prpplague/witch_dev/documentation/WITCH-schematics/jpgs/Primary Sequence - 47594.jpg

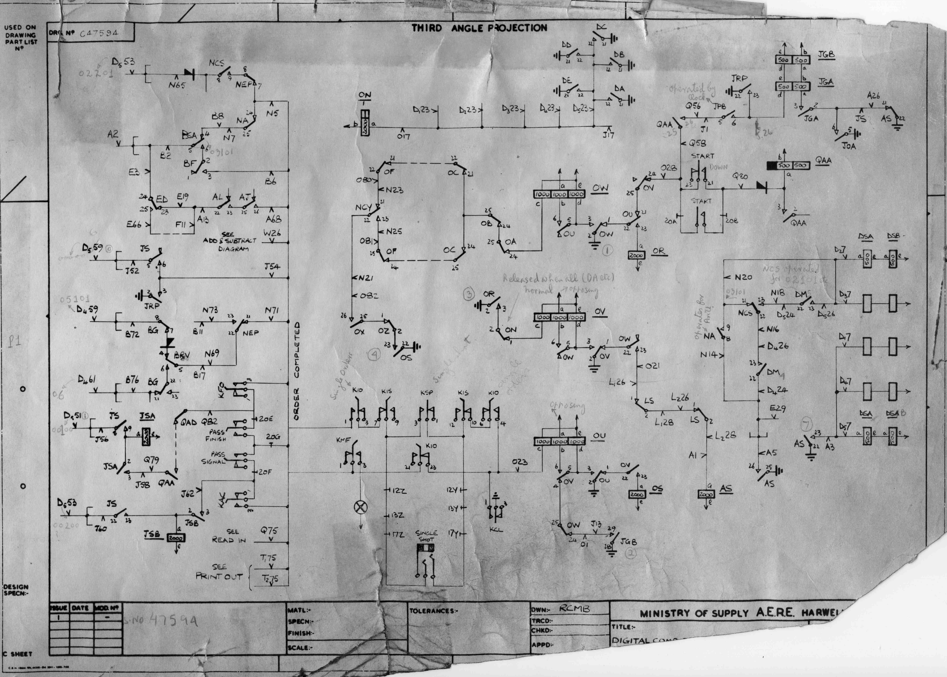
documentation/WITCH-schematics/jpgs/Primary Sequence - 47594.jpg
