prpplague/witch_dev/documentation/images/HarwellDekatronComputer-535x420.jpg

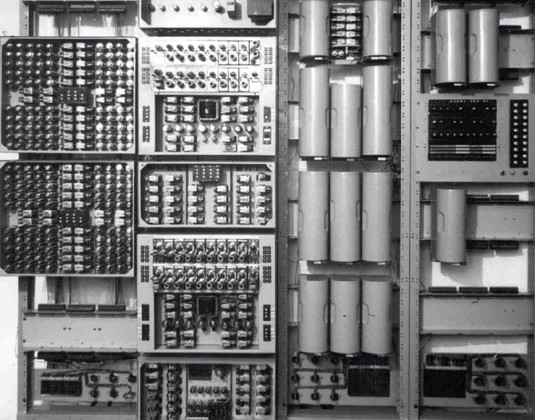
documentation/images/HarwellDekatronComputer-535x420.jpg
