prpplague/witch_dev/documentation/WITCH-schematics/notes/Multiplication Control Notes - 47584.pdf

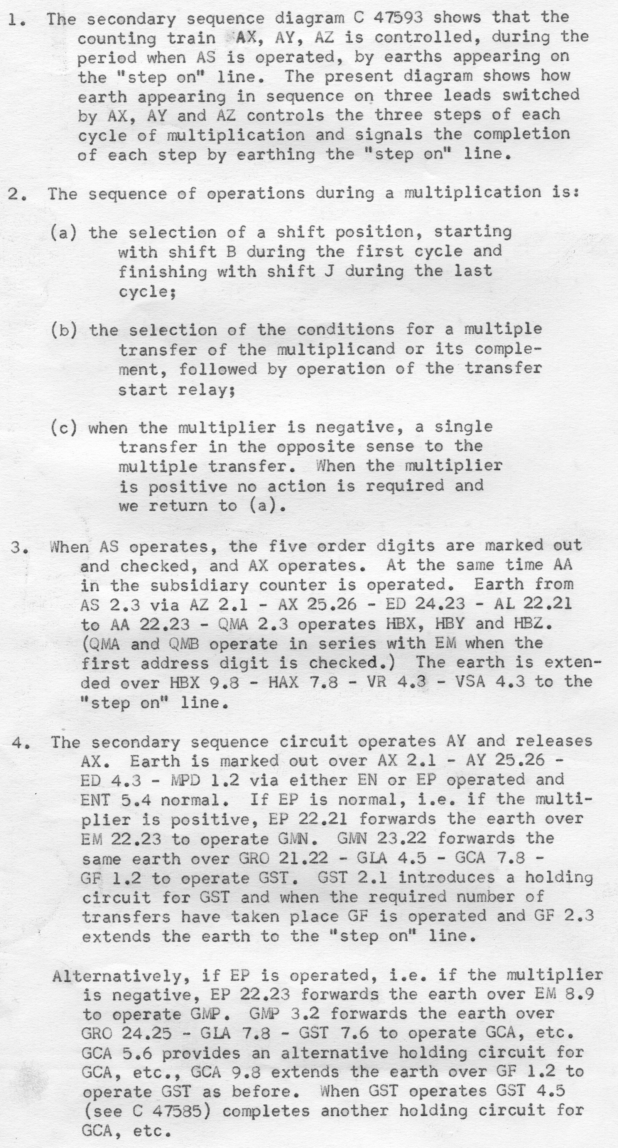
[picture p31: figure]

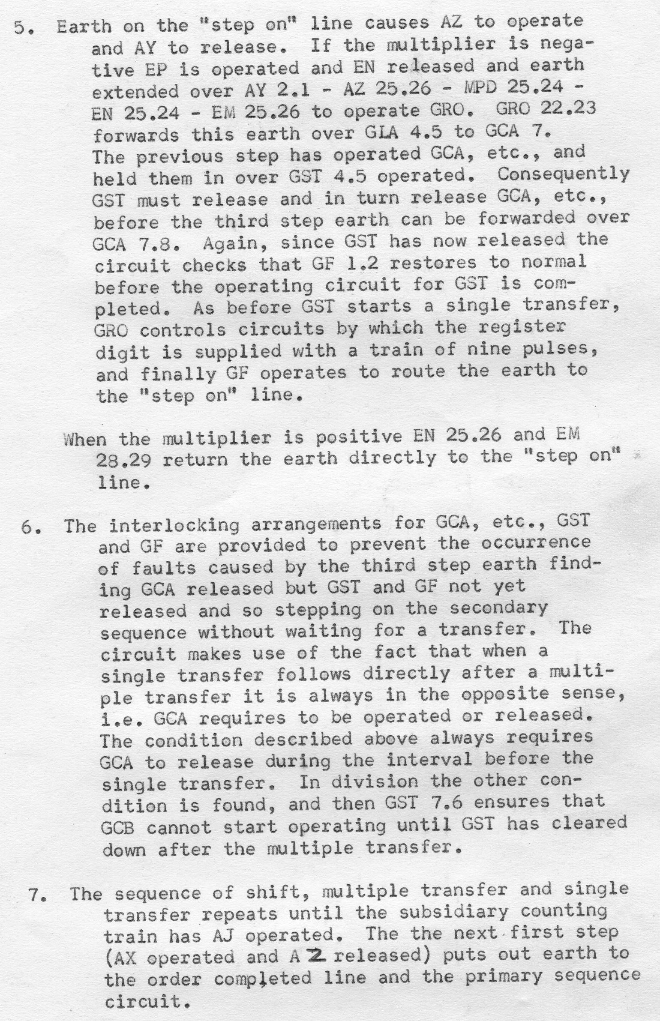
[picture p32: figure]
