prpplague/witch_dev/documentation/WITCH-schematics/notes/Read In Control Notes - 47582.pdf

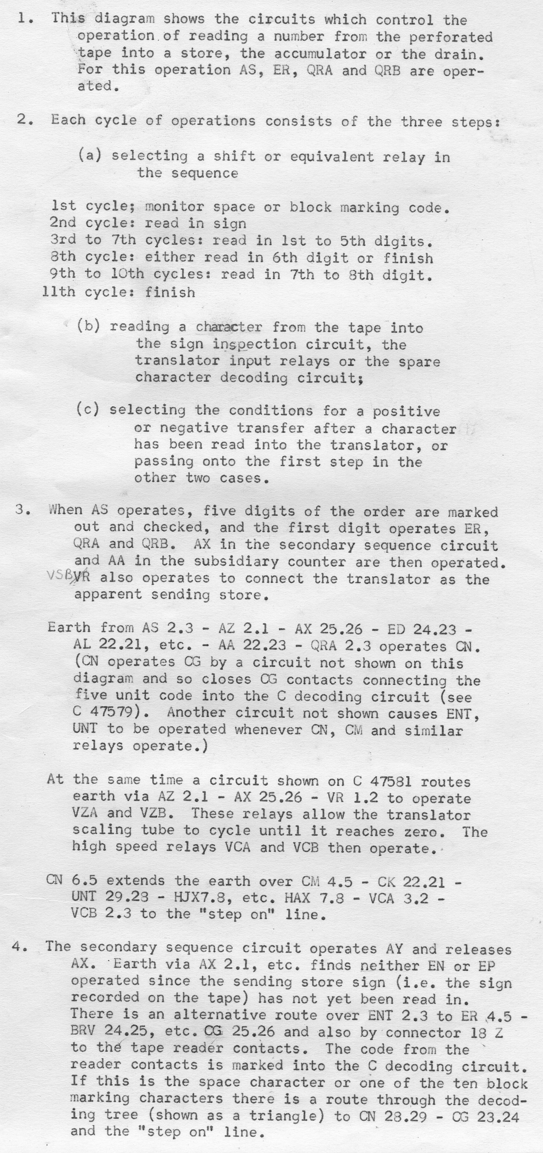
[picture p33: figure]

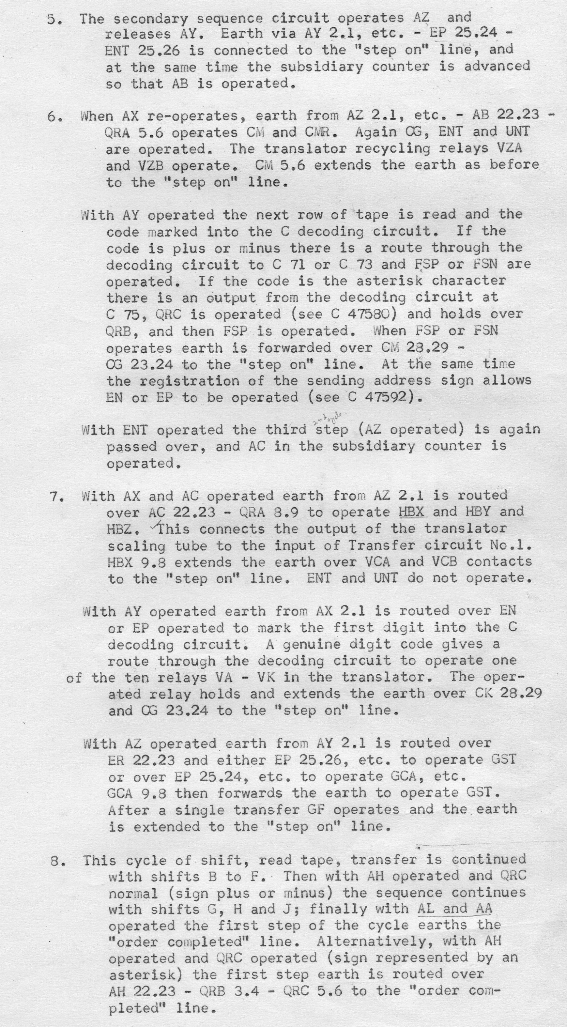
[picture p34: figure]
