prpplague/witch_dev/documentation/WITCH-schematics/notes/Secondary Sequence Notes - 47593.pdf

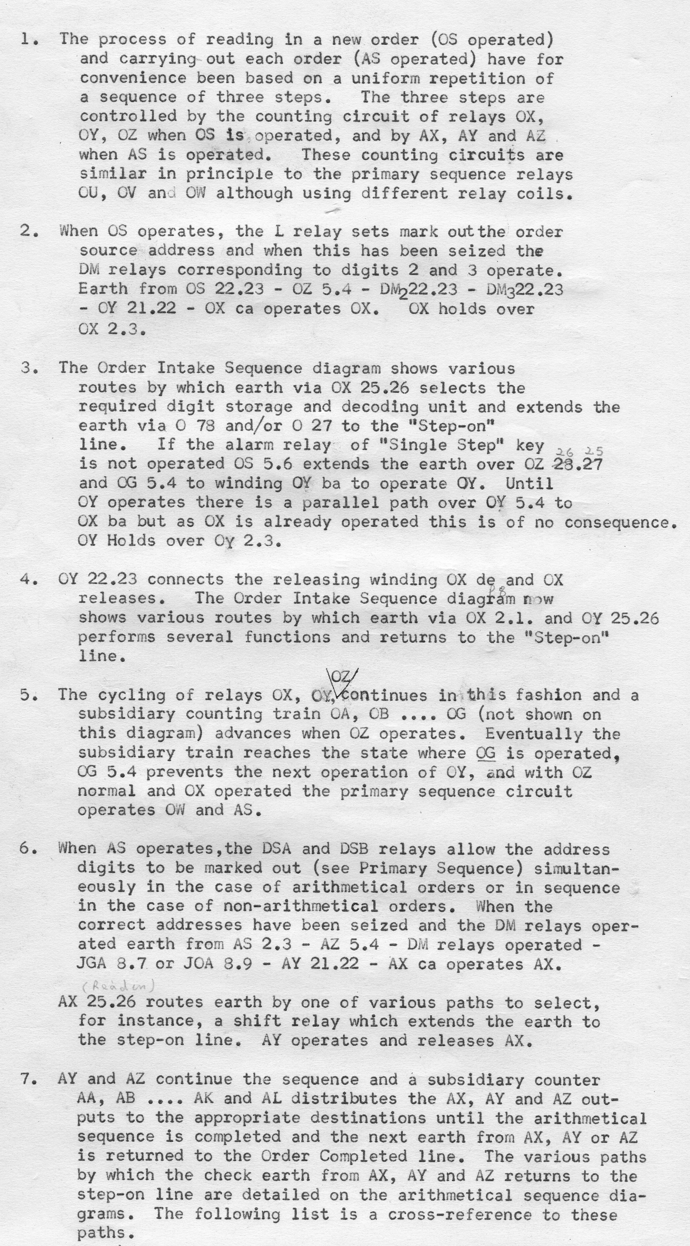
[picture p35: figure]

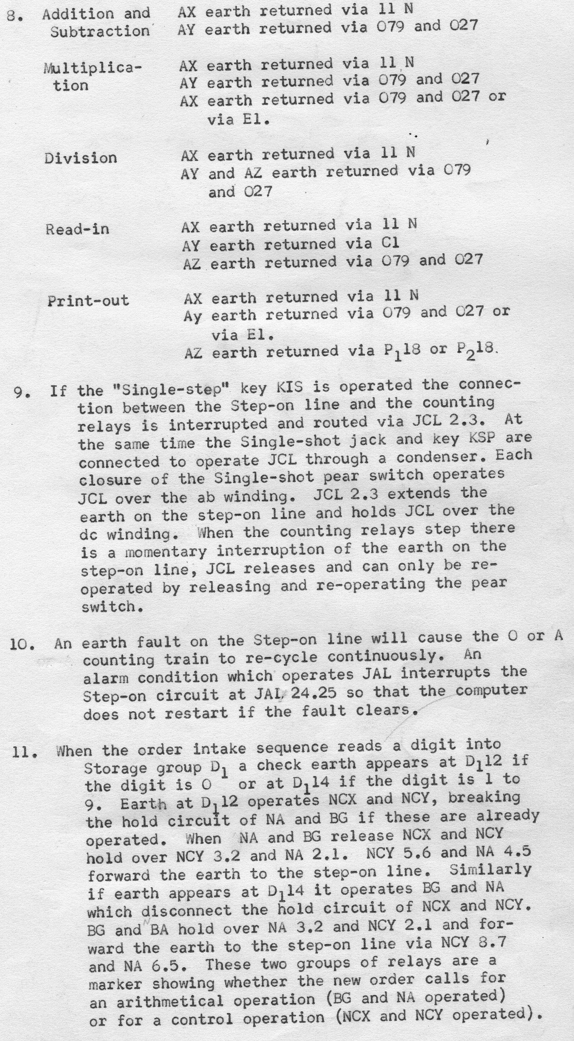
[picture p36: figure]

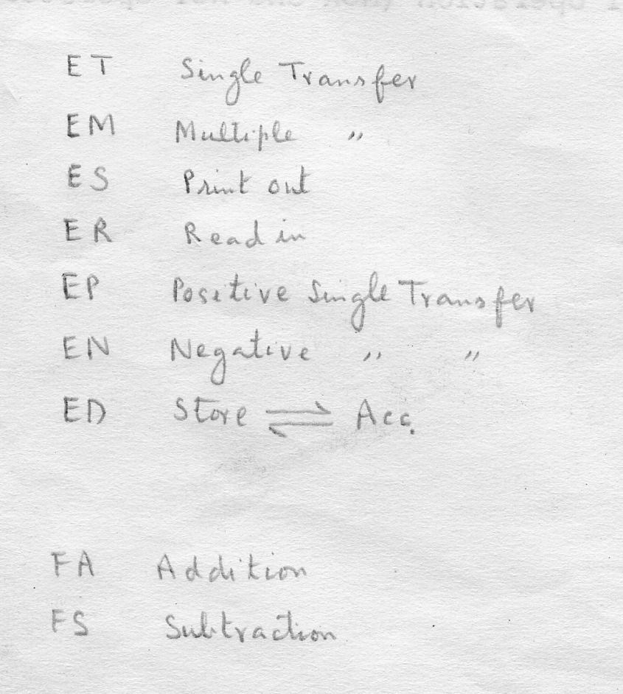
[picture p37: figure]
