prpplague/witch_dev/documentation/WITCH-schematics/notes/Sign Inspection Circuit Notes - 47580.pdf

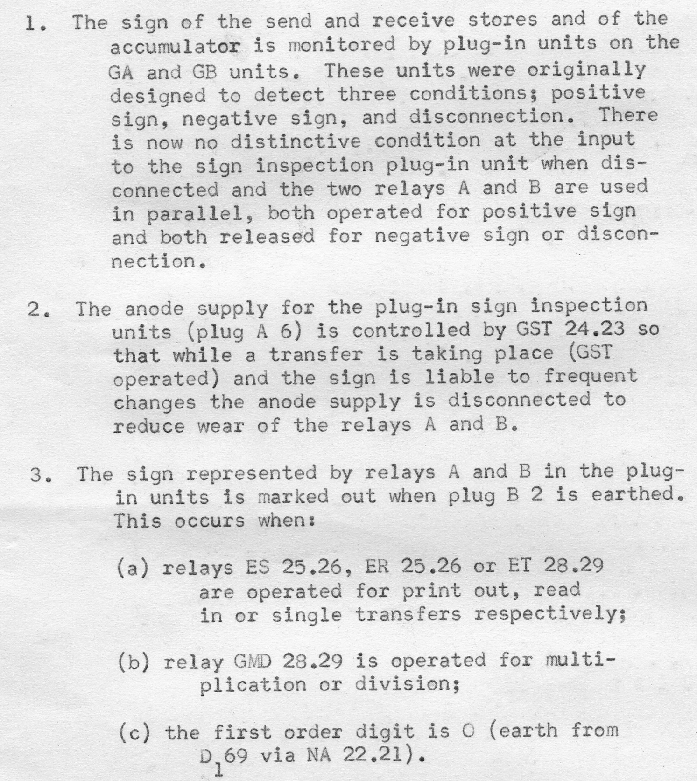
[picture p38: figure]

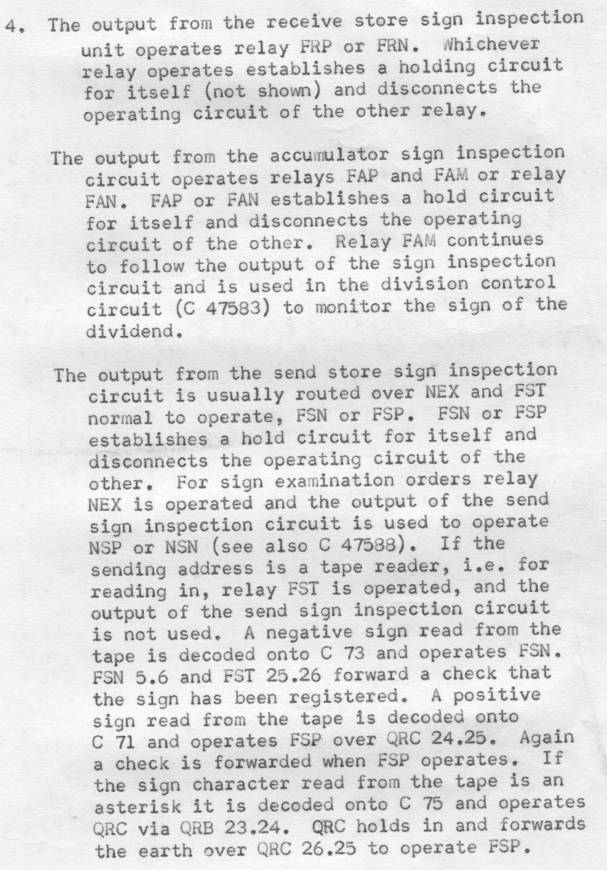
[picture p39: figure]
