prpplague/witch_dev/block-designs/witch-phase1/dekatron/witch-dekatron1.png

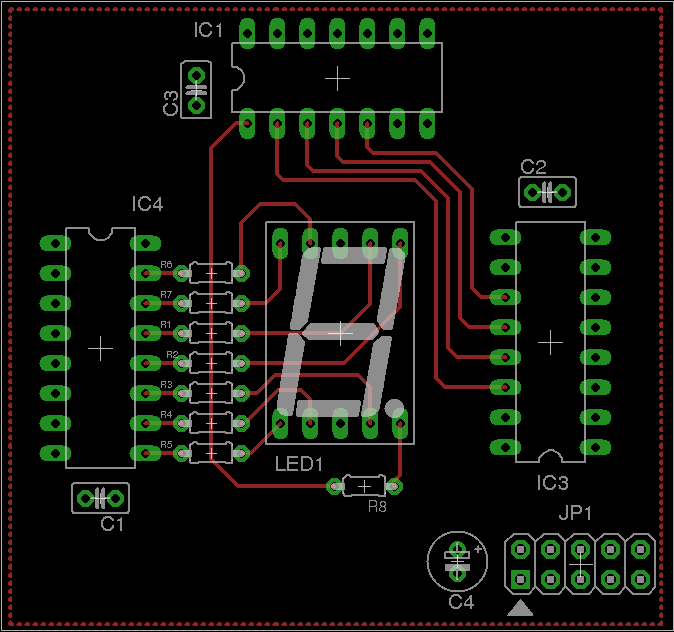
block-designs/witch-phase1/dekatron/witch-dekatron1.png
