prpplague/witch_dev/block-designs/witch-phase1/pulse/witch-pulse1.png

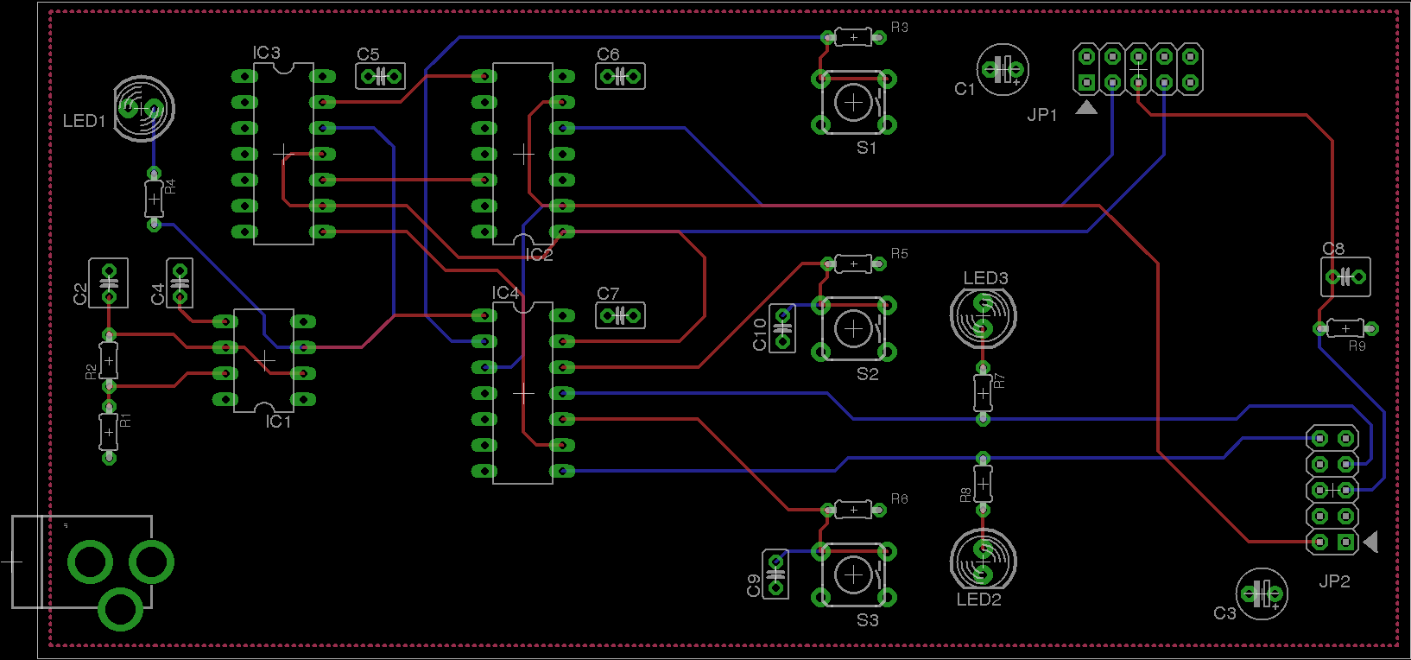
block-designs/witch-phase1/pulse/witch-pulse1.png
