prpplague/witch_dev/block-designs/witch-phase1/transfer/witch-transfer1.png

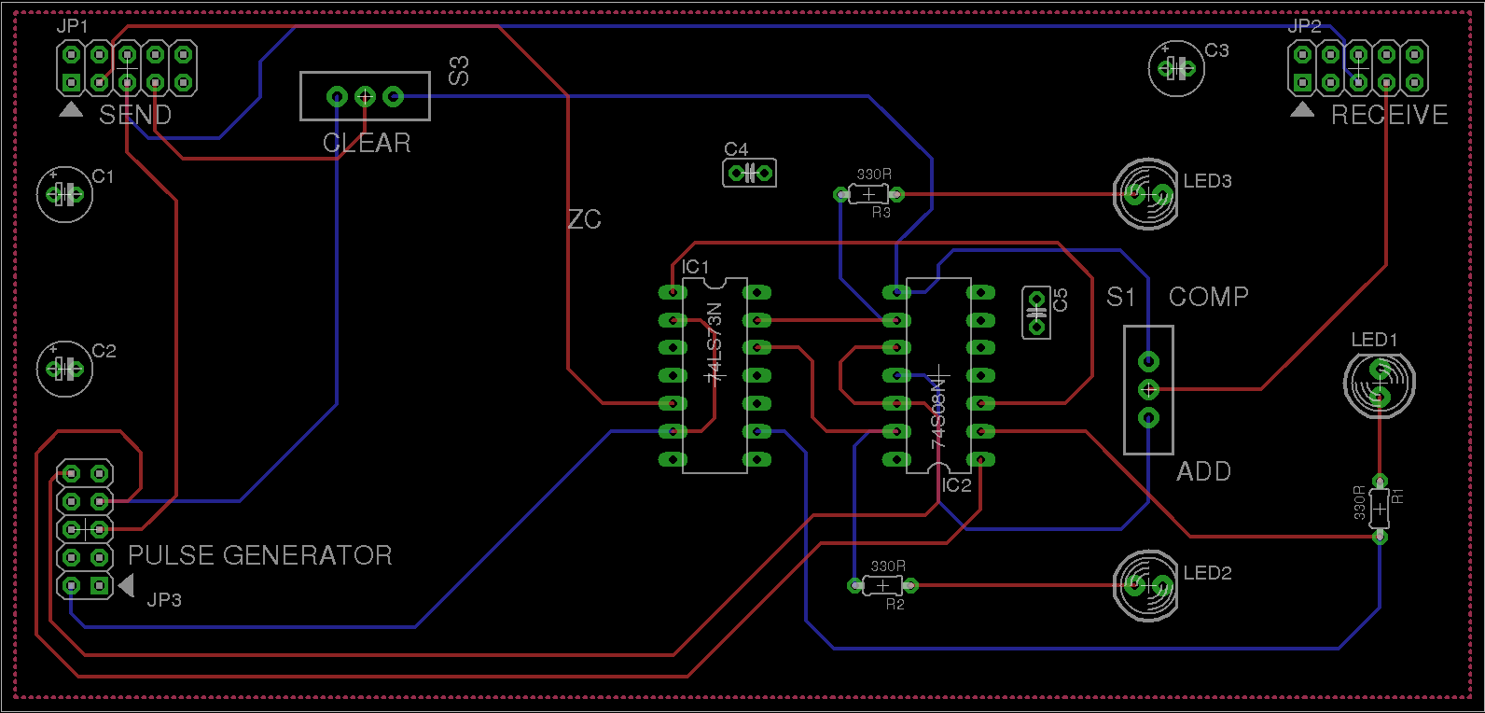
block-designs/witch-phase1/transfer/witch-transfer1.png
