prpplague/witch_dev/block-designs/witch-phase2/carry-block/carry-block.png

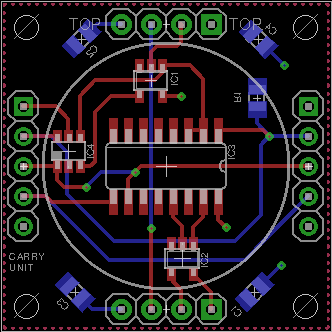
block-designs/witch-phase2/carry-block/carry-block.png
