prpplague/witch_dev/block-designs/witch-phase2/carry-select/carry-select.png

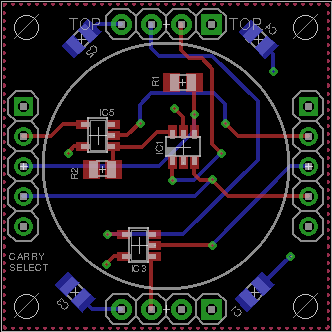
block-designs/witch-phase2/carry-select/carry-select.png
