prpplague/witch_dev/block-designs/witch-phase2/dekatron-sim/dekatron-sim-4017-A3/dekatron-sim-4017-a3.png

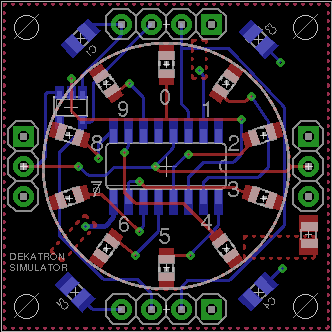
block-designs/witch-phase2/dekatron-sim/dekatron-sim-4017-A3/dekatron-sim-4017-a3.png
