prpplague/witch_dev/block-designs/witch-phase2/store-column-block/store-column-block.png

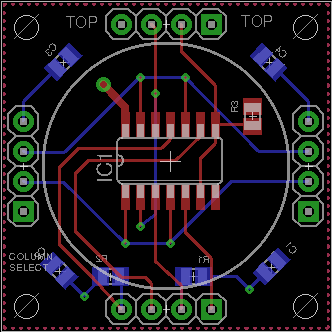
block-designs/witch-phase2/store-column-block/store-column-block.png
