prpplague/witch_dev/block-designs/witch-phase2/store-ctrl-block/store-ctrl-block.png

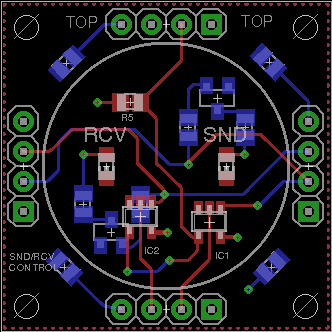
block-designs/witch-phase2/store-ctrl-block/store-ctrl-block.png
