prpplague/witch_dev/block-designs/witch-phase2/transfer-block/transfer-block.png

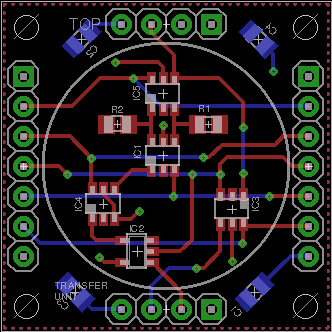
block-designs/witch-phase2/transfer-block/transfer-block.png
