prpplague/witch_dev/block-designs/witch-phase3/relay-set-d-decode/relay-set-d-decode.png

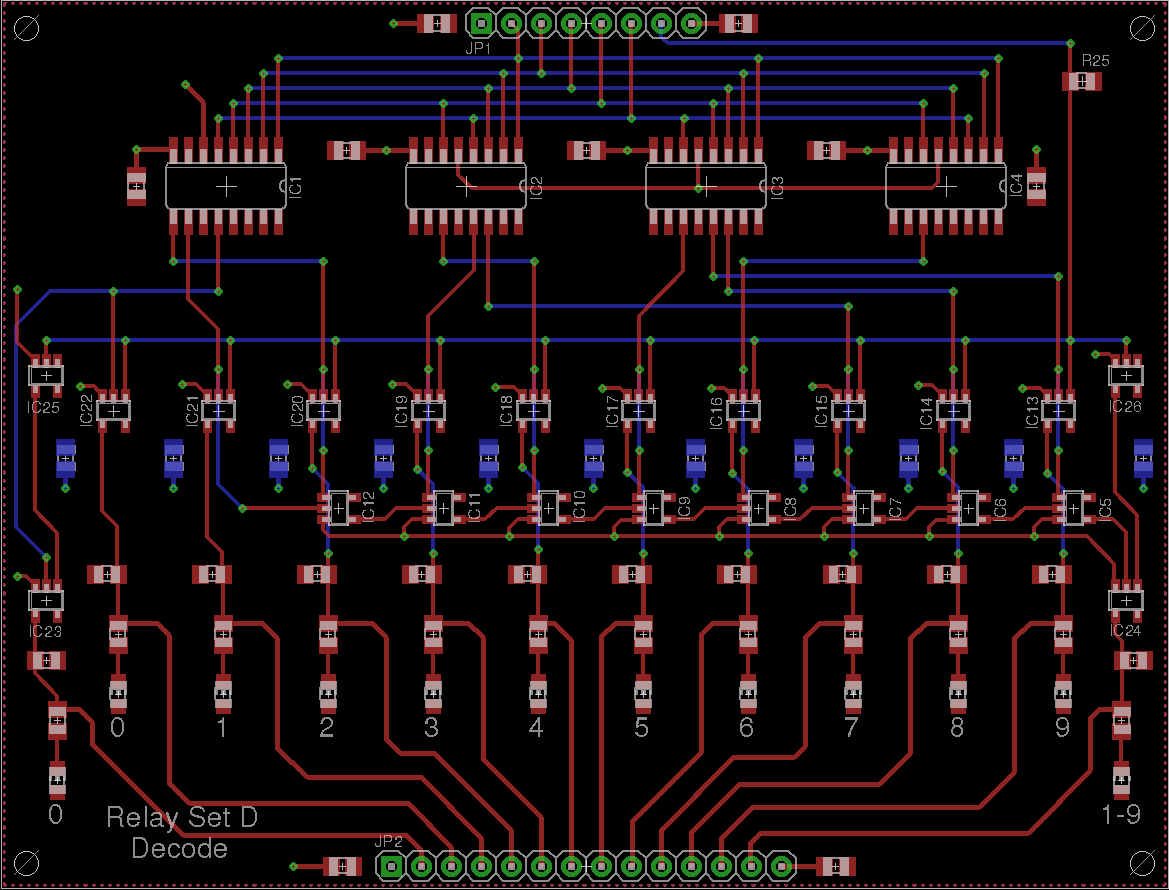
block-designs/witch-phase3/relay-set-d-decode/relay-set-d-decode.png
