prpplague/witch_dev/block-designs/witch-phase3/relay-set-d-latch/relay-set-d-latch.png

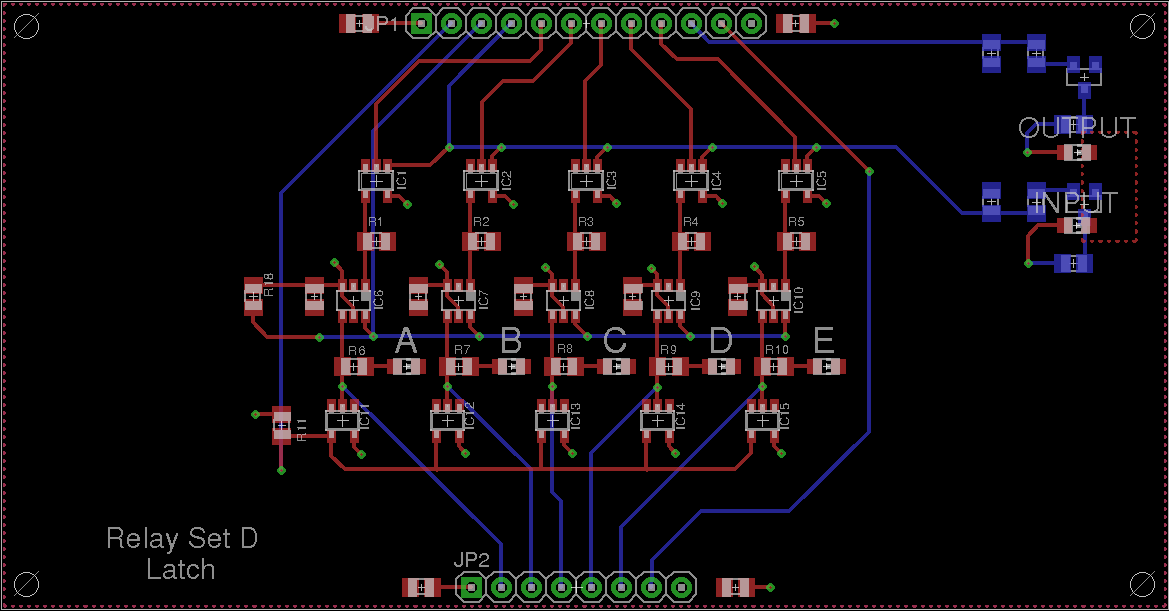
block-designs/witch-phase3/relay-set-d-latch/relay-set-d-latch.png
