prpplague/witch_dev/block-designs/witch-phase4/tape-reader/dot-reader/dot-sensors.png

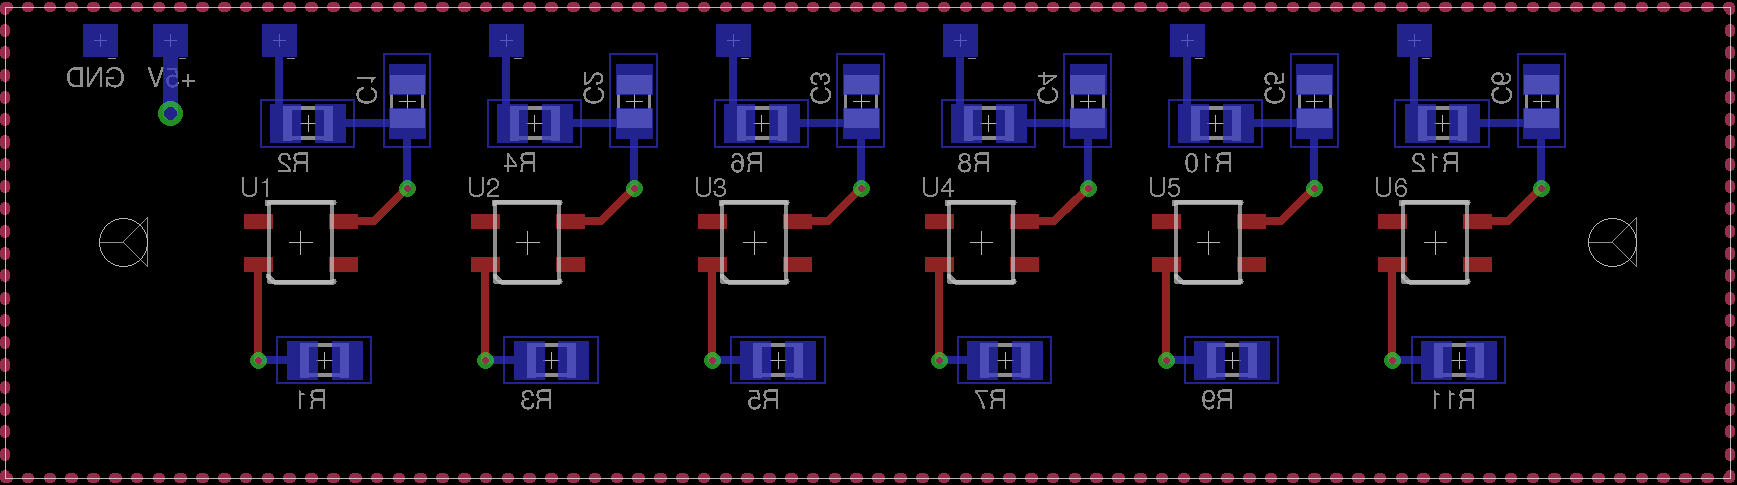
block-designs/witch-phase4/tape-reader/dot-reader/dot-sensors.png
