prpplague/witch_dev/documentation/datasheets/6AL5.jpg

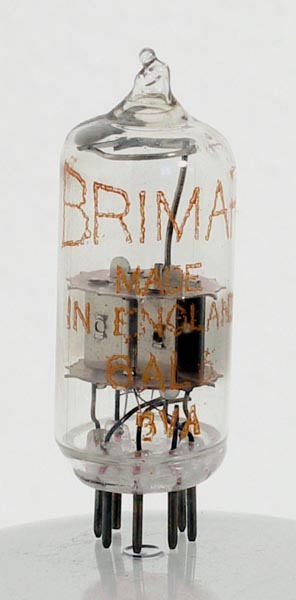
documentation/datasheets/6AL5.jpg
