prpplague/witch_dev/documentation/datasheets/6AM5.jpg

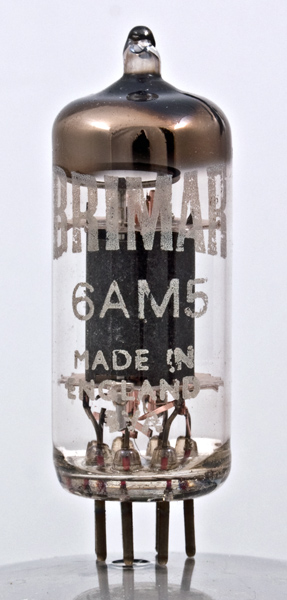
documentation/datasheets/6AM5.jpg
