prpplague/witch_dev/documentation/datasheets/6J6.jpg

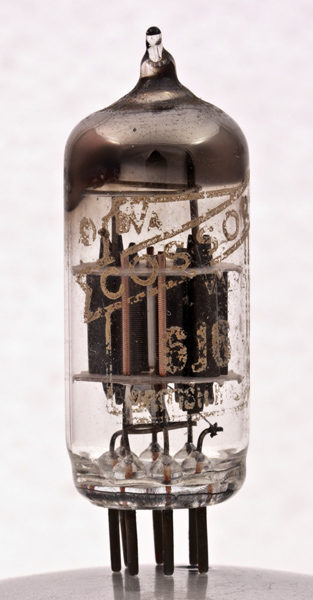
documentation/datasheets/6J6.jpg
