prpplague/witch_dev/documentation/datasheets/8D3.jpg

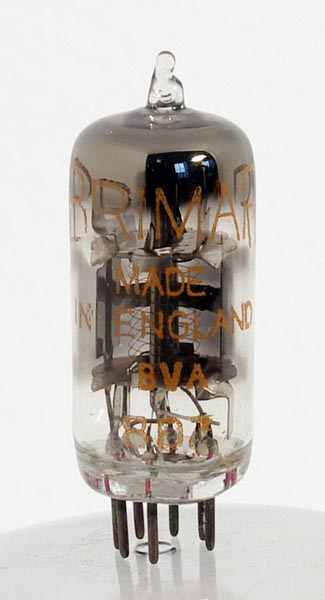
documentation/datasheets/8D3.jpg
