prpplague/witch_dev/documentation/datasheets/12AT7.jpg

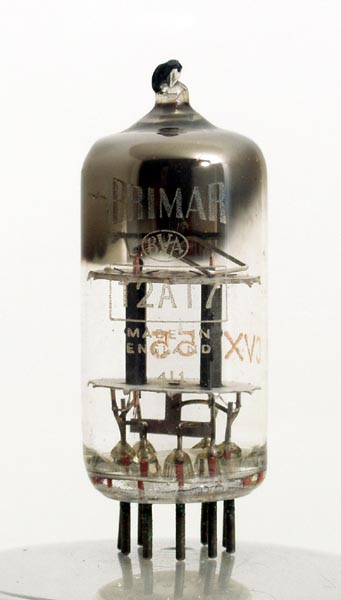
documentation/datasheets/12AT7.jpg
