prpplague/witch_dev/documentation/datasheets/85A2.jpg

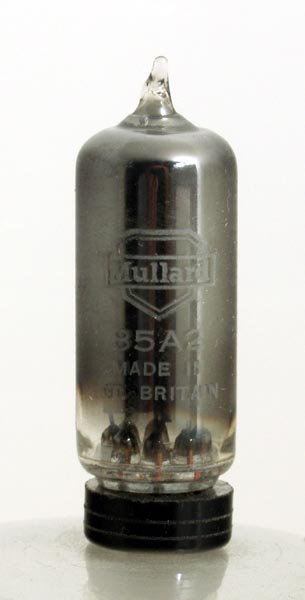
documentation/datasheets/85A2.jpg
