prpplague/witch_dev/documentation/datasheets/E90CC.jpg

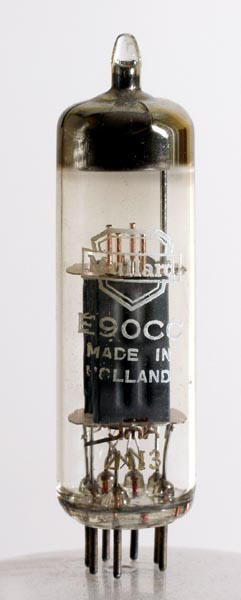
documentation/datasheets/E90CC.jpg
