prpplague/witch_dev/documentation/datasheets/E92CC.jpg

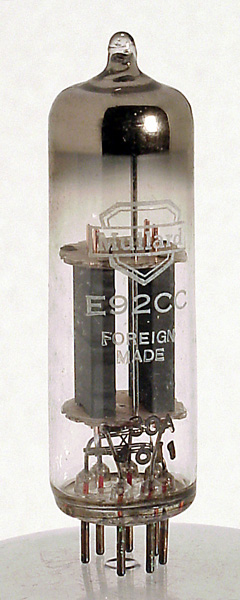
documentation/datasheets/E92CC.jpg
