prpplague/witch_dev/documentation/datasheets/EB91.jpg

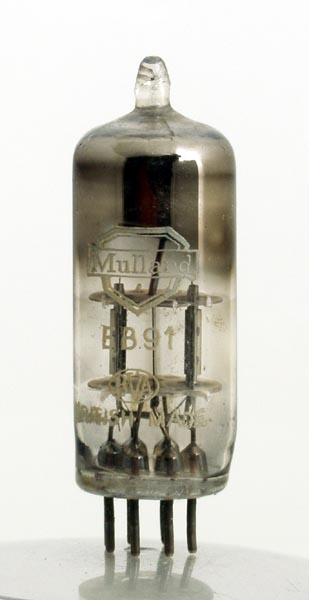
documentation/datasheets/EB91.jpg
