prpplague/witch_dev/documentation/datasheets/ECC81.jpg

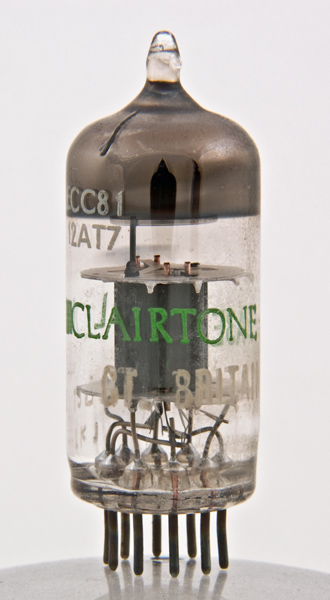
documentation/datasheets/ECC81.jpg
