prpplague/witch_dev/documentation/datasheets/EL33.jpg

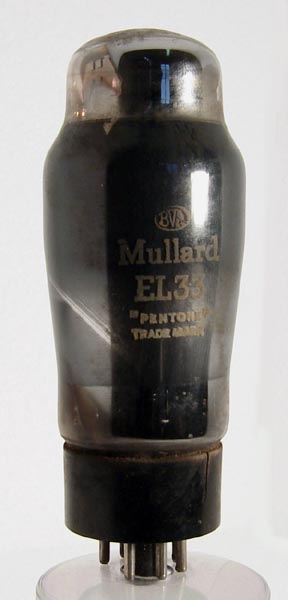
documentation/datasheets/EL33.jpg
