prpplague/witch_dev/documentation/datasheets/EL360.jpg

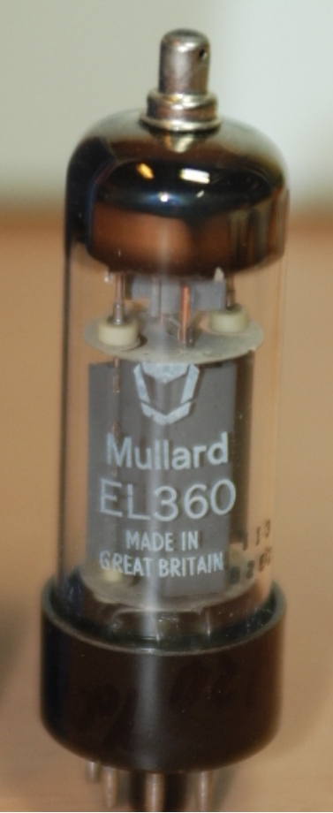
documentation/datasheets/EL360.jpg
