prpplague/witch_dev/documentation/datasheets/G1-371K.jpg

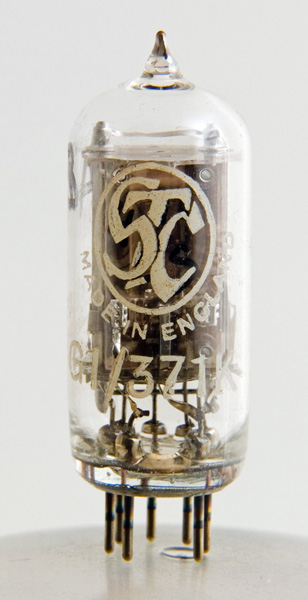
documentation/datasheets/G1-371K.jpg
