prpplague/witch_dev/documentation/datasheets/GC10A.jpg

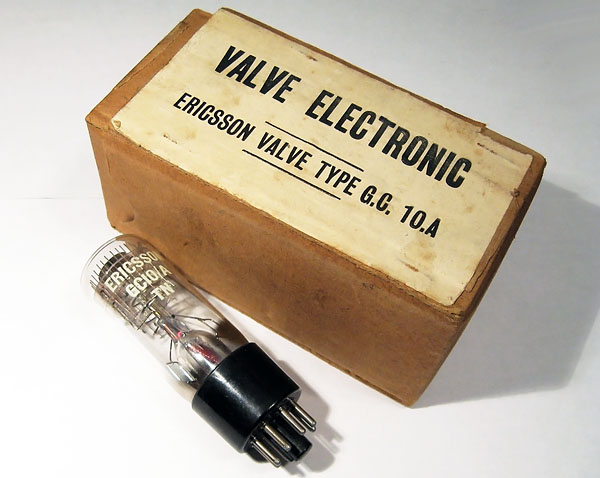
documentation/datasheets/GC10A.jpg
