prpplague/witch_dev/documentation/datasheets/GC10B.jpg

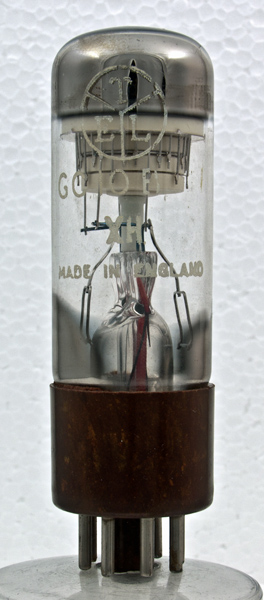
documentation/datasheets/GC10B.jpg
