prpplague/witch_dev/documentation/datasheets/GS10C.jpg

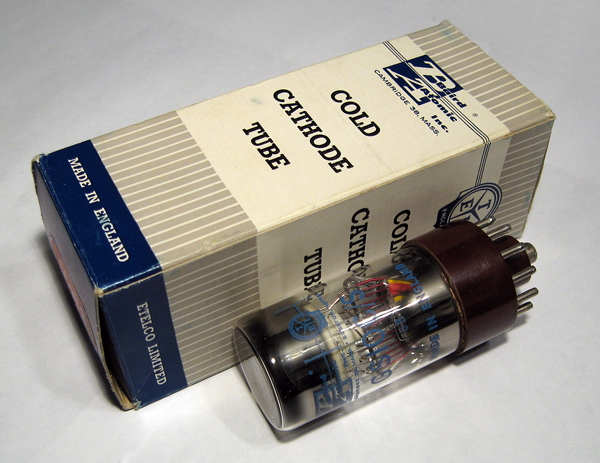
documentation/datasheets/GS10C.jpg
