prpplague/witch_dev/documentation/datasheets/GTE175M.jpg

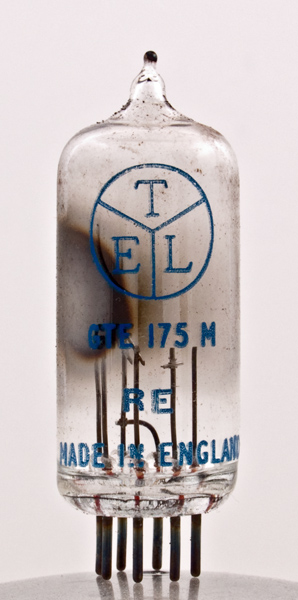
documentation/datasheets/GTE175M.jpg
