prpplague/witch_dev/documentation/datasheets/P-308-AB.jpg

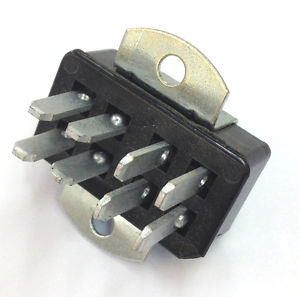
documentation/datasheets/P-308-AB.jpg
