prpplague/witch_dev/documentation/datasheets/S-308-AB.jpg

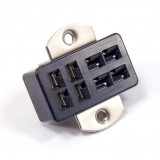
documentation/datasheets/S-308-AB.jpg
