prpplague/witch_dev/documentation/datasheets/VR150_30.jpg

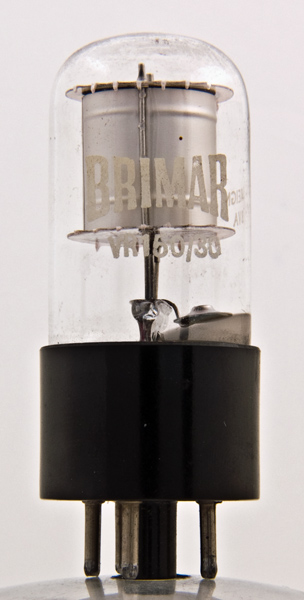
documentation/datasheets/VR150_30.jpg
