prpplague/witch_dev/documentation/dekatron-spinner/Variable Dekatron Spinner Kit | Threeneuron's Pile o'Poo_files/shock_03s.jpg

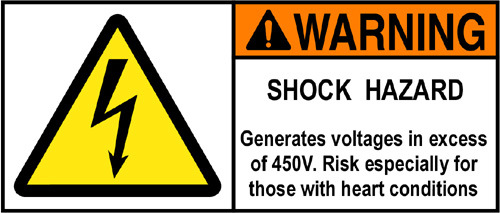
documentation/dekatron-spinner/Variable Dekatron Spinner Kit | Threeneuron's Pile o'Poo_files/shock_03s.jpg
