prpplague/witch_dev/documentation/dekatron-spinner/Variable Dekatron Spinner Kit | Threeneuron's Pile o'Poo_files/sp393_14.jpg

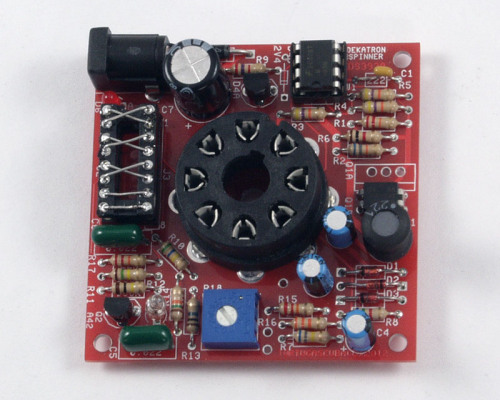
documentation/dekatron-spinner/Variable Dekatron Spinner Kit | Threeneuron's Pile o'Poo_files/sp393_14.jpg
