prpplague/witch_dev/documentation/images/caption-1.jpg

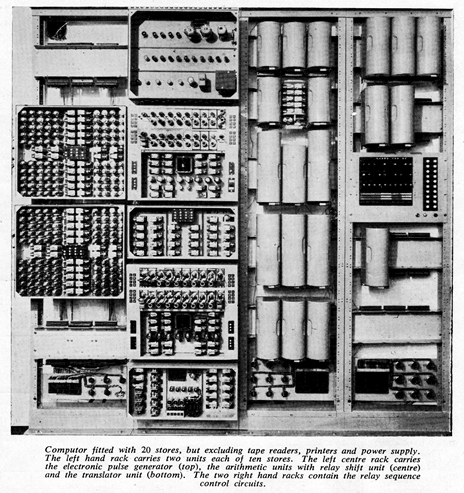
documentation/images/caption-1.jpg
