prpplague/witch_dev/documentation/images/EE-2.jpg

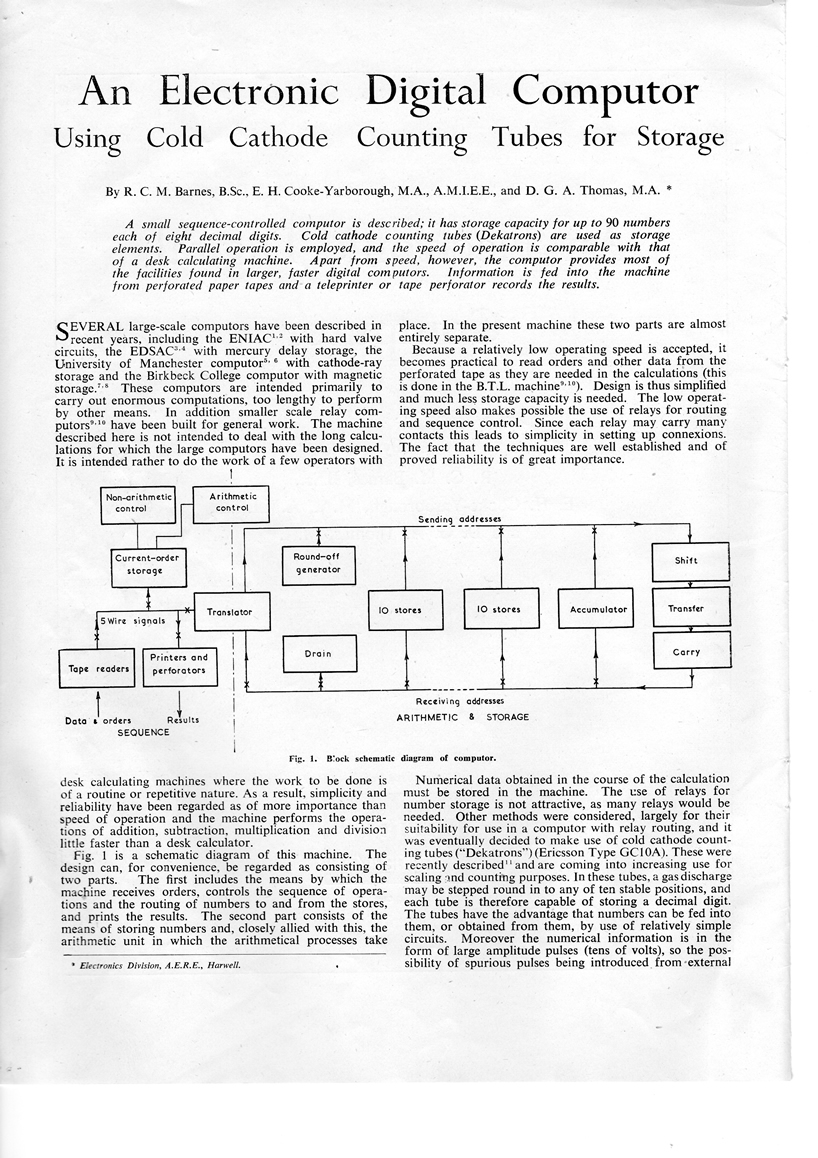
documentation/images/EE-2.jpg
