prpplague/witch_dev/documentation/images/EE-4.jpg

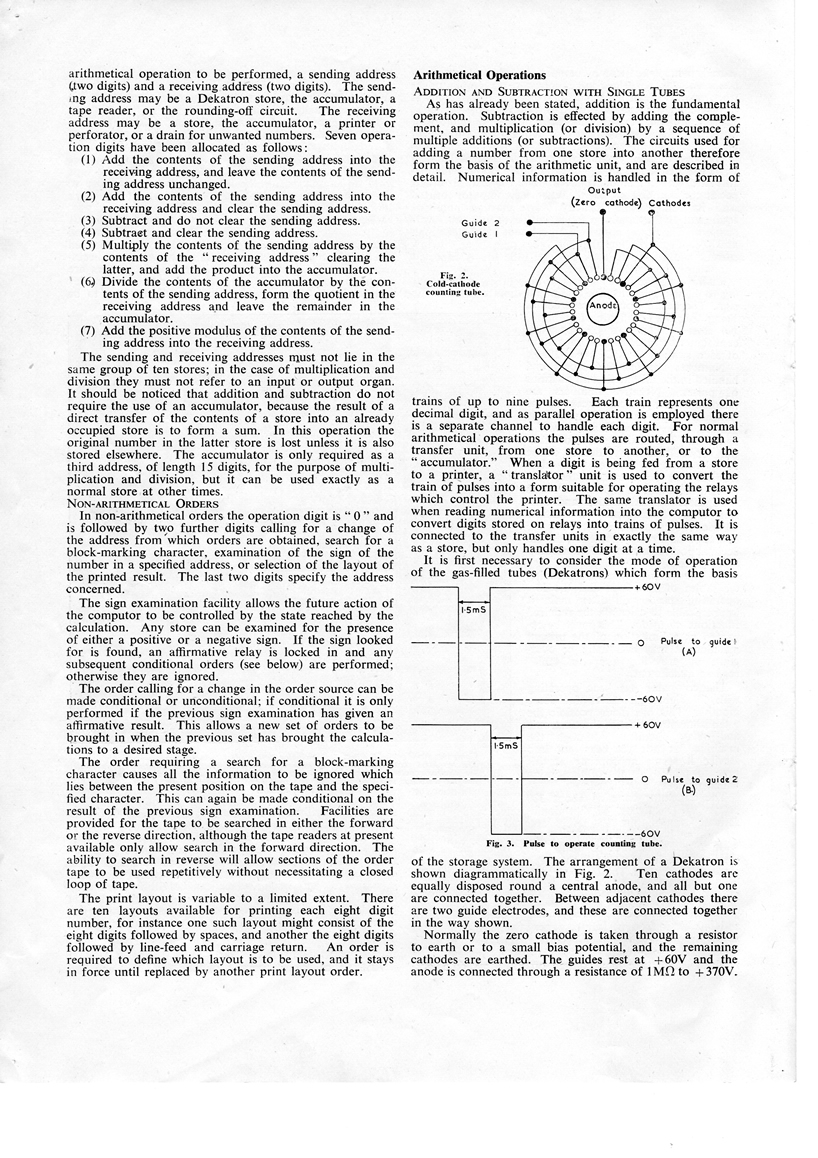
documentation/images/EE-4.jpg
