prpplague/witch_dev/documentation/images/EE-5.jpg

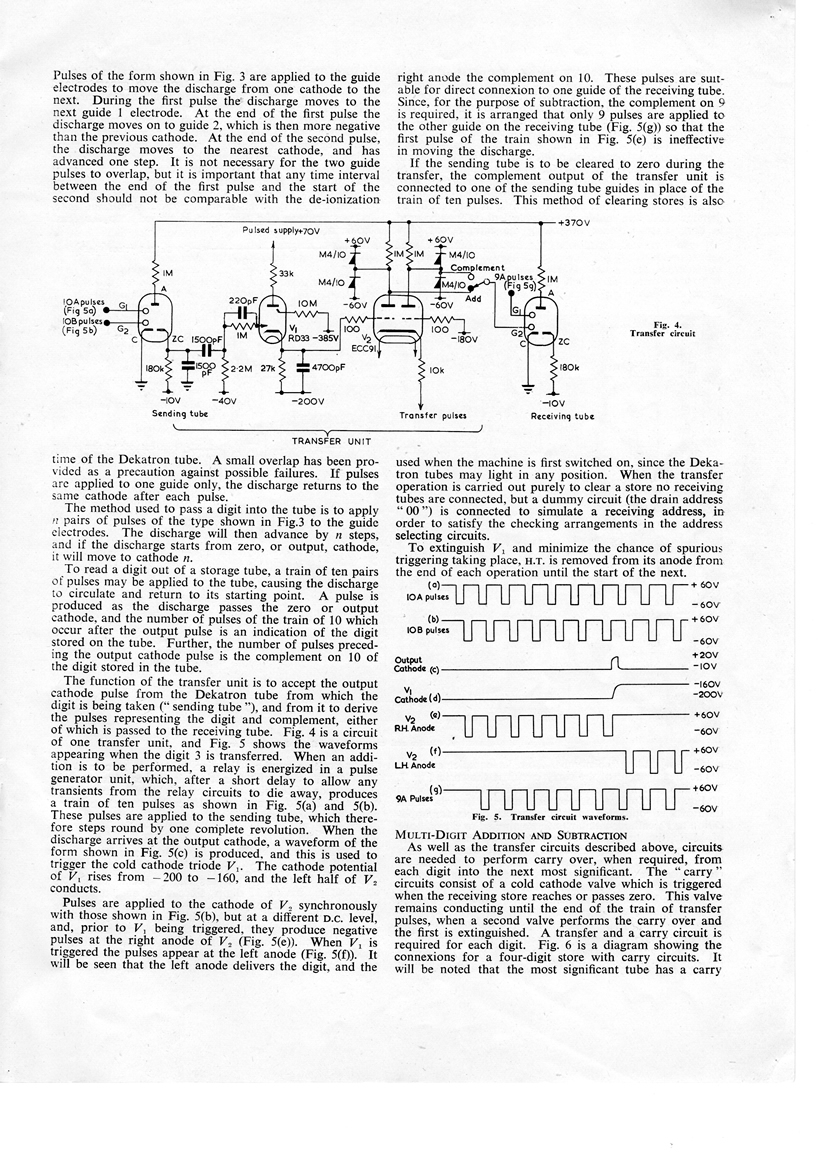
documentation/images/EE-5.jpg
