prpplague/witch_dev/documentation/images/EE-6.jpg

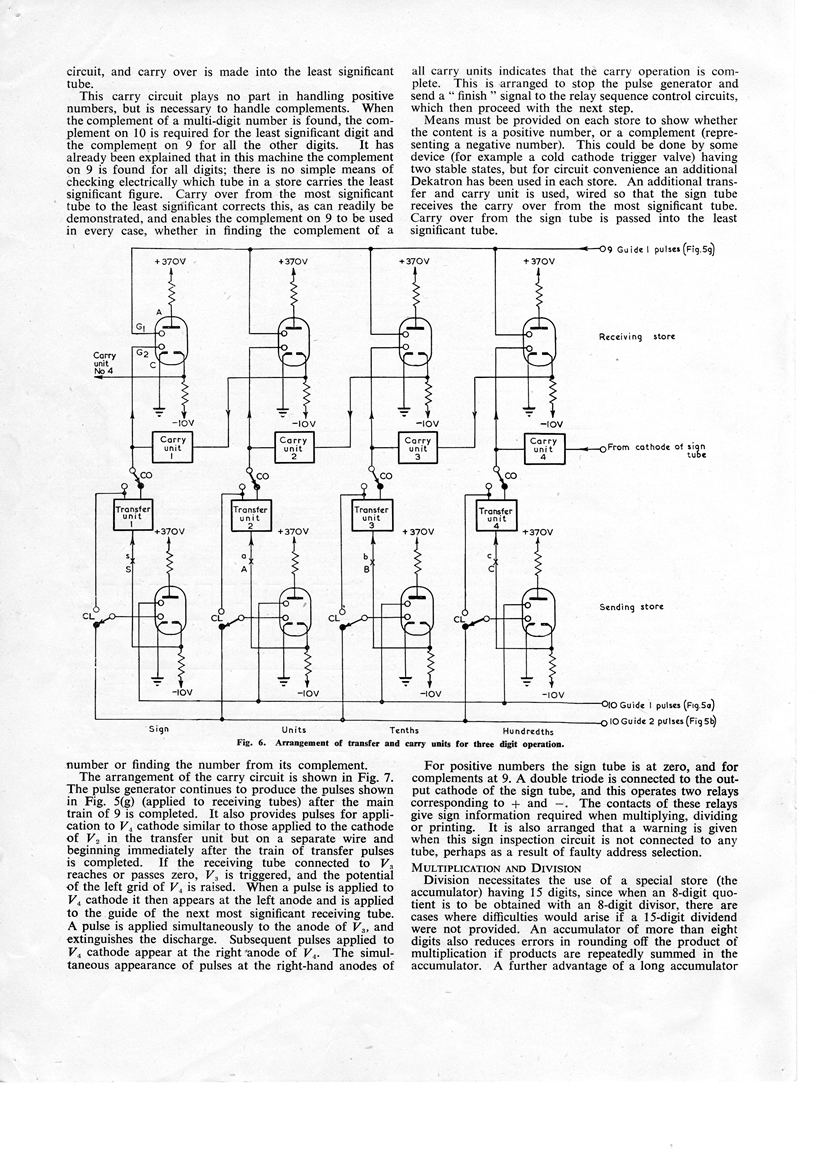
documentation/images/EE-6.jpg
