prpplague/witch_dev/documentation/images/EE-7.jpg

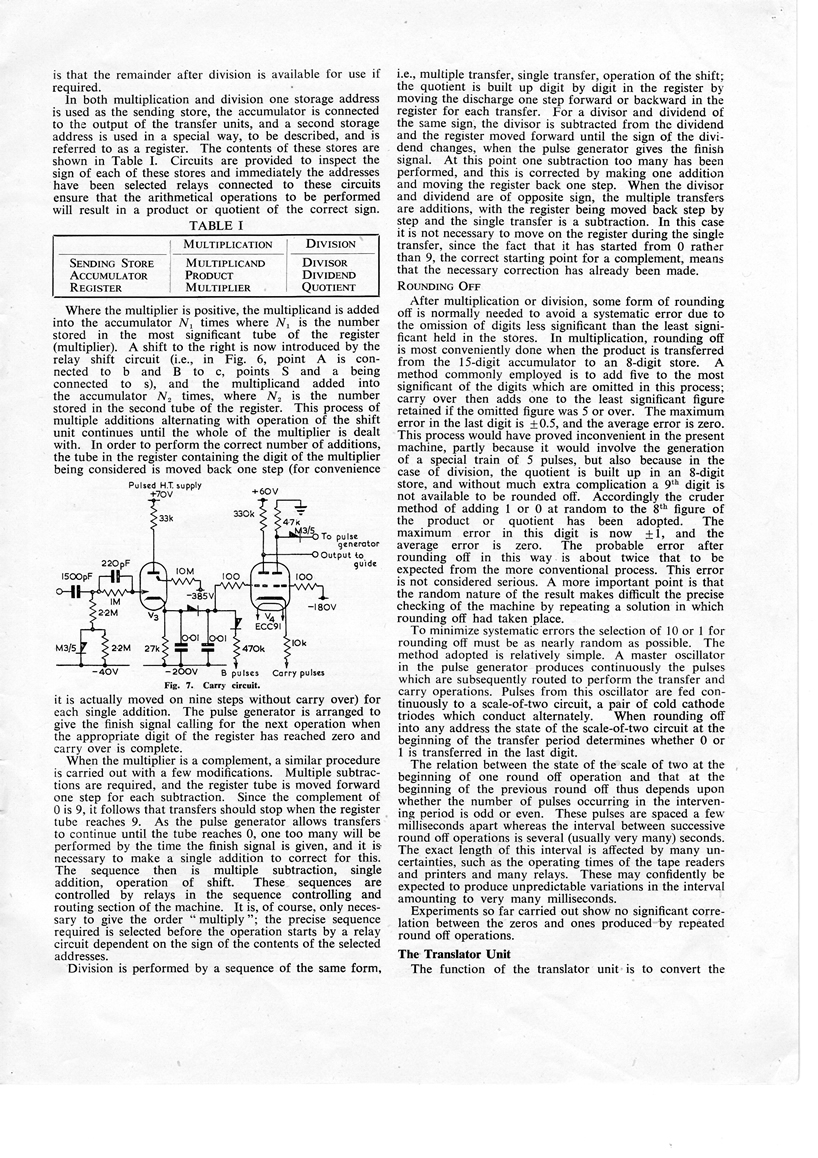
documentation/images/EE-7.jpg
