prpplague/witch_dev/documentation/images/EE-8.jpg

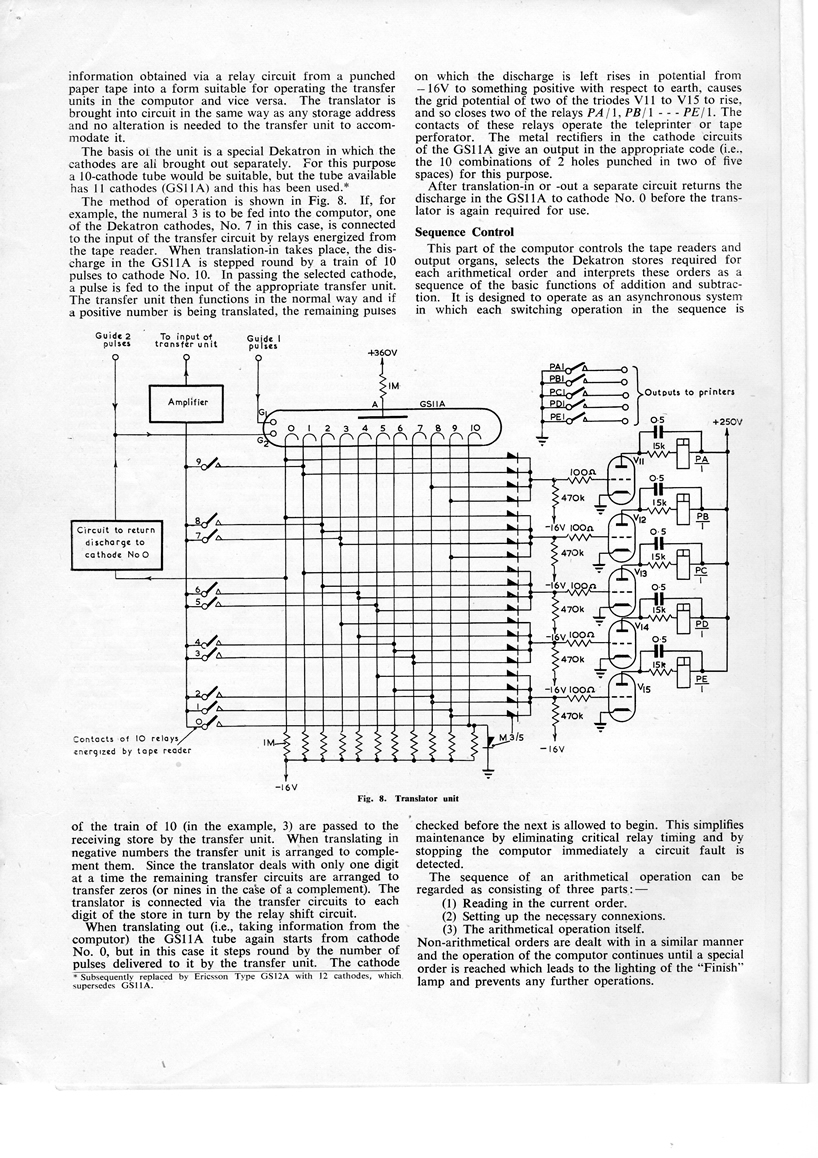
documentation/images/EE-8.jpg
