prpplague/witch_dev/documentation/images/fig2.png

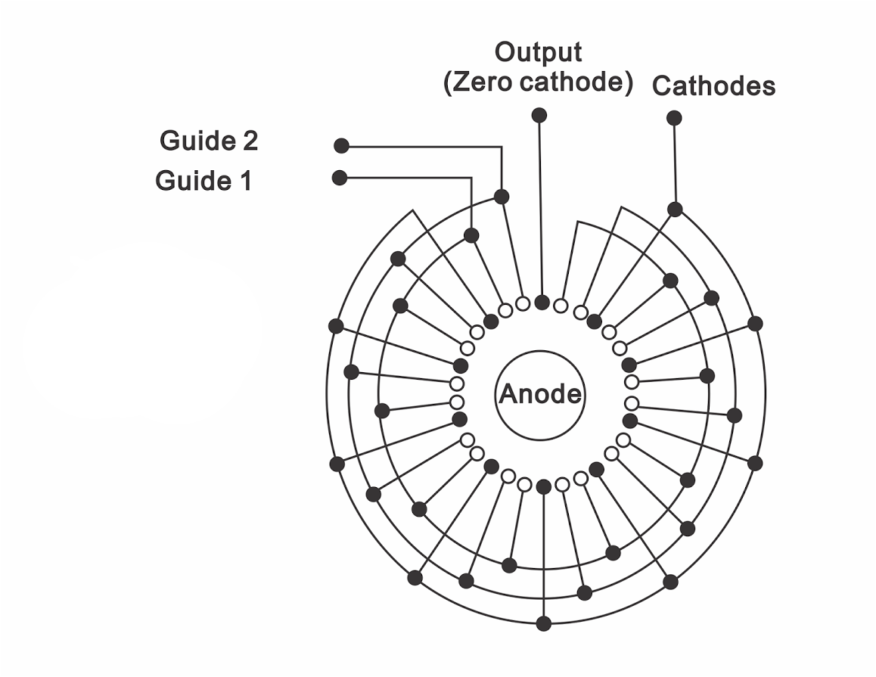
documentation/images/fig2.png
