prpplague/witch_dev/documentation/images/fig3.png

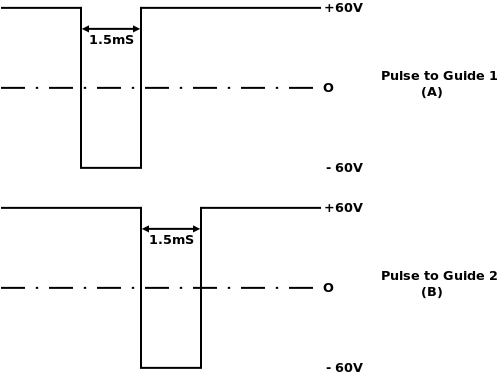
documentation/images/fig3.png
