prpplague/witch_dev/documentation/images/fig4.png

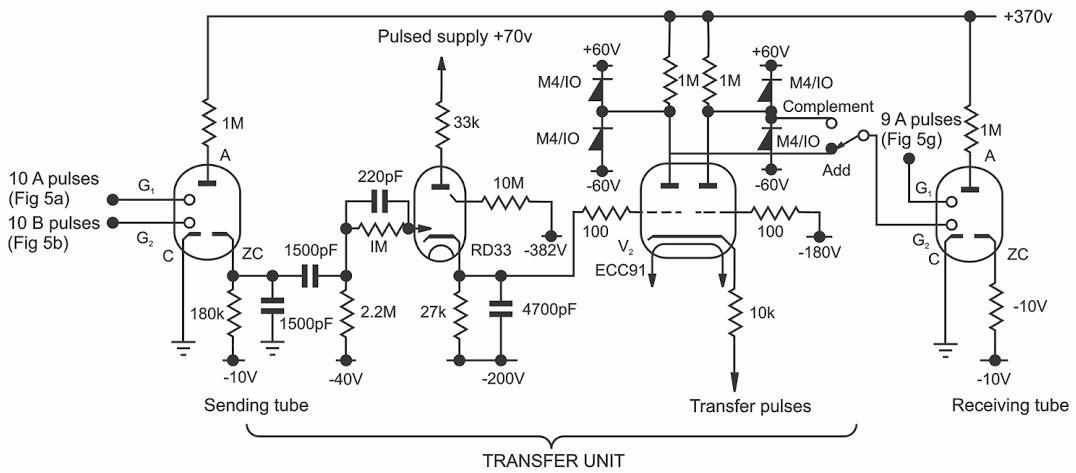
documentation/images/fig4.png
