prpplague/witch_dev/documentation/images/fig5.png

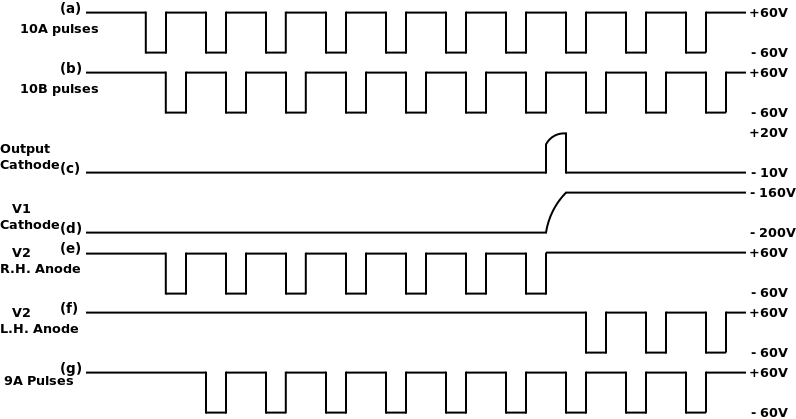
documentation/images/fig5.png
