prpplague/witch_dev/documentation/images/fig6.png

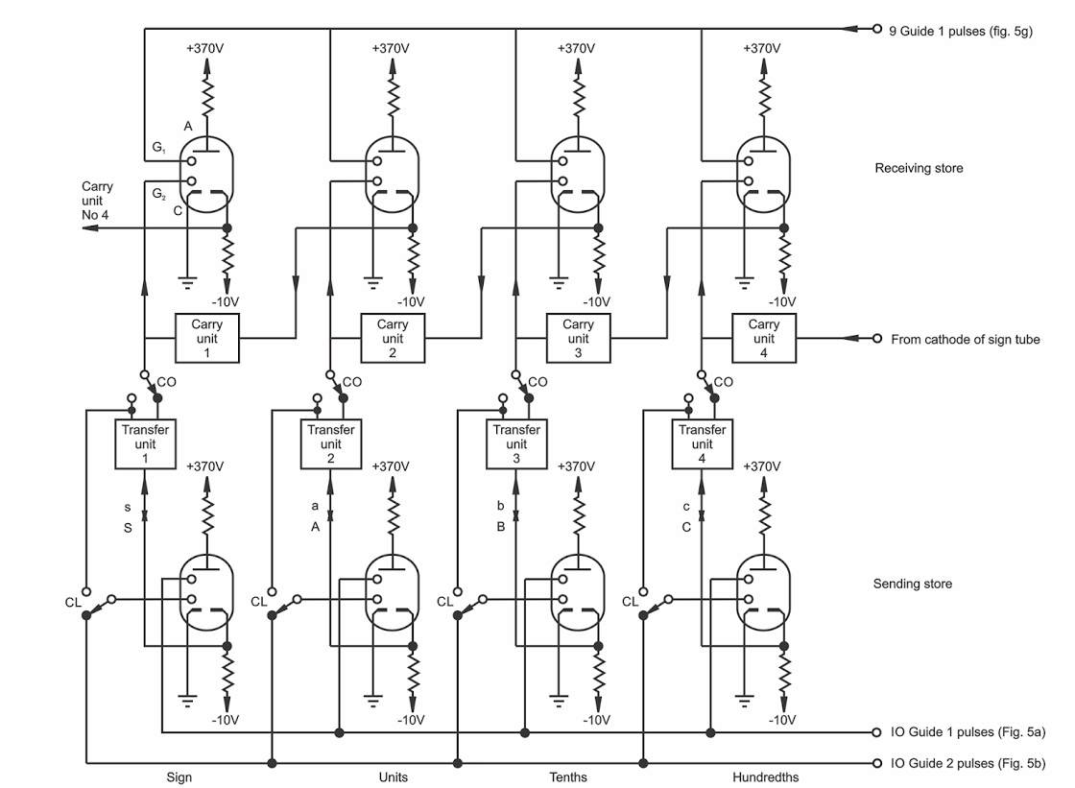
documentation/images/fig6.png
