prpplague/witch_dev/documentation/images/fig7.png

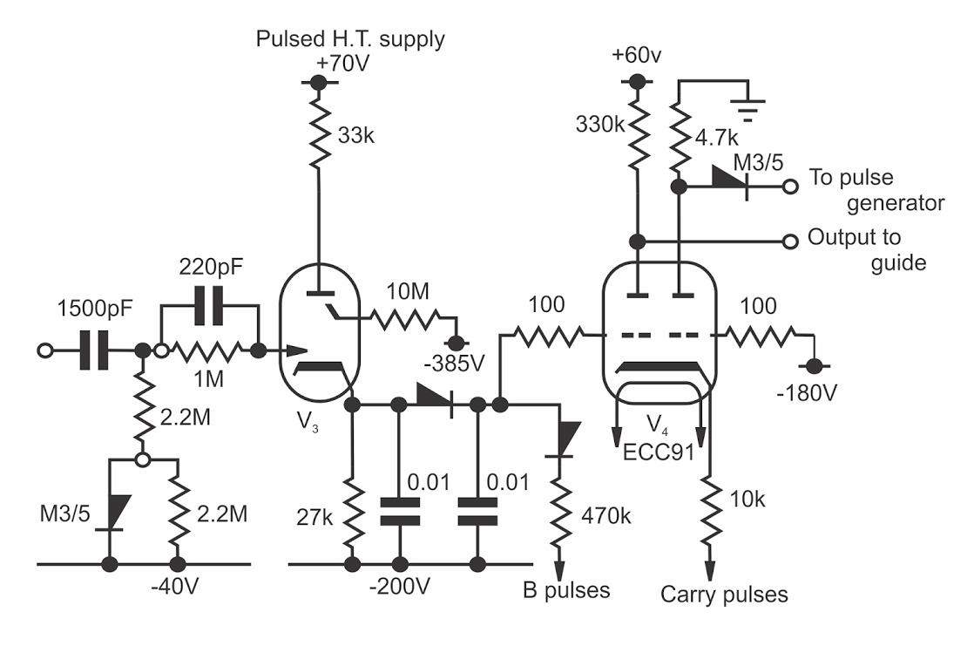
documentation/images/fig7.png
