prpplague/witch_dev/documentation/images/fig8.png

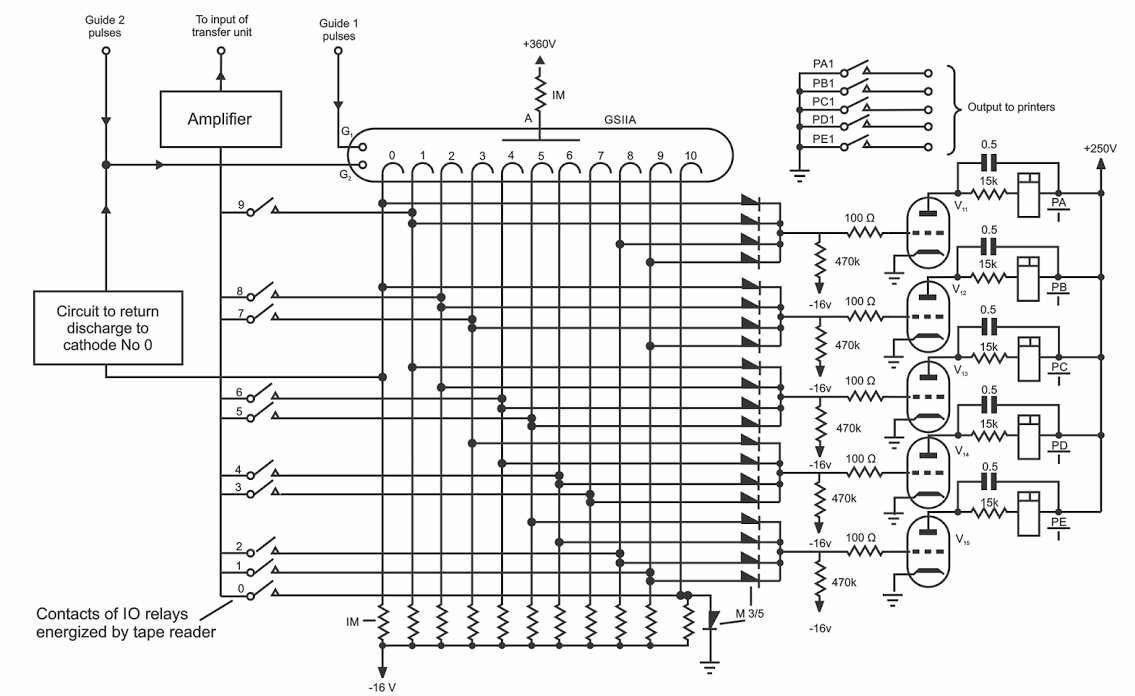
documentation/images/fig8.png
