prpplague/witch_dev/documentation/images/fig-1.jpg

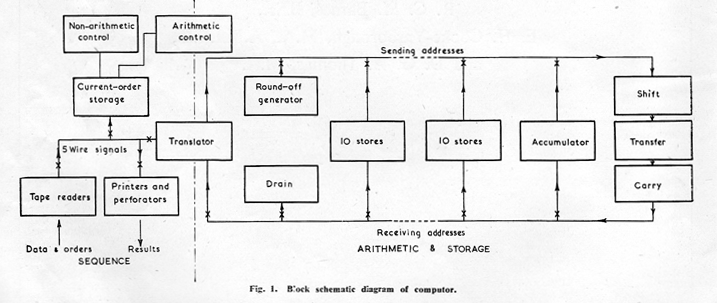
documentation/images/fig-1.jpg
