prpplague/witch_dev/documentation/images/fig-2.jpg

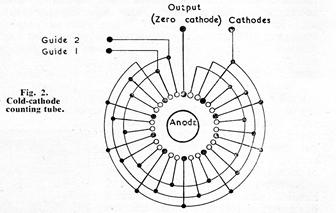
documentation/images/fig-2.jpg
