prpplague/witch_dev/documentation/images/fig-3.jpg

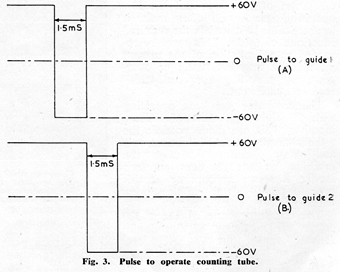
documentation/images/fig-3.jpg
