prpplague/witch_dev/documentation/images/fig-4.jpg

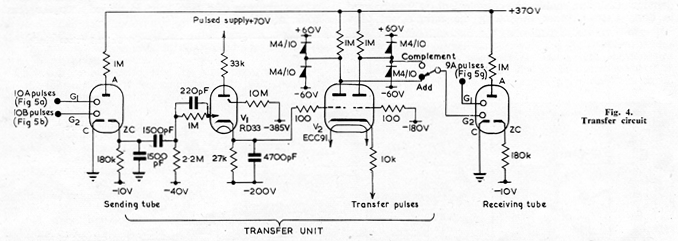
documentation/images/fig-4.jpg
