prpplague/witch_dev/documentation/images/fig-5.jpg

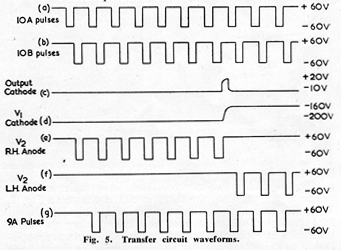
documentation/images/fig-5.jpg
