prpplague/witch_dev/documentation/images/fig-6.jpg

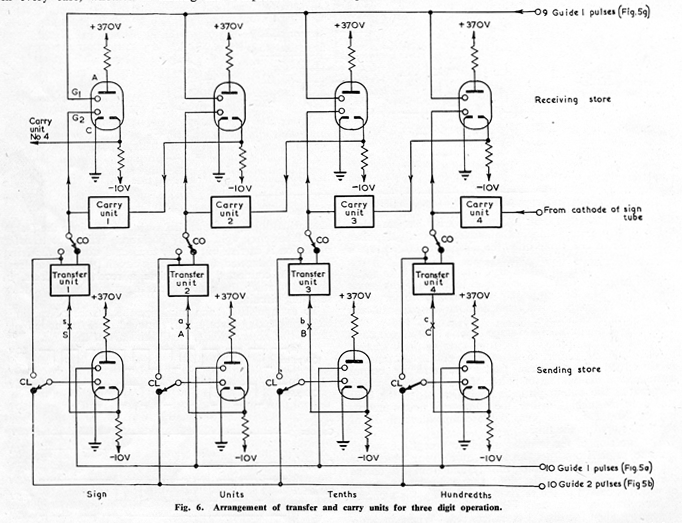
documentation/images/fig-6.jpg
