prpplague/witch_dev/documentation/images/fig-7.jpg

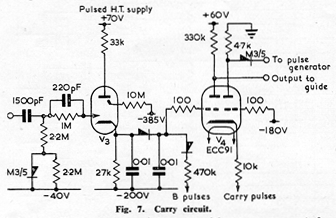
documentation/images/fig-7.jpg
