prpplague/witch_dev/documentation/images/fig-8.jpg

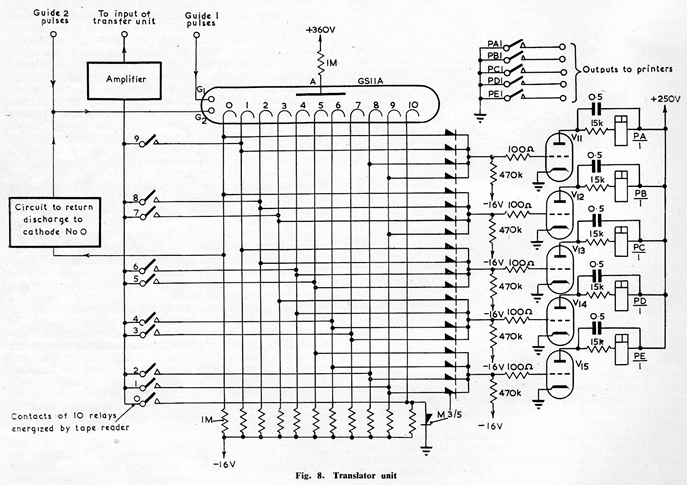
documentation/images/fig-8.jpg
