prpplague/witch_dev/documentation/images/harwell-ee-1951-txt-p1.jpg

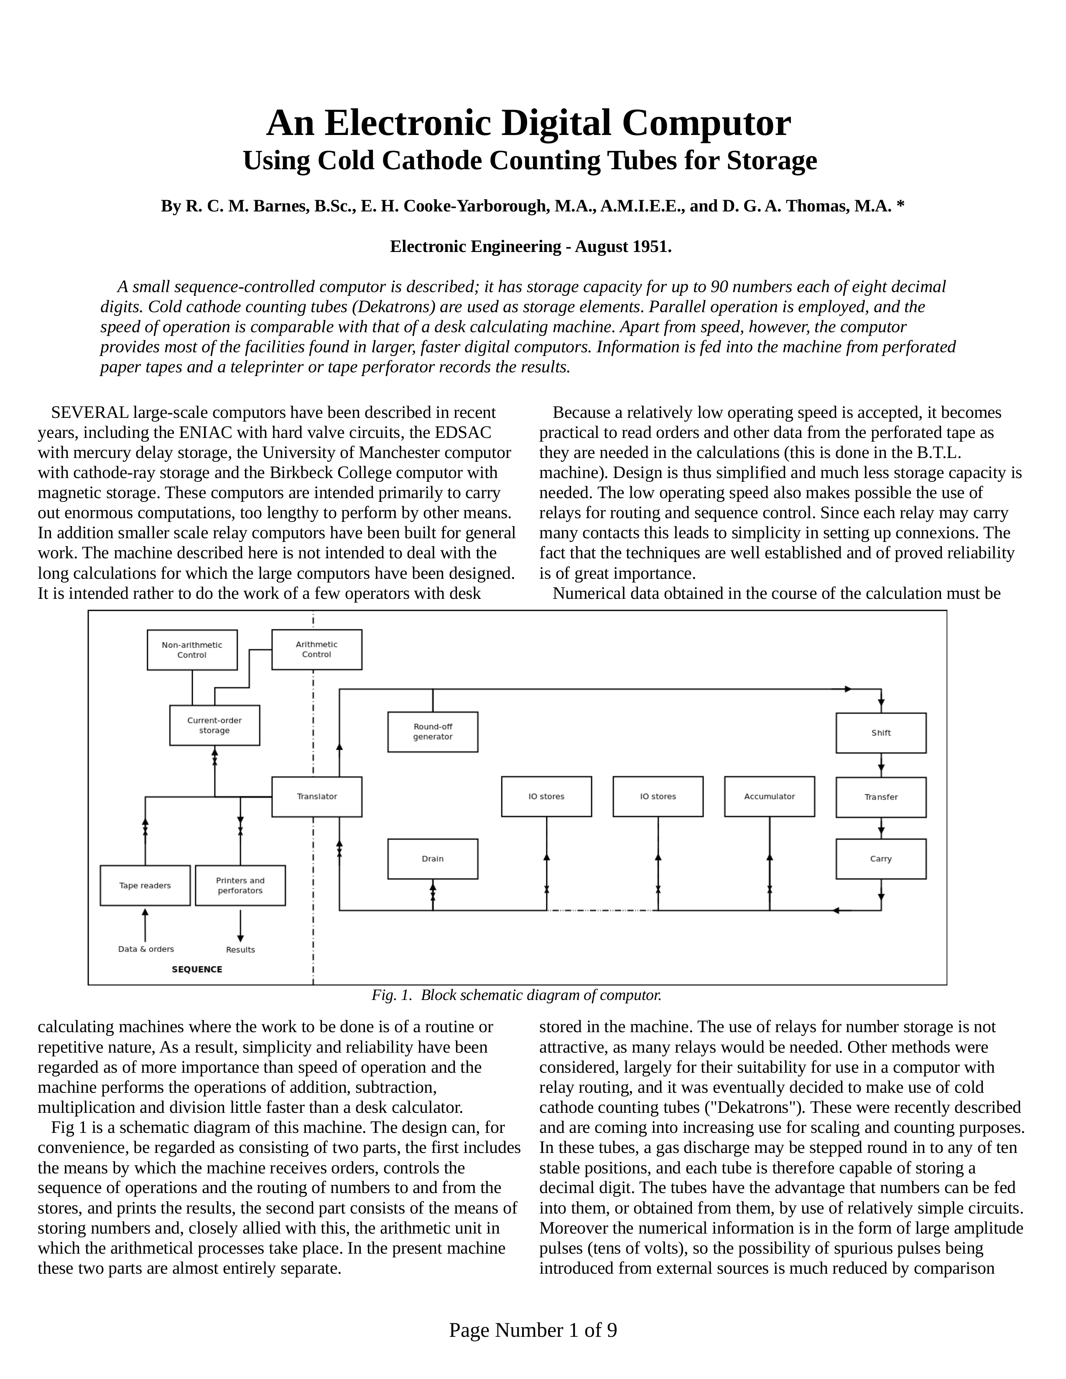
documentation/images/harwell-ee-1951-txt-p1.jpg
