prpplague/witch_dev/documentation/images/HarwellDekatronComputer-2.jpg

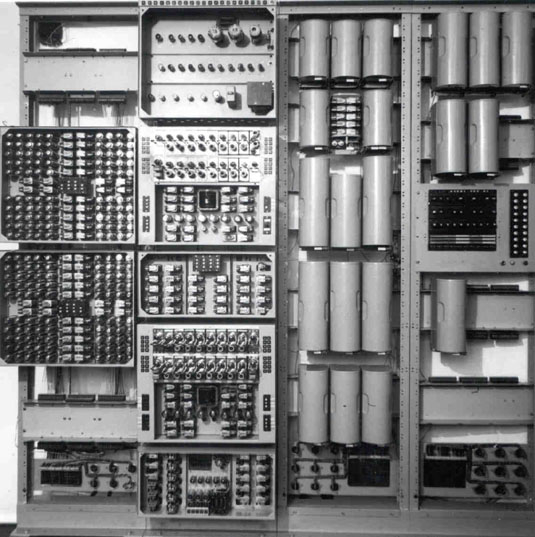
documentation/images/HarwellDekatronComputer-2.jpg
