prpplague/witch_dev/documentation/images/HarwellDekatronComputer.jpg

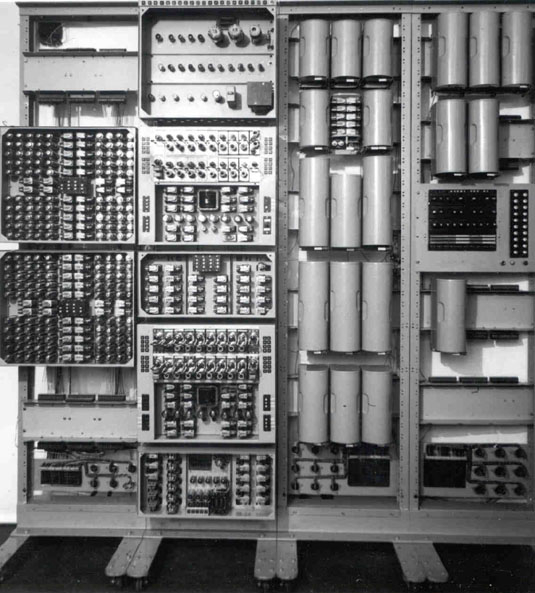
documentation/images/HarwellDekatronComputer.jpg
