prpplague/witch_dev/documentation/images/witch-figure1.png

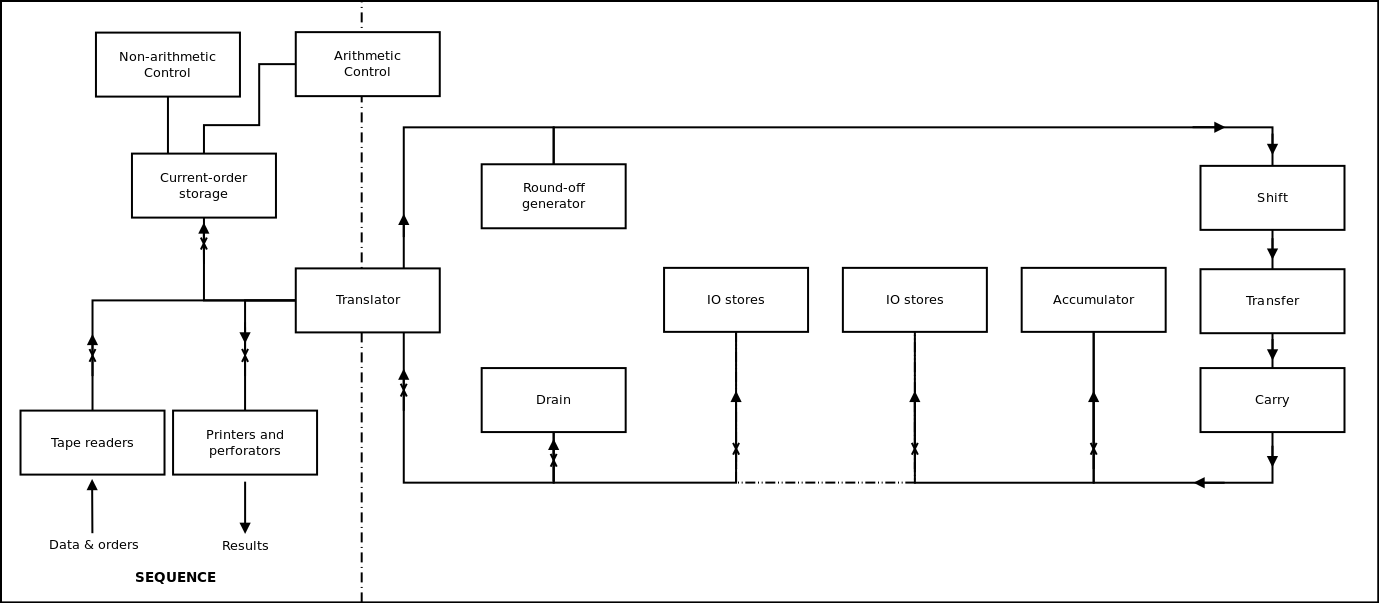
documentation/images/witch-figure1.png
