prpplague/witch_dev/documentation/ramsbottom/WITCH, or the Harwell Dekatron Computer_files/cer.jpg

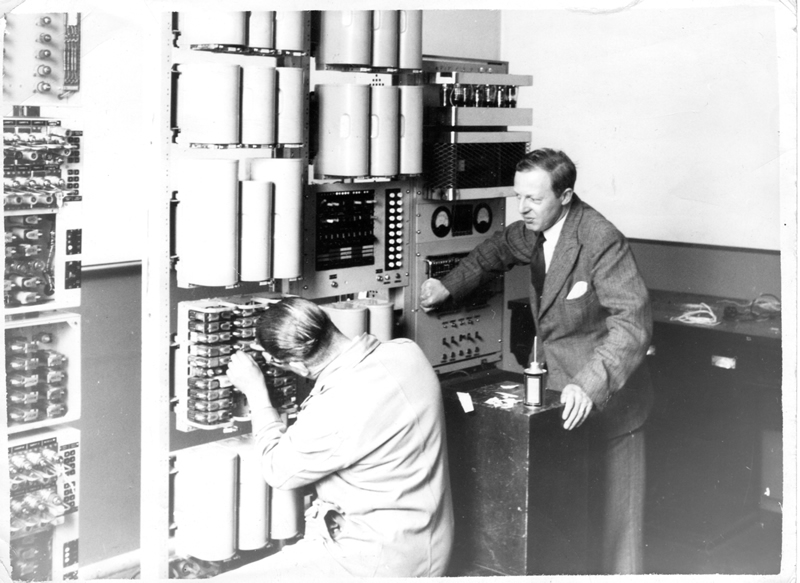
documentation/ramsbottom/WITCH, or the Harwell Dekatron Computer_files/cer.jpg
