prpplague/witch_dev/documentation/ramsbottom/WITCH, or the Harwell Dekatron Computer_files/IMG_6186.jpg

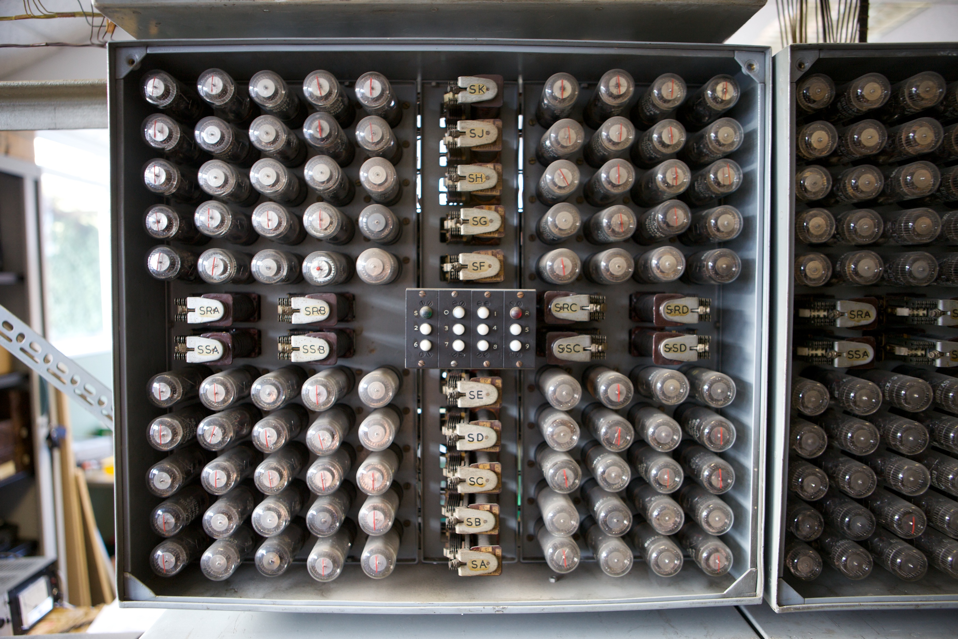
documentation/ramsbottom/WITCH, or the Harwell Dekatron Computer_files/IMG_6186.jpg
