prpplague/witch_dev/documentation/WITCH-pictures/block-socket1.JPG

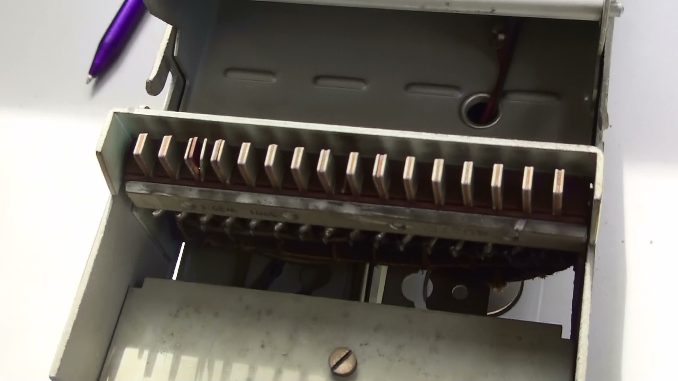
documentation/WITCH-pictures/block-socket1.JPG
