prpplague/witch_dev/documentation/WITCH-pictures/block-socket2.JPG

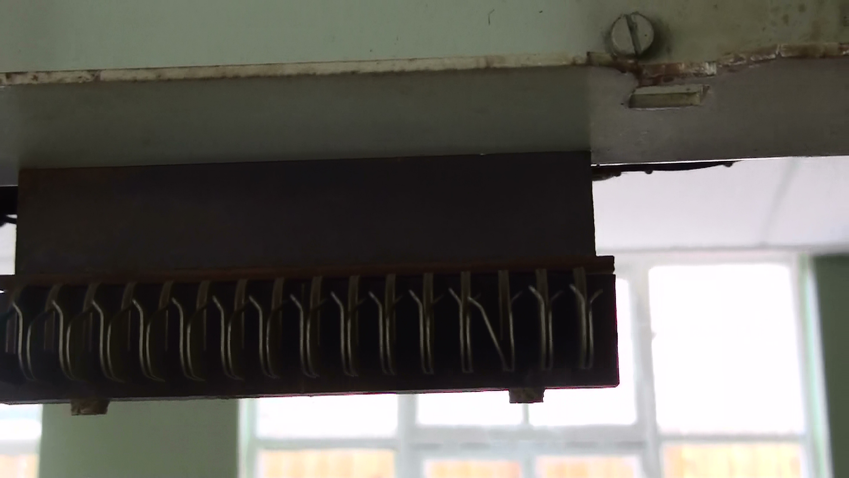
documentation/WITCH-pictures/block-socket2.JPG
