prpplague/witch_dev/documentation/WITCH-pictures/DSC06120.JPG

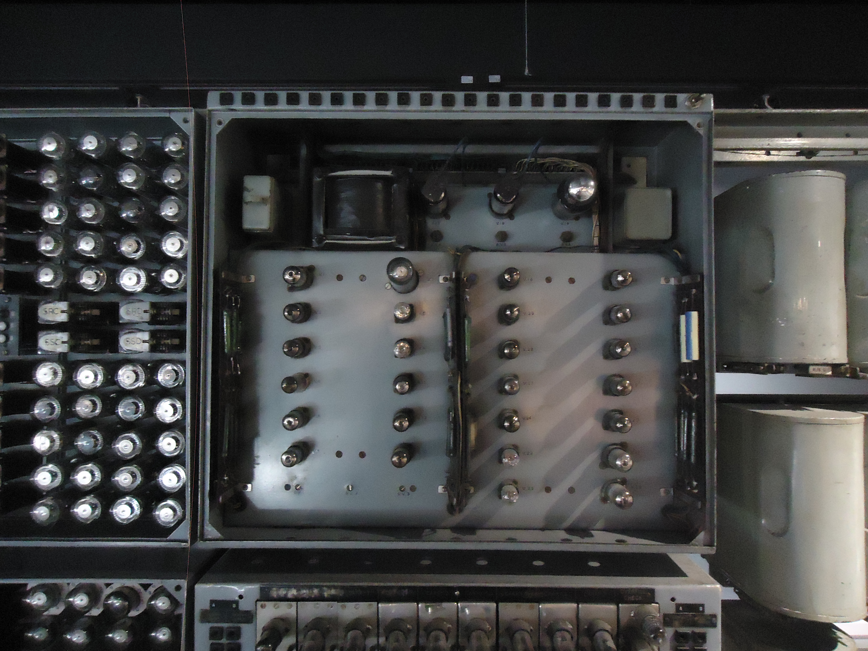
documentation/WITCH-pictures/DSC06120.JPG
