prpplague/witch_dev/documentation/WITCH-pictures/DSC06125.JPG

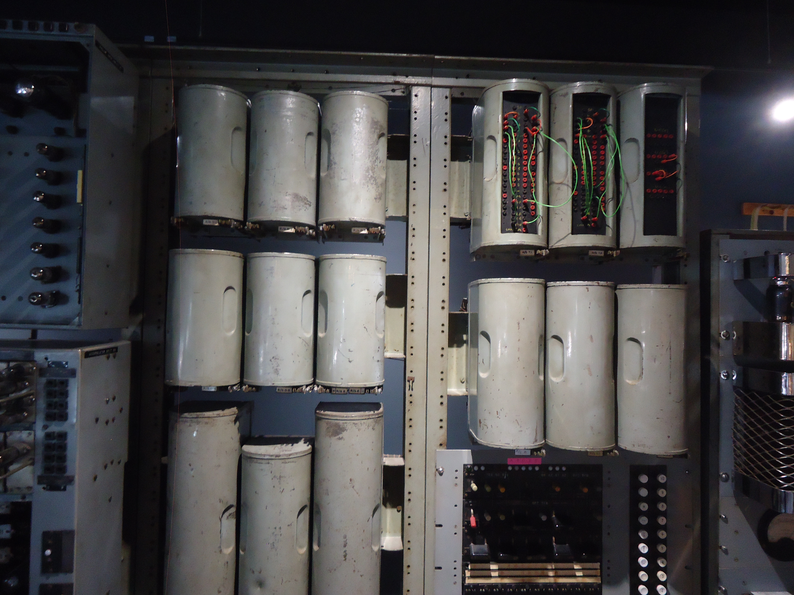
documentation/WITCH-pictures/DSC06125.JPG
