prpplague/witch_dev/documentation/WITCH-pictures/DSC06127.JPG

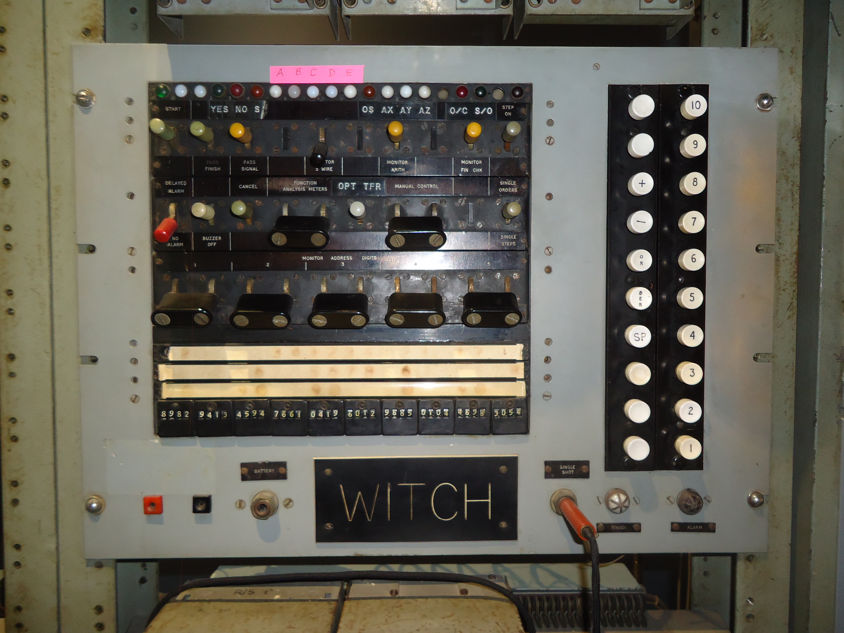
documentation/WITCH-pictures/DSC06127.JPG
