prpplague/witch_dev/documentation/WITCH-pictures/DSC06133.JPG

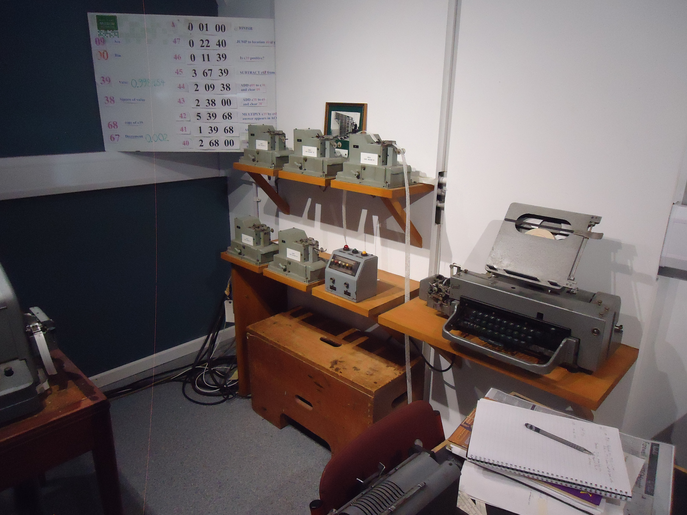
documentation/WITCH-pictures/DSC06133.JPG
