prpplague/witch_dev/documentation/WITCH-pictures/DSC06134.JPG

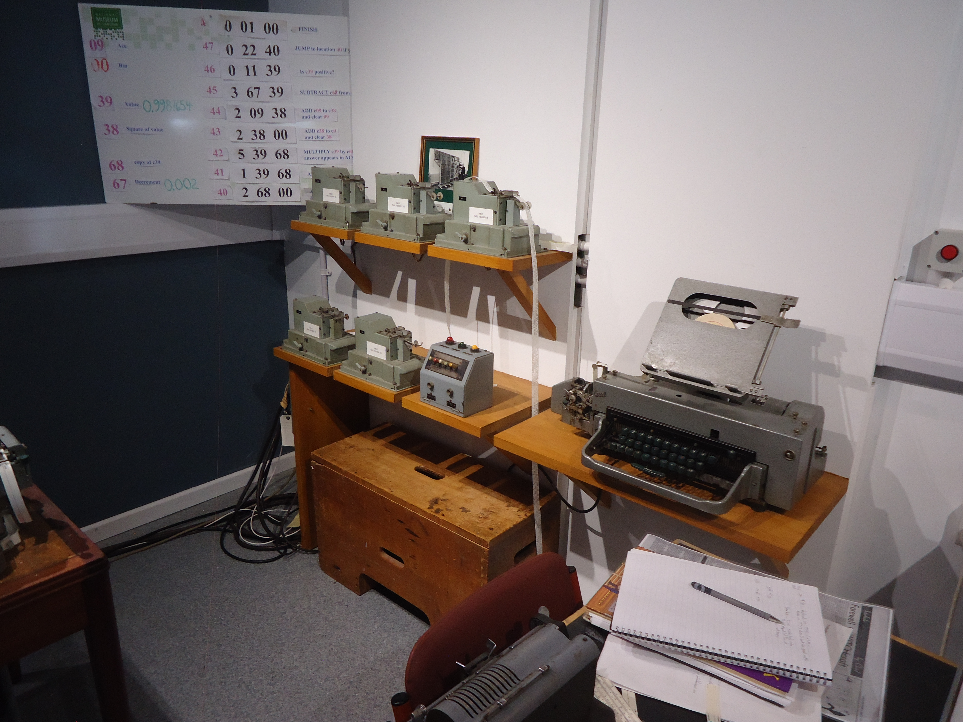
documentation/WITCH-pictures/DSC06134.JPG
