prpplague/witch_dev/documentation/WITCH-pictures/DSC06138.JPG

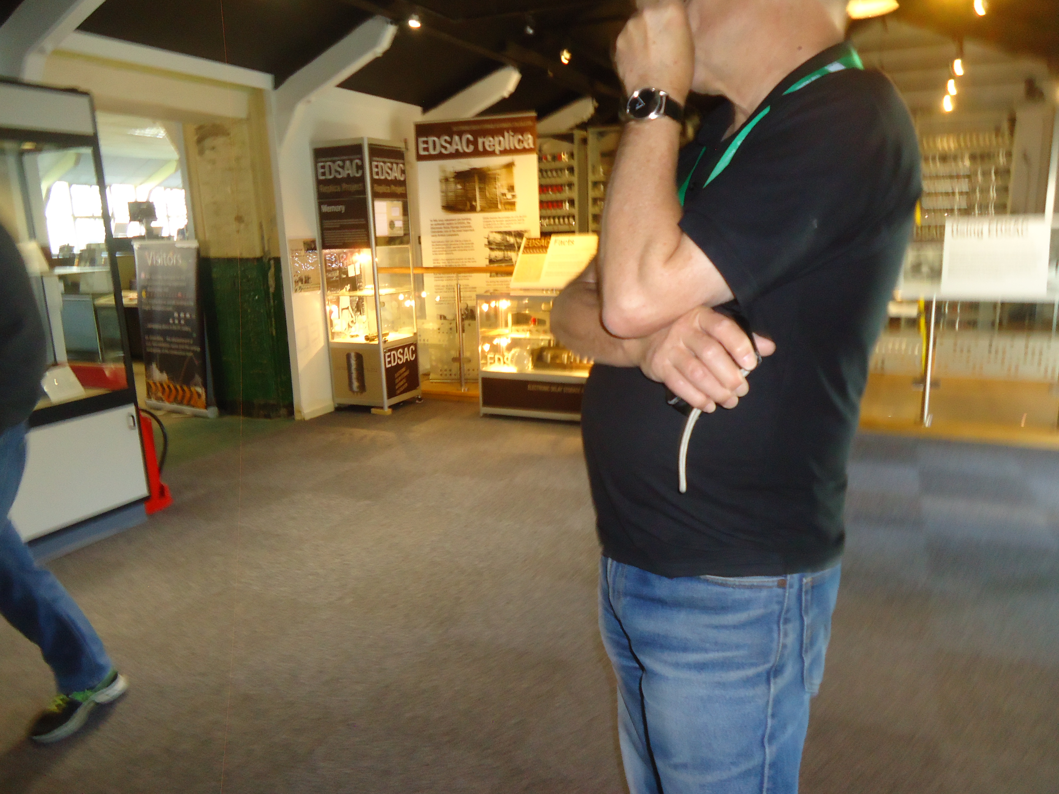
documentation/WITCH-pictures/DSC06138.JPG
