prpplague/witch_dev/documentation/WITCH-pictures/DSC06139.JPG

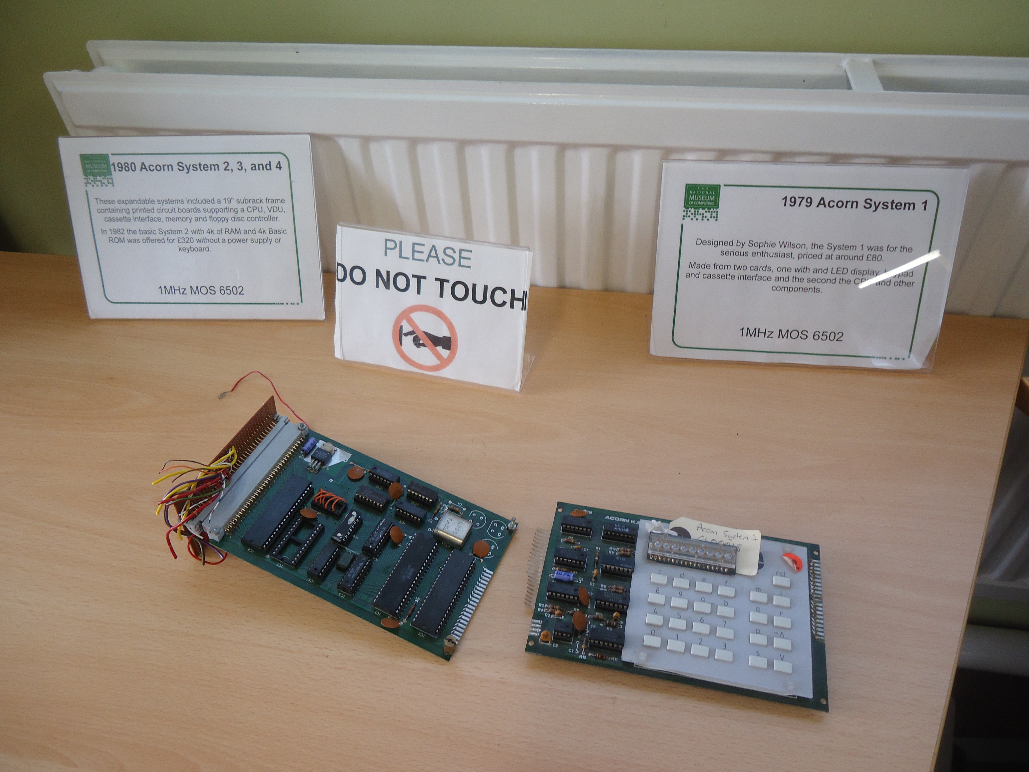
documentation/WITCH-pictures/DSC06139.JPG
