prpplague/witch_dev/documentation/WITCH-pictures/DSC06141.JPG

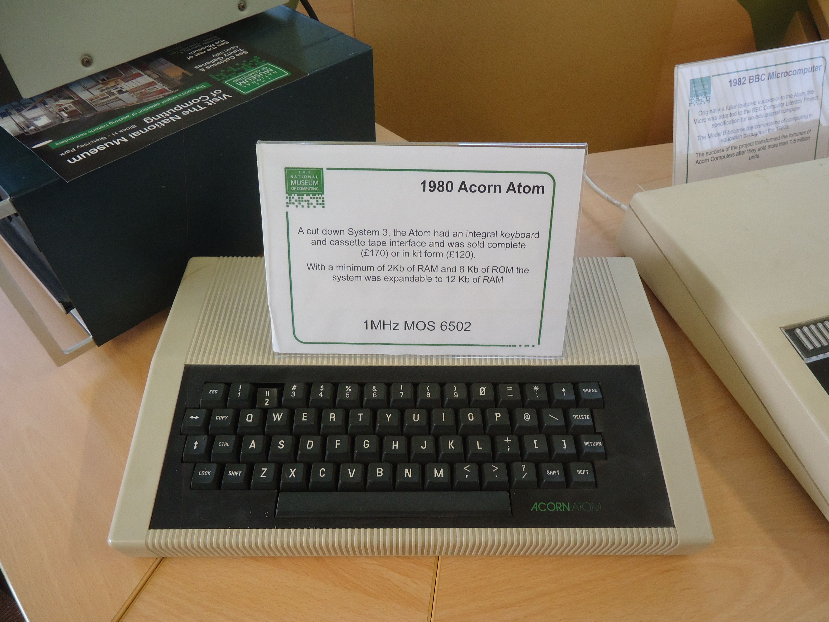
documentation/WITCH-pictures/DSC06141.JPG
