prpplague/witch_dev/documentation/WITCH-pictures/DSC06142.JPG

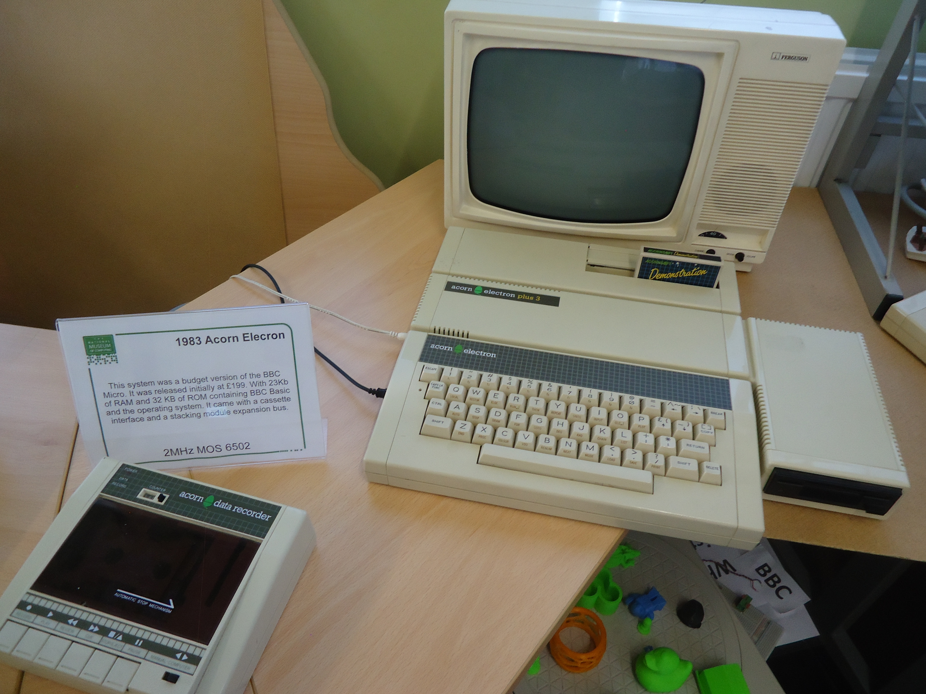
documentation/WITCH-pictures/DSC06142.JPG
