prpplague/witch_dev/documentation/WITCH-pictures/DSC06143.JPG

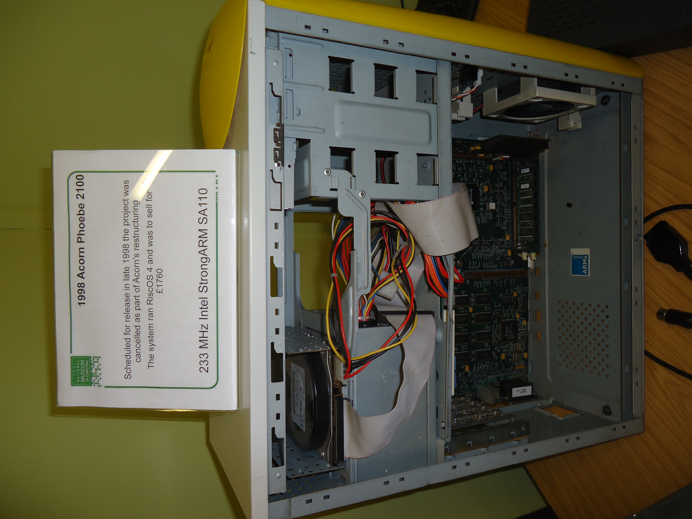
documentation/WITCH-pictures/DSC06143.JPG
