prpplague/witch_dev/documentation/WITCH-pictures/DSC06144.JPG

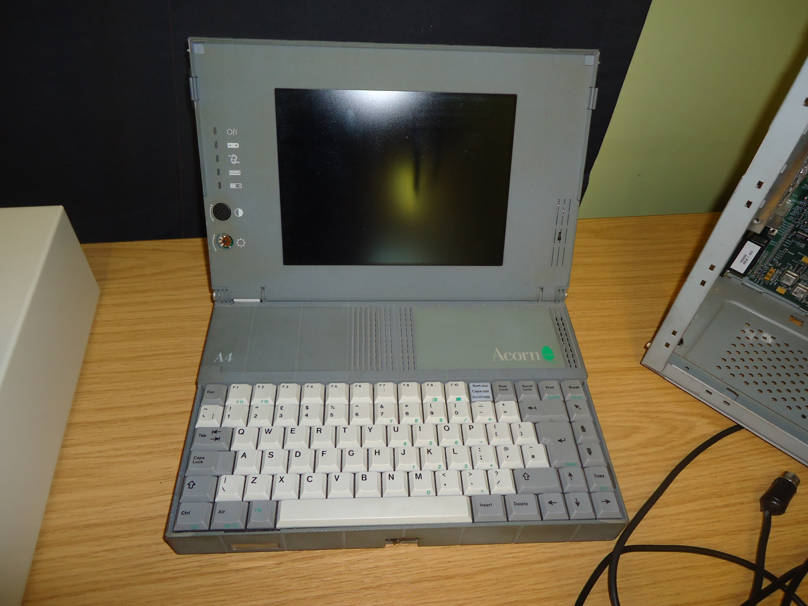
documentation/WITCH-pictures/DSC06144.JPG
