prpplague/witch_dev/documentation/WITCH-pictures/DSC06145.JPG

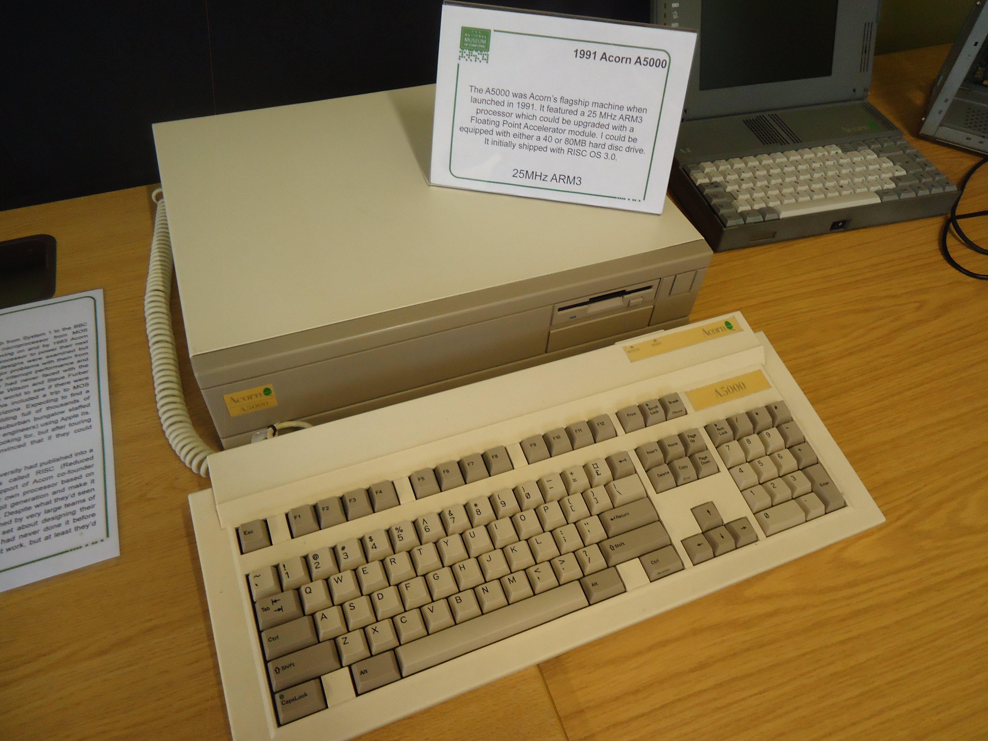
documentation/WITCH-pictures/DSC06145.JPG
