prpplague/witch_dev/documentation/WITCH-pictures/DSC06146.JPG

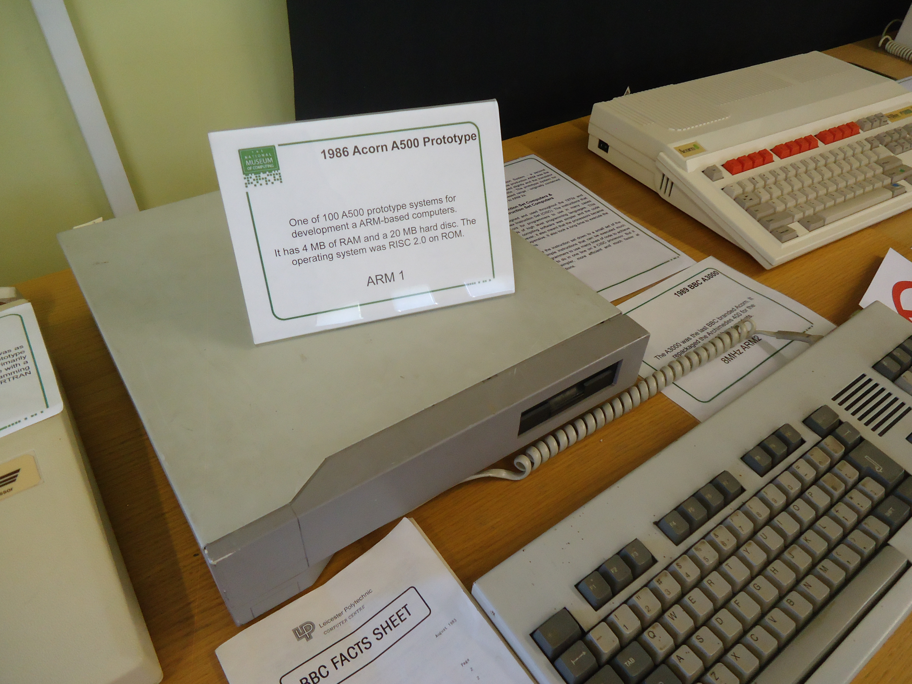
documentation/WITCH-pictures/DSC06146.JPG
