prpplague/witch_dev/documentation/WITCH-pictures/DSC06147.JPG

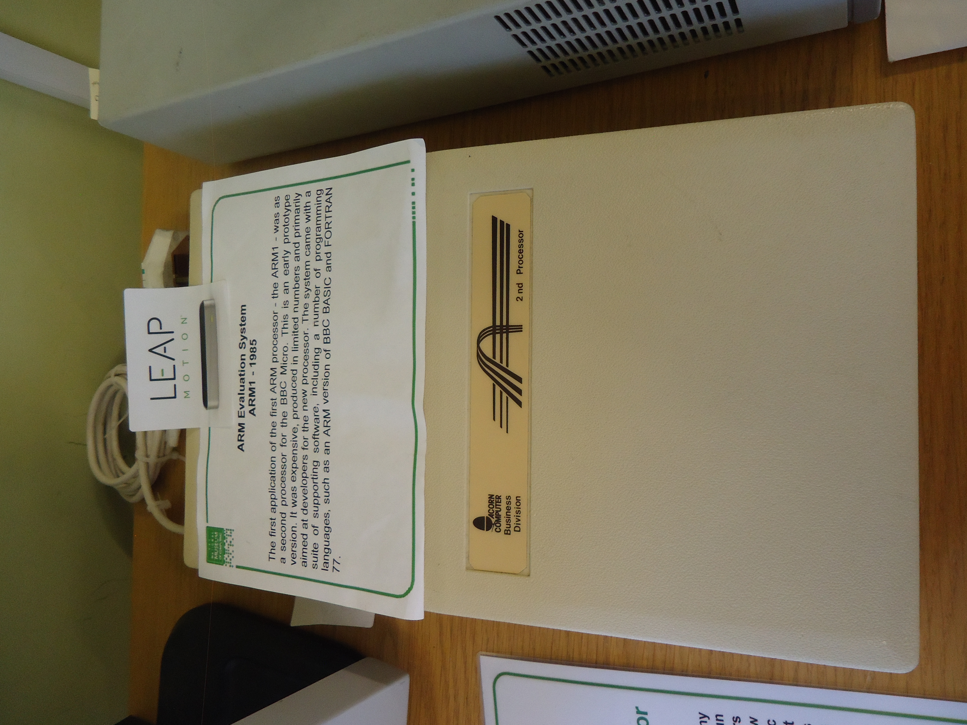
documentation/WITCH-pictures/DSC06147.JPG
