prpplague/witch_dev/documentation/WITCH-pictures/DSC06148.JPG

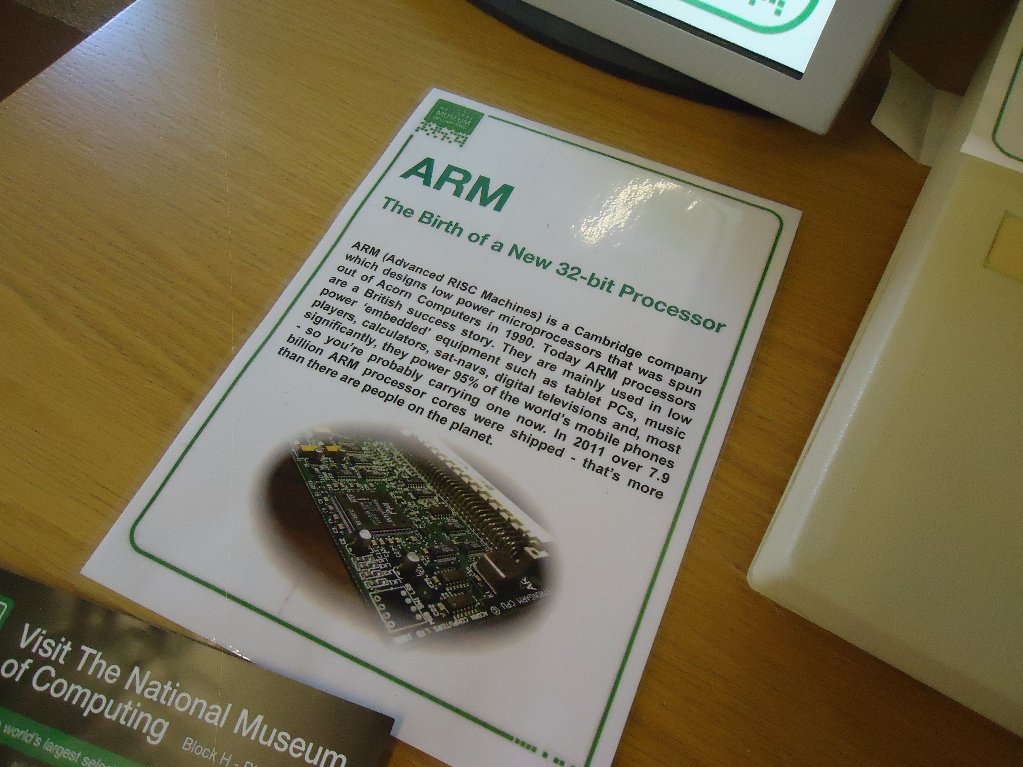
documentation/WITCH-pictures/DSC06148.JPG
