prpplague/witch_dev/documentation/WITCH-pictures/DSC06150.JPG

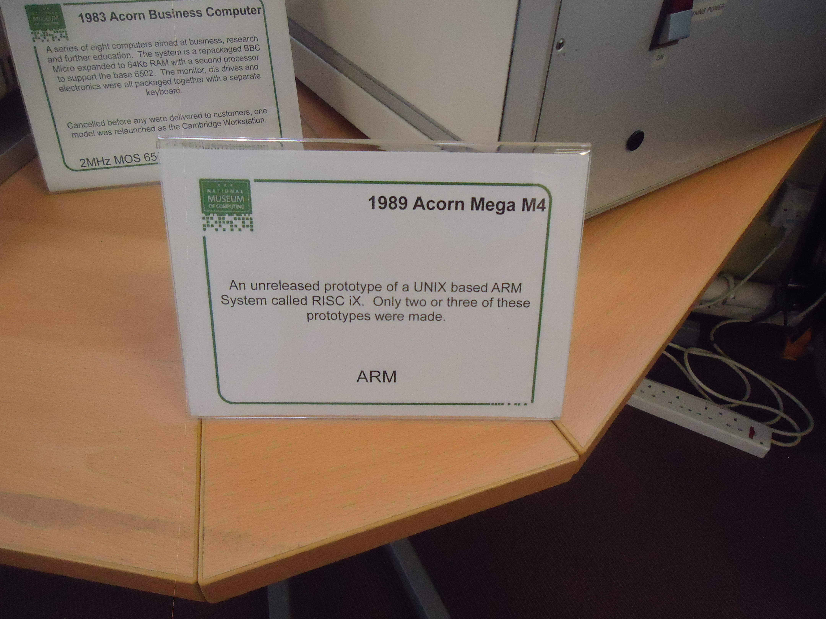
documentation/WITCH-pictures/DSC06150.JPG
