prpplague/witch_dev/documentation/WITCH-pictures/DSC06151.JPG

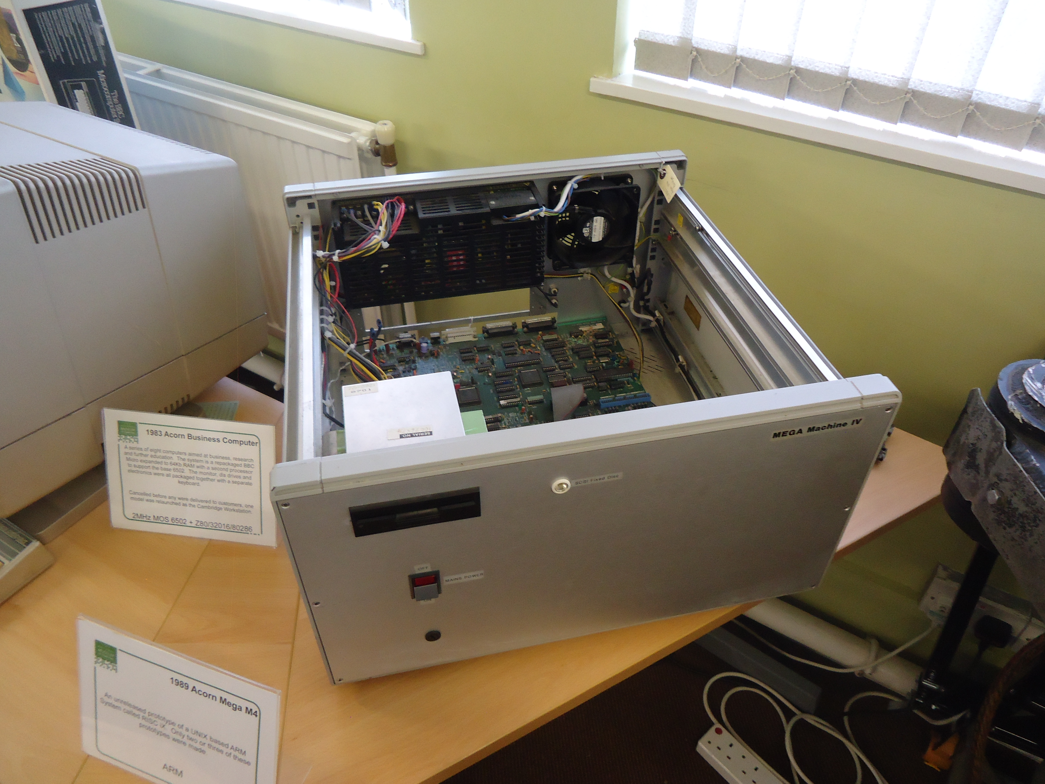
documentation/WITCH-pictures/DSC06151.JPG
