prpplague/witch_dev/documentation/WITCH-pictures/DSC06152.JPG

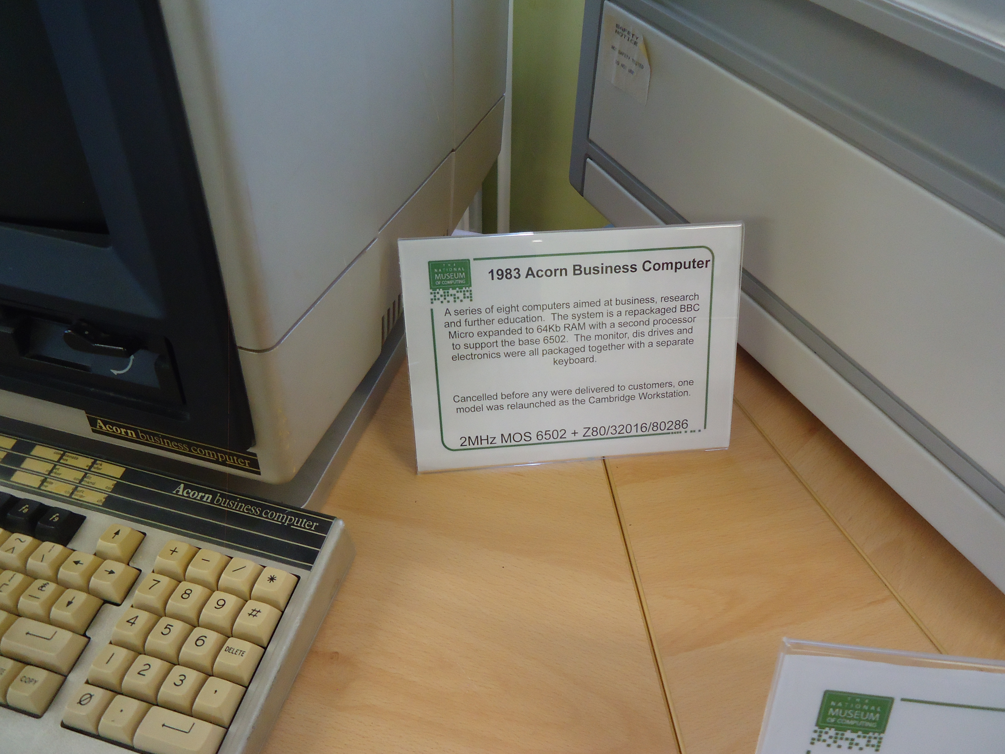
documentation/WITCH-pictures/DSC06152.JPG
