prpplague/witch_dev/documentation/WITCH-pictures/plugin-modules/carry_unit_waveforms-a.jpg

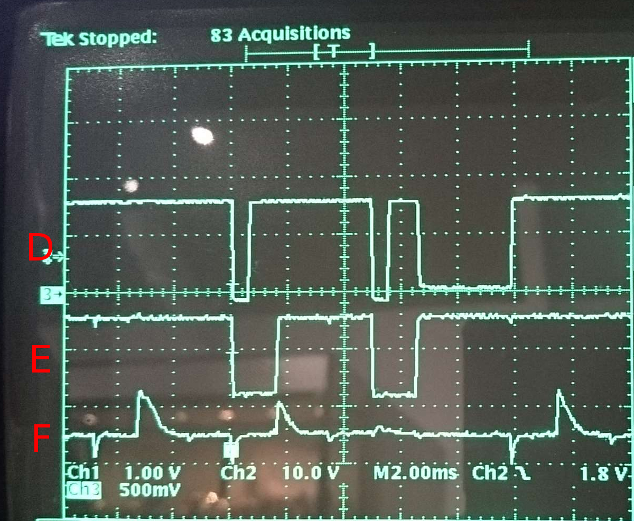
documentation/WITCH-pictures/plugin-modules/carry_unit_waveforms-a.jpg
