prpplague/witch_dev/documentation/WITCH-pictures/plugin-modules/carry_unit_waveforms-b.jpg

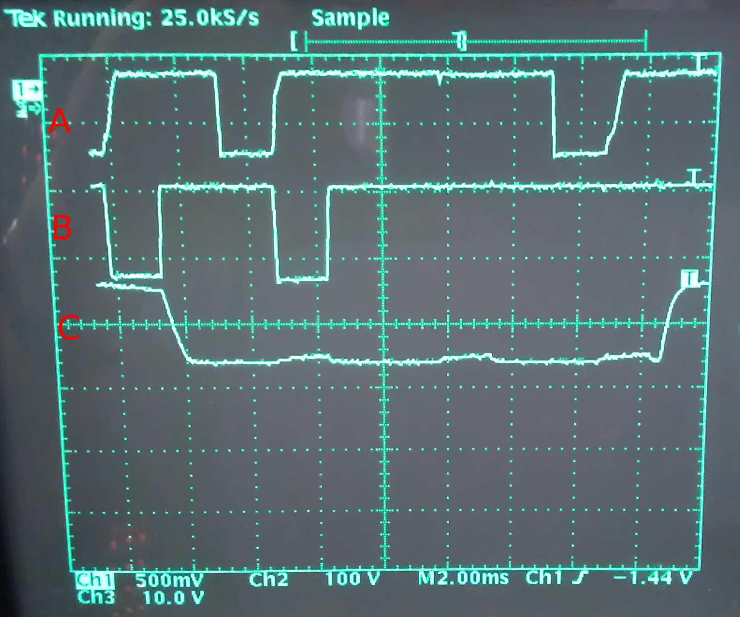
documentation/WITCH-pictures/plugin-modules/carry_unit_waveforms-b.jpg
