prpplague/witch_dev/documentation/WITCH-pictures/plugin-modules/IMG_1141.jpg

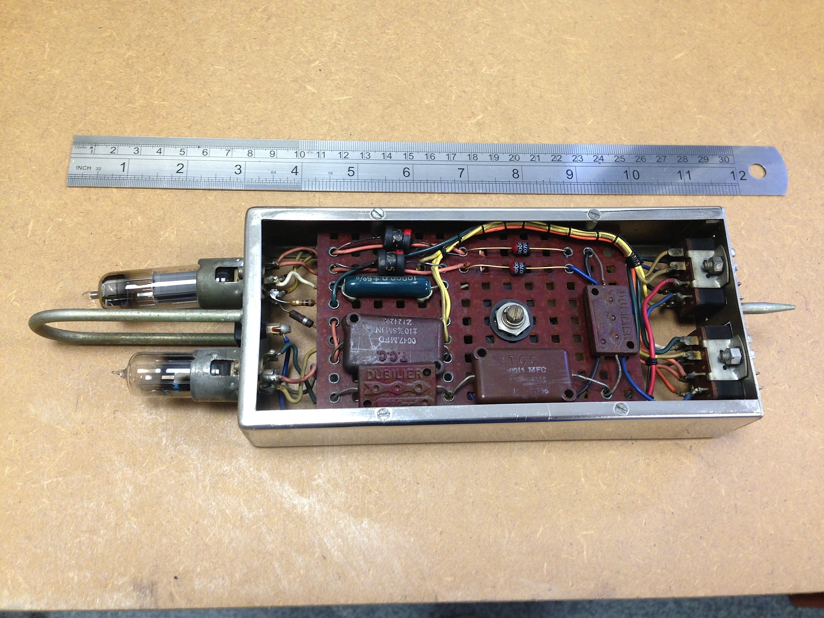
documentation/WITCH-pictures/plugin-modules/IMG_1141.jpg
