prpplague/witch_dev/documentation/WITCH-pictures/plugin-modules/IMG_1142.jpg

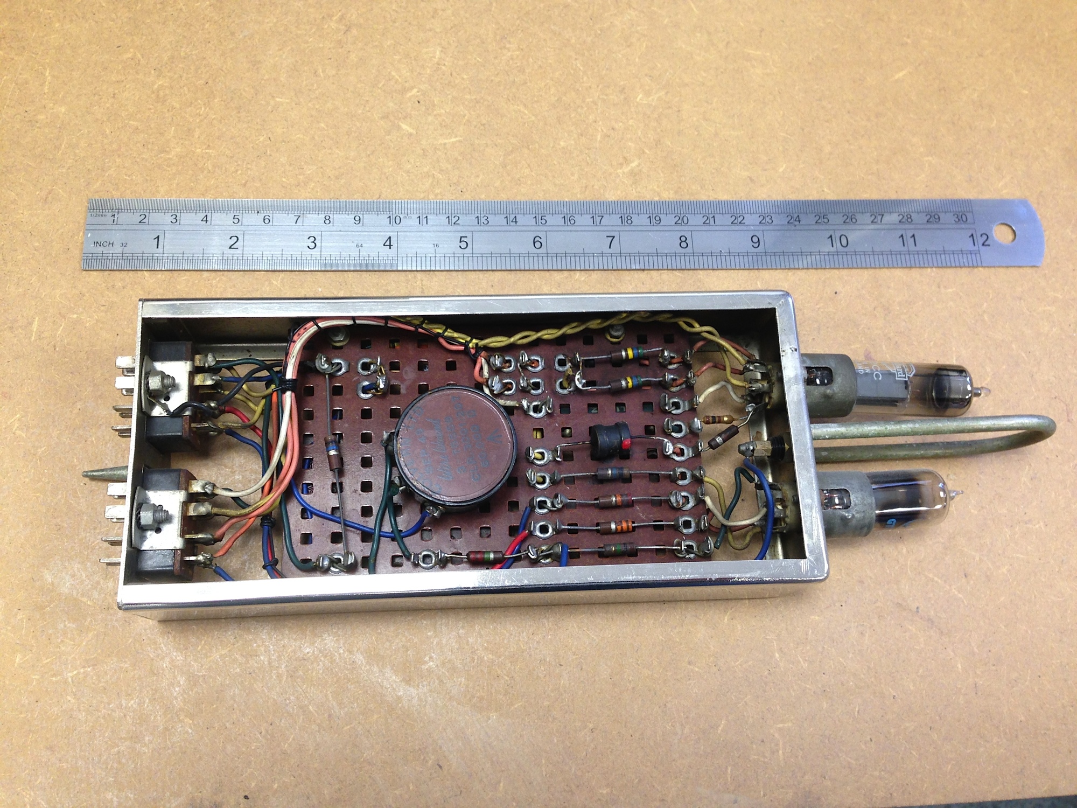
documentation/WITCH-pictures/plugin-modules/IMG_1142.jpg
