prpplague/witch_dev/documentation/WITCH-pictures/plugin-modules/IMG_1143.jpg

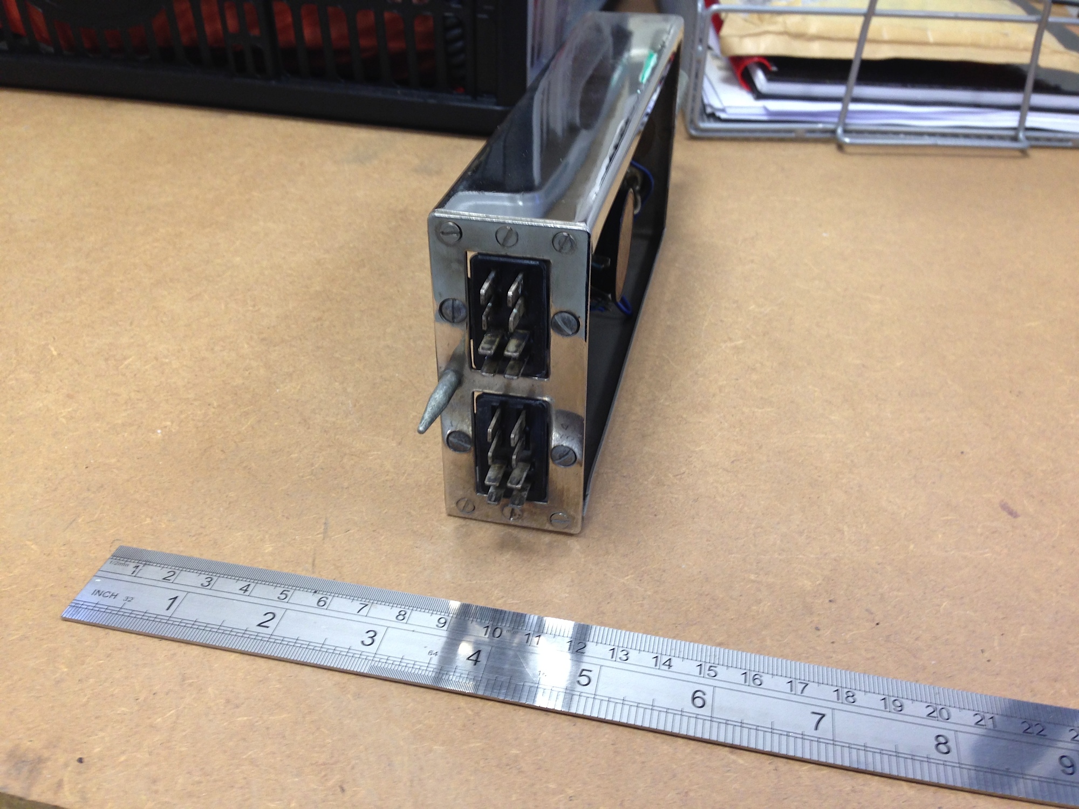
documentation/WITCH-pictures/plugin-modules/IMG_1143.jpg
