prpplague/witch_dev/documentation/WITCH-pictures/plugin-modules/IMG_1144.jpg

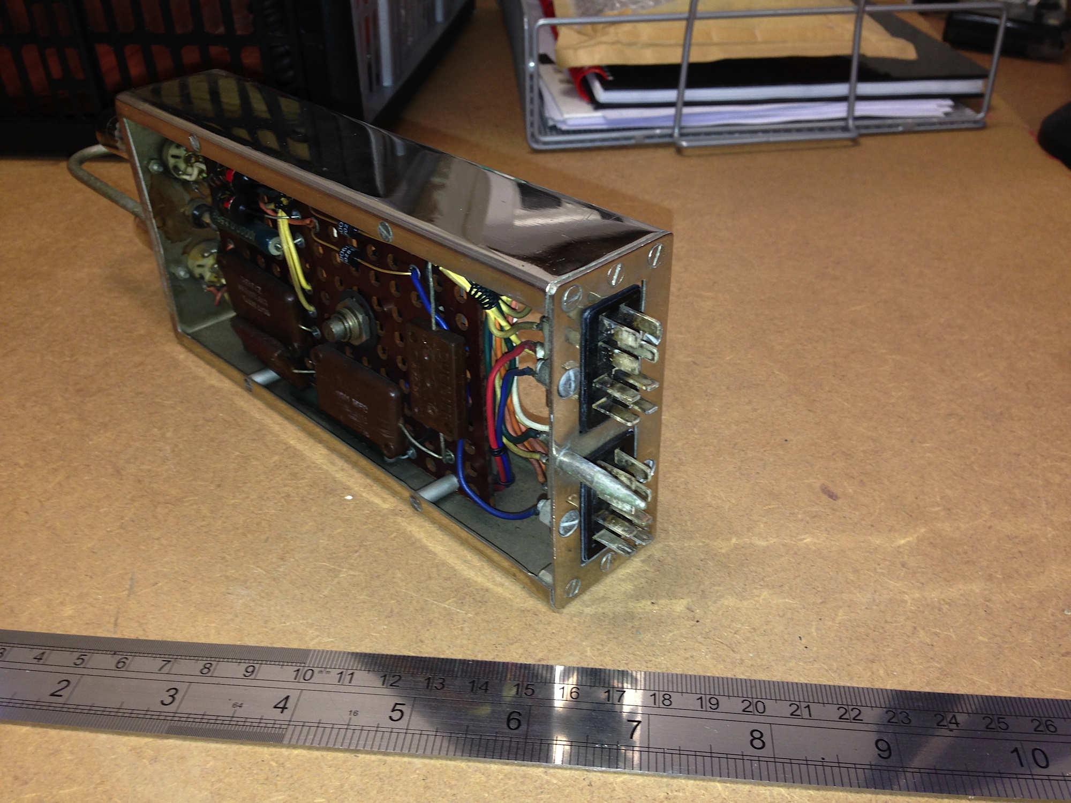
documentation/WITCH-pictures/plugin-modules/IMG_1144.jpg
