prpplague/witch_dev/documentation/WITCH-pictures/plugin-modules/IMG_1145.jpg

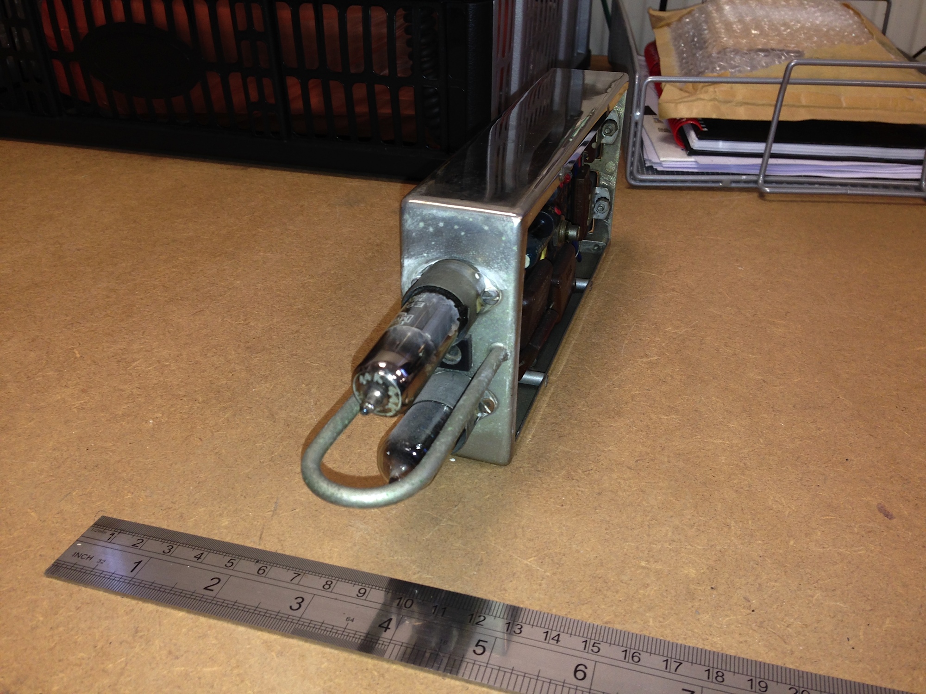
documentation/WITCH-pictures/plugin-modules/IMG_1145.jpg
