prpplague/witch_dev/documentation/WITCH-pictures/plugin-modules/IMG_1147.jpg

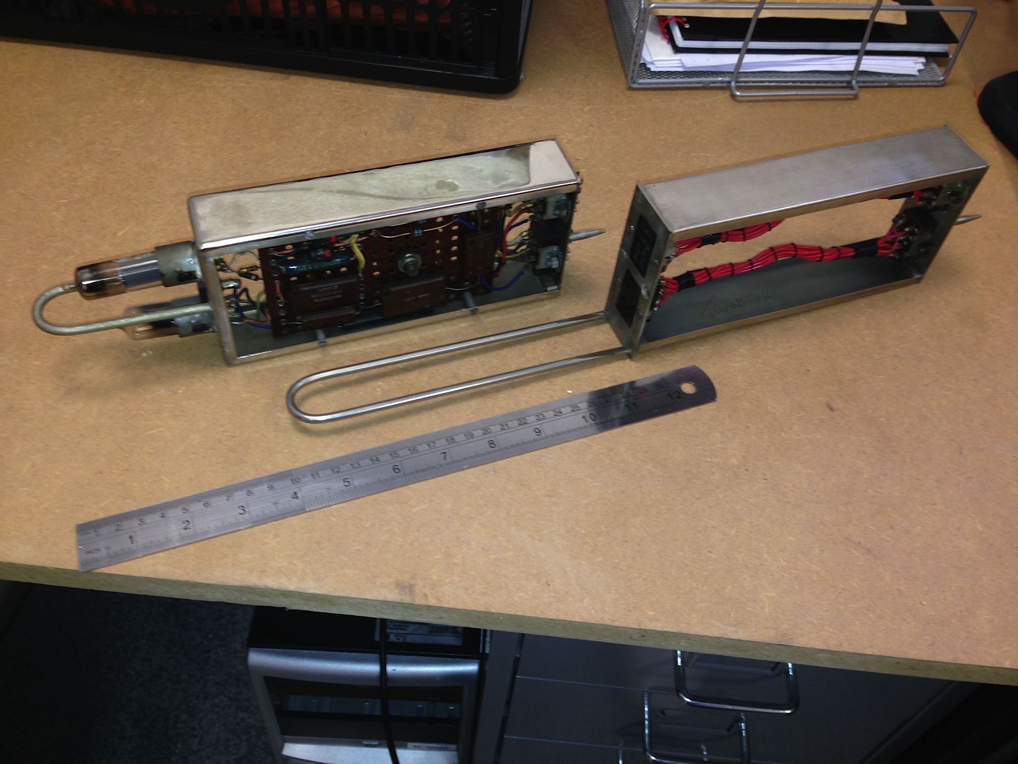
documentation/WITCH-pictures/plugin-modules/IMG_1147.jpg
