prpplague/witch_dev/documentation/WITCH-pictures/plugin-modules/IMG_1149.jpg

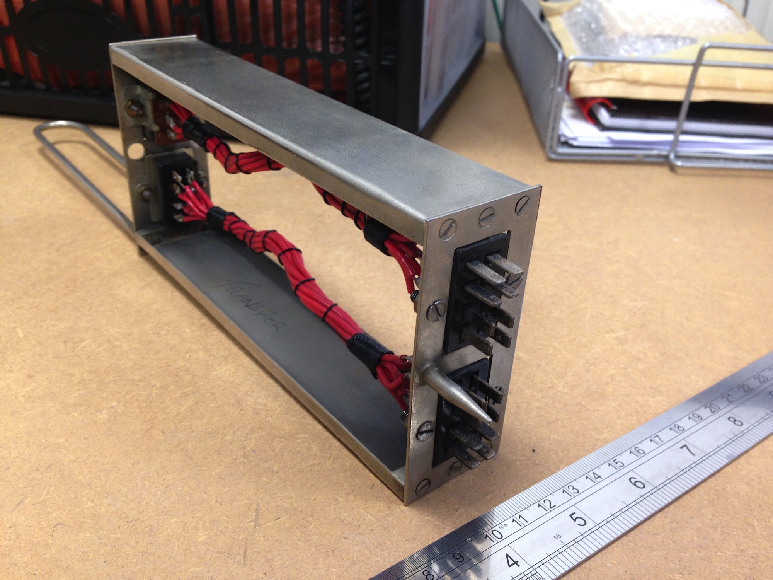
documentation/WITCH-pictures/plugin-modules/IMG_1149.jpg
