prpplague/witch_dev/documentation/WITCH-pictures/plugin-modules/IMG_1150.jpg

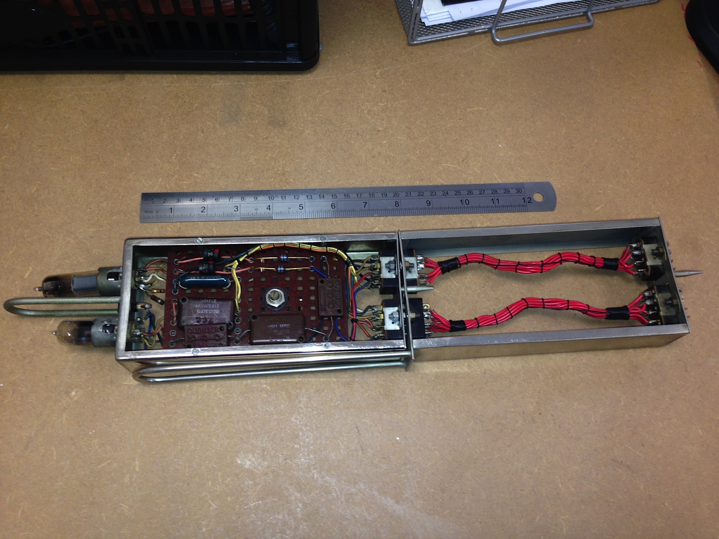
documentation/WITCH-pictures/plugin-modules/IMG_1150.jpg
