prpplague/witch_dev/documentation/WITCH-pictures/plugin-modules/IMG_1151.jpg

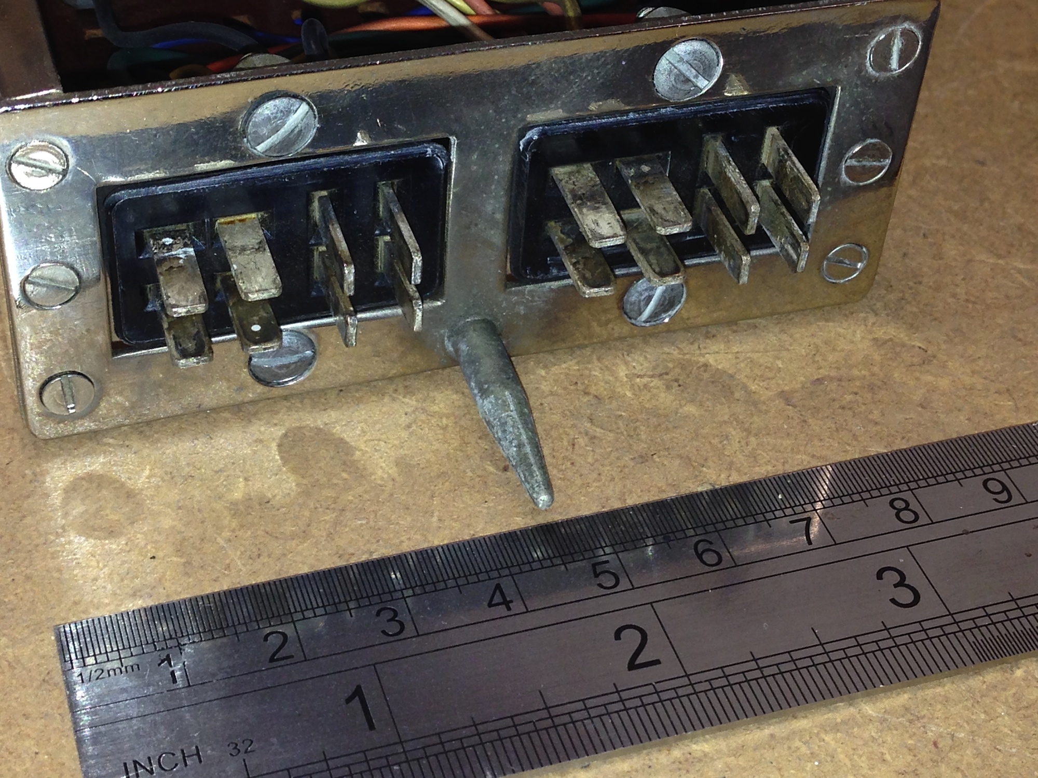
documentation/WITCH-pictures/plugin-modules/IMG_1151.jpg
