prpplague/witch_dev/documentation/WITCH-pictures/plugin-modules/IMG_1152.jpg

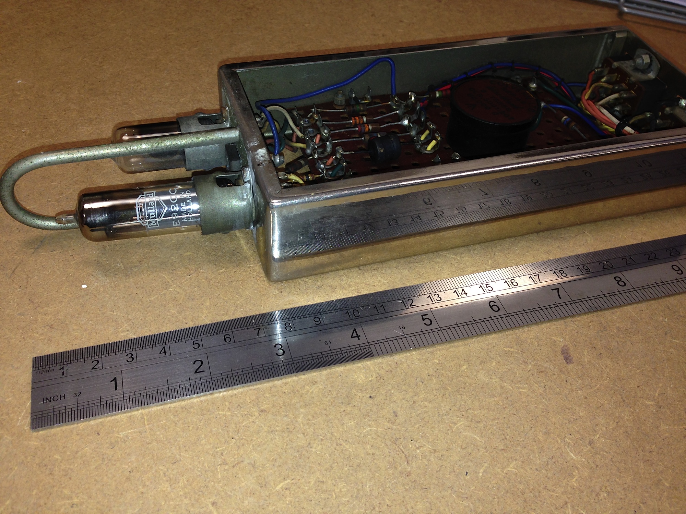
documentation/WITCH-pictures/plugin-modules/IMG_1152.jpg
