prpplague/witch_dev/documentation/WITCH-pictures/plugin-modules/plugins.jpg

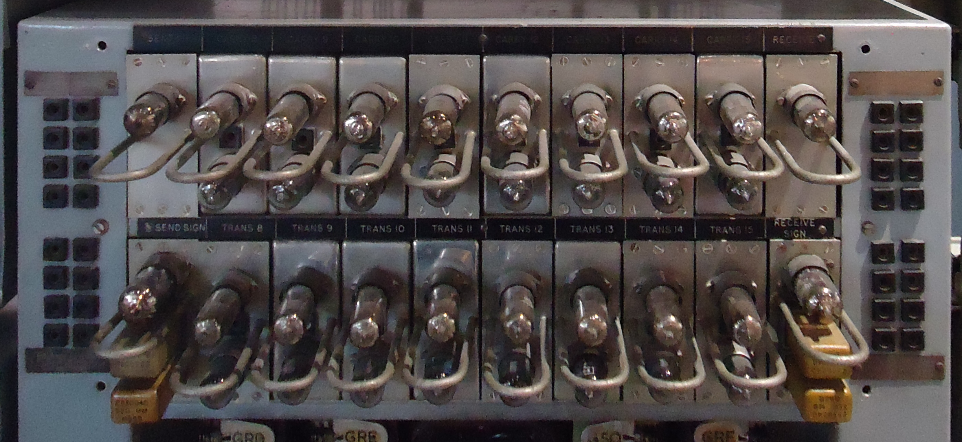
documentation/WITCH-pictures/plugin-modules/plugins.jpg
