prpplague/witch_dev/documentation/WITCH-pictures/relay-t-1.JPG

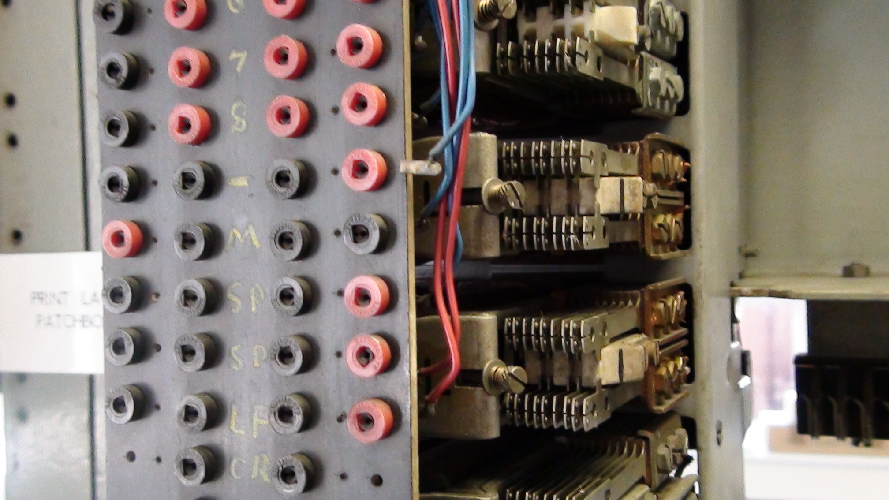
documentation/WITCH-pictures/relay-t-1.JPG
