prpplague/witch_dev/documentation/WITCH-pictures/relay-t-2.JPG

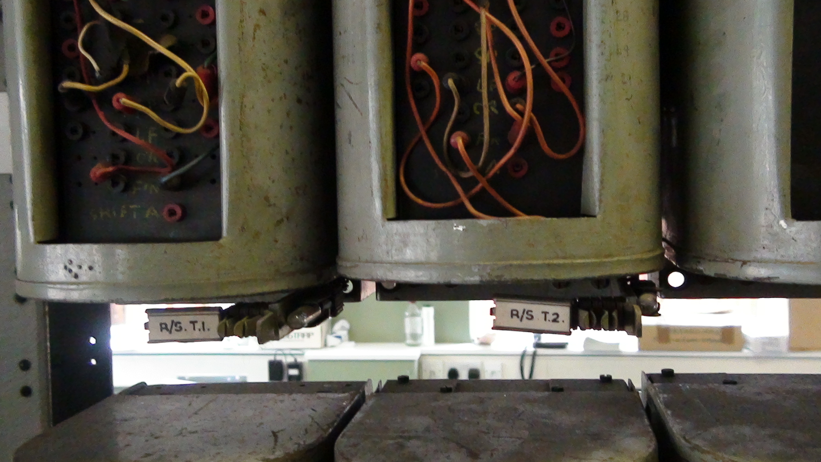
documentation/WITCH-pictures/relay-t-2.JPG
