prpplague/witch_dev/documentation/WITCH-pictures/relay-t-3.jpg

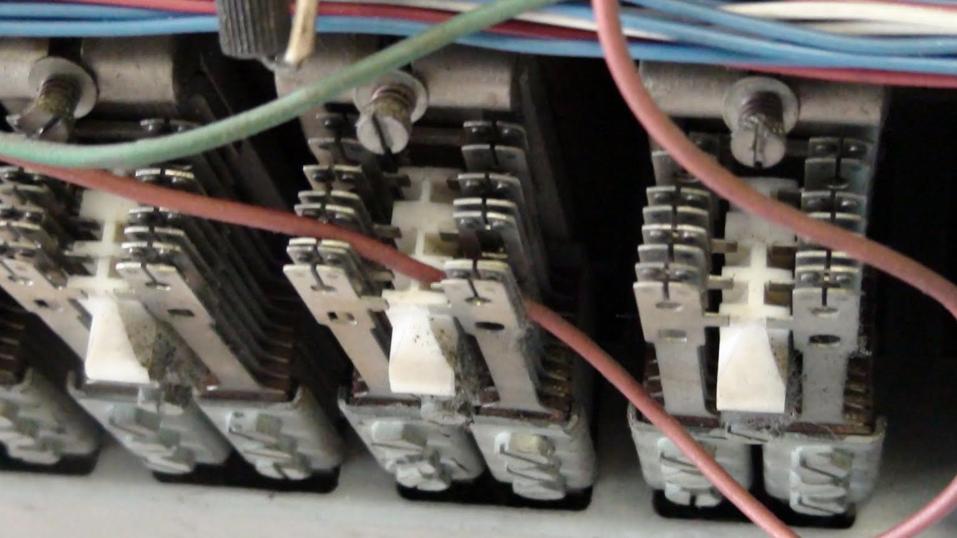
documentation/WITCH-pictures/relay-t-3.jpg
