prpplague/witch_dev/documentation/WITCH-pictures/relay-t-4.jpg

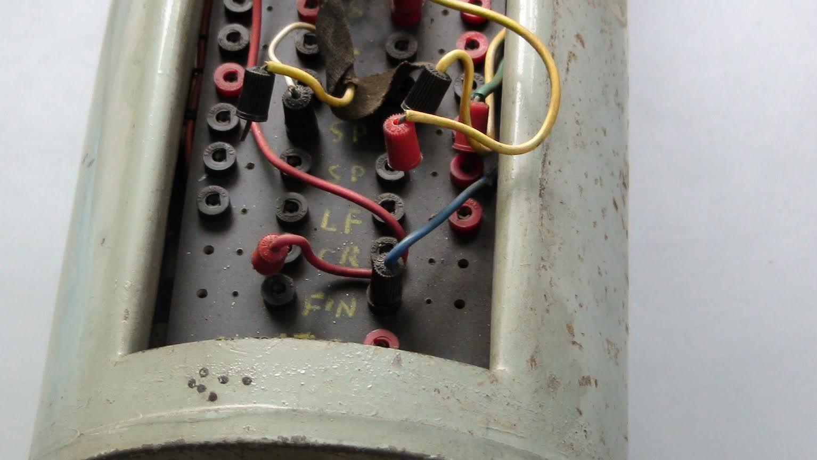
documentation/WITCH-pictures/relay-t-4.jpg
