prpplague/witch_dev/documentation/witch-program-1.jpg

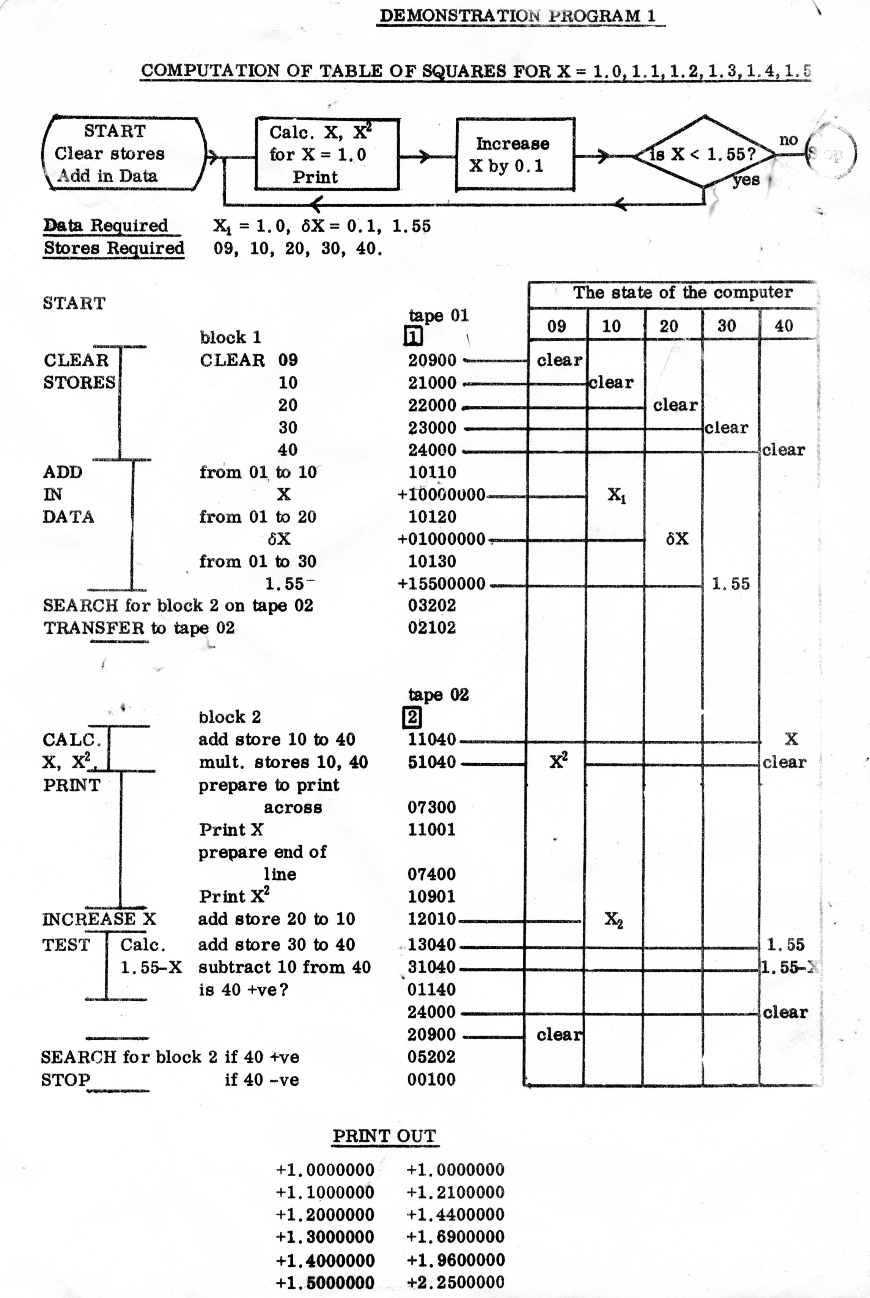
documentation/witch-program-1.jpg
