prpplague/witch_dev/documentation/witch-program-2.jpg

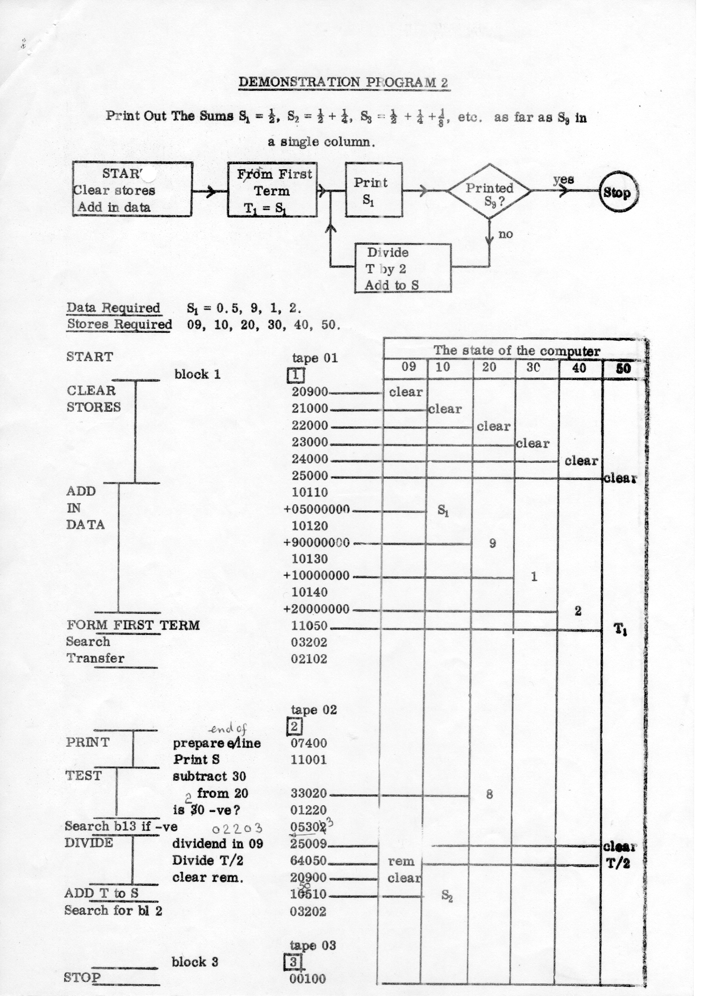
documentation/witch-program-2.jpg
