prpplague/witch_dev/documentation/WITCH-schematics/jpgs/1st Digit Selection - 47592.jpg

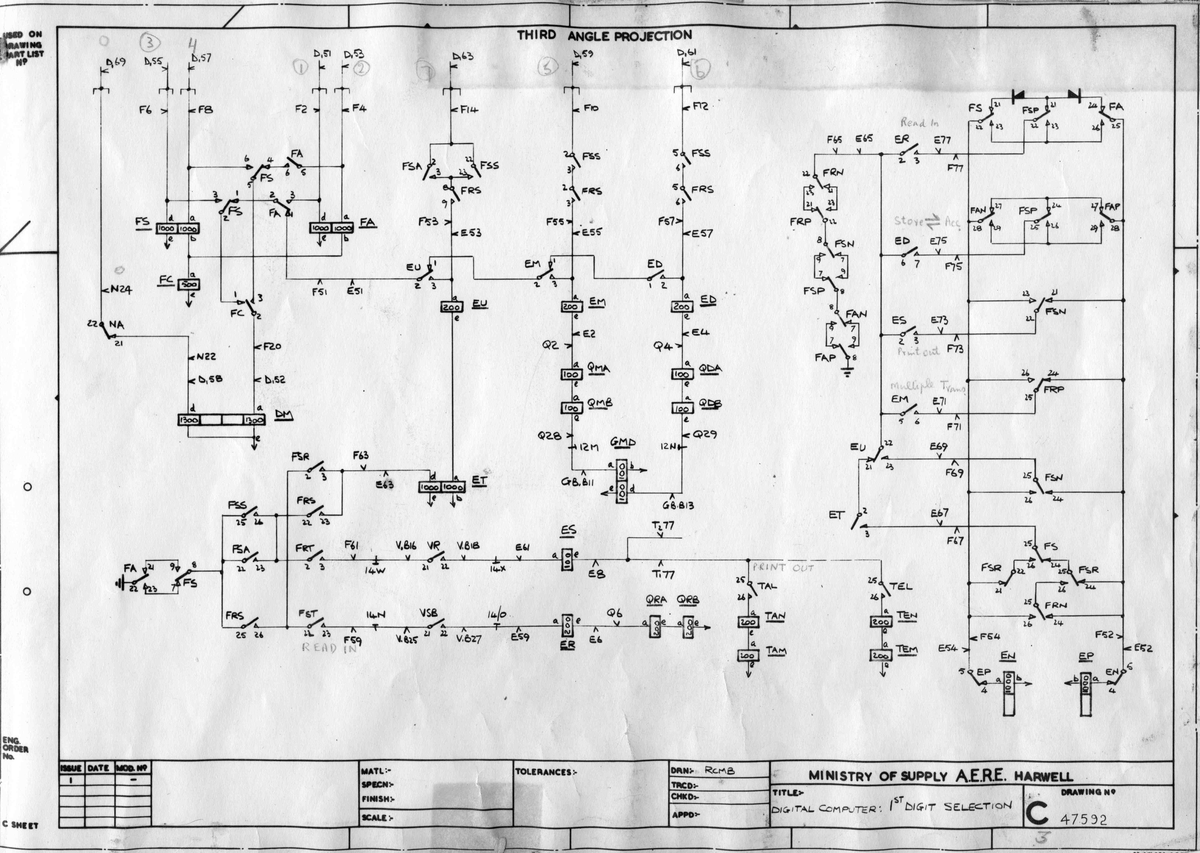
documentation/WITCH-schematics/jpgs/1st Digit Selection - 47592.jpg
