prpplague/witch_dev/documentation/WITCH-schematics/jpgs/2nd Digit Selection - 47591.jpg

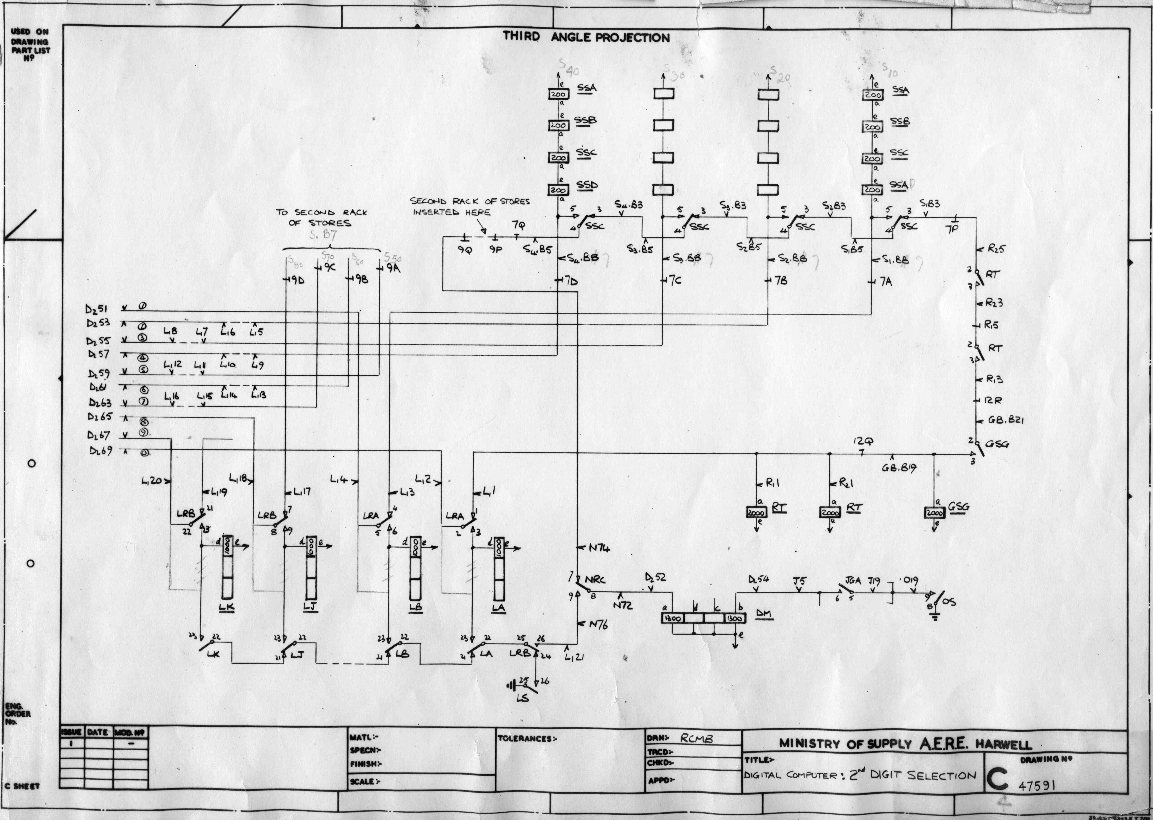
documentation/WITCH-schematics/jpgs/2nd Digit Selection - 47591.jpg
