prpplague/witch_dev/documentation/WITCH-schematics/jpgs/3rd Digit Selection - 47590.jpg

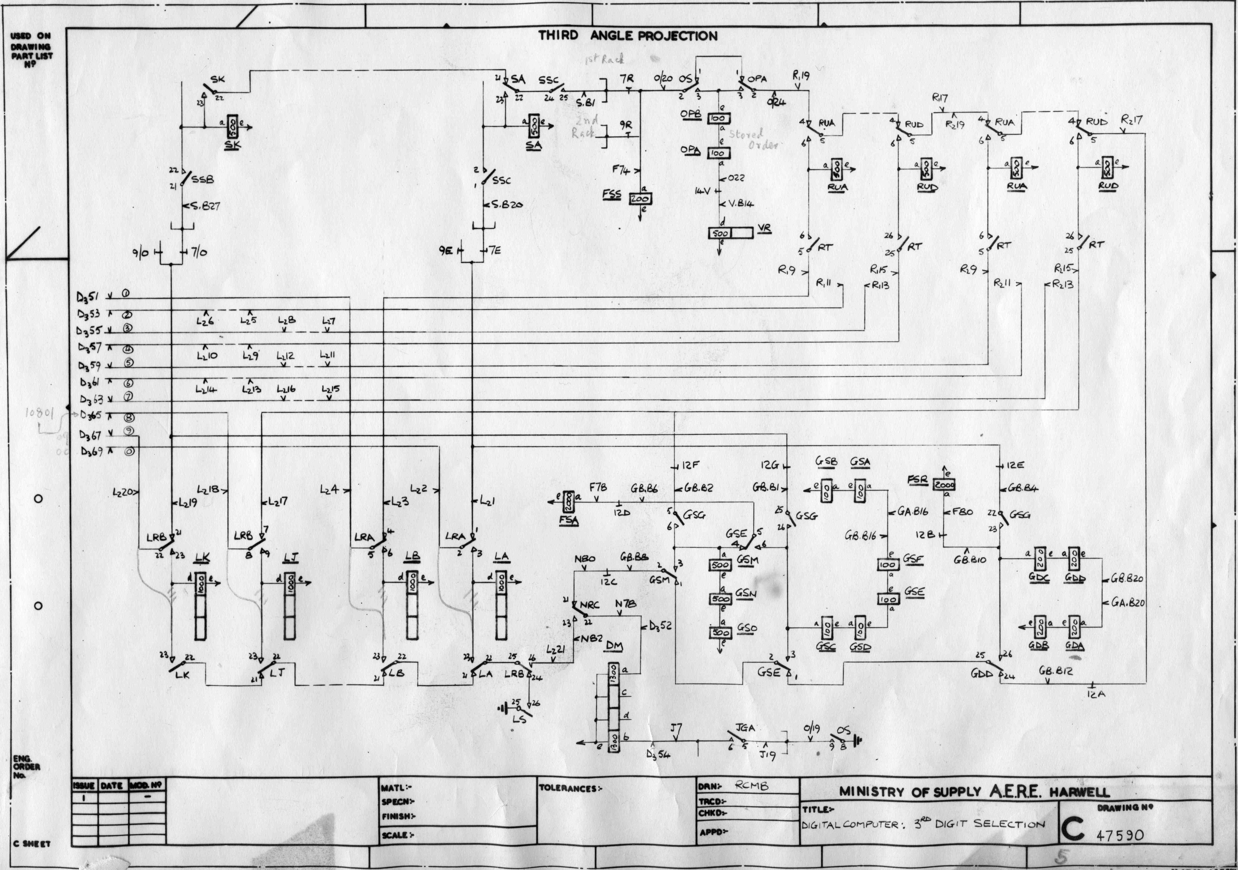
documentation/WITCH-schematics/jpgs/3rd Digit Selection - 47590.jpg
