prpplague/witch_dev/documentation/WITCH-schematics/jpgs/4th Digit Selection - 47589.jpg

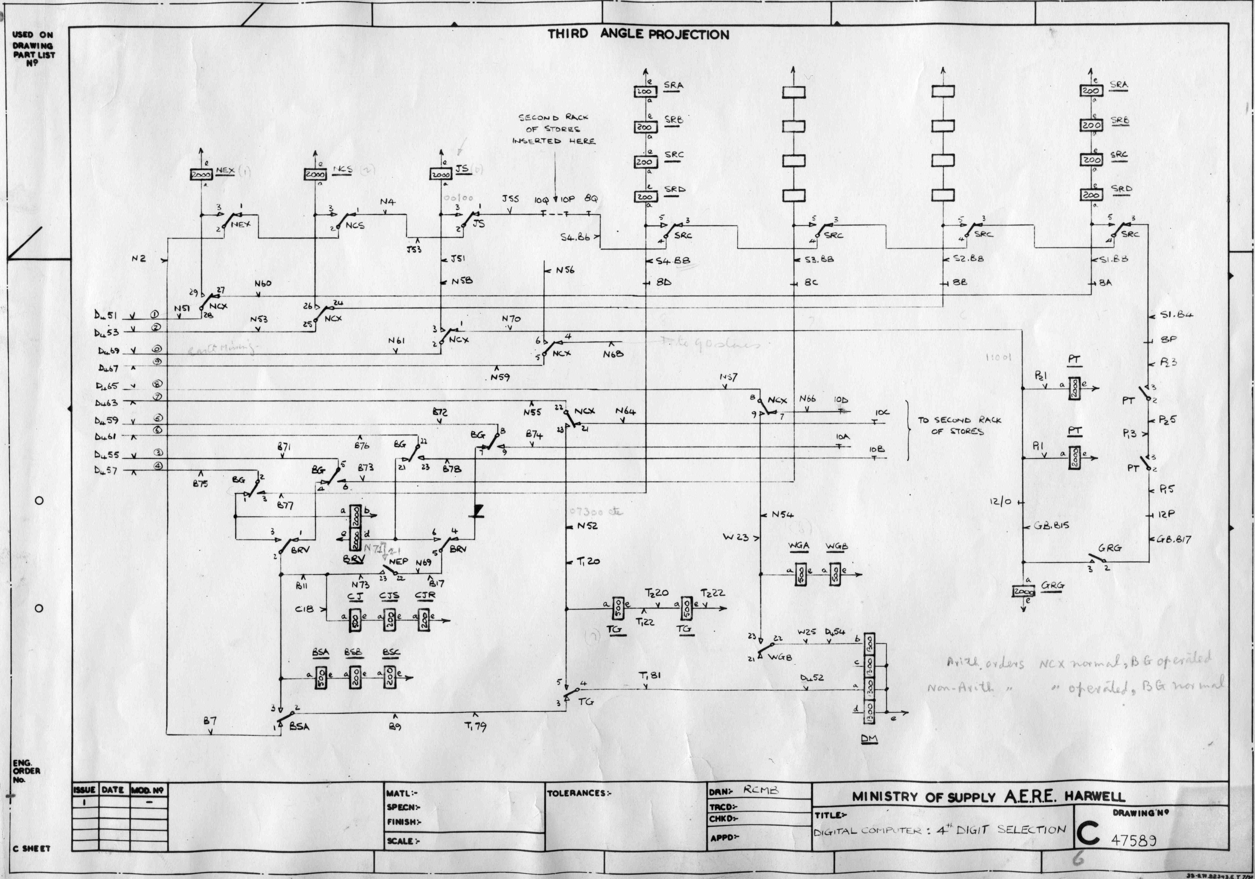
documentation/WITCH-schematics/jpgs/4th Digit Selection - 47589.jpg
