prpplague/witch_dev/documentation/WITCH-schematics/jpgs/5 Wire Input and Output - 47579.jpg

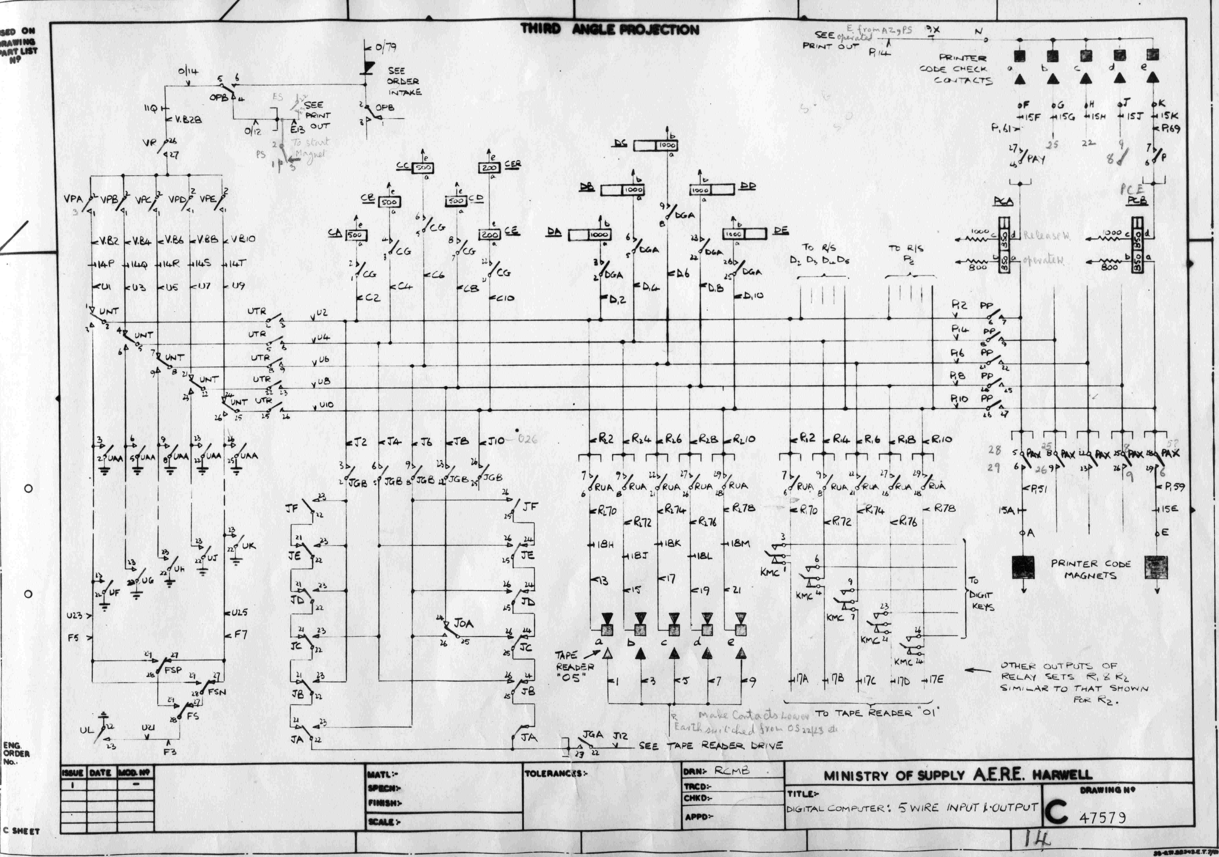
documentation/WITCH-schematics/jpgs/5 Wire Input and Output - 47579.jpg
