prpplague/witch_dev/documentation/WITCH-schematics/jpgs/5th Digit Selection - 47588.jpg

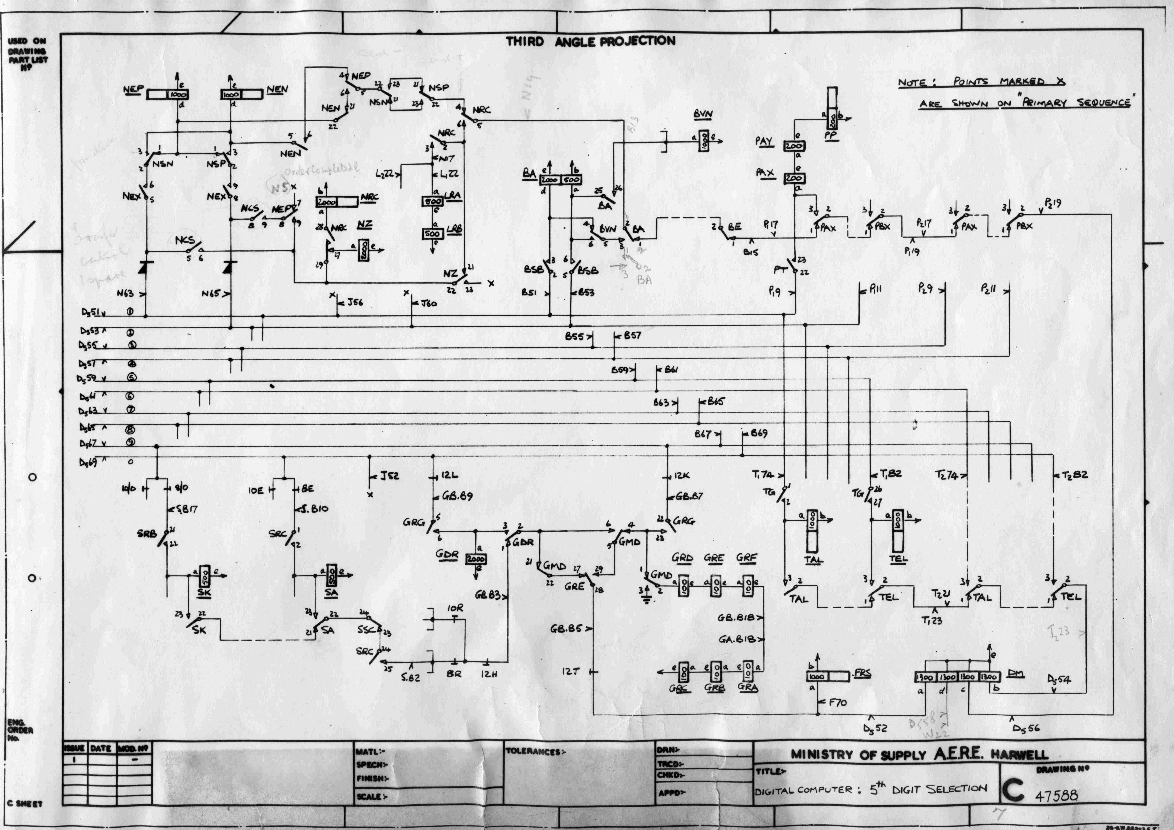
documentation/WITCH-schematics/jpgs/5th Digit Selection - 47588.jpg
