prpplague/witch_dev/documentation/WITCH-schematics/jpgs/Add and Subtract Control - 47585.jpg

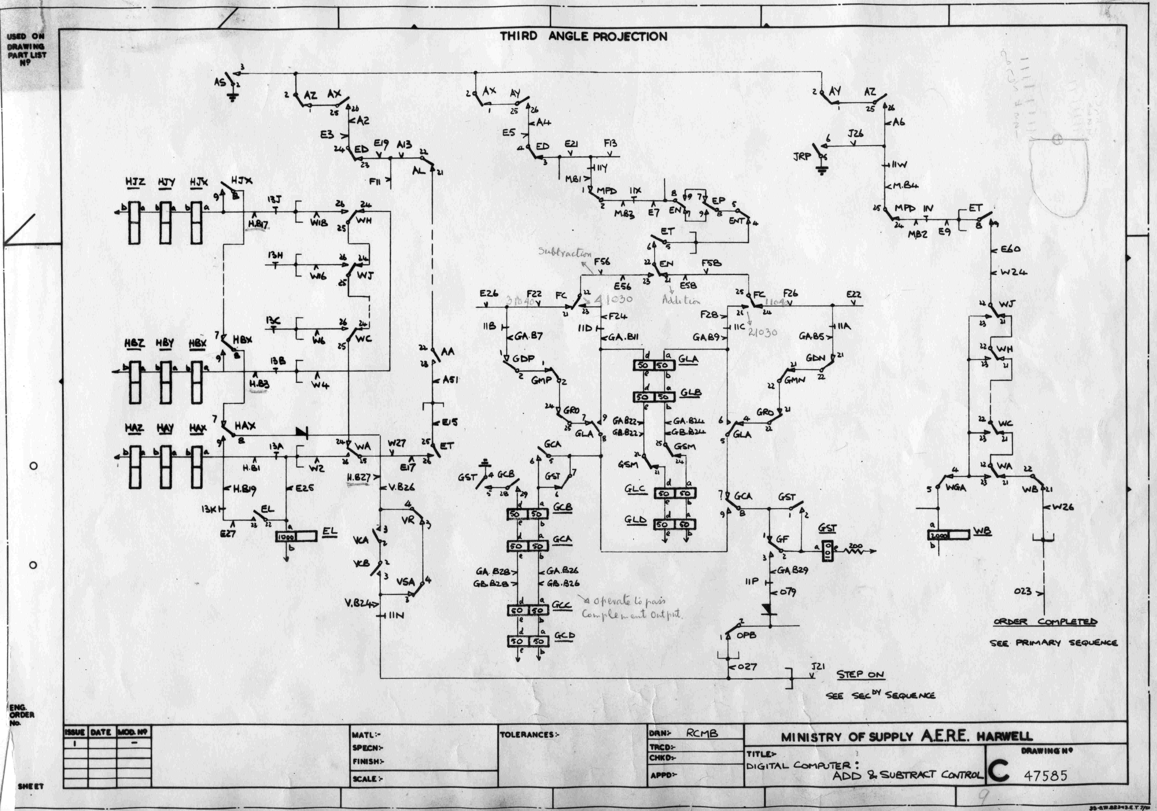
documentation/WITCH-schematics/jpgs/Add and Subtract Control - 47585.jpg
