prpplague/witch_dev/documentation/WITCH-schematics/jpgs/Alarm Circuit - 47578.jpg

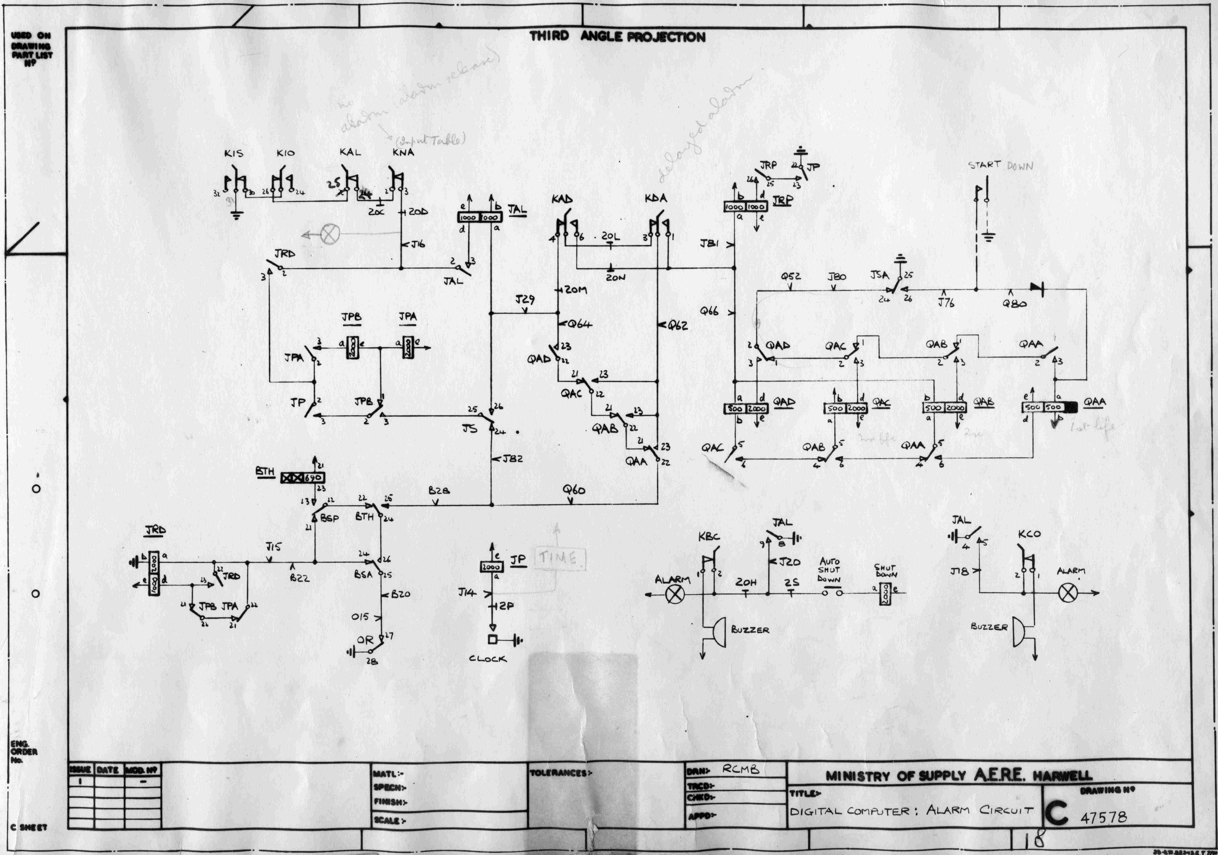
documentation/WITCH-schematics/jpgs/Alarm Circuit - 47578.jpg
