prpplague/witch_dev/documentation/WITCH-schematics/jpgs/Control Connectors - 48129.jpg

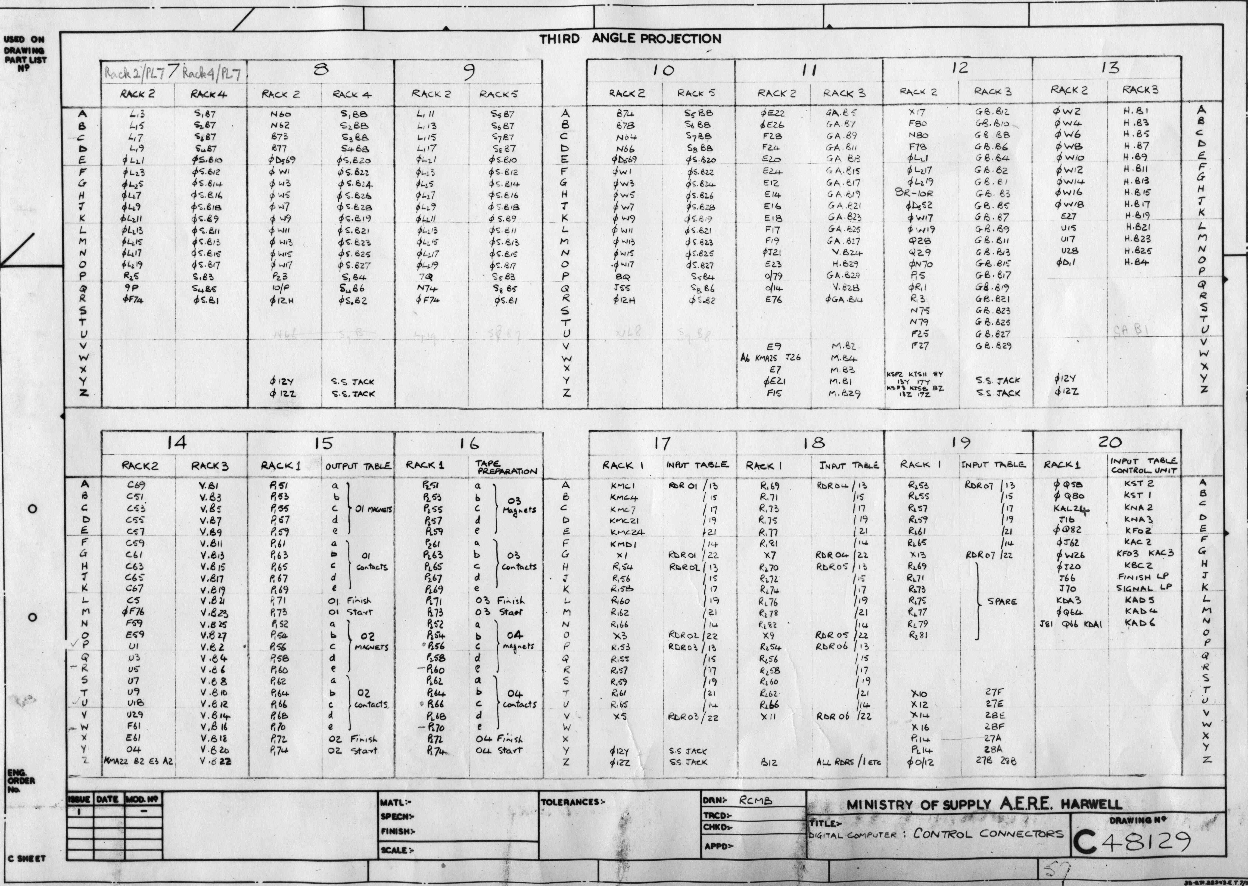
documentation/WITCH-schematics/jpgs/Control Connectors - 48129.jpg
