prpplague/witch_dev/documentation/WITCH-schematics/jpgs/Division Control - 47583.jpg

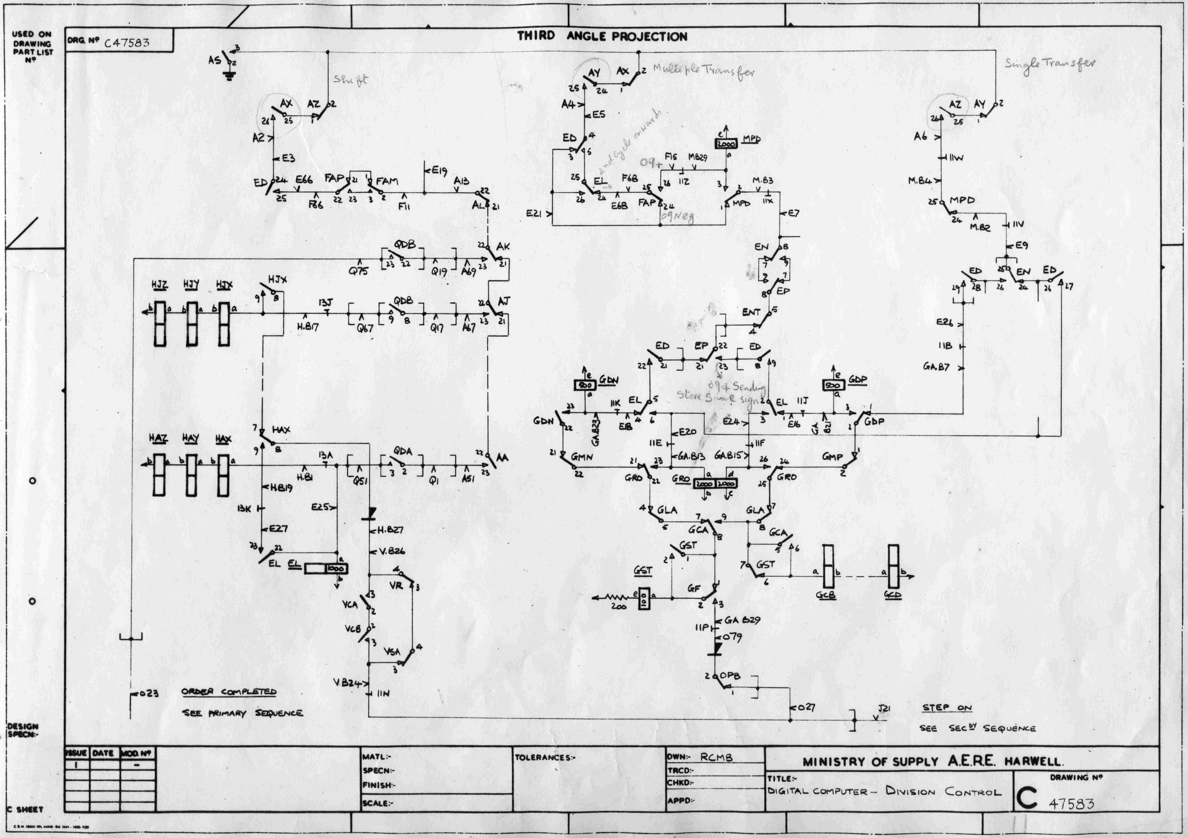
documentation/WITCH-schematics/jpgs/Division Control - 47583.jpg
