prpplague/witch_dev/documentation/WITCH-schematics/jpgs/Figure 5.jpg

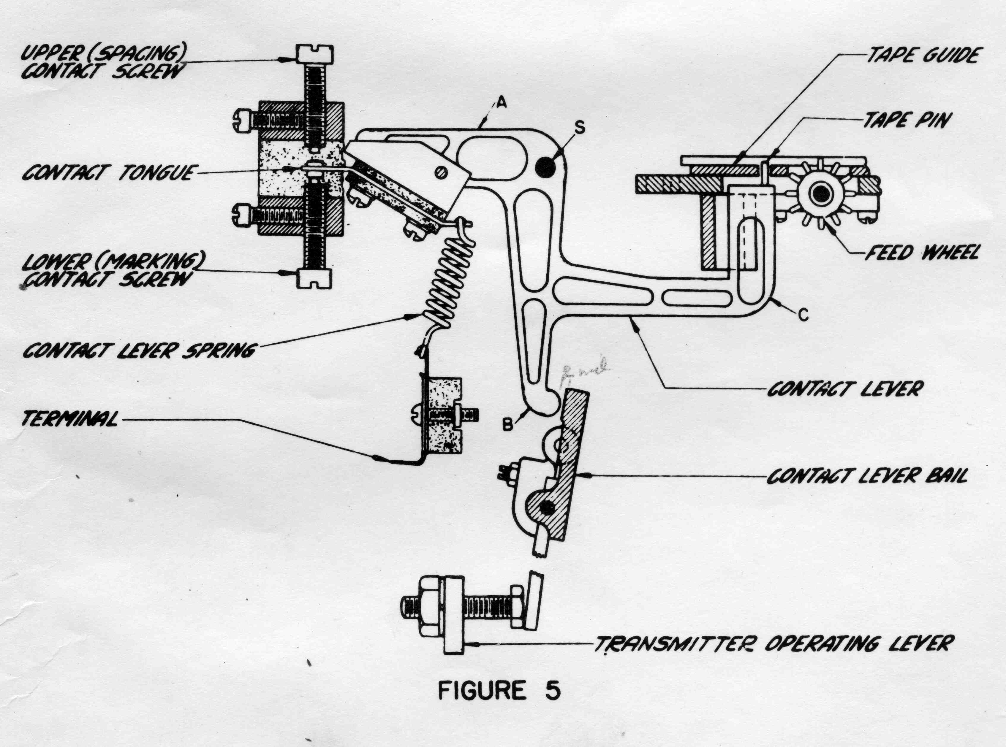
documentation/WITCH-schematics/jpgs/Figure 5.jpg
