prpplague/witch_dev/documentation/WITCH-schematics/jpgs/Figure 15.jpg

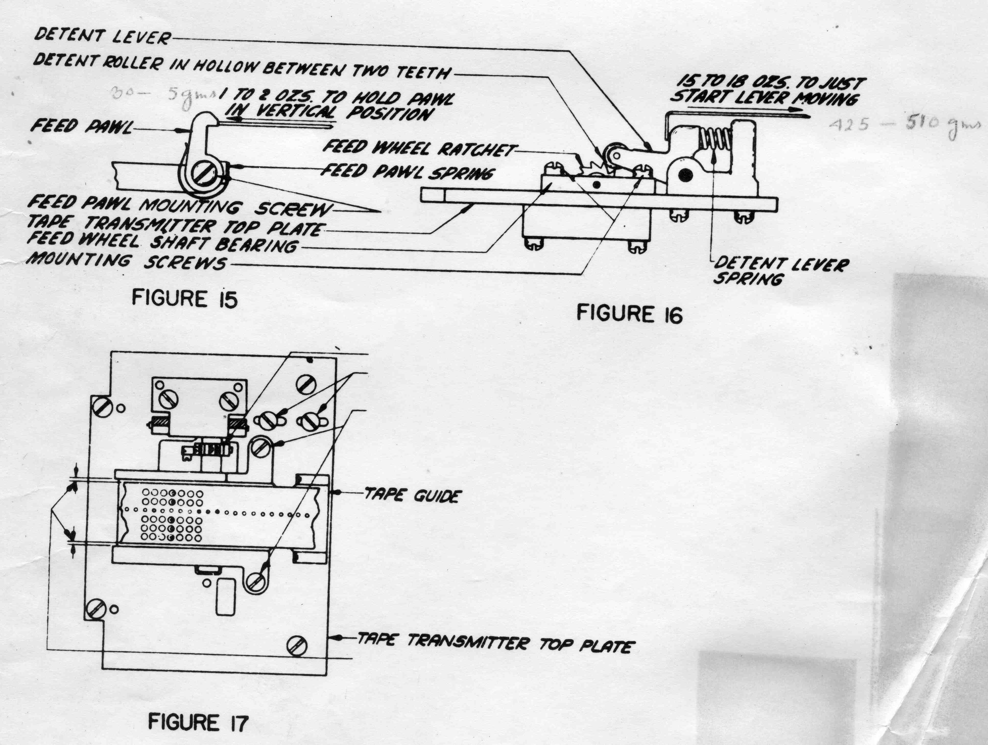
documentation/WITCH-schematics/jpgs/Figure 15.jpg
