prpplague/witch_dev/documentation/WITCH-schematics/jpgs/Input Table - 47550.jpg

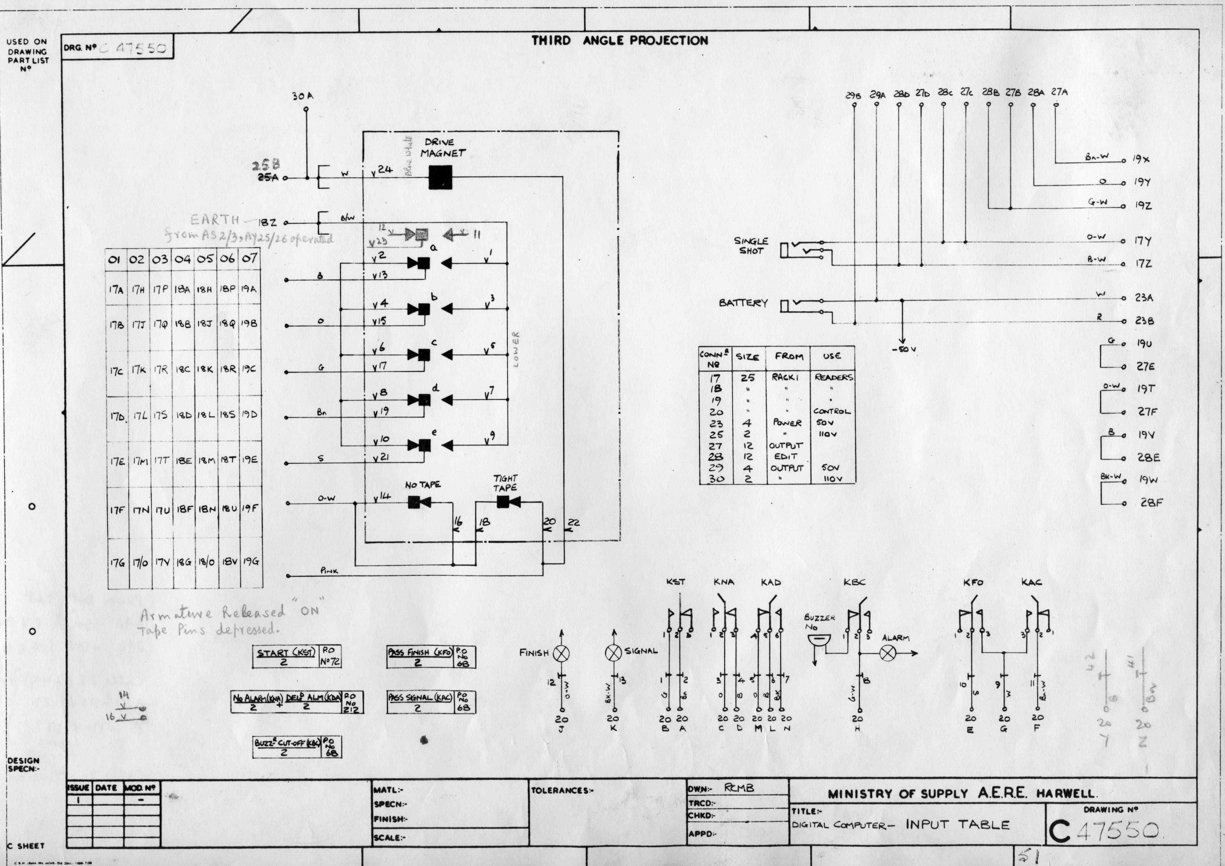
documentation/WITCH-schematics/jpgs/Input Table - 47550.jpg
