prpplague/witch_dev/documentation/WITCH-schematics/jpgs/Multiplication Control - 47584.jpg

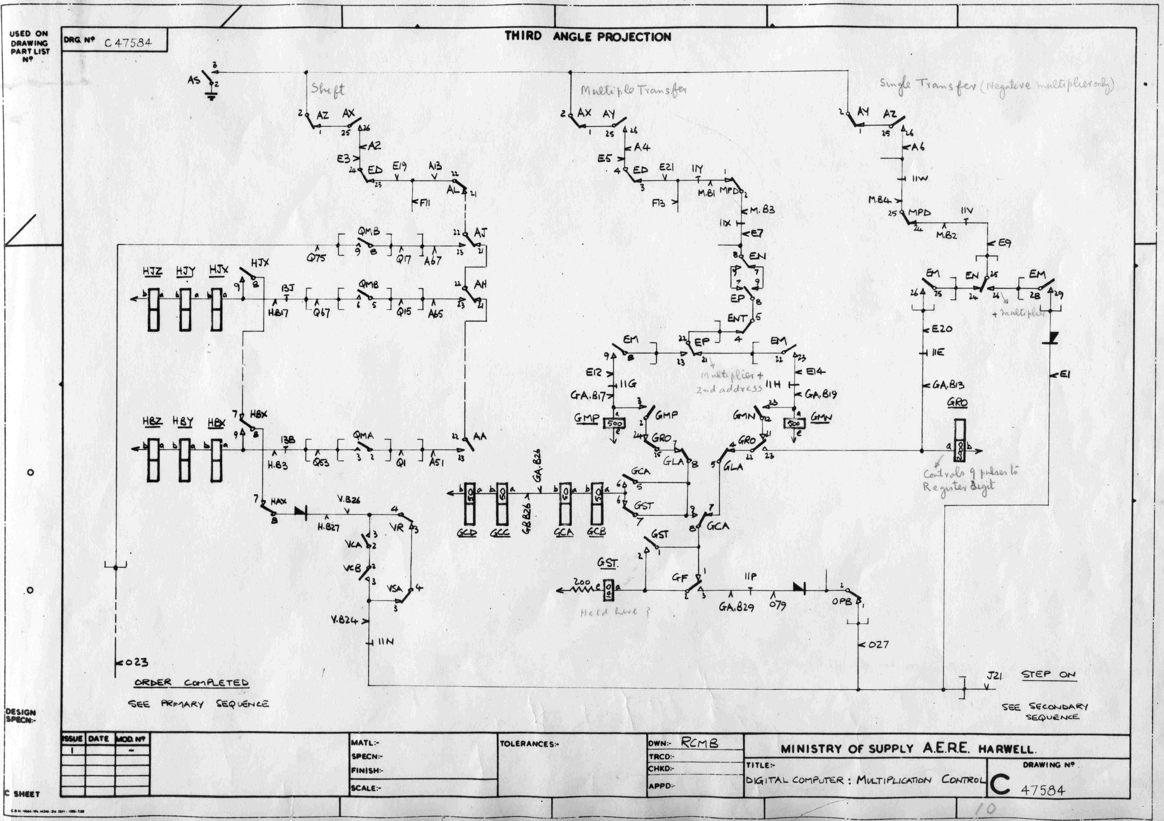
documentation/WITCH-schematics/jpgs/Multiplication Control - 47584.jpg
