prpplague/witch_dev/documentation/WITCH-schematics/jpgs/Output Units - 47549.jpg

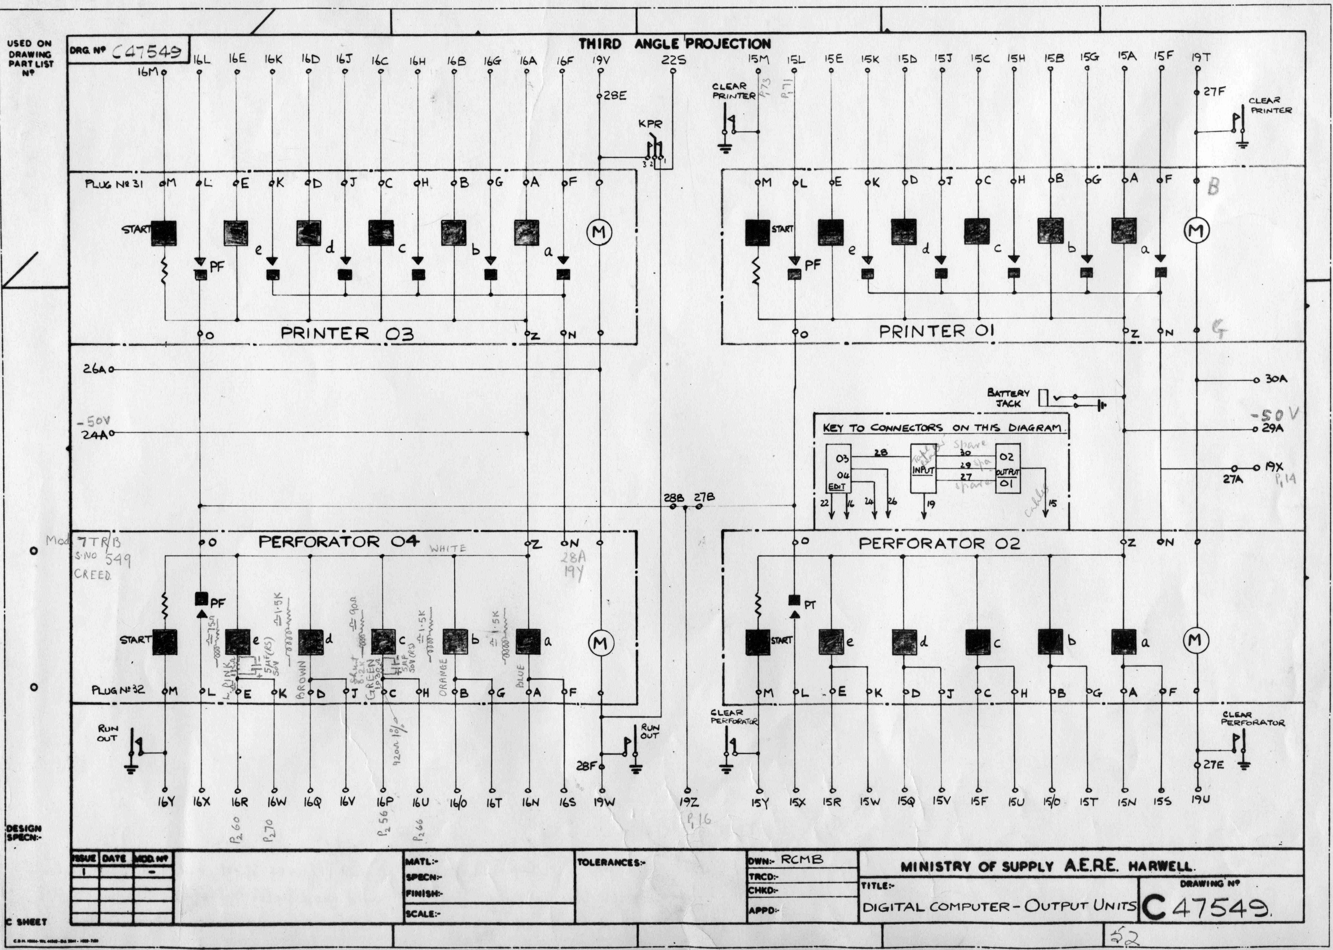
documentation/WITCH-schematics/jpgs/Output Units - 47549.jpg
