prpplague/witch_dev/documentation/WITCH-schematics/jpgs/Plug In Units - 47567.jpg

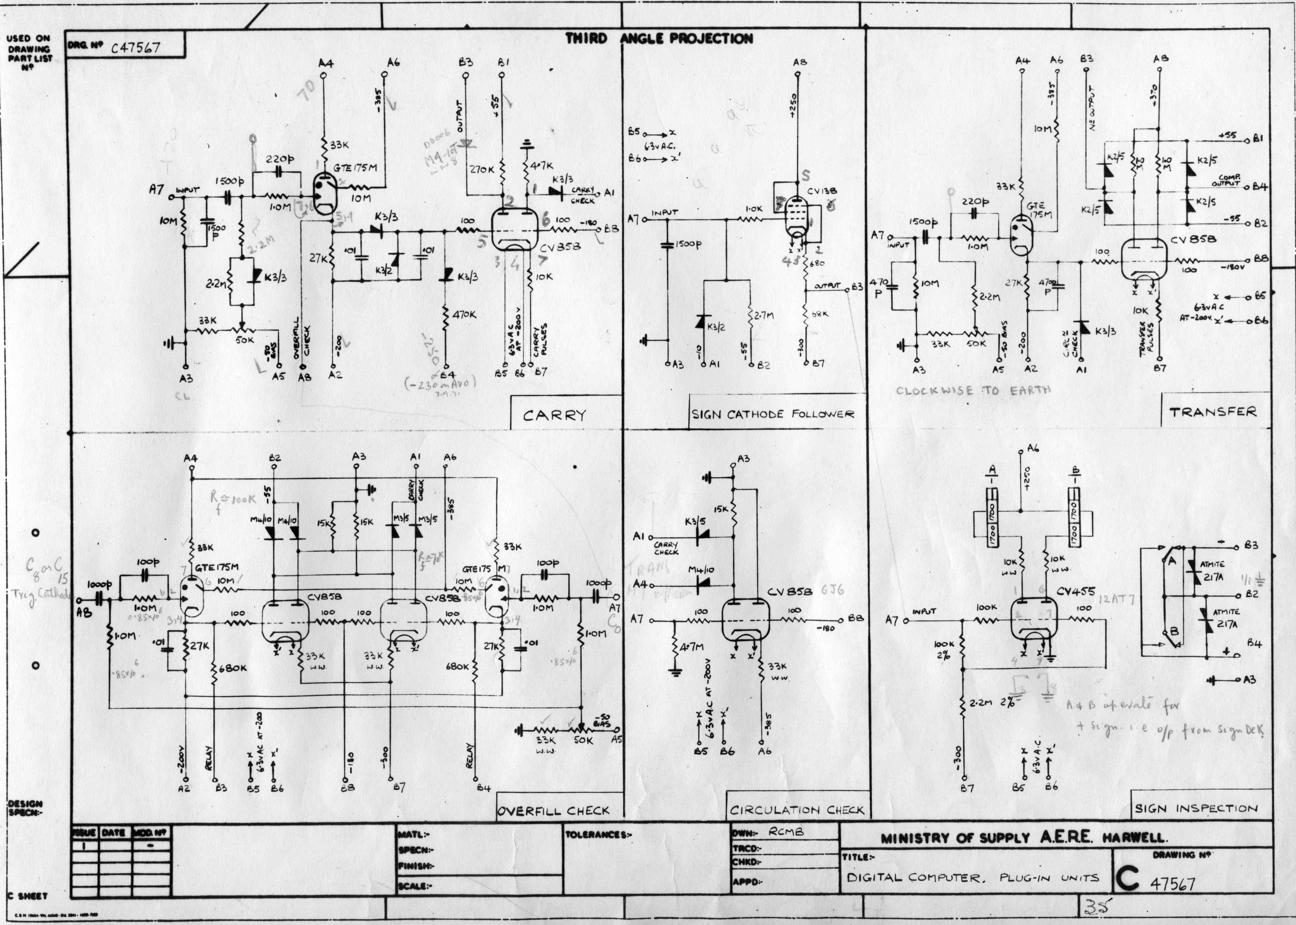
documentation/WITCH-schematics/jpgs/Plug In Units - 47567.jpg
