prpplague/witch_dev/documentation/WITCH-schematics/jpgs/Power Distribution Unit - 47545.jpg

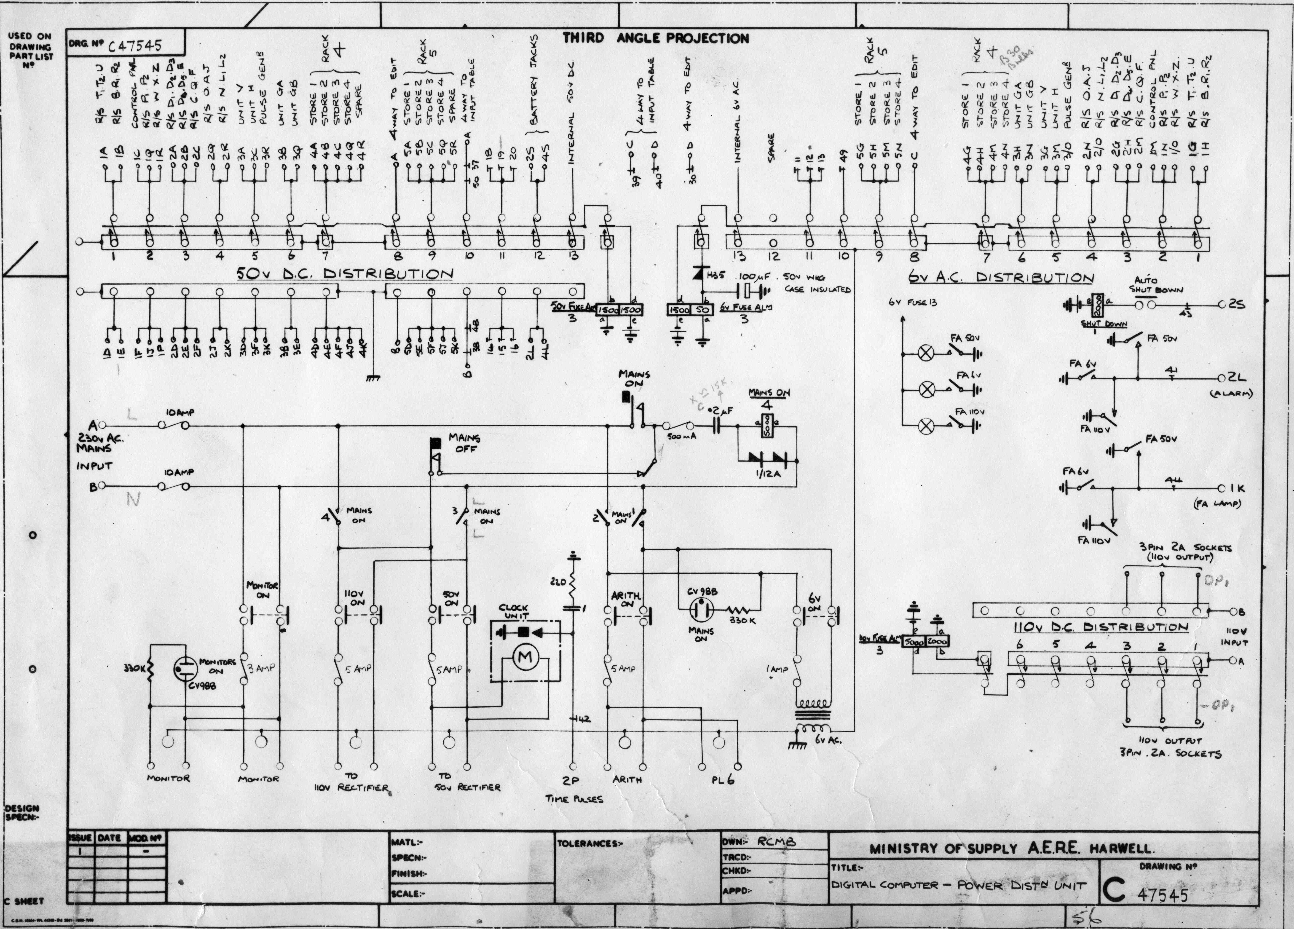
documentation/WITCH-schematics/jpgs/Power Distribution Unit - 47545.jpg
