prpplague/witch_dev/documentation/WITCH-schematics/jpgs/Pulse Generator Control - 47927.jpg

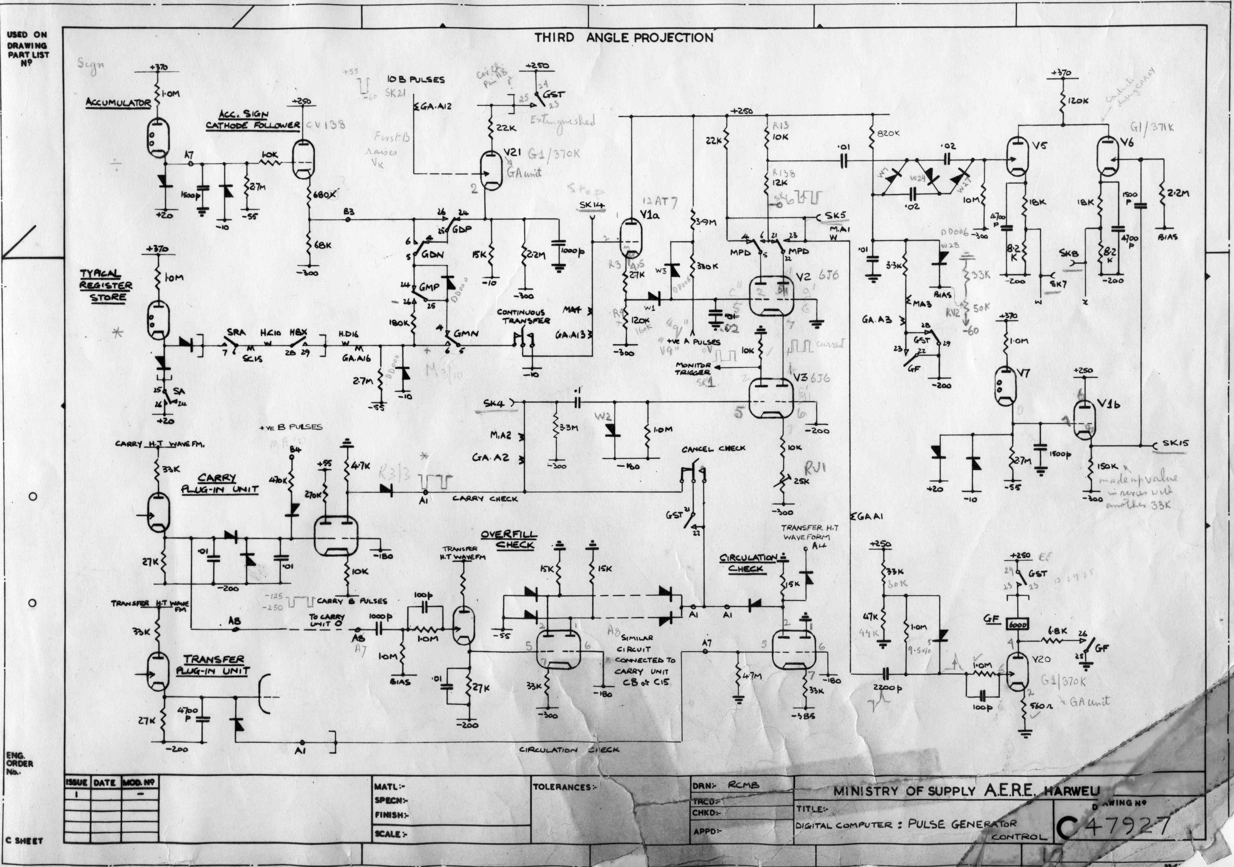
documentation/WITCH-schematics/jpgs/Pulse Generator Control - 47927.jpg
