prpplague/witch_dev/documentation/WITCH-schematics/jpgs/Rectifier Unit - 47547.jpg

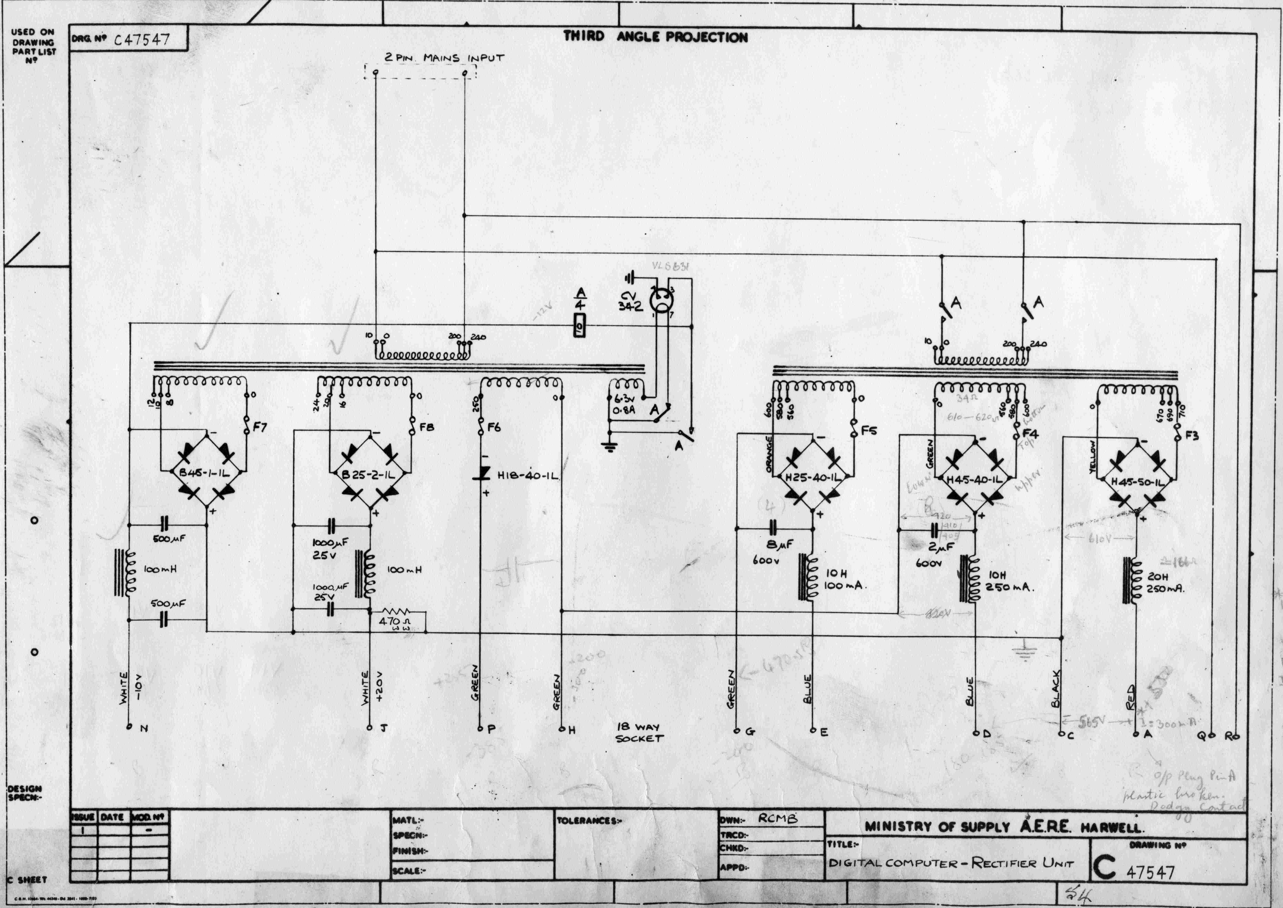
documentation/WITCH-schematics/jpgs/Rectifier Unit - 47547.jpg
