prpplague/witch_dev/documentation/WITCH-schematics/jpgs/Relay Set A - 47577.jpg

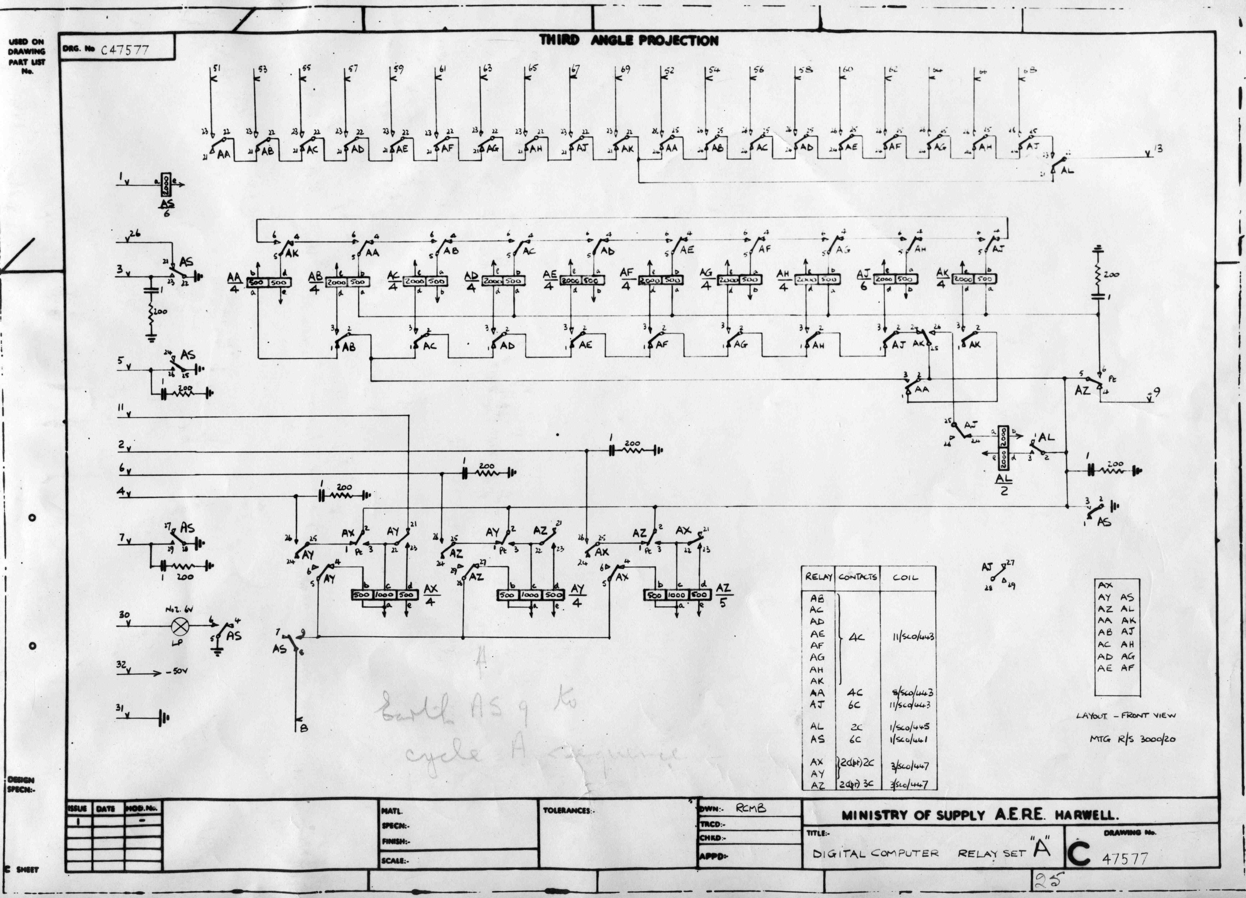
documentation/WITCH-schematics/jpgs/Relay Set A - 47577.jpg
