prpplague/witch_dev/documentation/WITCH-schematics/jpgs/Relay Set B - 47576.jpg

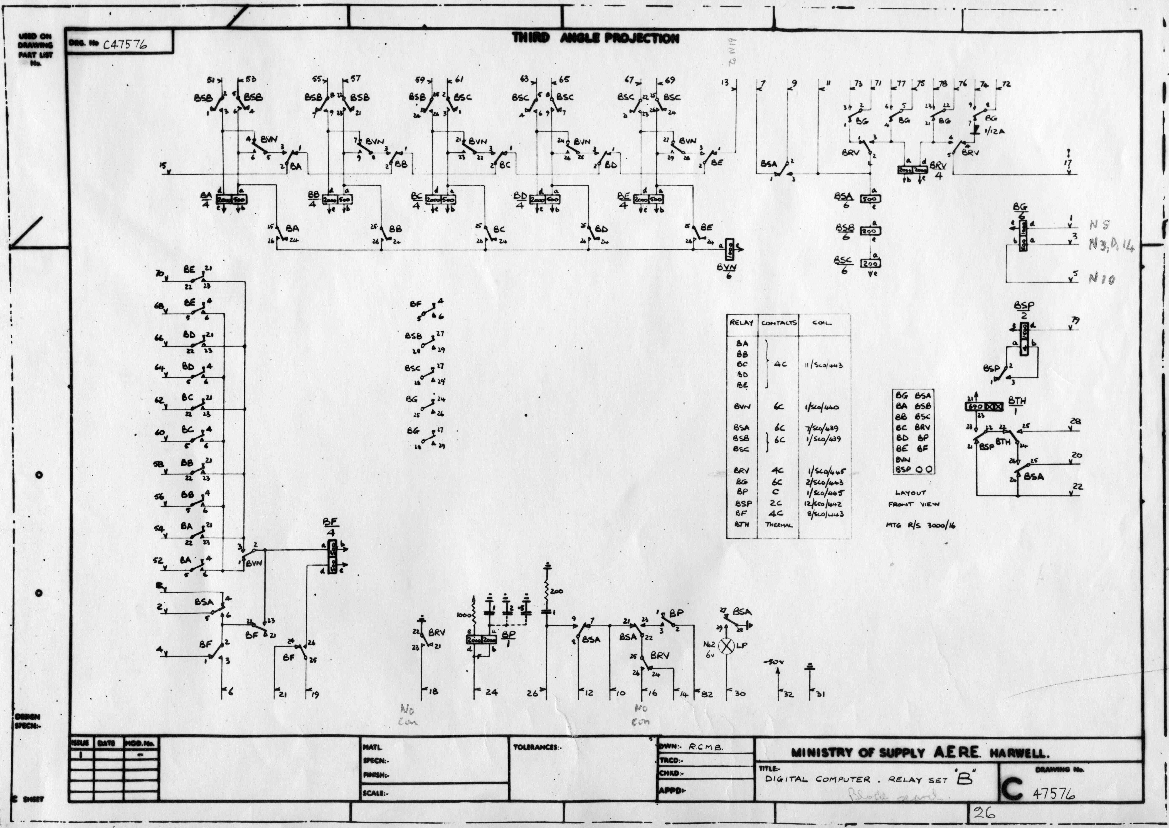
documentation/WITCH-schematics/jpgs/Relay Set B - 47576.jpg
