prpplague/witch_dev/documentation/WITCH-schematics/jpgs/Relay Set C - 47575.jpg

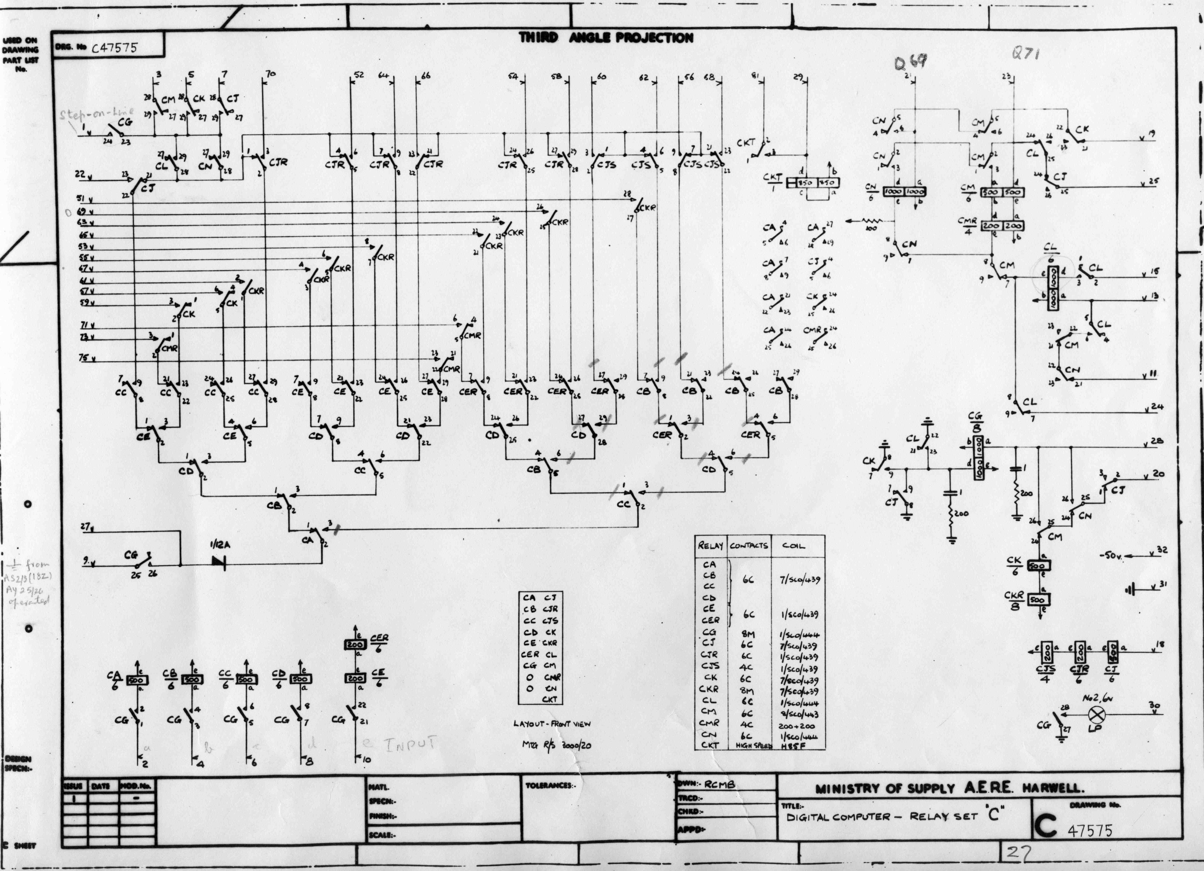
documentation/WITCH-schematics/jpgs/Relay Set C - 47575.jpg
