prpplague/witch_dev/documentation/WITCH-schematics/jpgs/Relay Set D - 47574.jpg

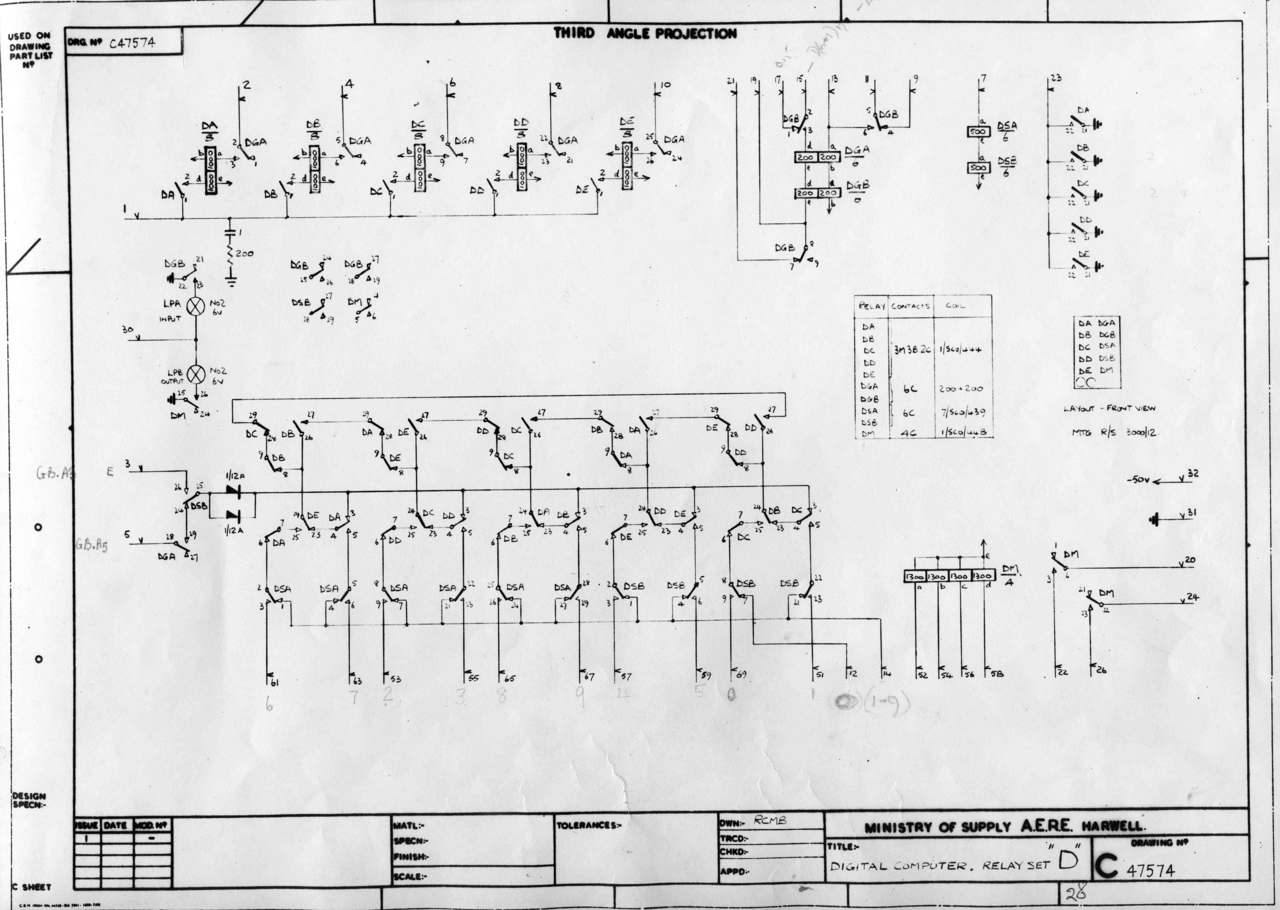
documentation/WITCH-schematics/jpgs/Relay Set D - 47574.jpg
