prpplague/witch_dev/documentation/WITCH-schematics/jpgs/Relay Set E - 47573.jpg

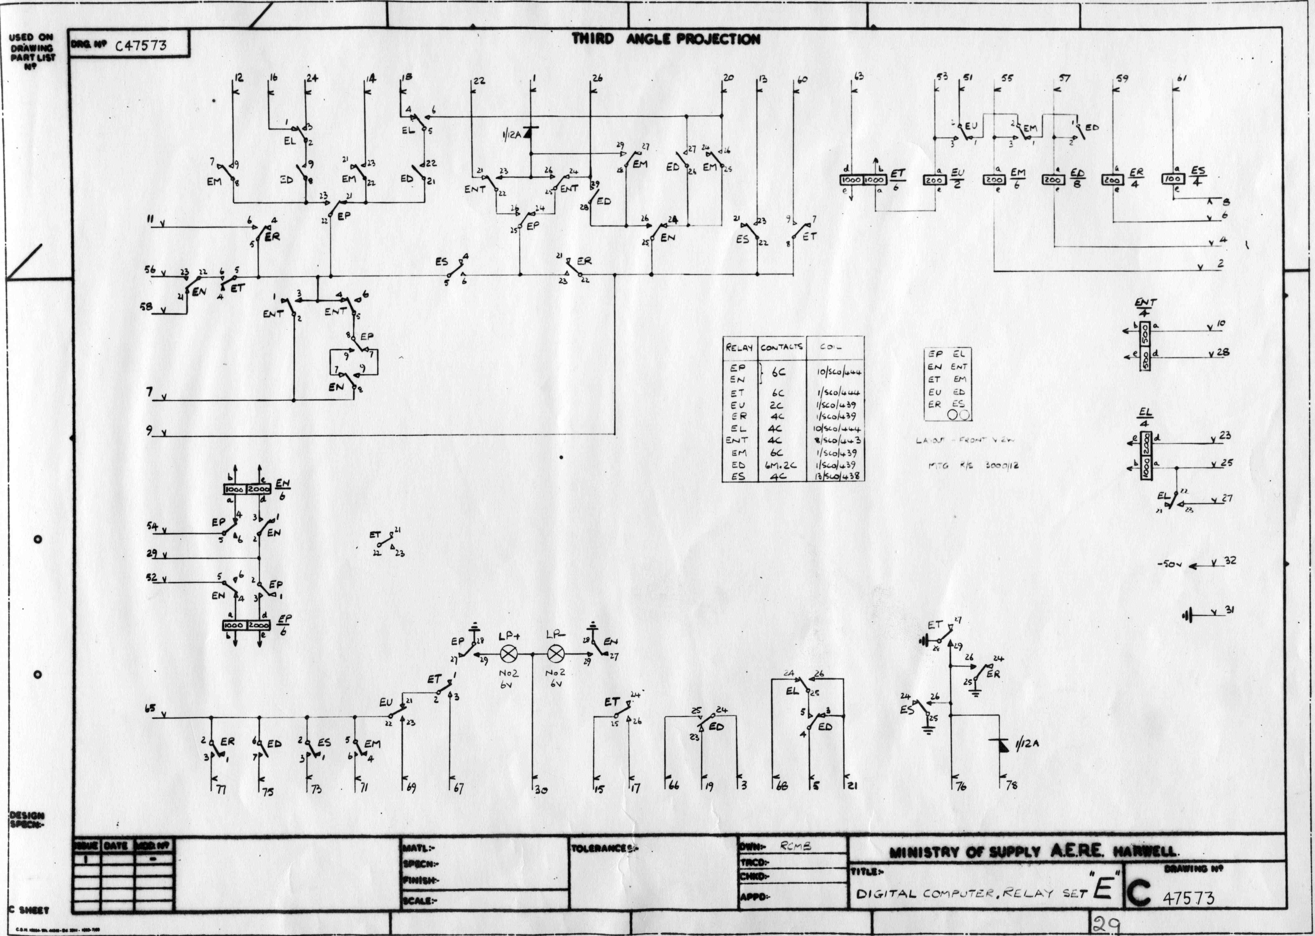
documentation/WITCH-schematics/jpgs/Relay Set E - 47573.jpg
