prpplague/witch_dev/documentation/WITCH-schematics/jpgs/Relay Set J - 47565.jpg

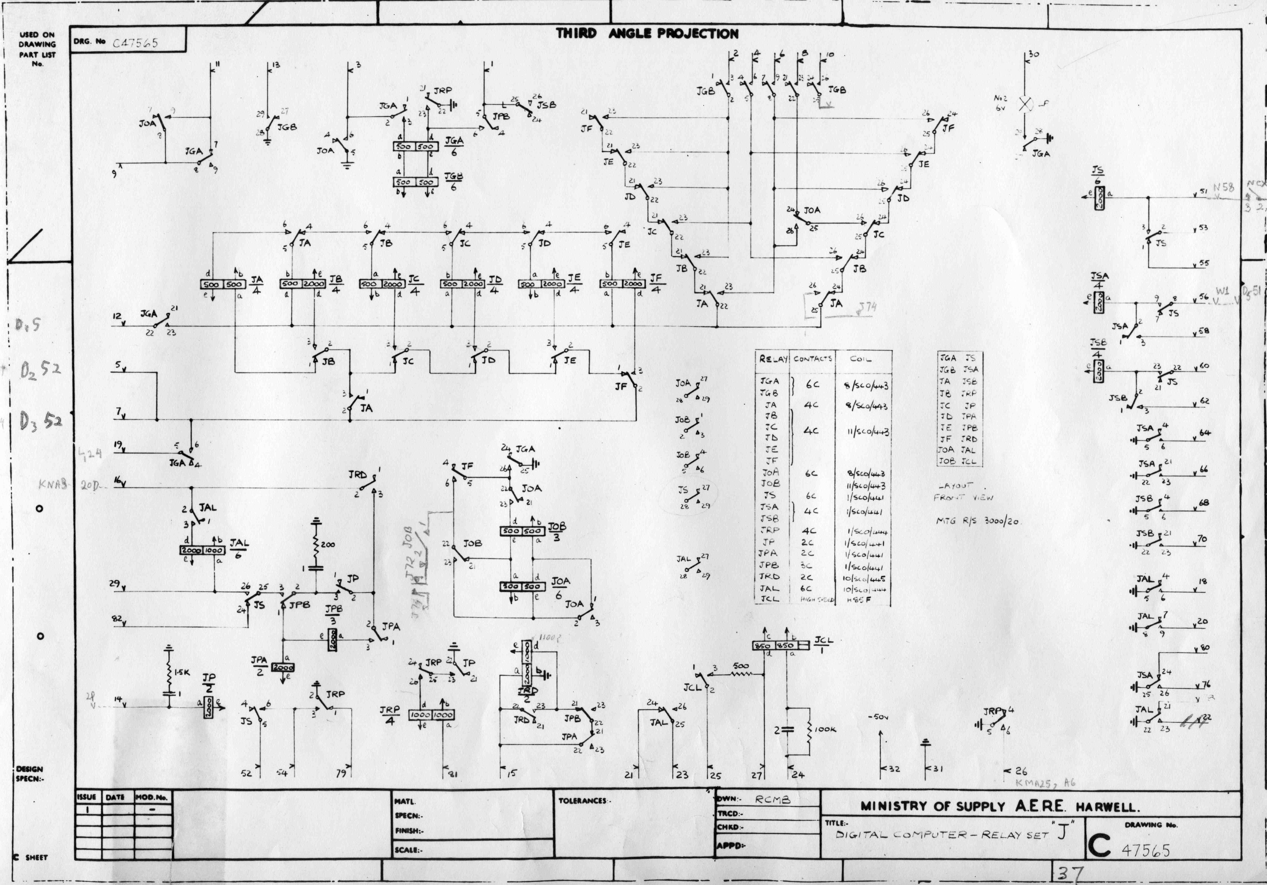
documentation/WITCH-schematics/jpgs/Relay Set J - 47565.jpg
