prpplague/witch_dev/documentation/WITCH-schematics/jpgs/Relay Set L - 47564.jpg

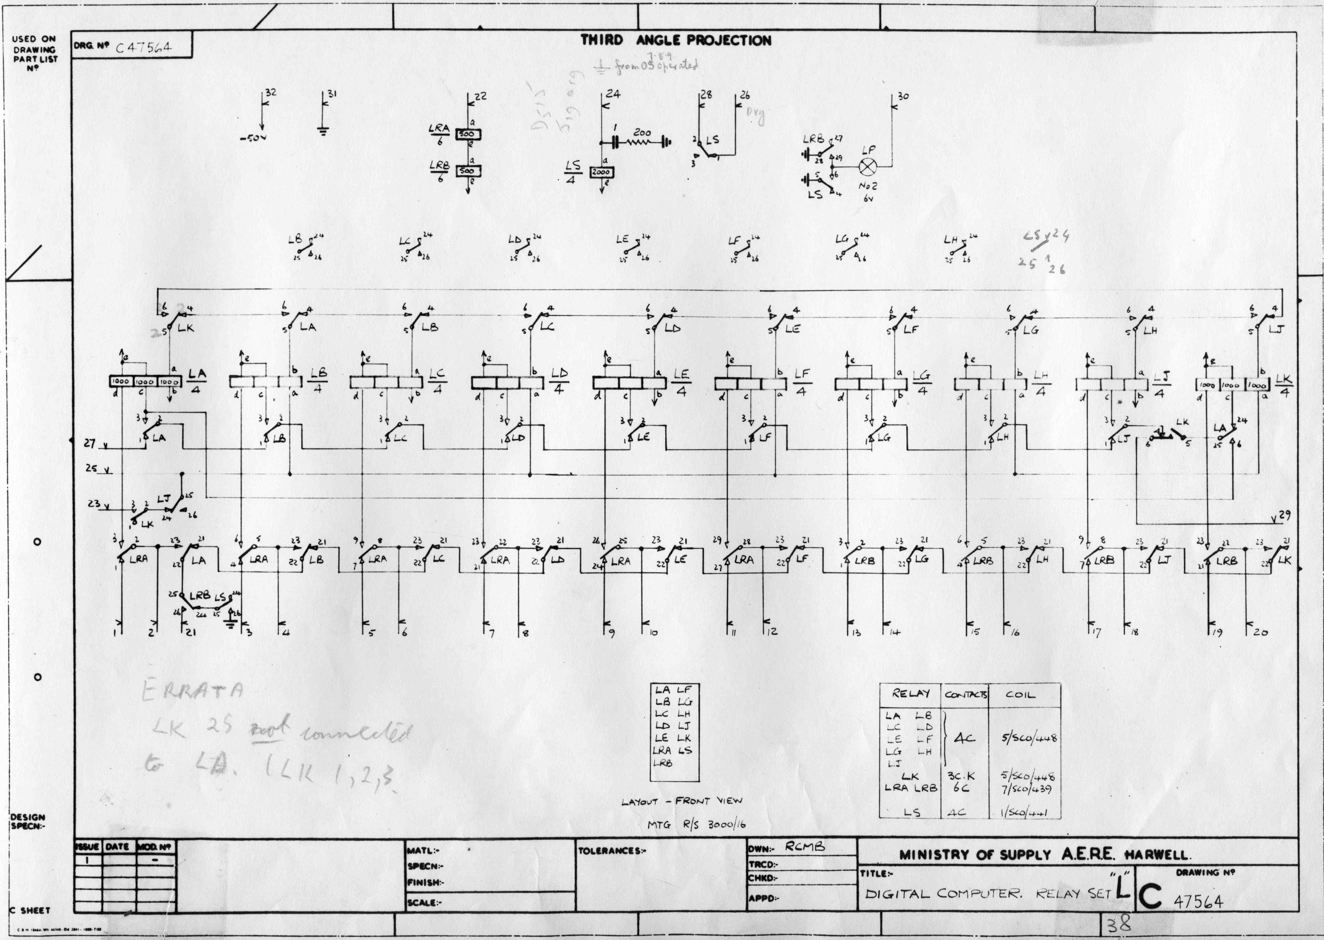
documentation/WITCH-schematics/jpgs/Relay Set L - 47564.jpg
