prpplague/witch_dev/documentation/WITCH-schematics/jpgs/Relay Set N - 47561.jpg

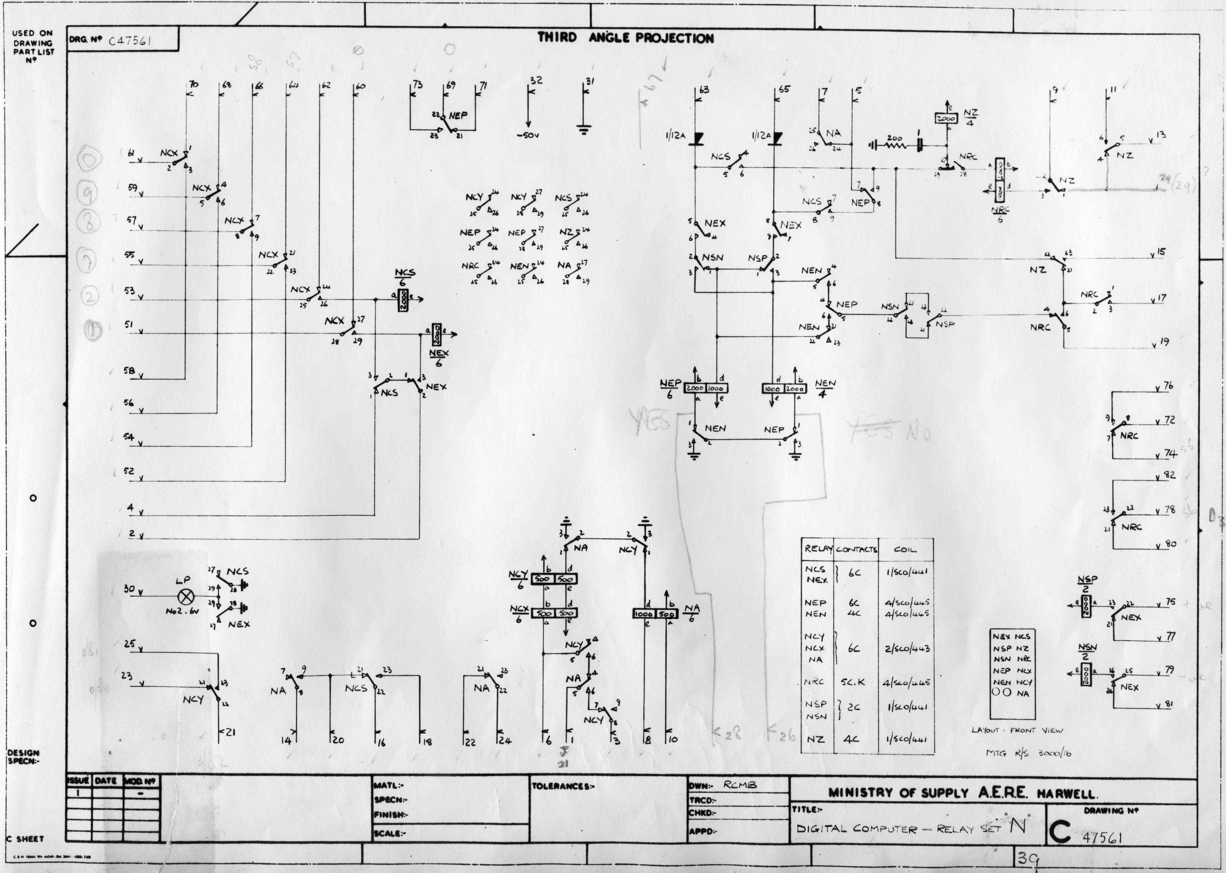
documentation/WITCH-schematics/jpgs/Relay Set N - 47561.jpg
