prpplague/witch_dev/documentation/WITCH-schematics/jpgs/Relay Set O - 47560.jpg

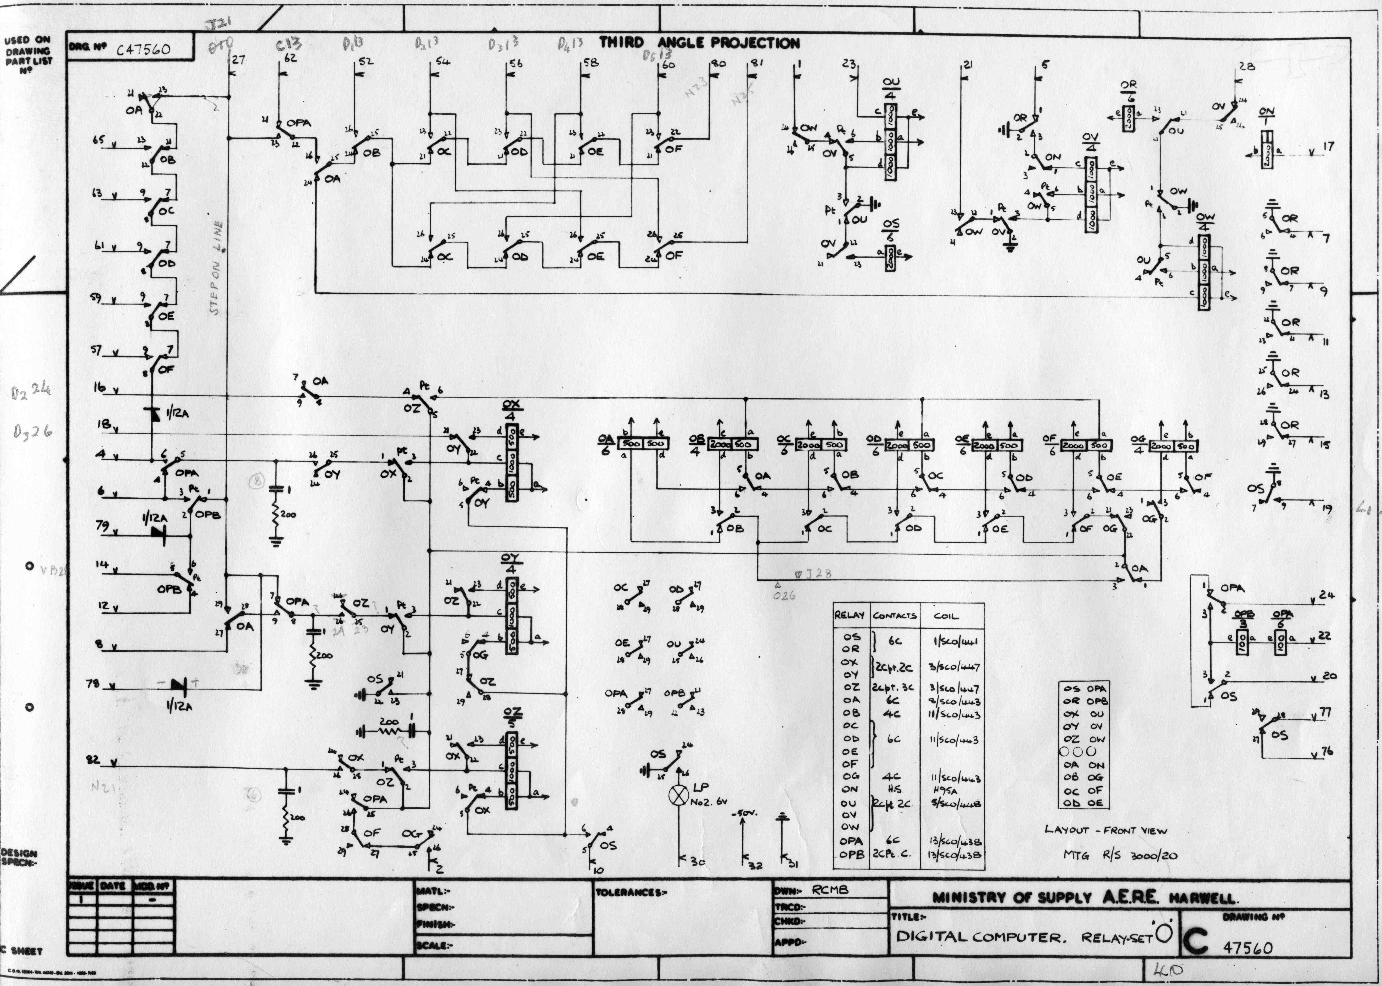
documentation/WITCH-schematics/jpgs/Relay Set O - 47560.jpg
