prpplague/witch_dev/documentation/WITCH-schematics/jpgs/Relay Set P - 47559.jpg

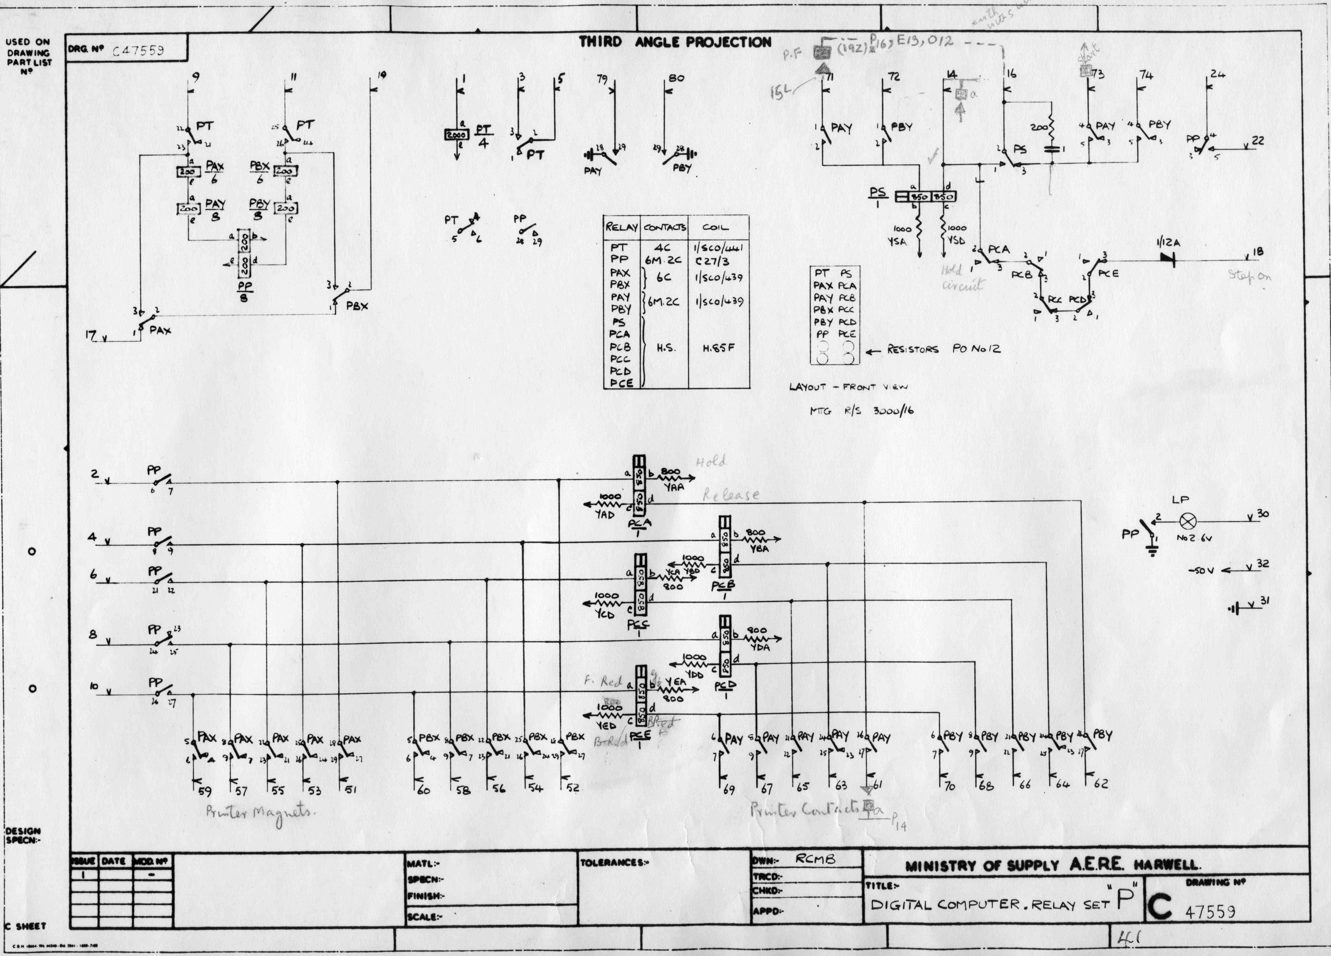
documentation/WITCH-schematics/jpgs/Relay Set P - 47559.jpg
