prpplague/witch_dev/documentation/WITCH-schematics/jpgs/Relay Set Q - 47558.jpg

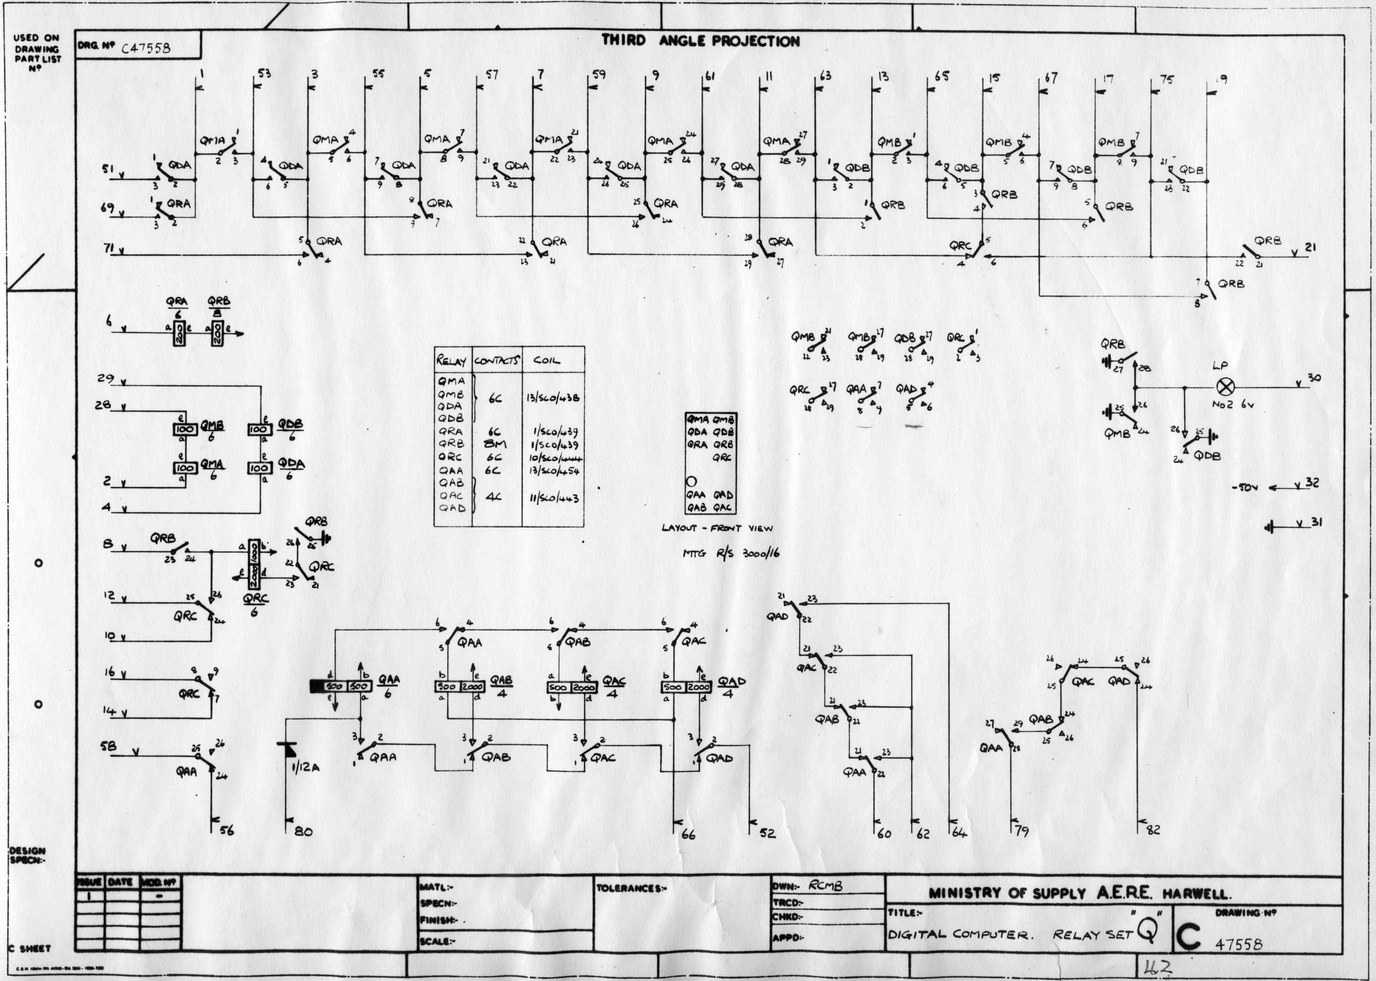
documentation/WITCH-schematics/jpgs/Relay Set Q - 47558.jpg
