prpplague/witch_dev/documentation/WITCH-schematics/jpgs/Relay Set R - 48301.jpg

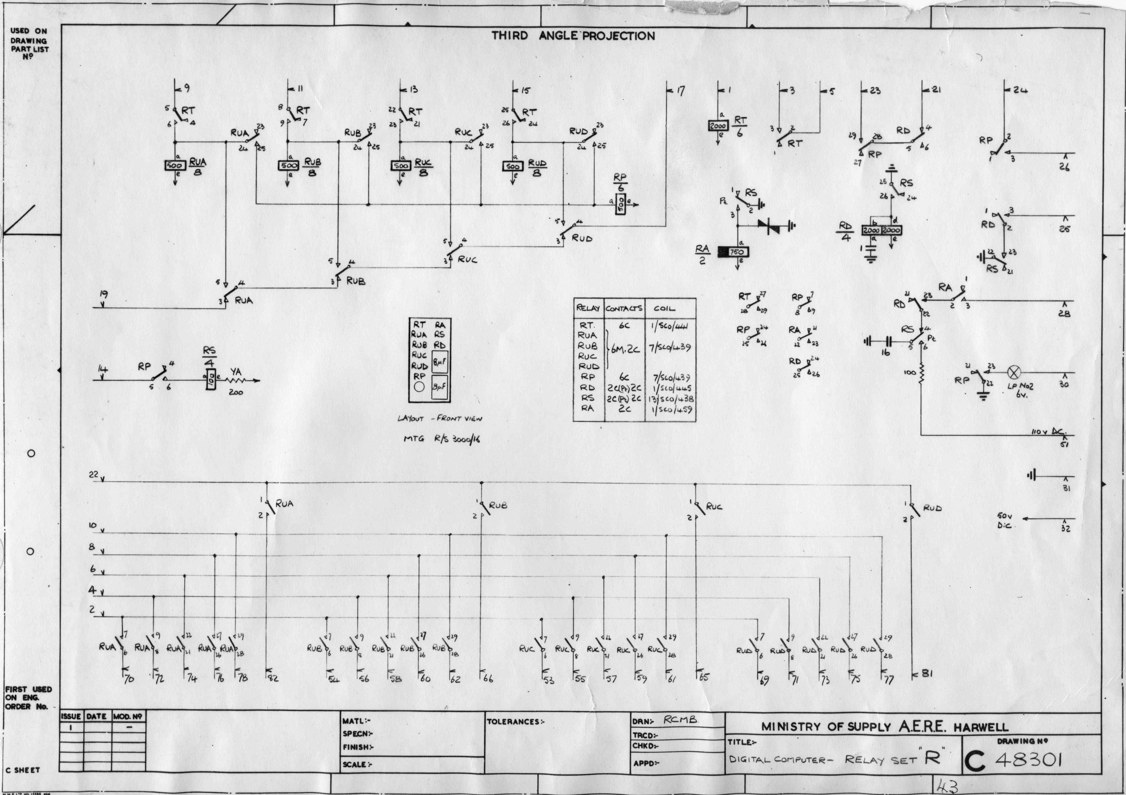
documentation/WITCH-schematics/jpgs/Relay Set R - 48301.jpg
