prpplague/witch_dev/documentation/WITCH-schematics/jpgs/Relay Set T - 47555.jpg

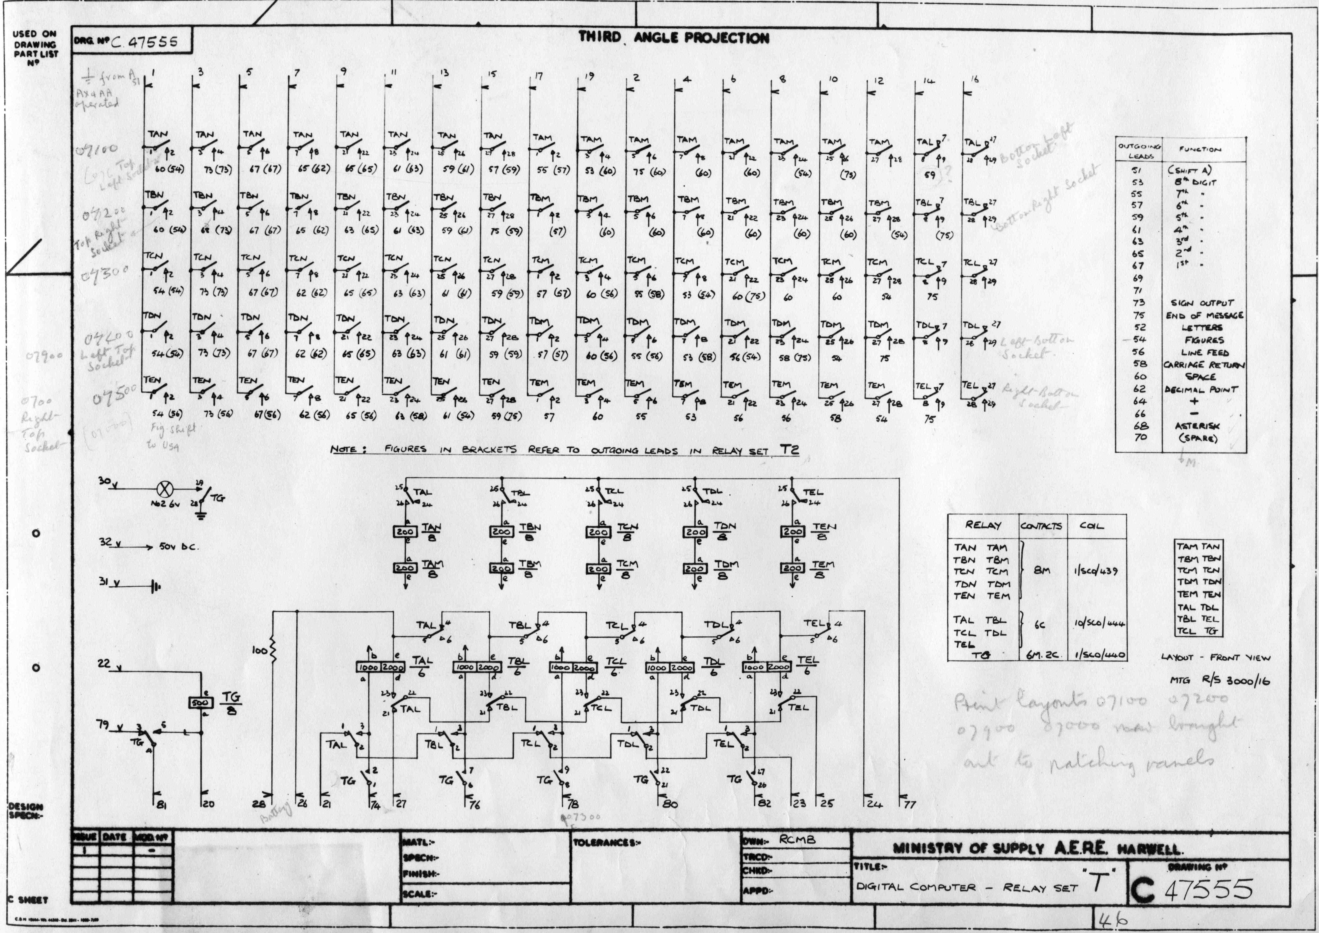
documentation/WITCH-schematics/jpgs/Relay Set T - 47555.jpg
