prpplague/witch_dev/documentation/WITCH-schematics/jpgs/Relay Set U - 47554.jpg

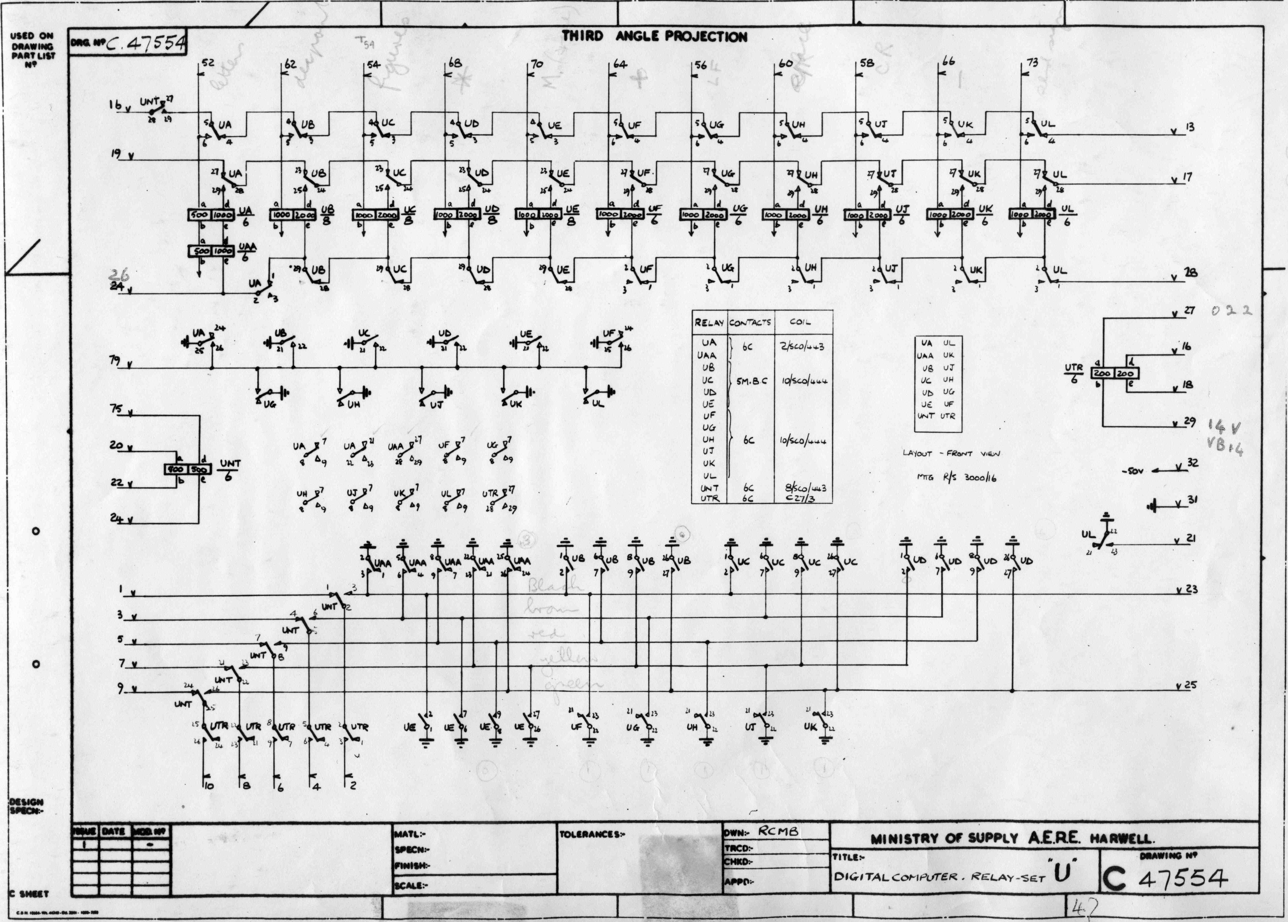
documentation/WITCH-schematics/jpgs/Relay Set U - 47554.jpg
