prpplague/witch_dev/documentation/WITCH-schematics/jpgs/Relay Set V - 47553.jpg

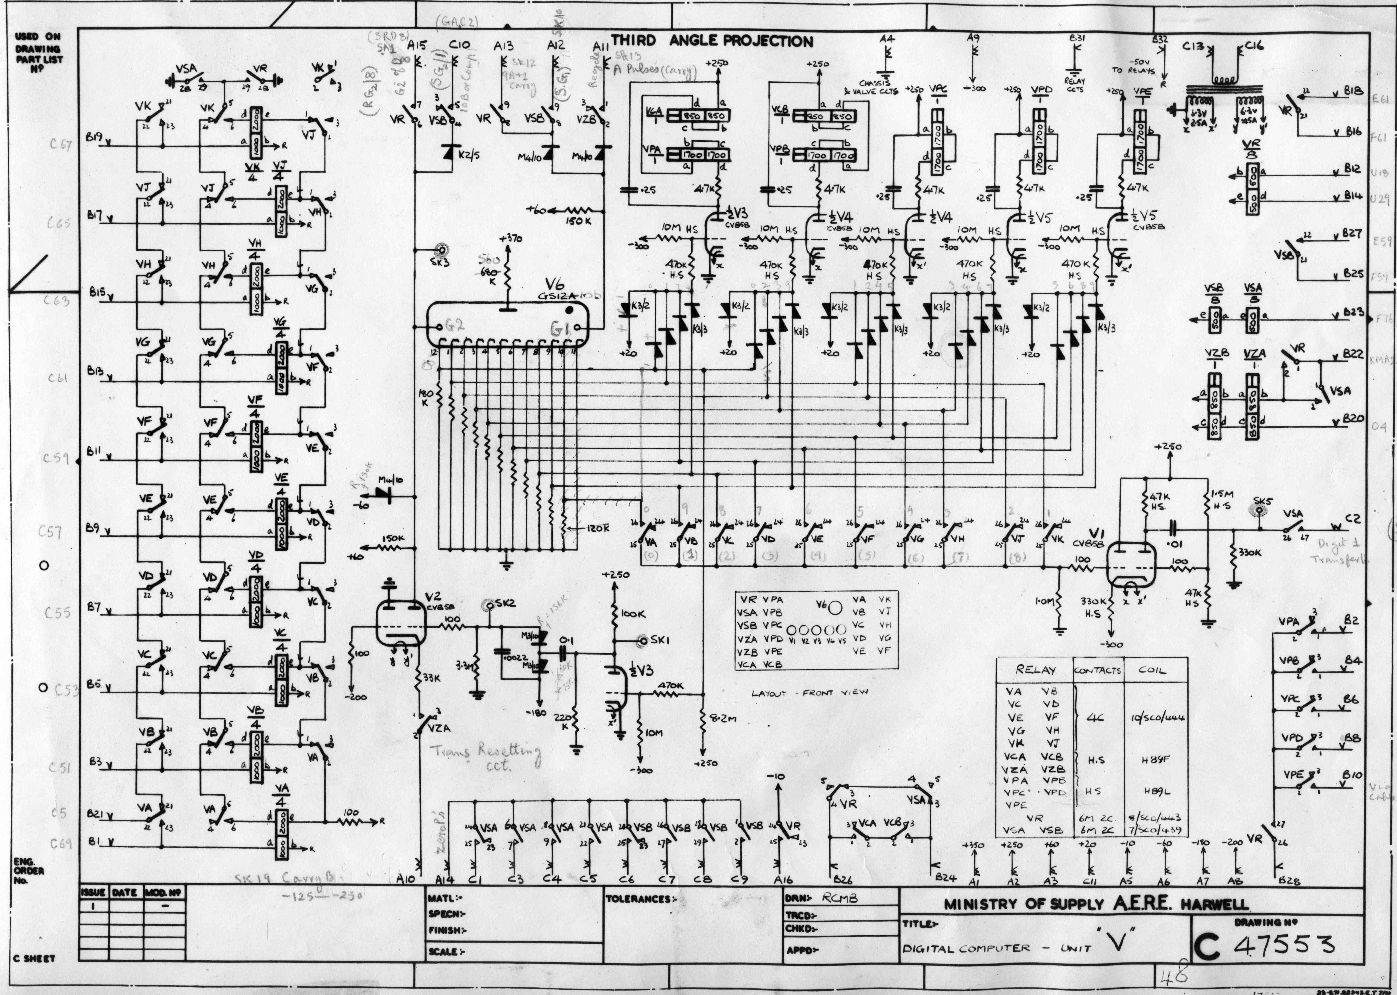
documentation/WITCH-schematics/jpgs/Relay Set V - 47553.jpg
