prpplague/witch_dev/documentation/WITCH-schematics/jpgs/Relay Set W - 47552.jpg

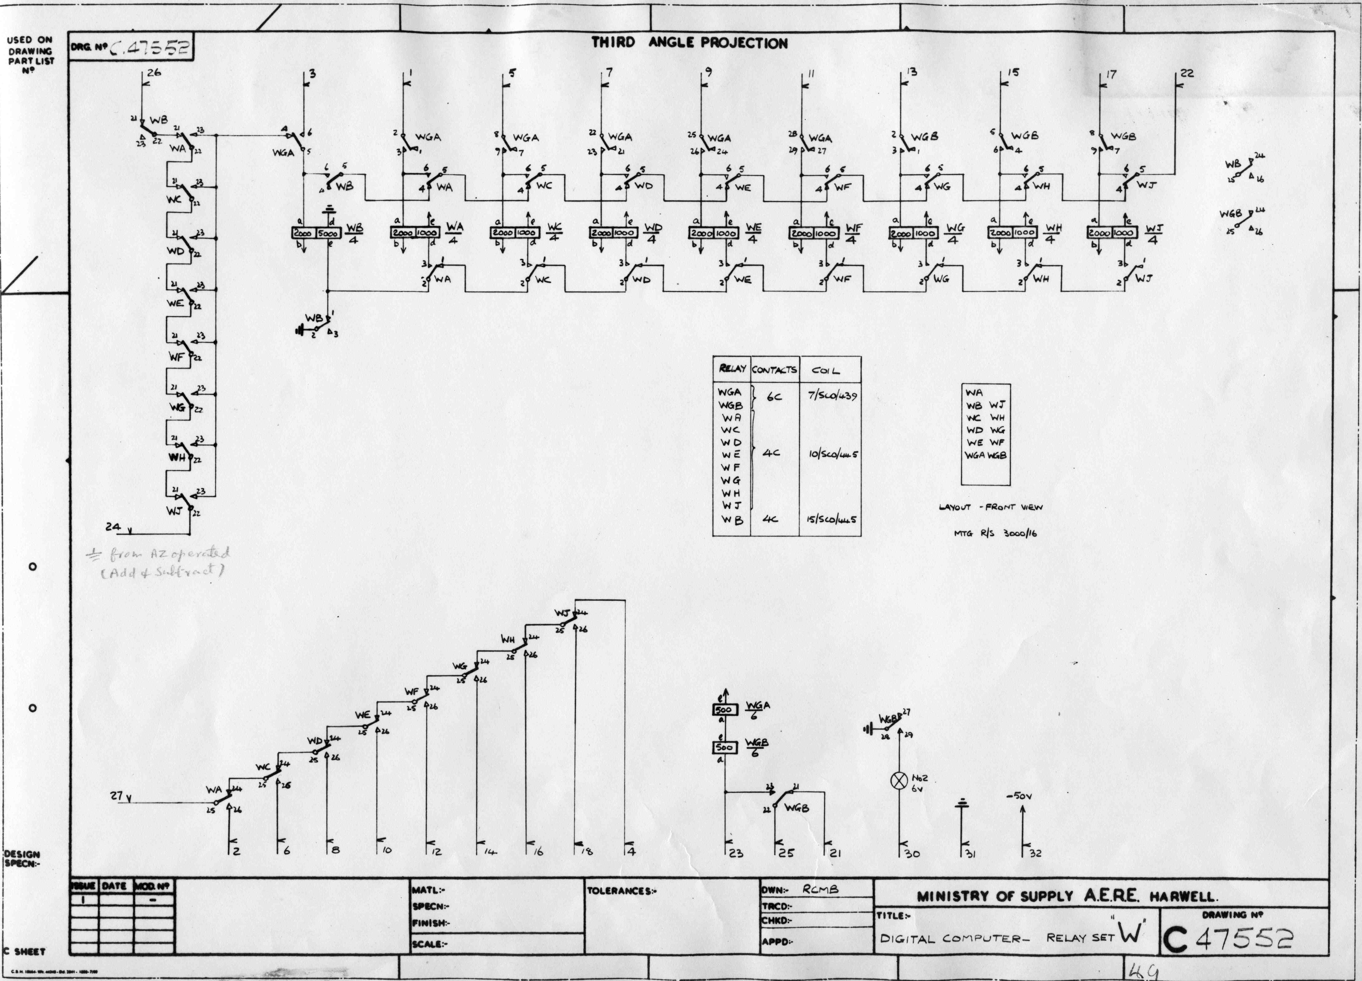
documentation/WITCH-schematics/jpgs/Relay Set W - 47552.jpg
