prpplague/witch_dev/documentation/WITCH-schematics/jpgs/Secondary Sequences - 47593.jpg

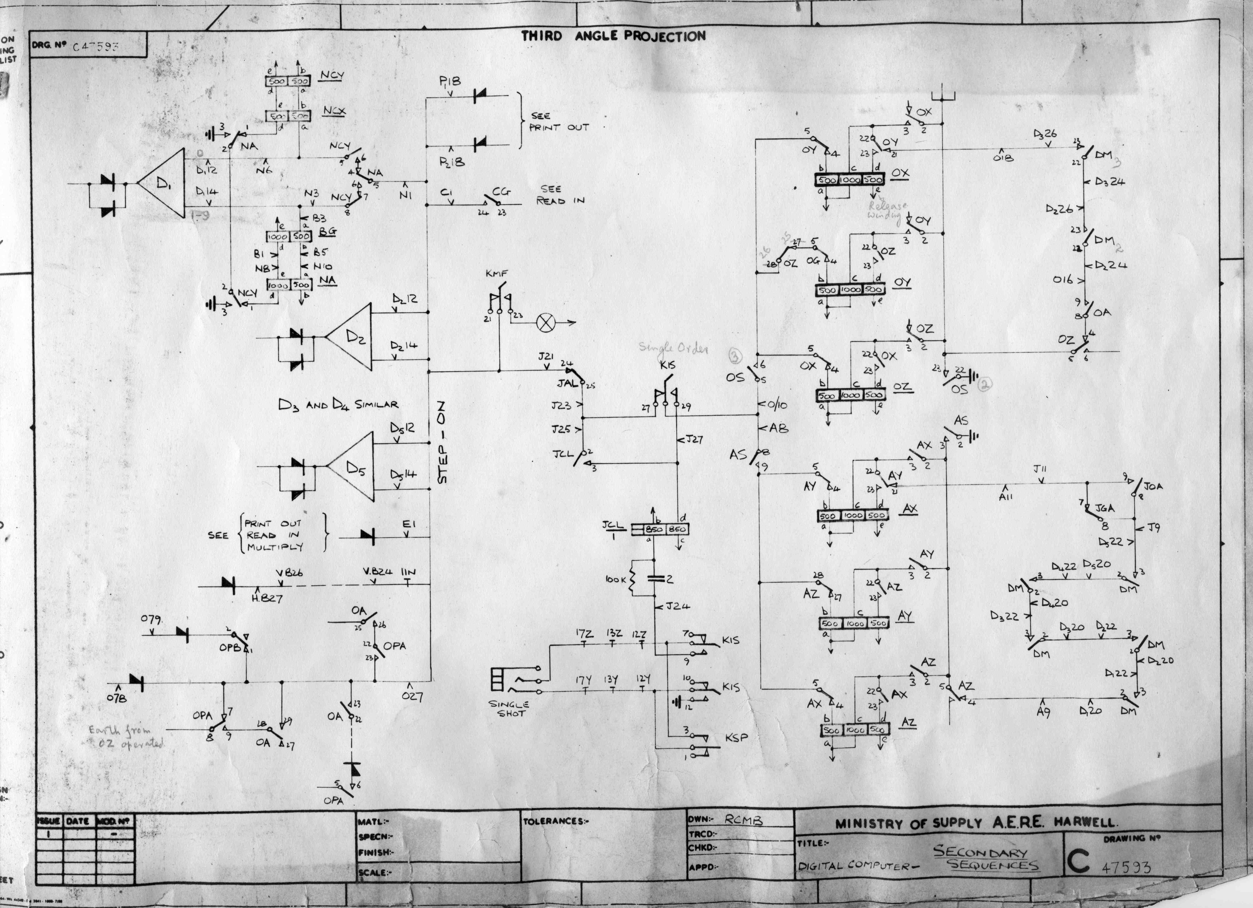
documentation/WITCH-schematics/jpgs/Secondary Sequences - 47593.jpg
