prpplague/witch_dev/documentation/WITCH-schematics/jpgs/Sign Inspection Circuit - 47580.jpg

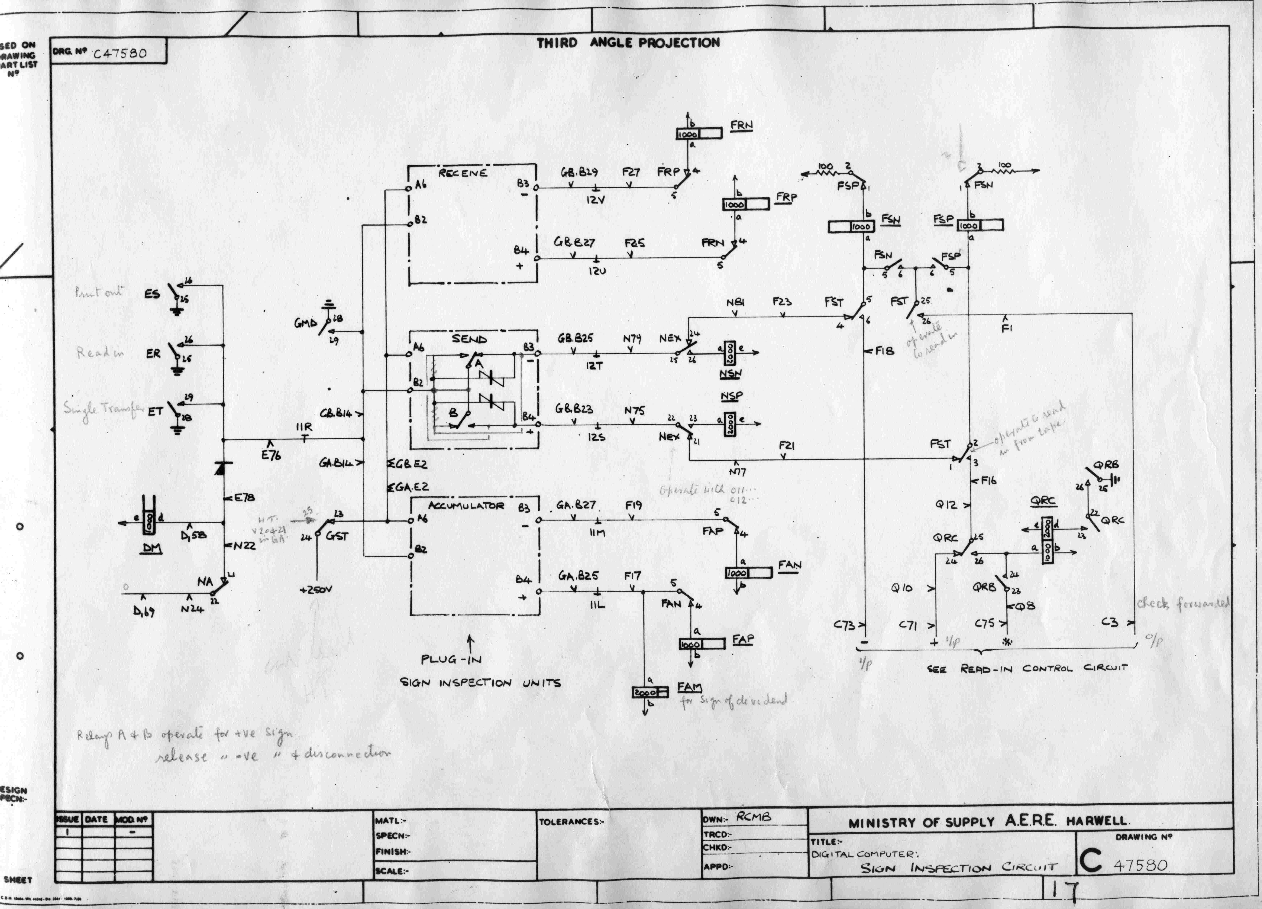
documentation/WITCH-schematics/jpgs/Sign Inspection Circuit - 47580.jpg
