prpplague/witch_dev/documentation/WITCH-schematics/jpgs/Stabiliser Unit - 47546.jpg

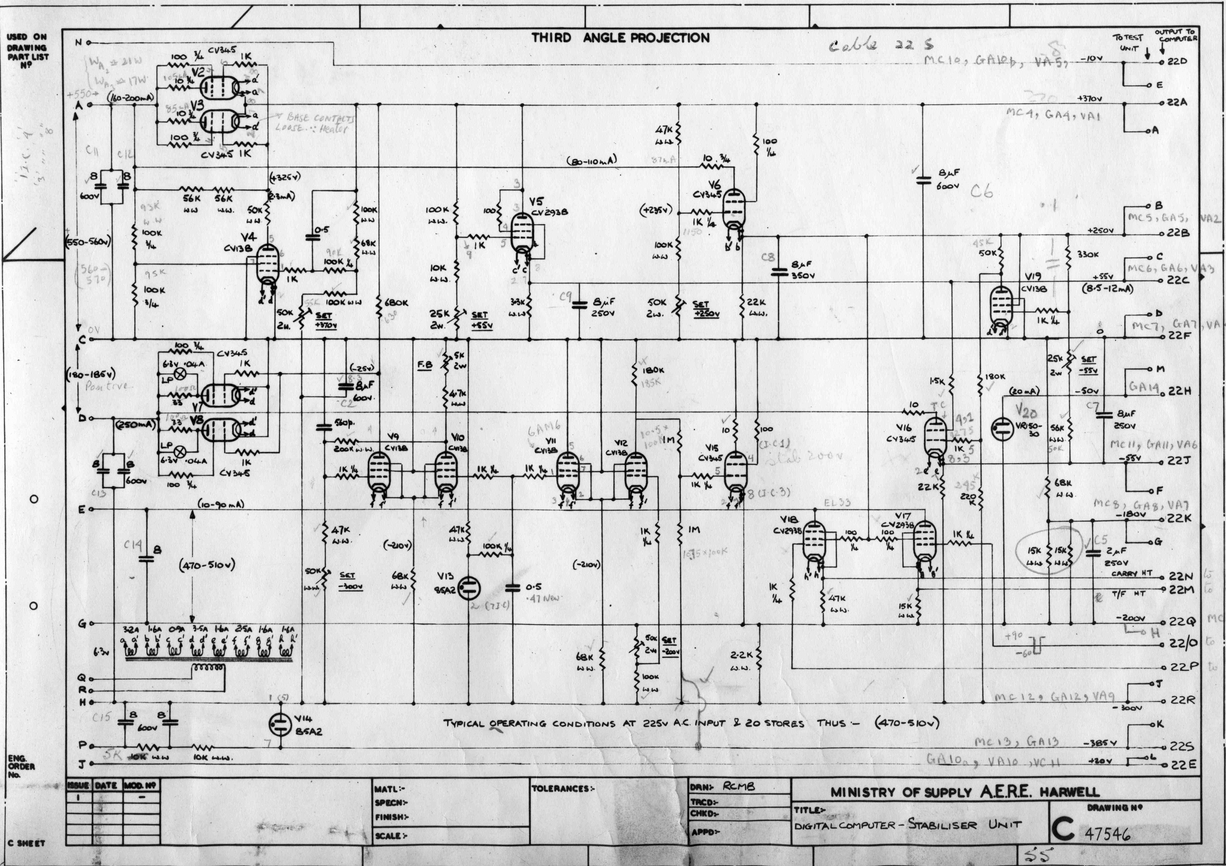
documentation/WITCH-schematics/jpgs/Stabiliser Unit - 47546.jpg
