prpplague/witch_dev/documentation/WITCH-schematics/jpgs/Tape Preparation Equipment - 47548.jpg

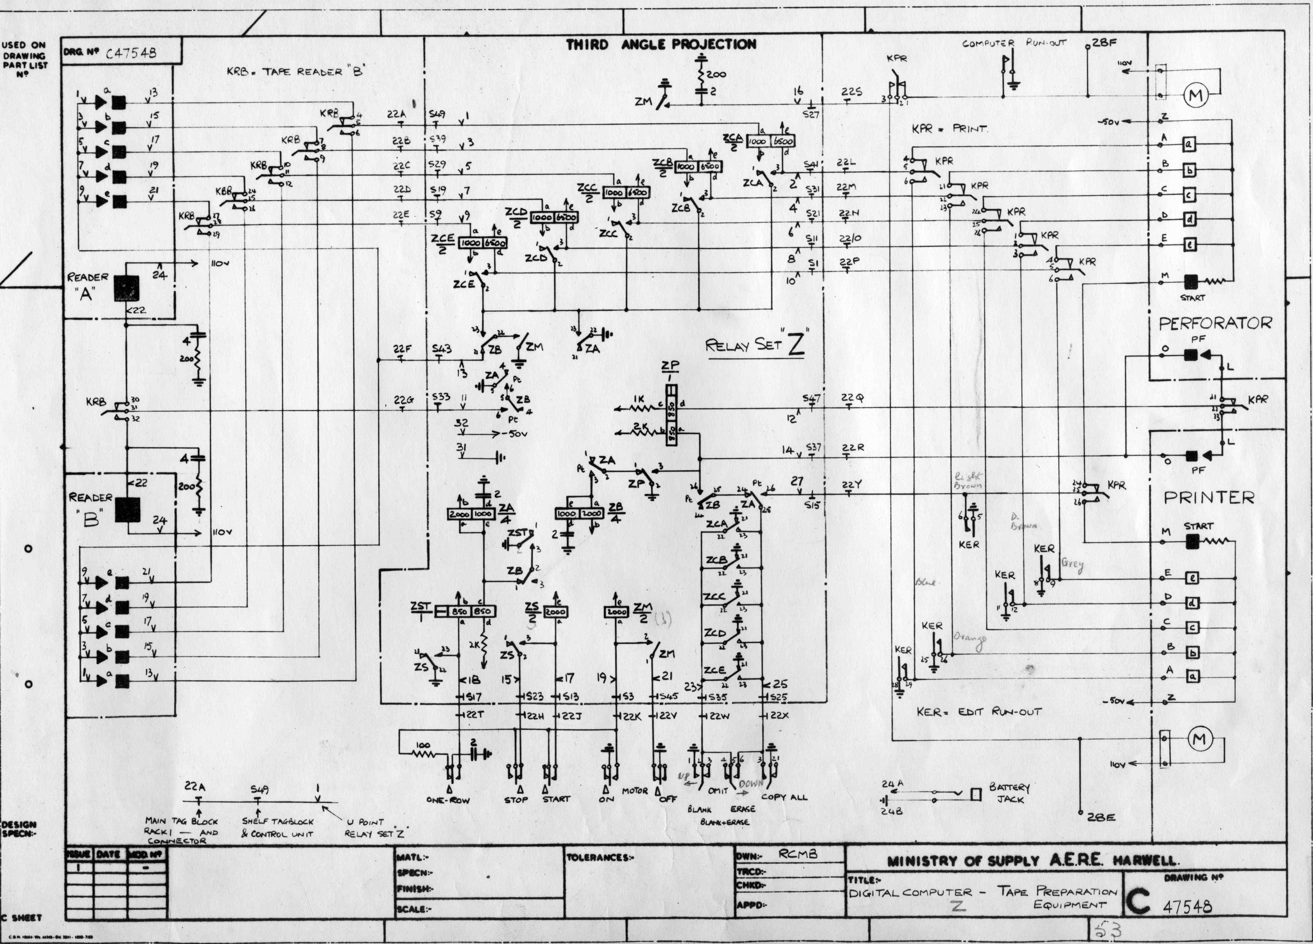
documentation/WITCH-schematics/jpgs/Tape Preparation Equipment - 47548.jpg
