prpplague/witch_dev/documentation/WITCH-schematics/jpgs/Tape Reader Drive - 48302.jpg

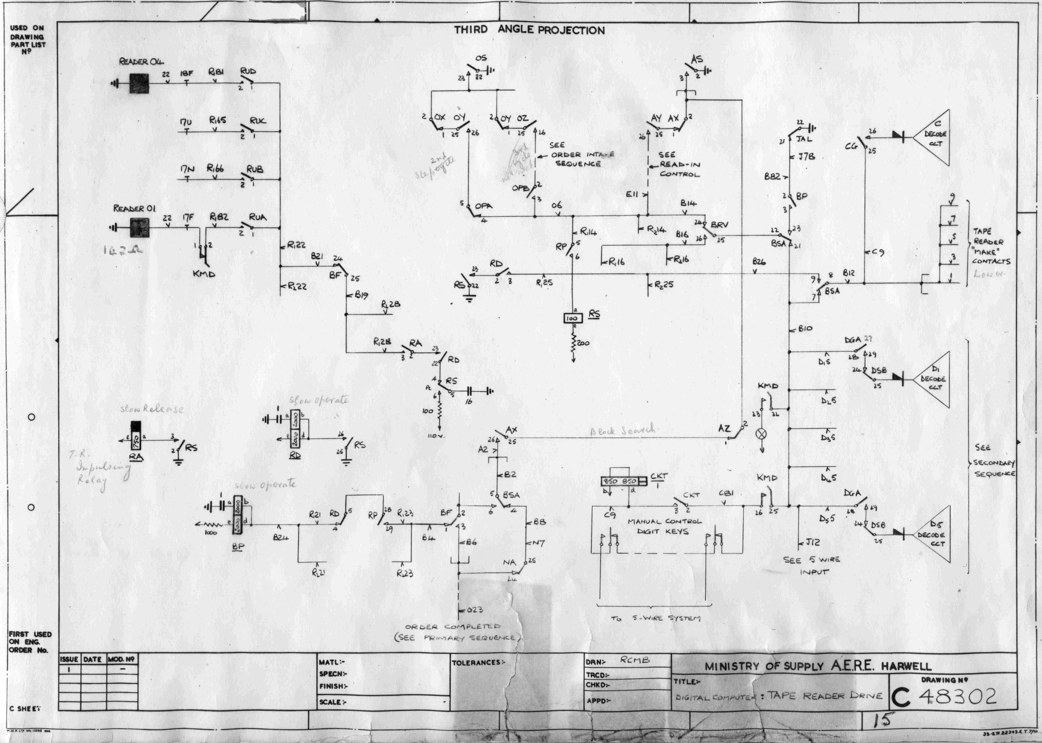
documentation/WITCH-schematics/jpgs/Tape Reader Drive - 48302.jpg
