prpplague/witch_dev/documentation/WITCH-schematics/jpgs/Unit GA Sheet 1 - 47570.jpg

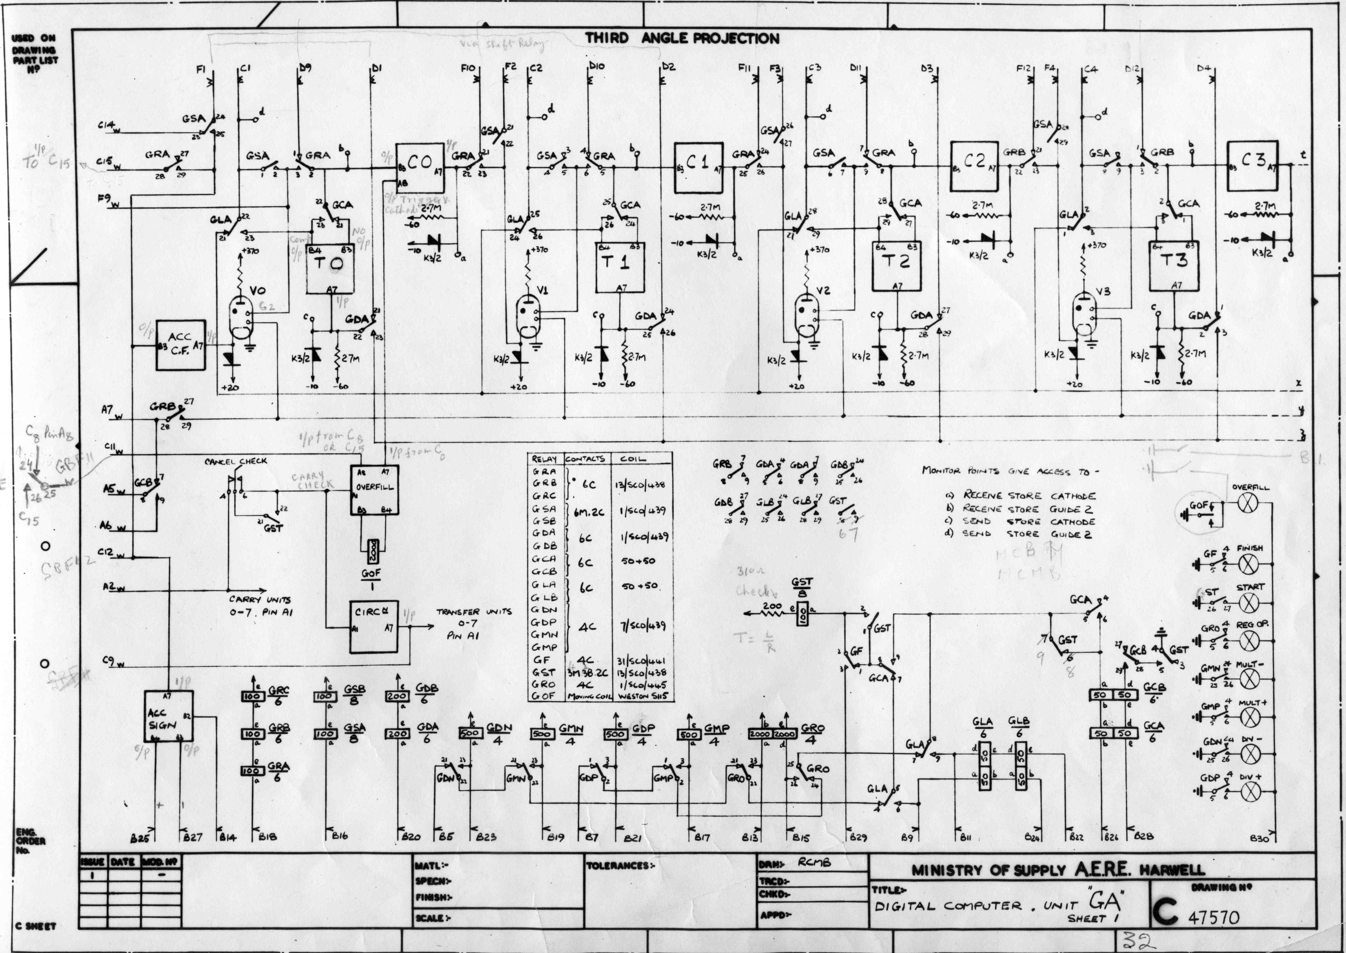
documentation/WITCH-schematics/jpgs/Unit GA Sheet 1 - 47570.jpg
