prpplague/witch_dev/documentation/WITCH-schematics/jpgs/Unit GA Sheet 2 - 47571.jpg

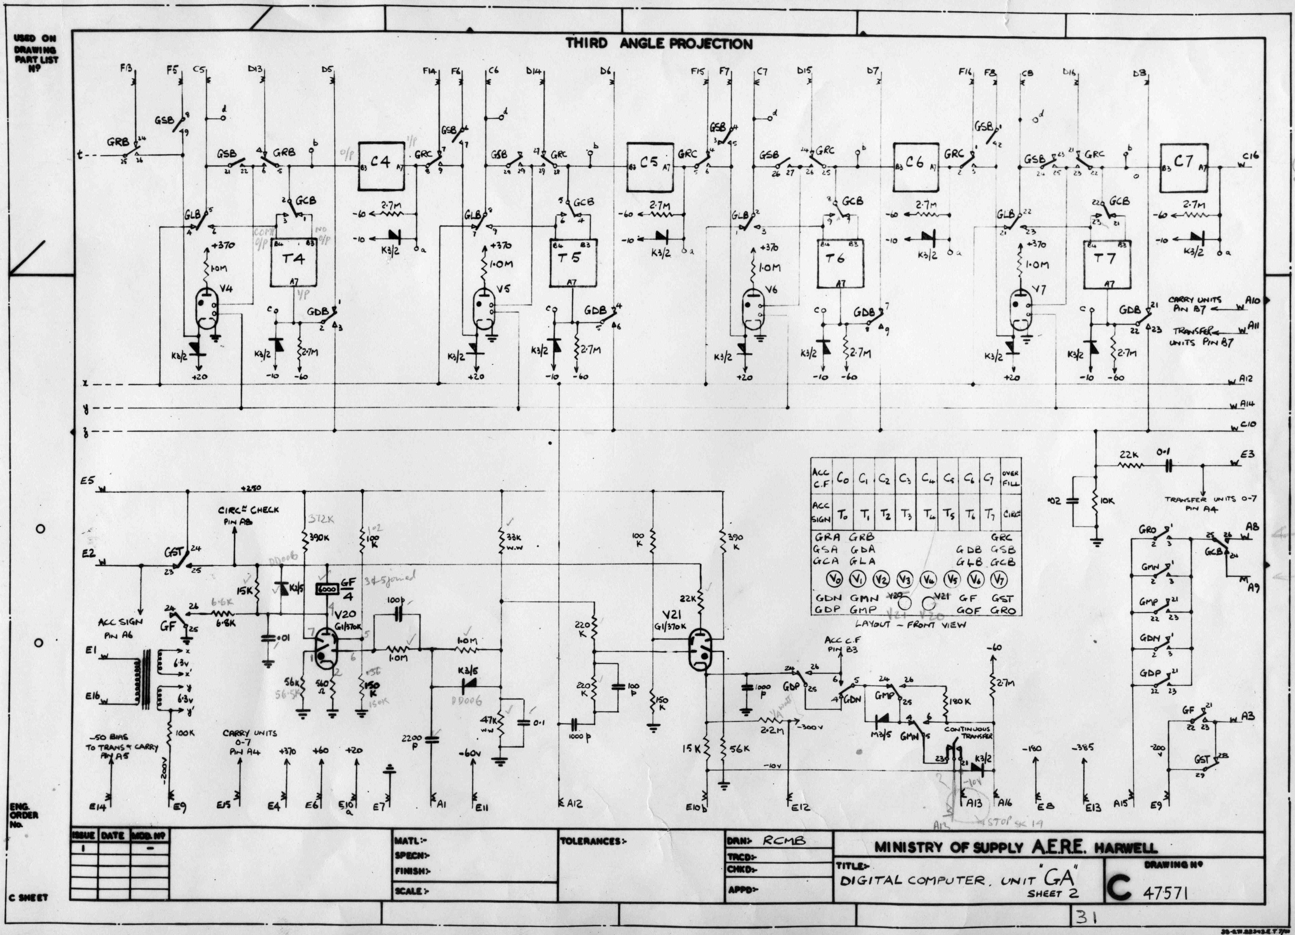
documentation/WITCH-schematics/jpgs/Unit GA Sheet 2 - 47571.jpg
