prpplague/witch_dev/documentation/WITCH-schematics/jpgs/Unit GB Sheet 1 - 47568.jpg

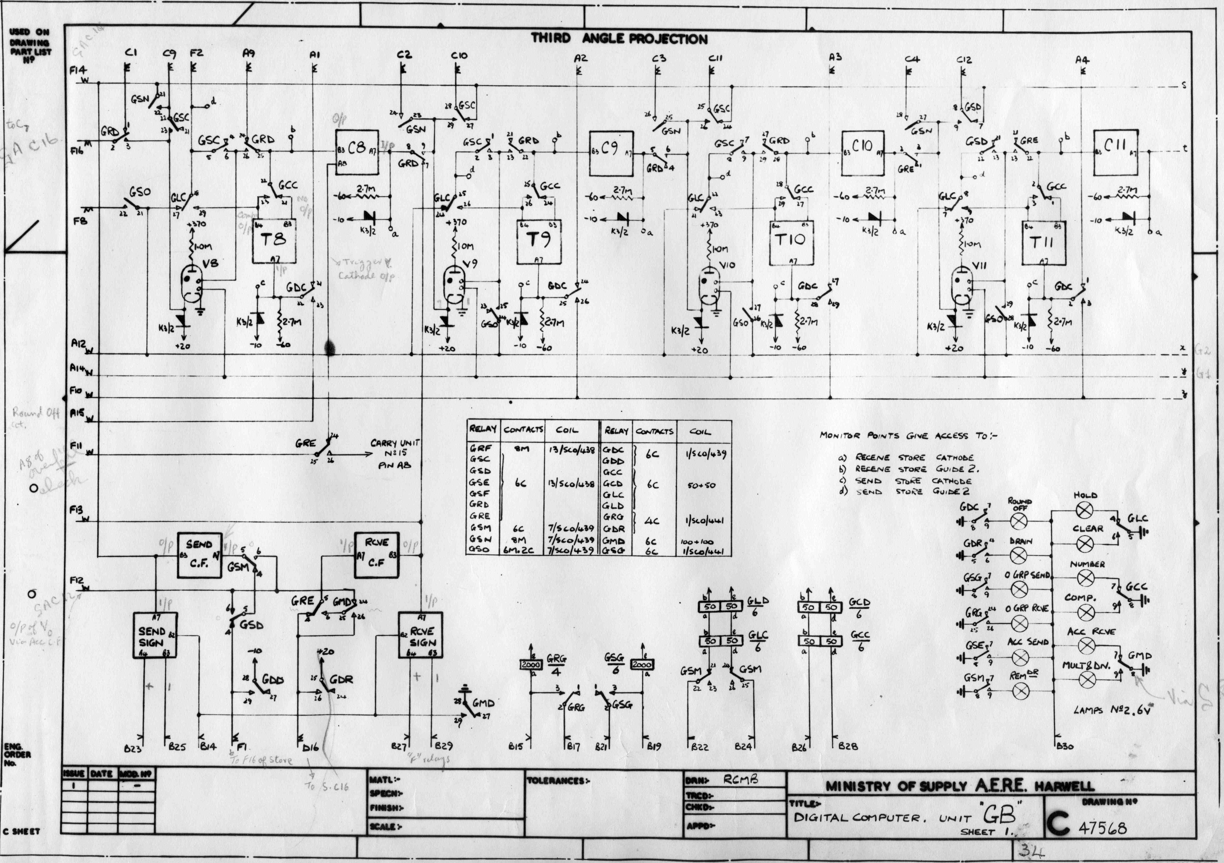
documentation/WITCH-schematics/jpgs/Unit GB Sheet 1 - 47568.jpg
