prpplague/witch_dev/documentation/WITCH-schematics/jpgs/Unit GB Sheet 2 - 47569.jpg

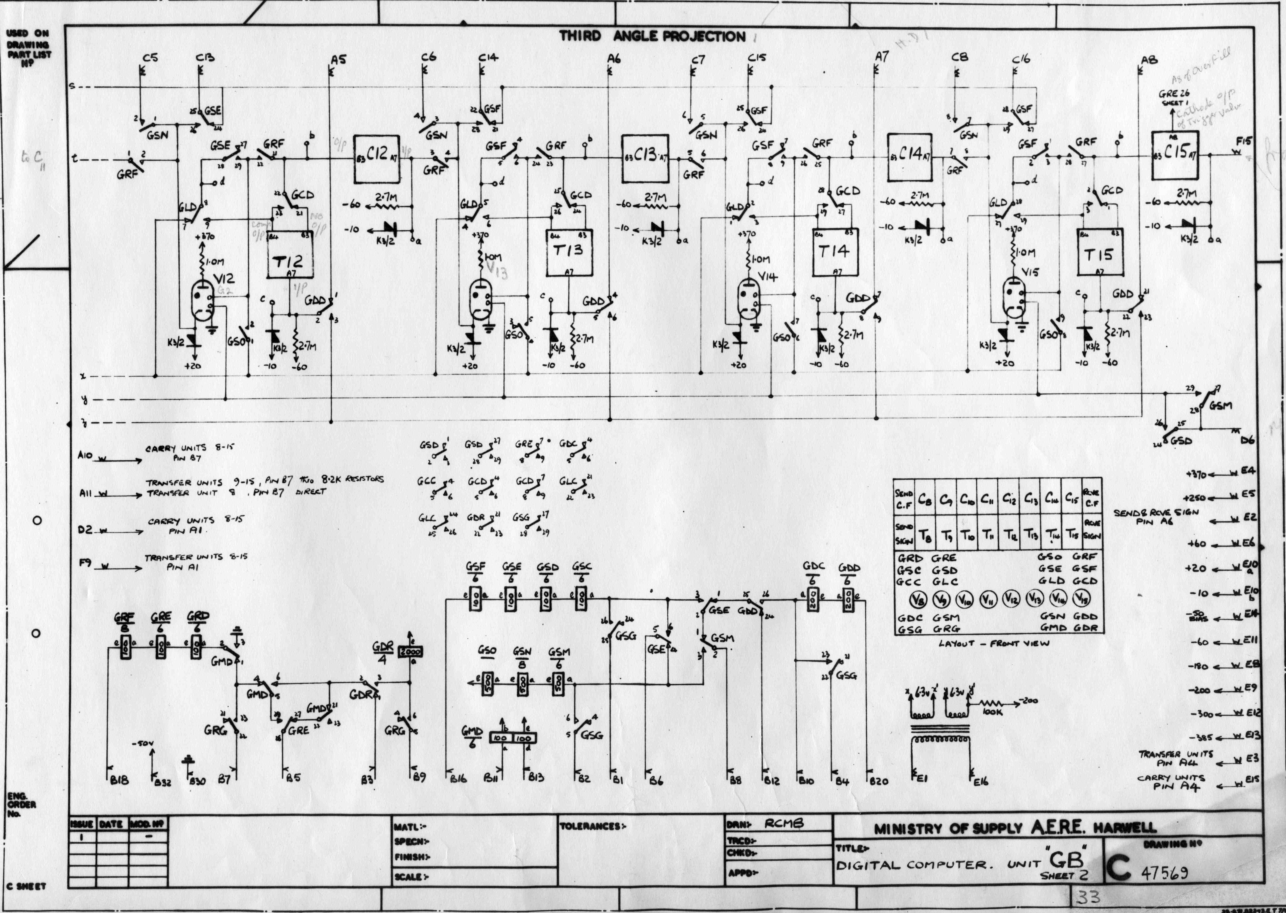
documentation/WITCH-schematics/jpgs/Unit GB Sheet 2 - 47569.jpg
