prpplague/witch_dev/documentation/WITCH-schematics/jpgs/Unit H - 47566.jpg

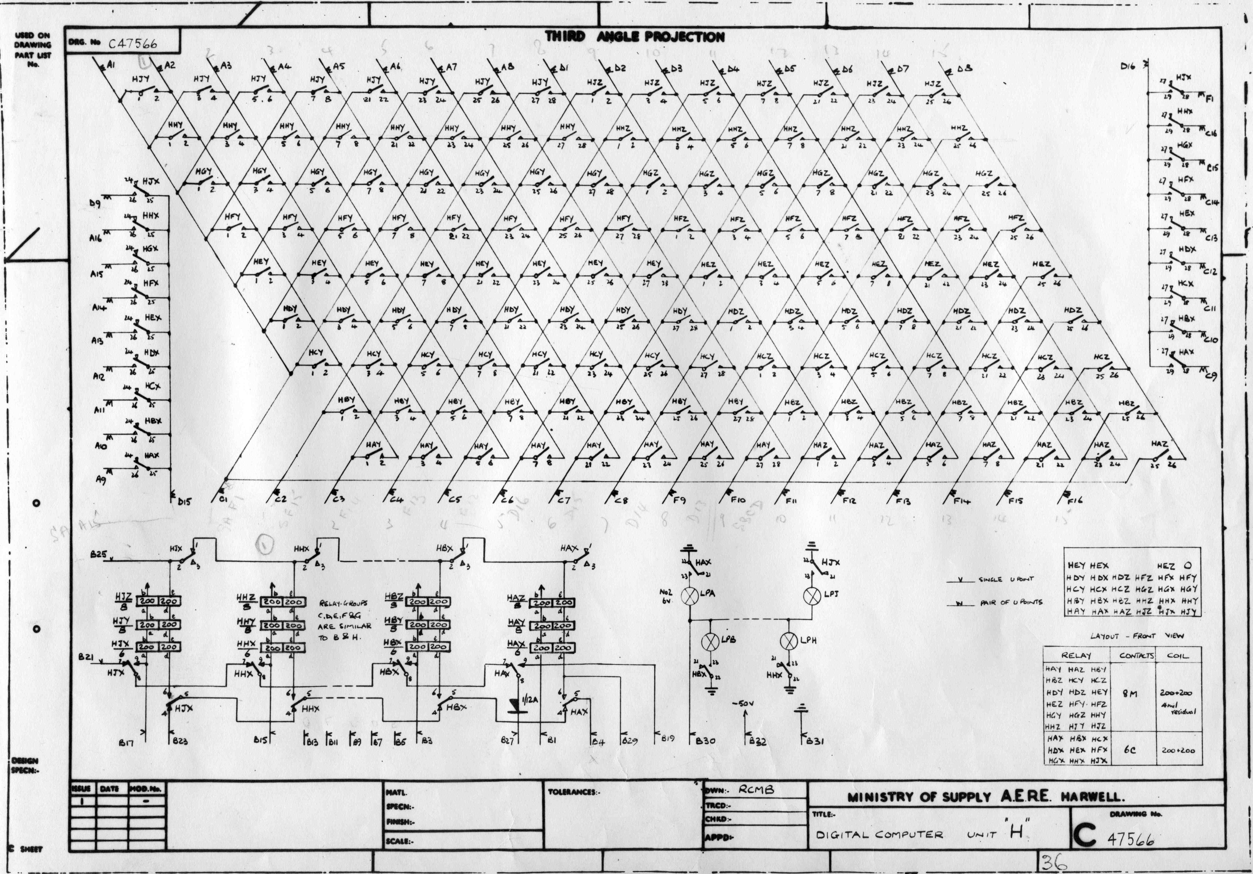
documentation/WITCH-schematics/jpgs/Unit H - 47566.jpg
