prpplague/witch_dev/documentation/WITCH-schematics/jpgs/Unit M Sheet 1 - 47562.jpg

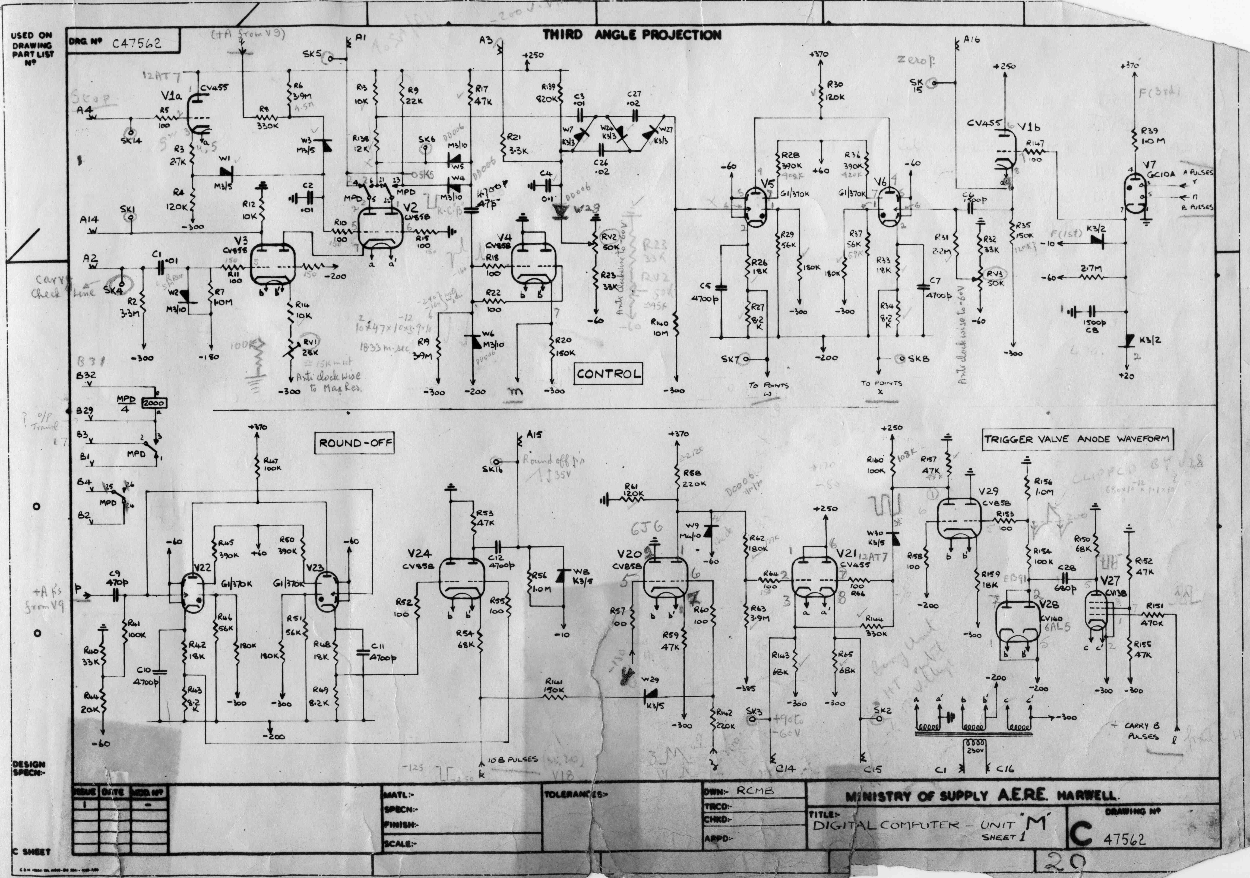
documentation/WITCH-schematics/jpgs/Unit M Sheet 1 - 47562.jpg
