prpplague/witch_dev/documentation/WITCH-schematics/jpgs/Unit M Sheet 2 - 47563.jpg

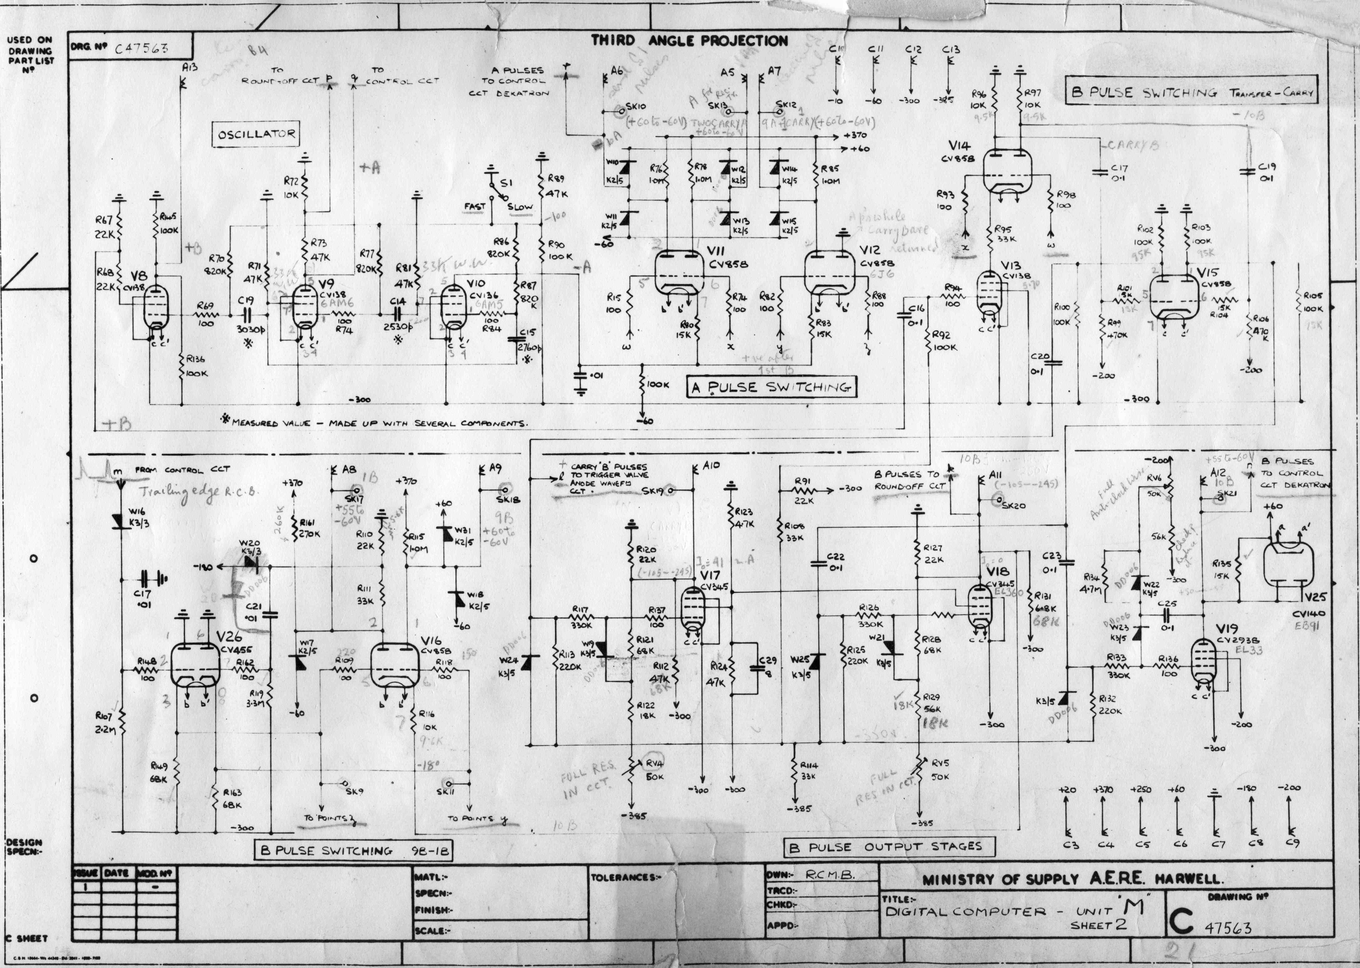
documentation/WITCH-schematics/jpgs/Unit M Sheet 2 - 47563.jpg
