prpplague/witch_dev/documentation/WITCH-schematics/jpgs/Unit S Sheet 2 - 47557.jpg

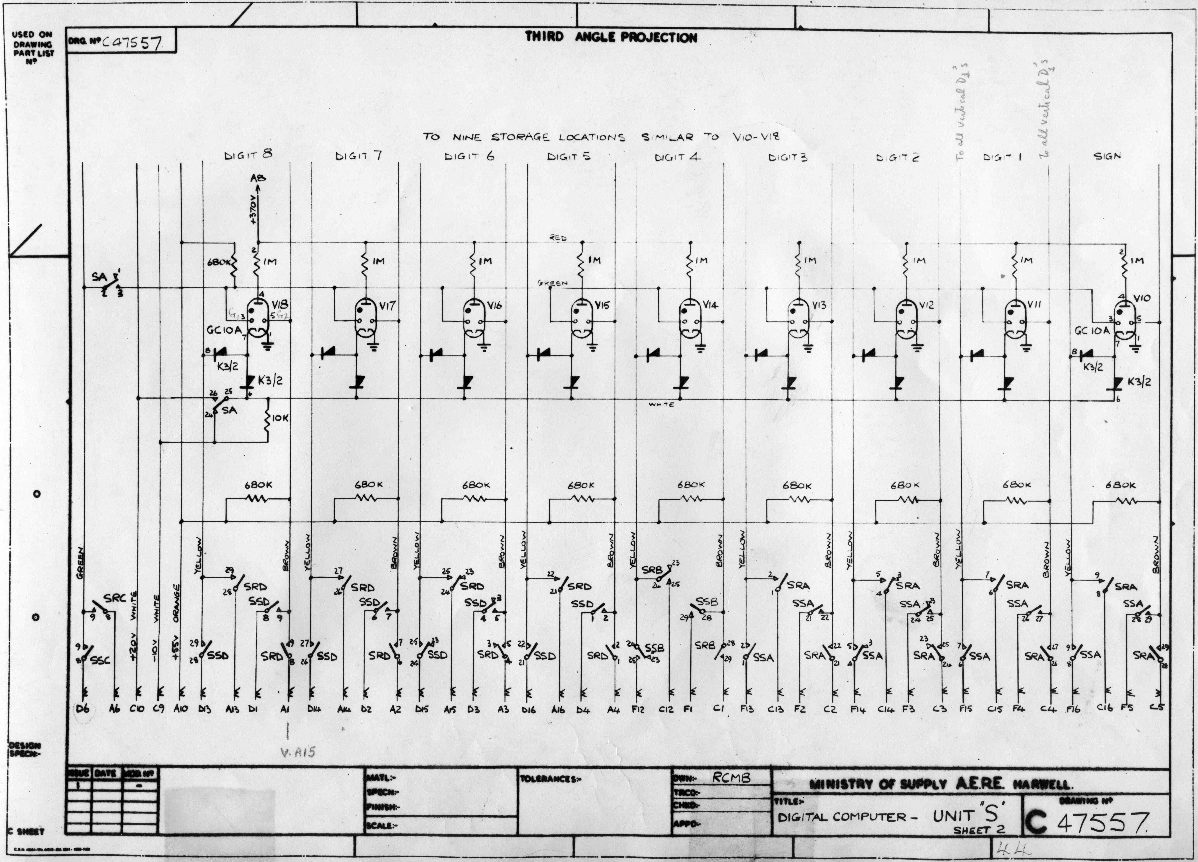
documentation/WITCH-schematics/jpgs/Unit S Sheet 2 - 47557.jpg
