prpplague/witch_dev/documentation/WITCH-schematics/misc/5dotcode001.jpg

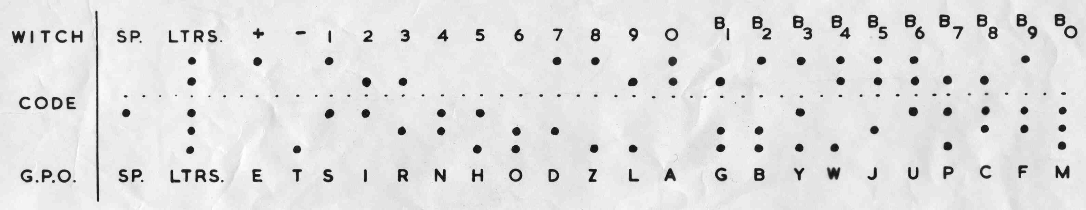
documentation/WITCH-schematics/misc/5dotcode001.jpg
