prpplague/witch_dev/documentation/WITCH-schematics/misc/bertenshaw001.jpg

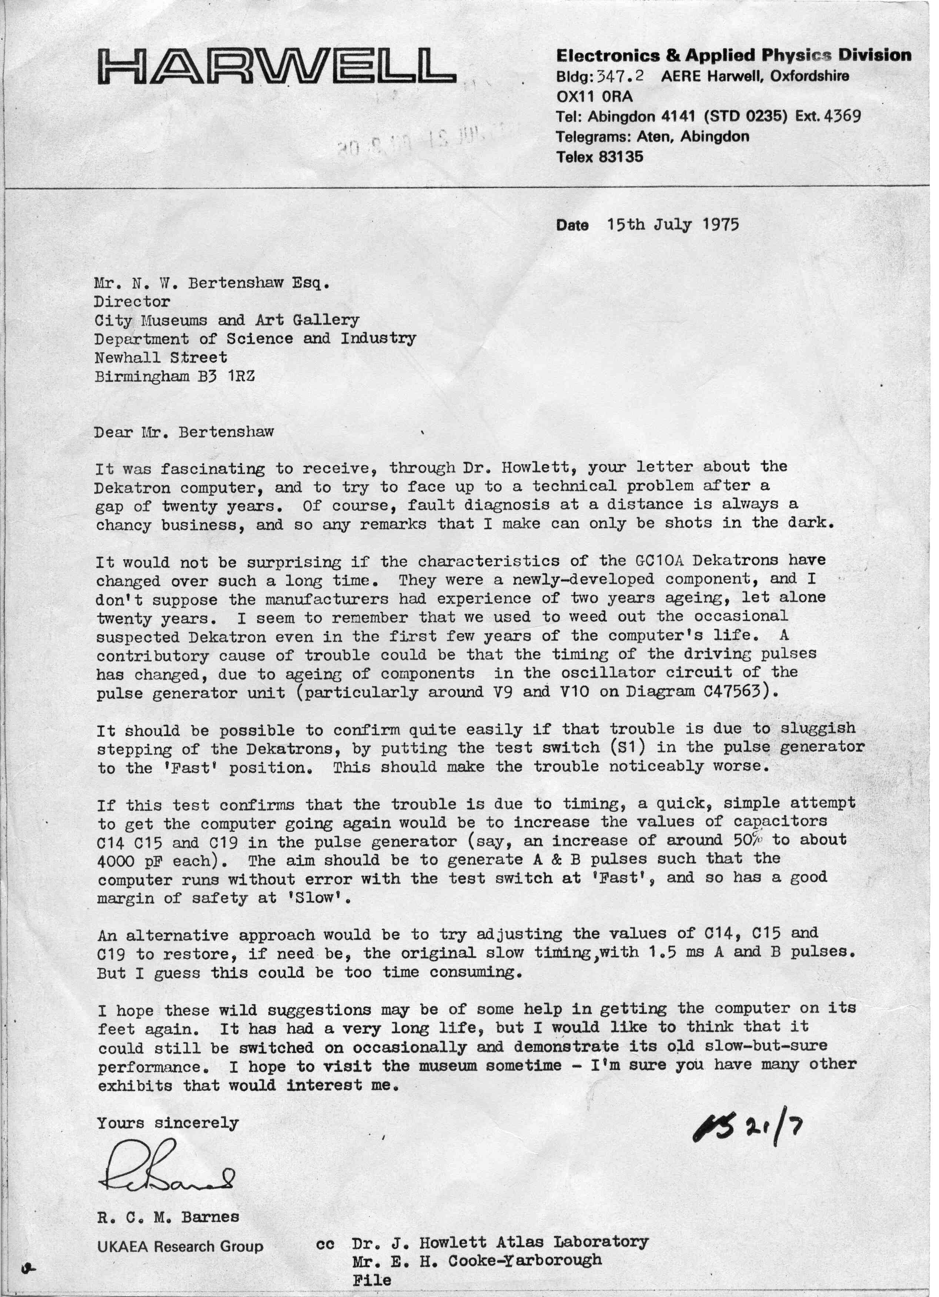
documentation/WITCH-schematics/misc/bertenshaw001.jpg
