prpplague/witch_dev/documentation/WITCH-schematics/notes/cable-sets-1.jpg

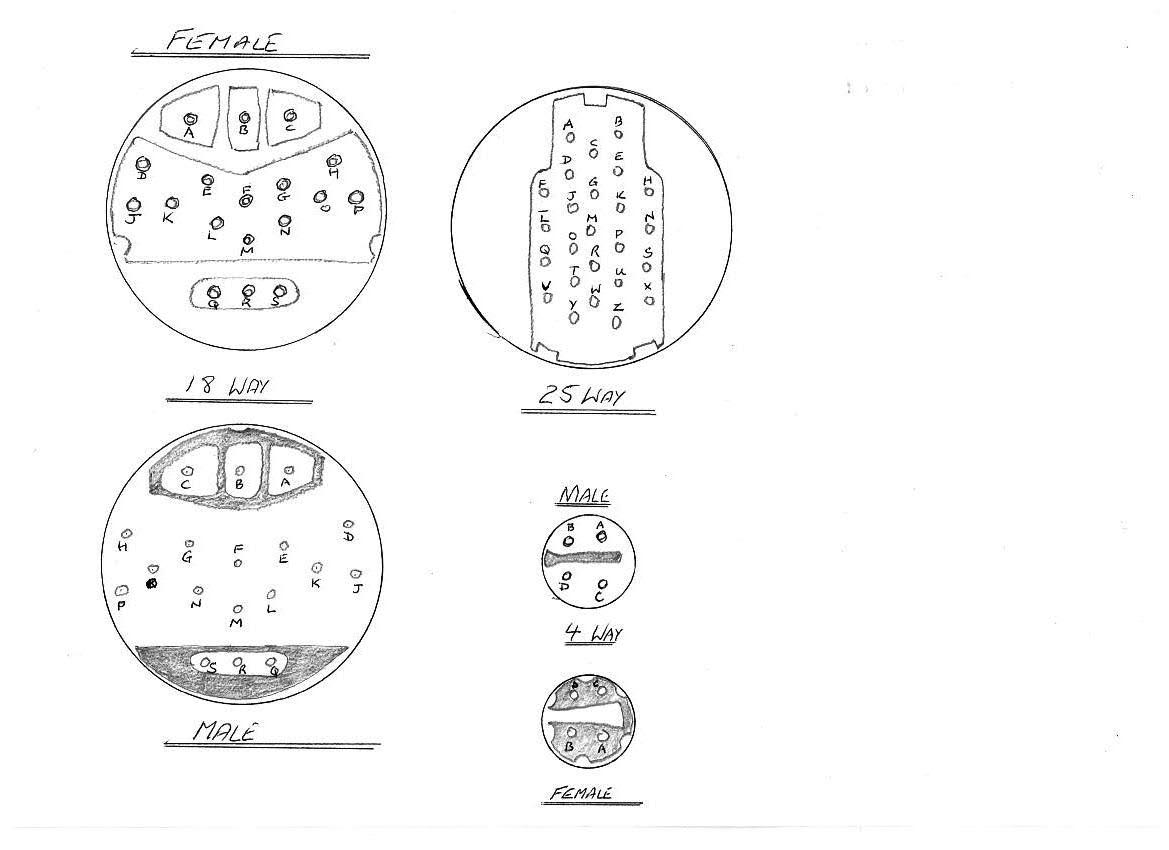
documentation/WITCH-schematics/notes/cable-sets-1.jpg
