prpplague/witch_dev/documentation/WITCH-schematics/notes/cable-sets-2.jpg

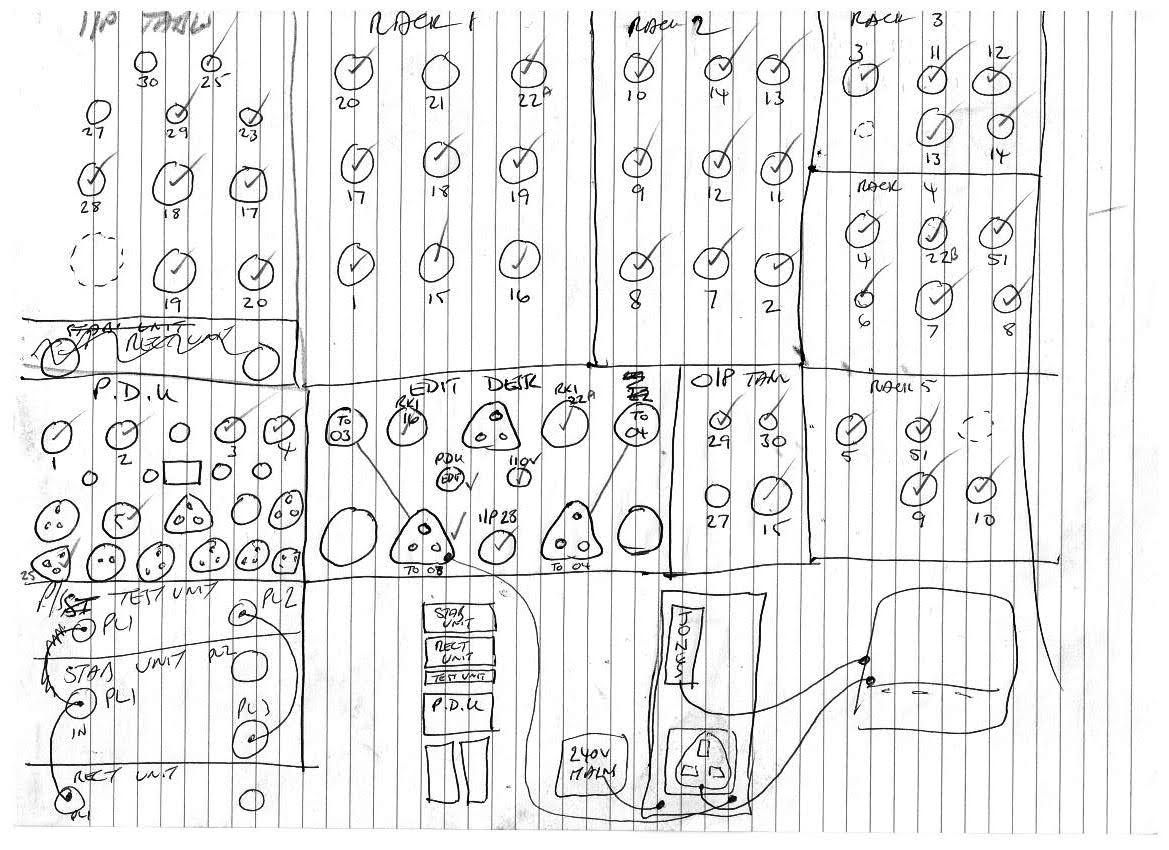
documentation/WITCH-schematics/notes/cable-sets-2.jpg
