prpplague/witch_dev/documentation/WITCH-schematics/notes/cable-sets-3.jpg

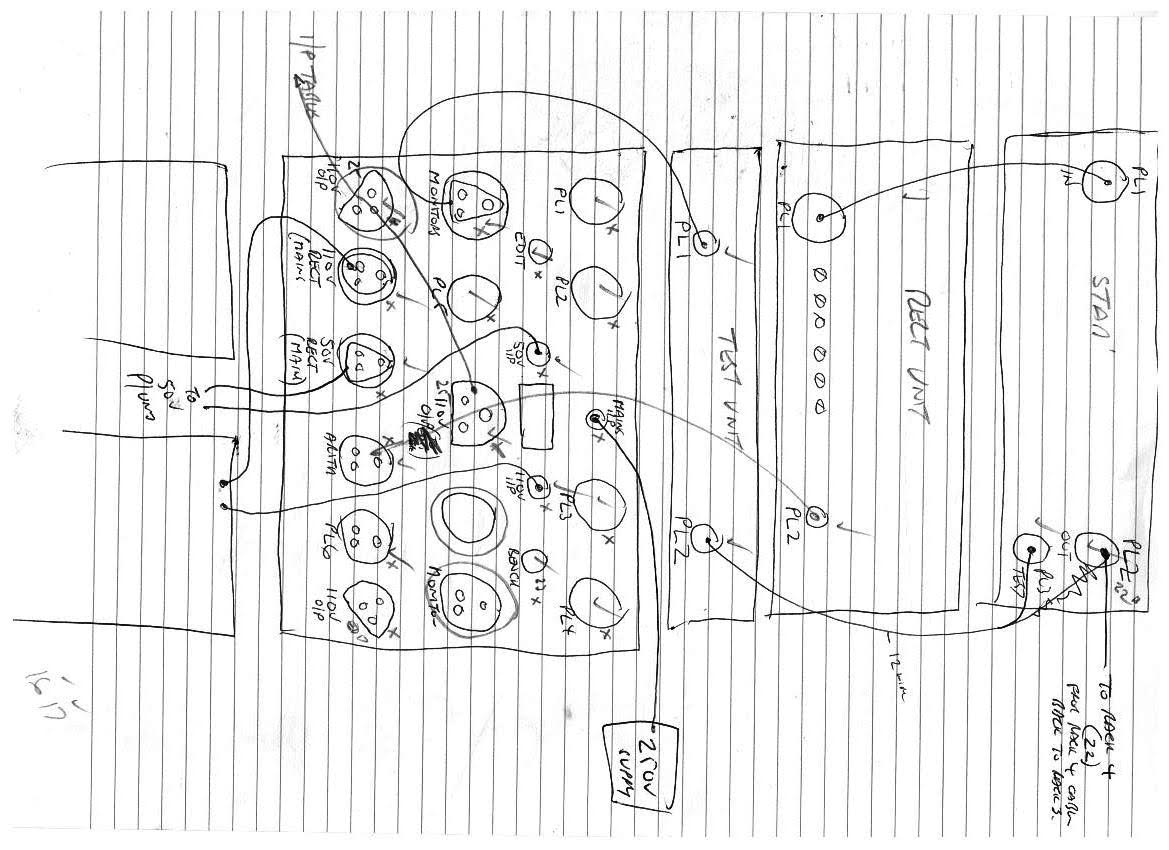
documentation/WITCH-schematics/notes/cable-sets-3.jpg
