prpplague/witch_dev/documentation/WITCH-schematics/notes/HDC cable schedule.jpg

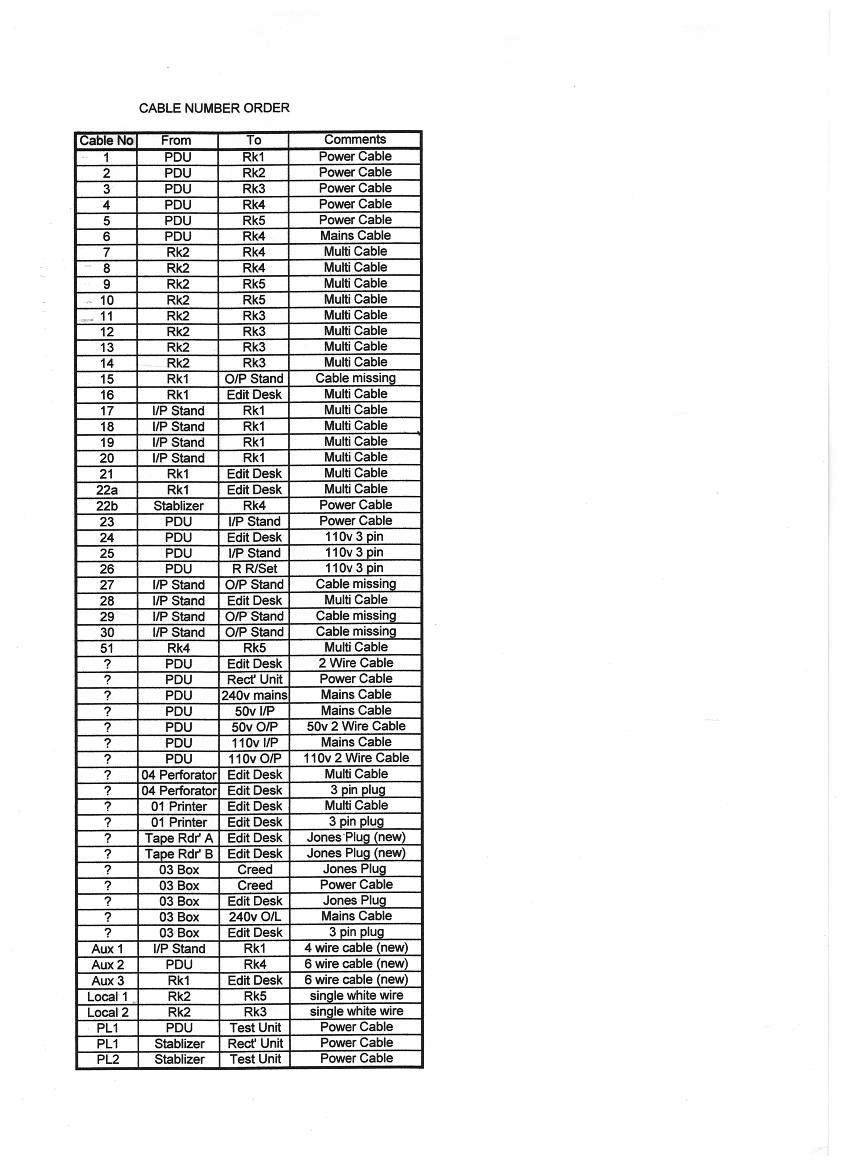
documentation/WITCH-schematics/notes/HDC cable schedule.jpg
