prpplague/witch_dev/documentation/WITCH-schematics/notes/HDC Inter-rack cables.jpg

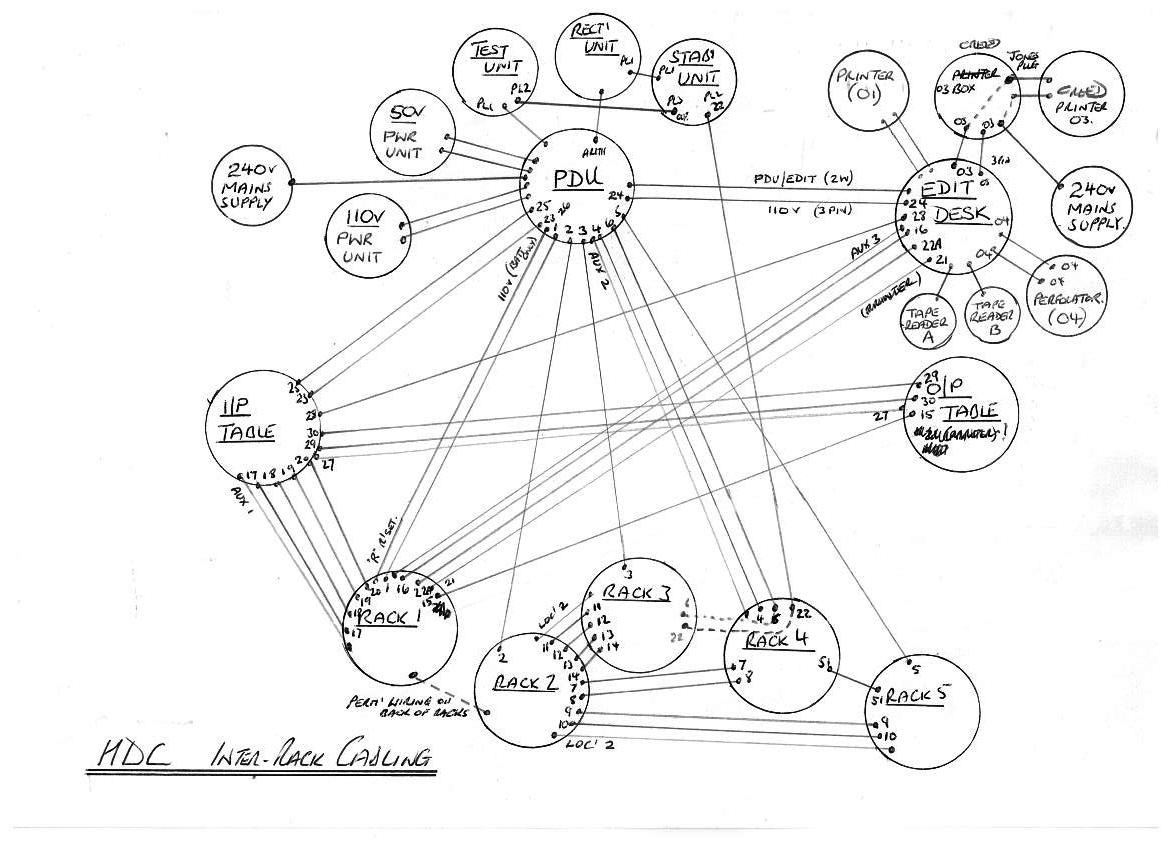
documentation/WITCH-schematics/notes/HDC Inter-rack cables.jpg
