prpplague/witch_dev/documentation/WITCH-schematics/notes/WITCH Layout.jpg

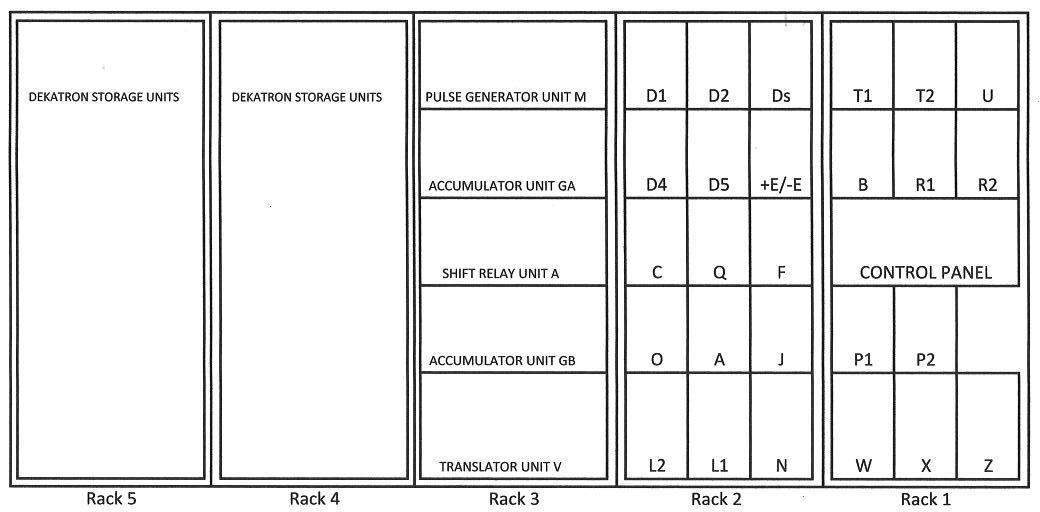
documentation/WITCH-schematics/notes/WITCH Layout.jpg
