prpplague/witch_dev/documentation/WITCH-schematics/jpgs/Order Intake Sequence - 47586.jpg

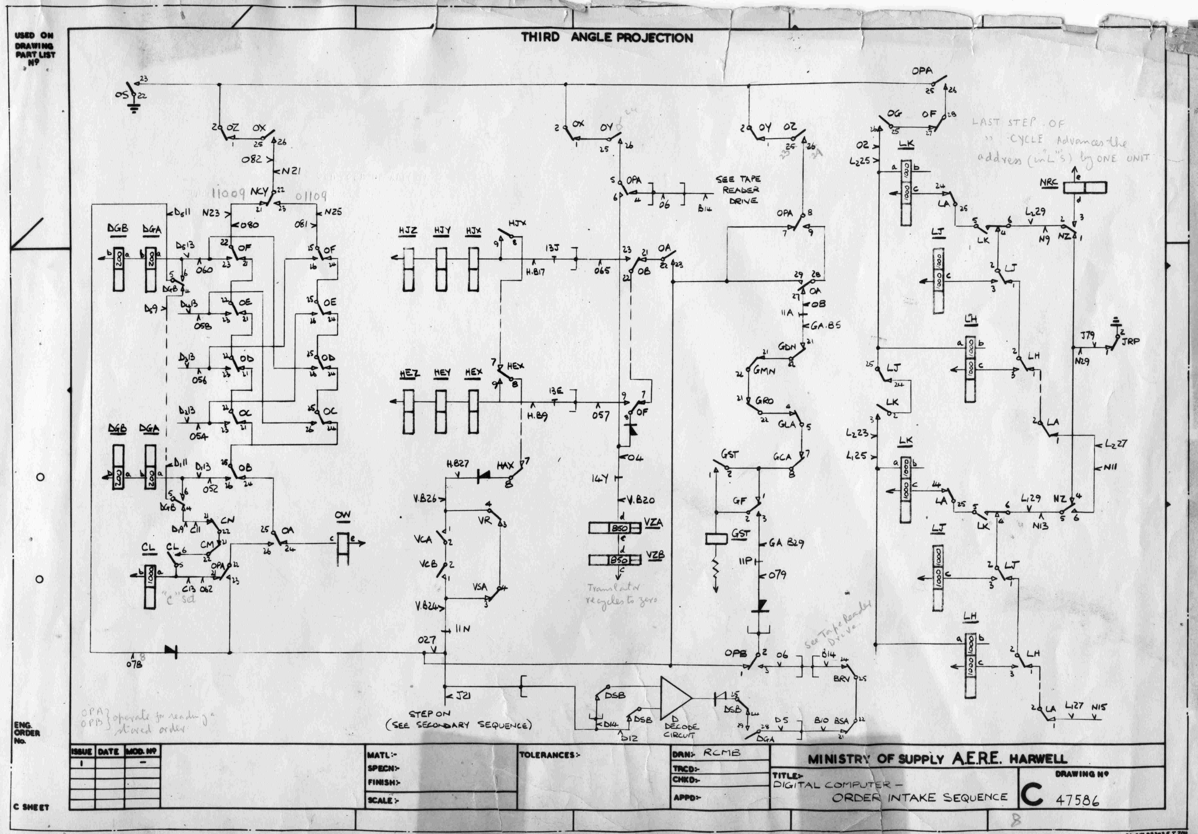
documentation/WITCH-schematics/jpgs/Order Intake Sequence - 47586.jpg
