prpplague/witch_dev/block-designs/witch-phase2/cad/relay-set-d.dxf

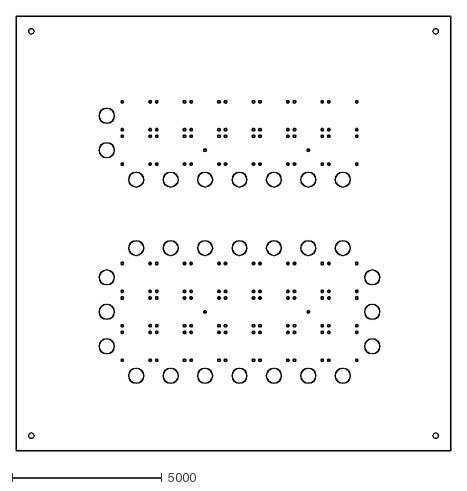
[picture p245: CAD file, 2016-07-04]
block-designs/witch-phase2/cad/relay-set-d.dxf
14500.0 x 14500.0
