prpplague/witch_dev/block-designs/witch-phase4/tape-reader/cad/58mm/tape-reader-top.dxf

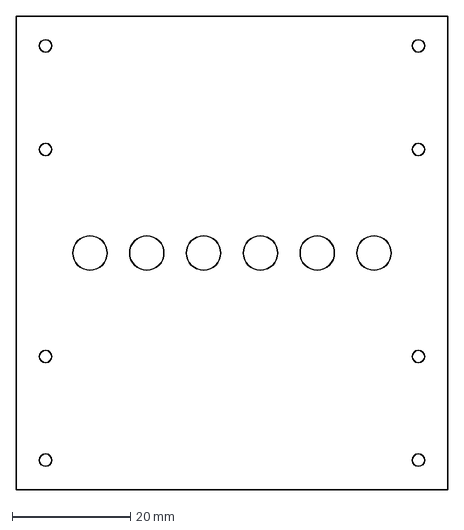
[picture p246: CAD file, 2017-11-26, an earlier design]
block-designs/witch-phase4/tape-reader/cad/58mm/tape-reader-top.dxf
73.0 x 80.0 mm
