prpplague/witch_dev/block-designs/witch-phase4/tape-reader/cad/58mm/tape-reader-bot.dxf

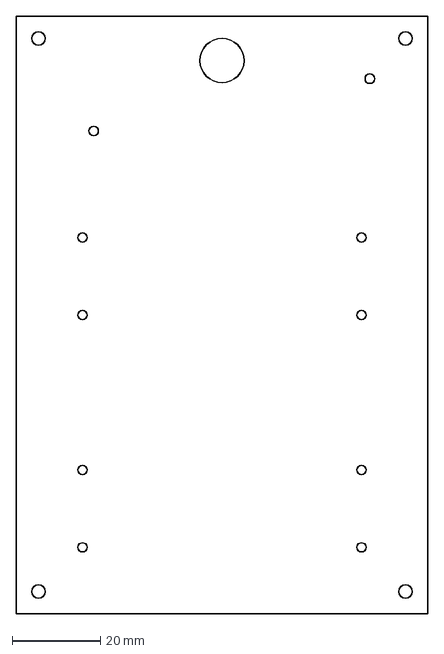
[picture p247: CAD file, 2017-11-26, an earlier design]
block-designs/witch-phase4/tape-reader/cad/58mm/tape-reader-bot.dxf
93.0 x 135.0 mm
