prpplague/witch_dev/block-designs/witch-phase4/tape-reader/cad/58mm/tape-reader-mid.dxf

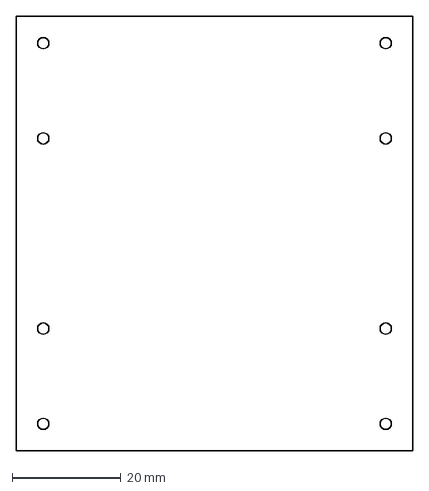
[picture p248: CAD file, 2016-06-26, an earlier design]
block-designs/witch-phase4/tape-reader/cad/58mm/tape-reader-mid.dxf
73.0 x 80.0 mm
