prpplague/witch_dev/documentation/WITCH-schematics/notes/Print Out Control Notes - 47581.pdf

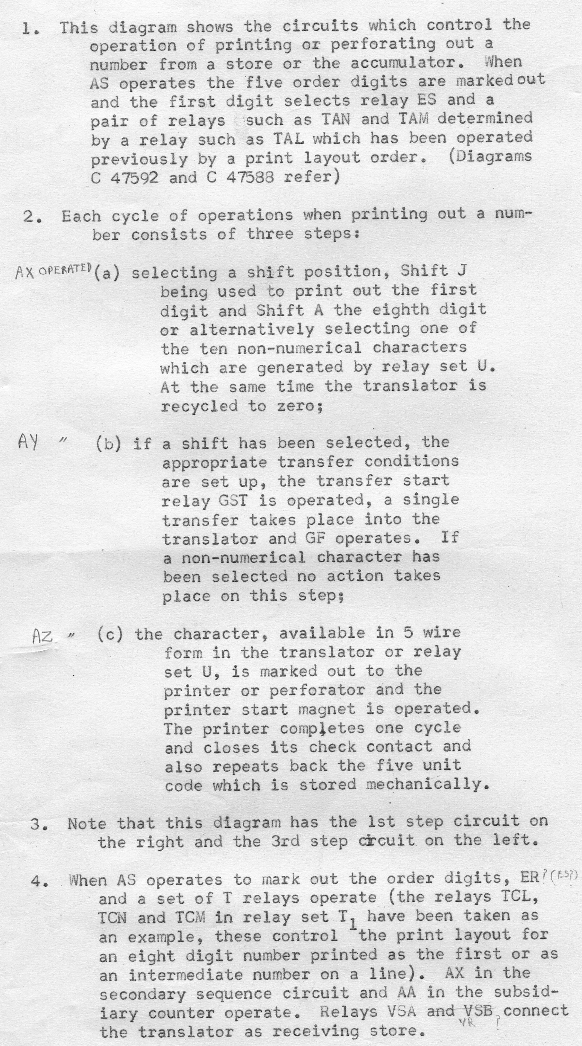
[picture p249: figure]

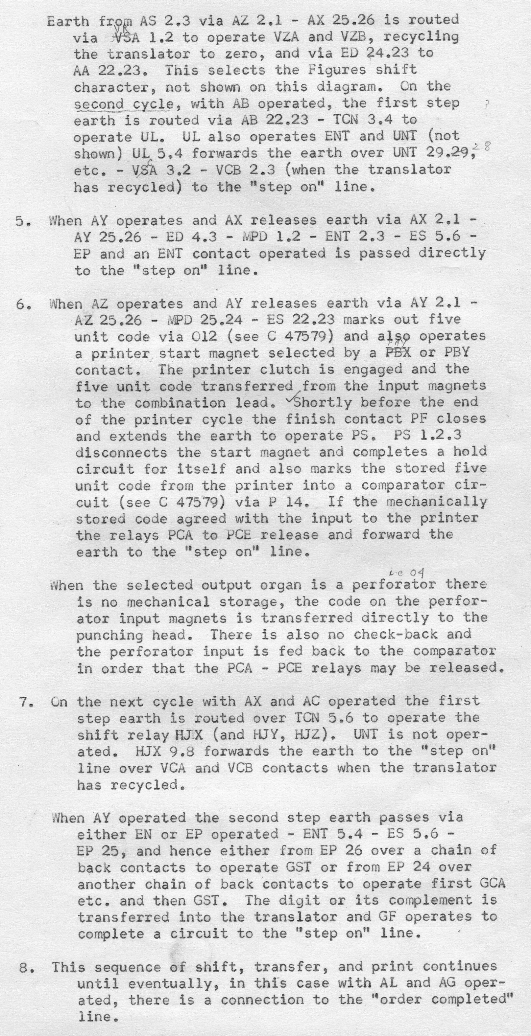
[picture p250: figure]
