prpplague/witch_dev/documentation/WITCH-schematics/jpgs/C48133_Rack_Wiring_Schedules_H_GB.jpg

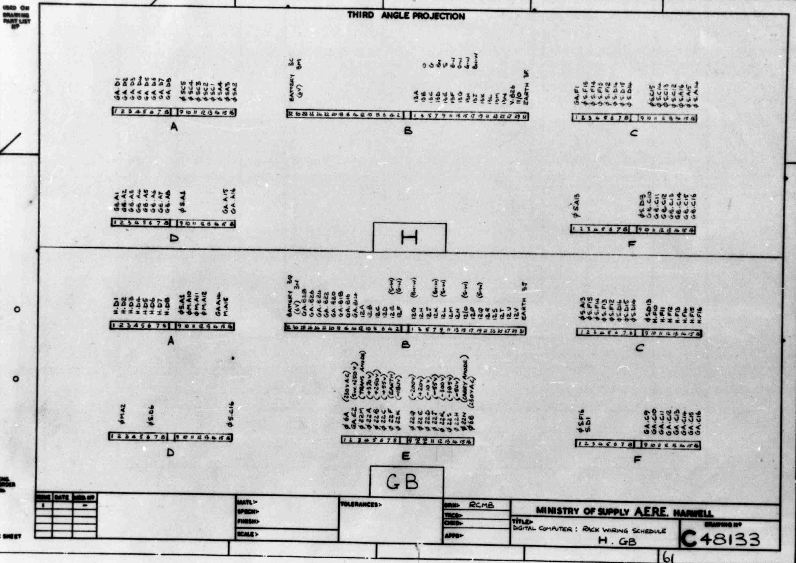
documentation/WITCH-schematics/jpgs/C48133_Rack_Wiring_Schedules_H_GB.jpg
