prpplague/witch_dev/documentation/WITCH-schematics/jpgs/manual-input-buttons.jpg

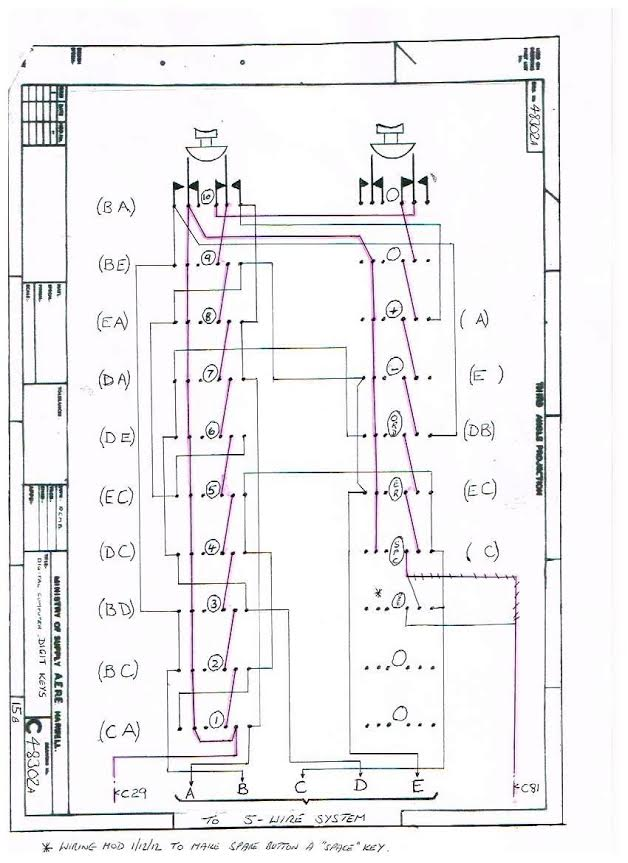
documentation/WITCH-schematics/jpgs/manual-input-buttons.jpg
