prpplague/witch_dev/documentation/WITCH-schematics/jpgs/Print Out - 47581.jpg

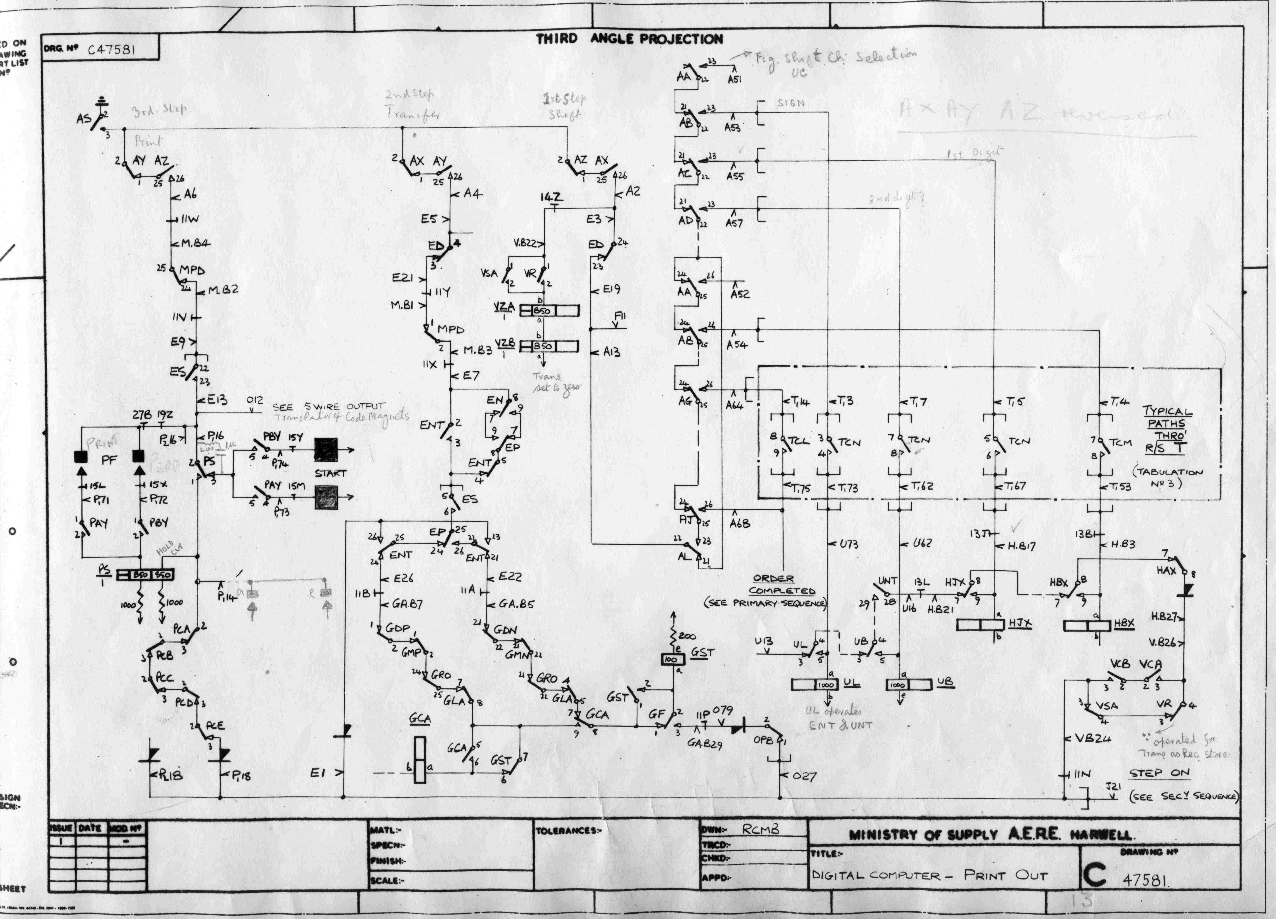
documentation/WITCH-schematics/jpgs/Print Out - 47581.jpg
