prpplague/witch_dev/documentation/WITCH-schematics/jpgs/Rack Wiring Schedule A B C D1 - 48130.jpg

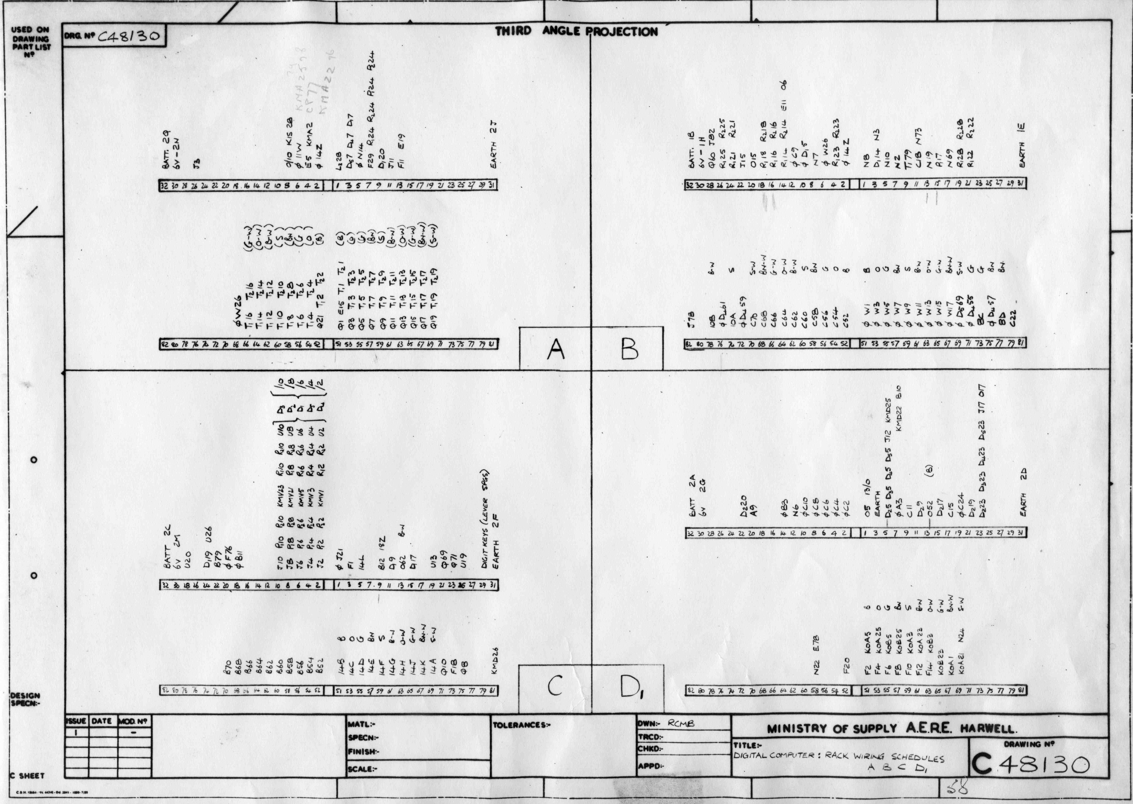
documentation/WITCH-schematics/jpgs/Rack Wiring Schedule A B C D1 - 48130.jpg
