prpplague/witch_dev/documentation/WITCH-schematics/jpgs/Rack Wiring Schedule D2 D3 D4 D5 - 48131.jpg

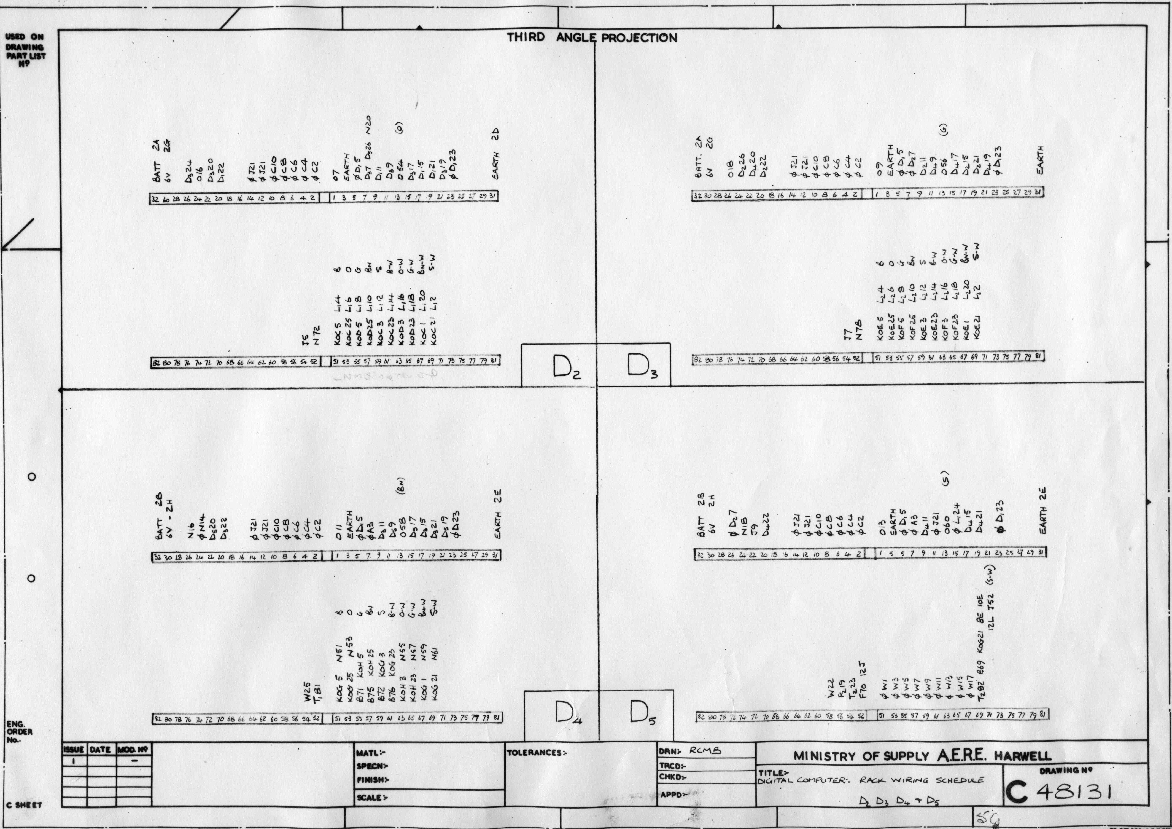
documentation/WITCH-schematics/jpgs/Rack Wiring Schedule D2 D3 D4 D5 - 48131.jpg
