prpplague/witch_dev/documentation/WITCH-schematics/jpgs/Rack Wiring Schedule E F GA - 48132.jpg

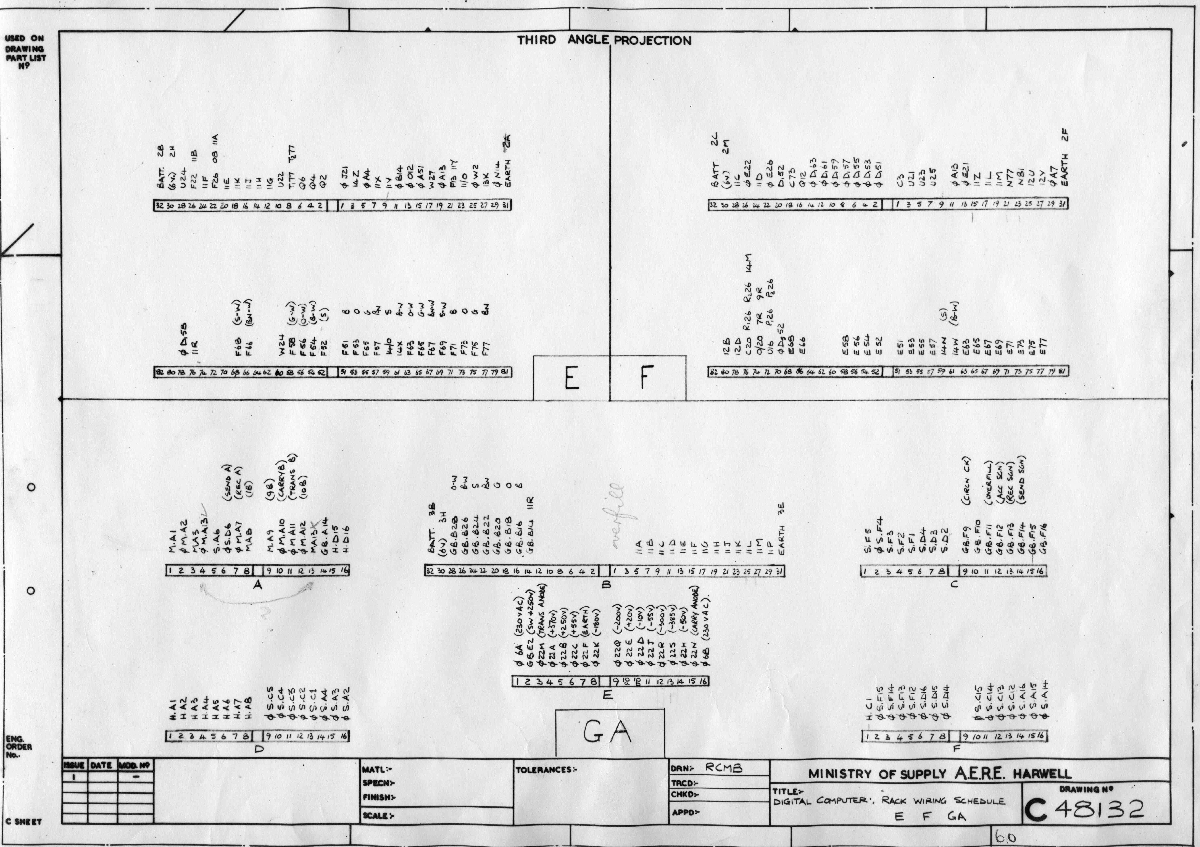
documentation/WITCH-schematics/jpgs/Rack Wiring Schedule E F GA - 48132.jpg
