prpplague/witch_dev/documentation/WITCH-schematics/jpgs/Rack Wiring Schedule H GB - 48133.jpg

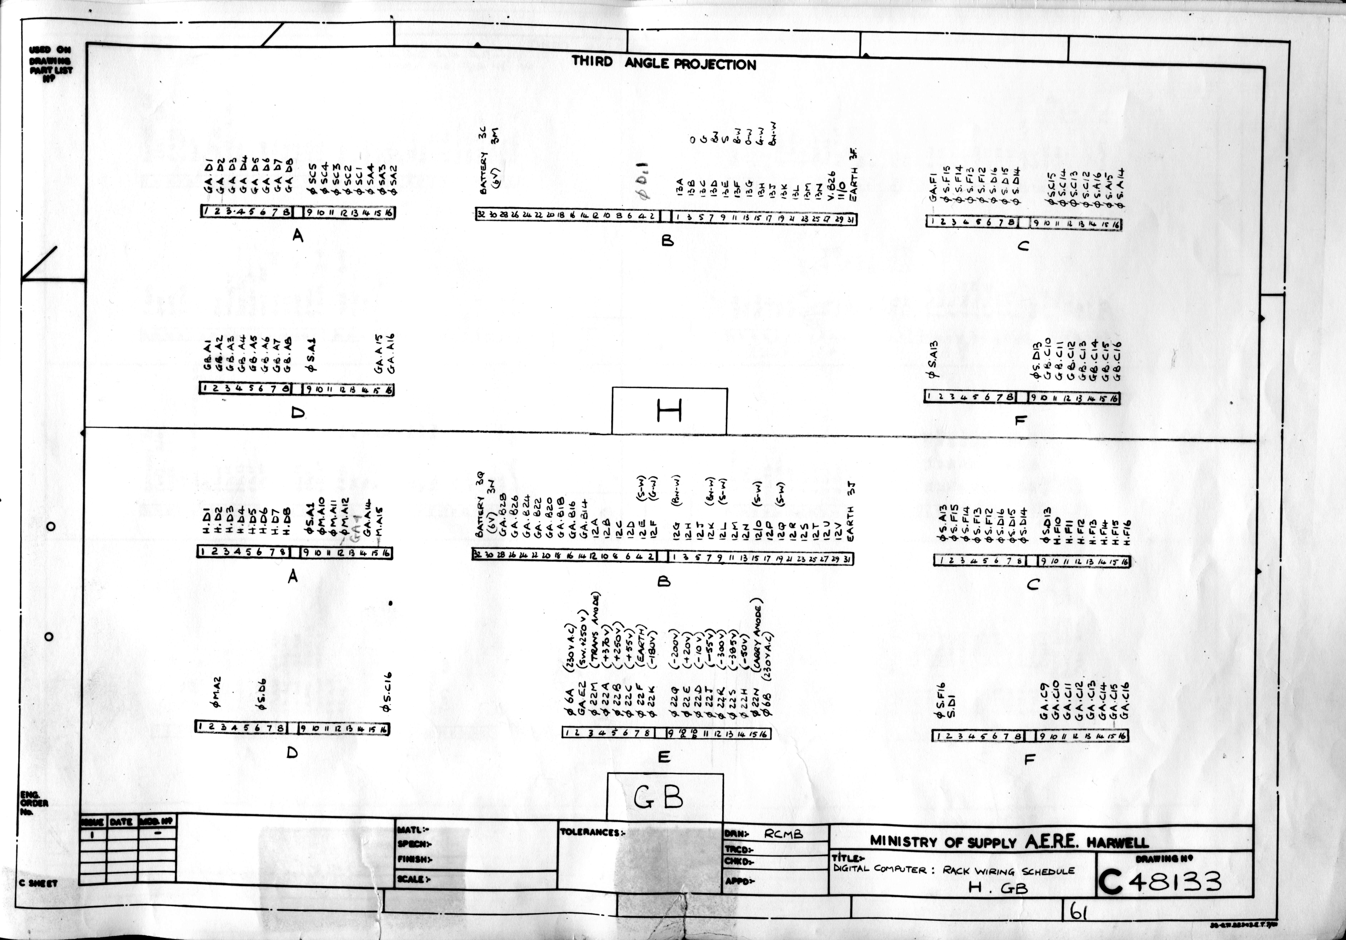
documentation/WITCH-schematics/jpgs/Rack Wiring Schedule H GB - 48133.jpg
