prpplague/witch_dev/documentation/WITCH-schematics/jpgs/Rack Wiring Schedule J L1 L2 M N - 48134.jpg

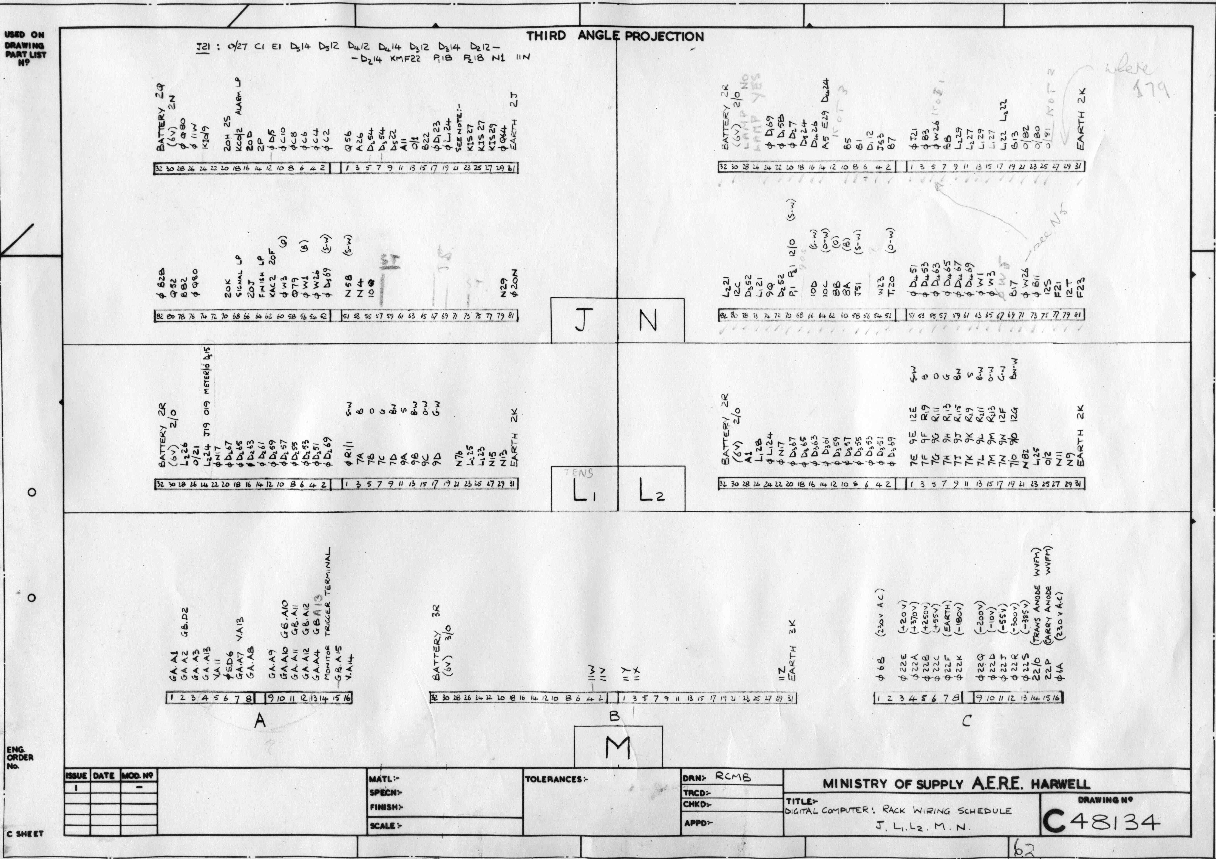
documentation/WITCH-schematics/jpgs/Rack Wiring Schedule J L1 L2 M N - 48134.jpg
