prpplague/witch_dev/documentation/WITCH-schematics/jpgs/Rack Wiring Schedule O P1 P2 Q R1 R2 - 48135.jpg

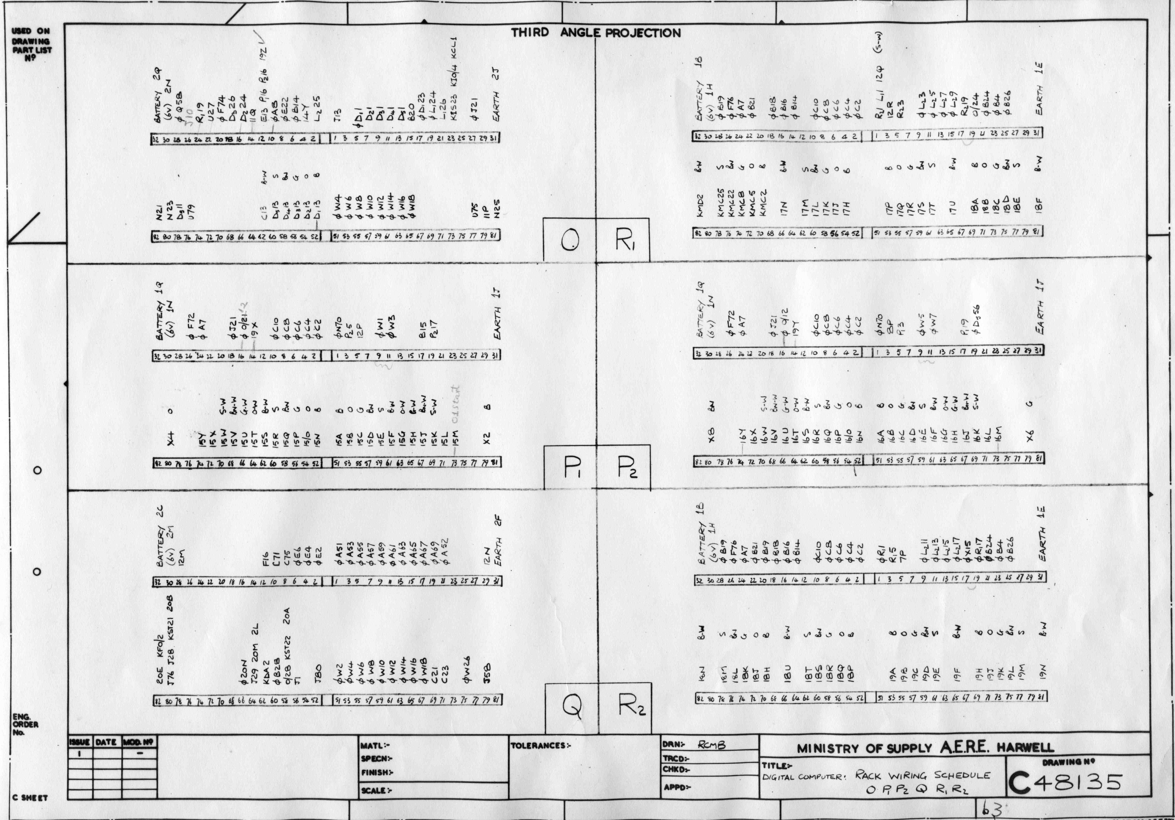
documentation/WITCH-schematics/jpgs/Rack Wiring Schedule O P1 P2 Q R1 R2 - 48135.jpg
