prpplague/witch_dev/documentation/WITCH-schematics/jpgs/Rack Wiring Schedule S T1 T2 - 48136.jpg

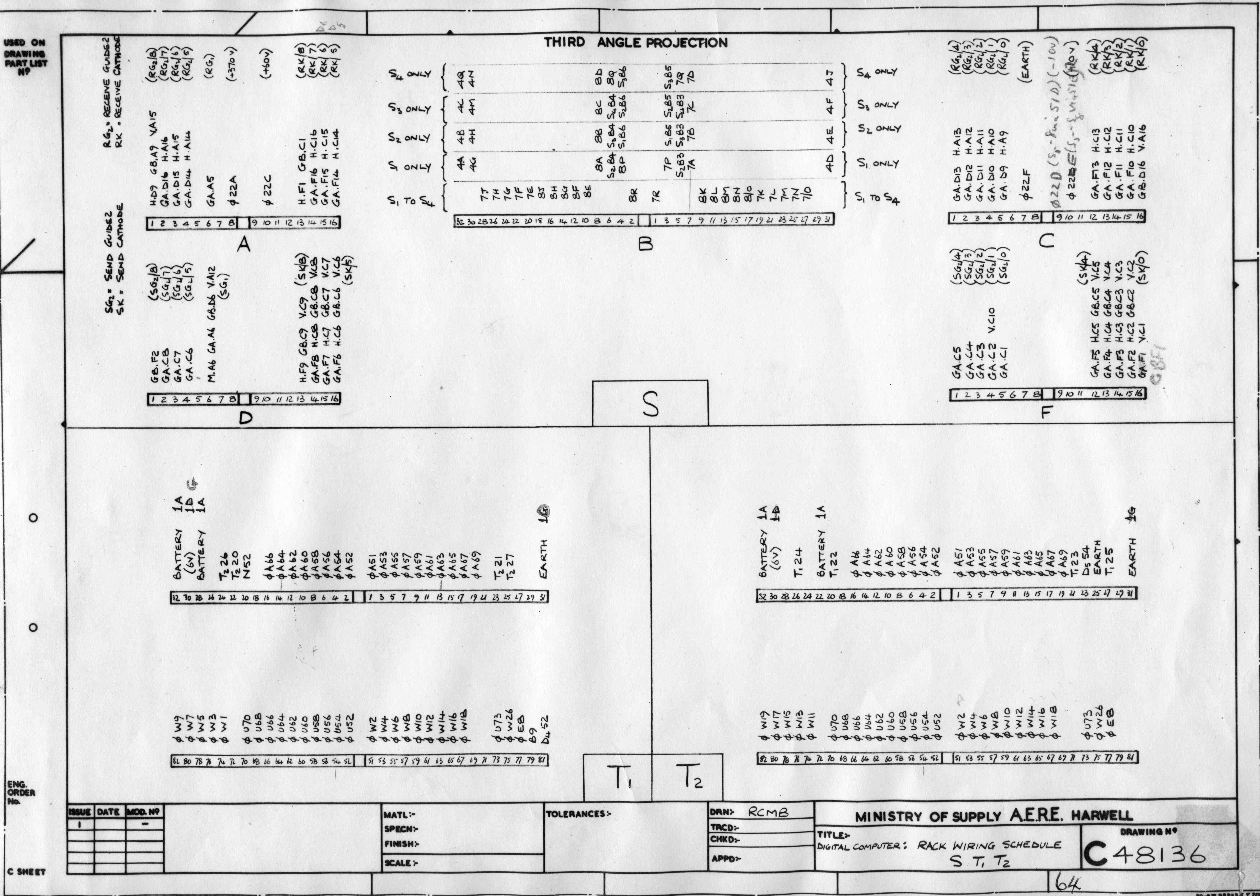
documentation/WITCH-schematics/jpgs/Rack Wiring Schedule S T1 T2 - 48136.jpg
