prpplague/witch_dev/documentation/WITCH-schematics/jpgs/Rack Wiring Schedule U V W X Z - 48137.jpg

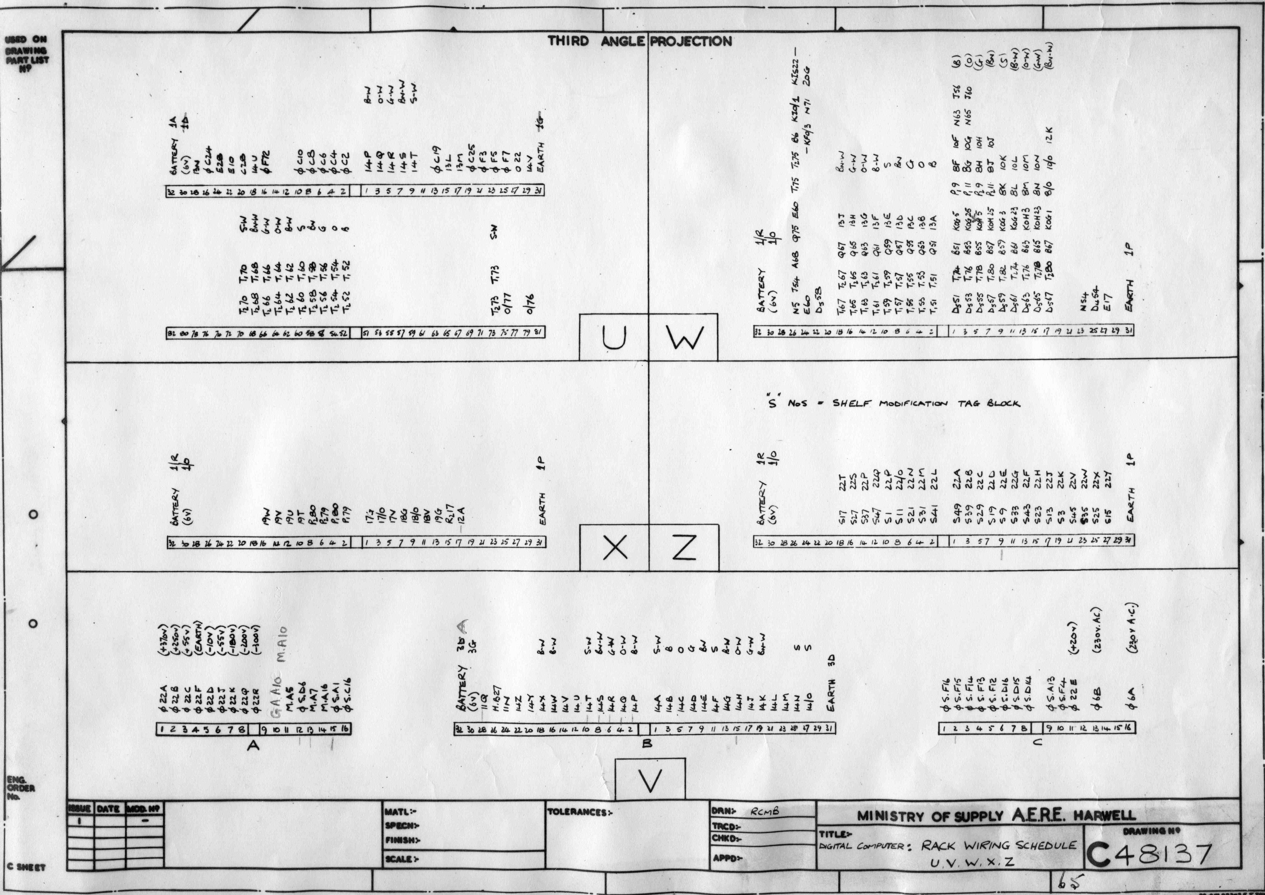
documentation/WITCH-schematics/jpgs/Rack Wiring Schedule U V W X Z - 48137.jpg
