prpplague/witch_dev/block-designs/witch-phase4/tape-reader/test-code/file2.png

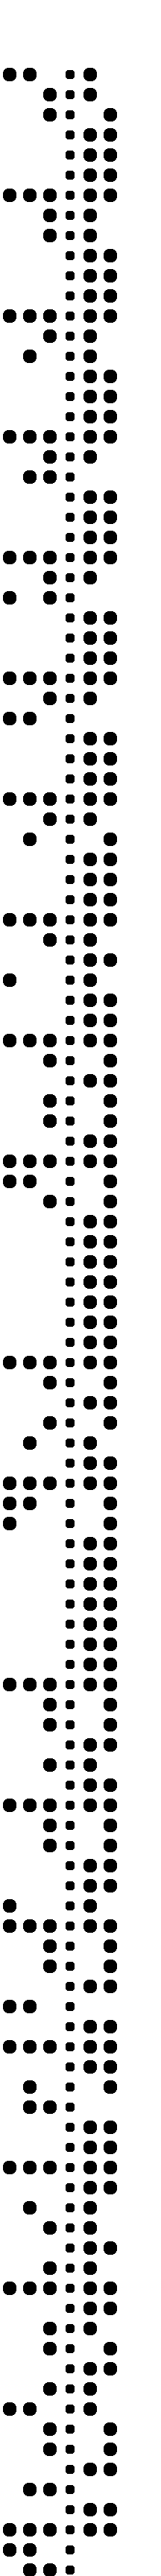
block-designs/witch-phase4/tape-reader/test-code/file2.png
