prpplague/witch_dev/documentation/WITCH-schematics/jpgs/Relay Set X and PSU Test Unit - 47551.jpg

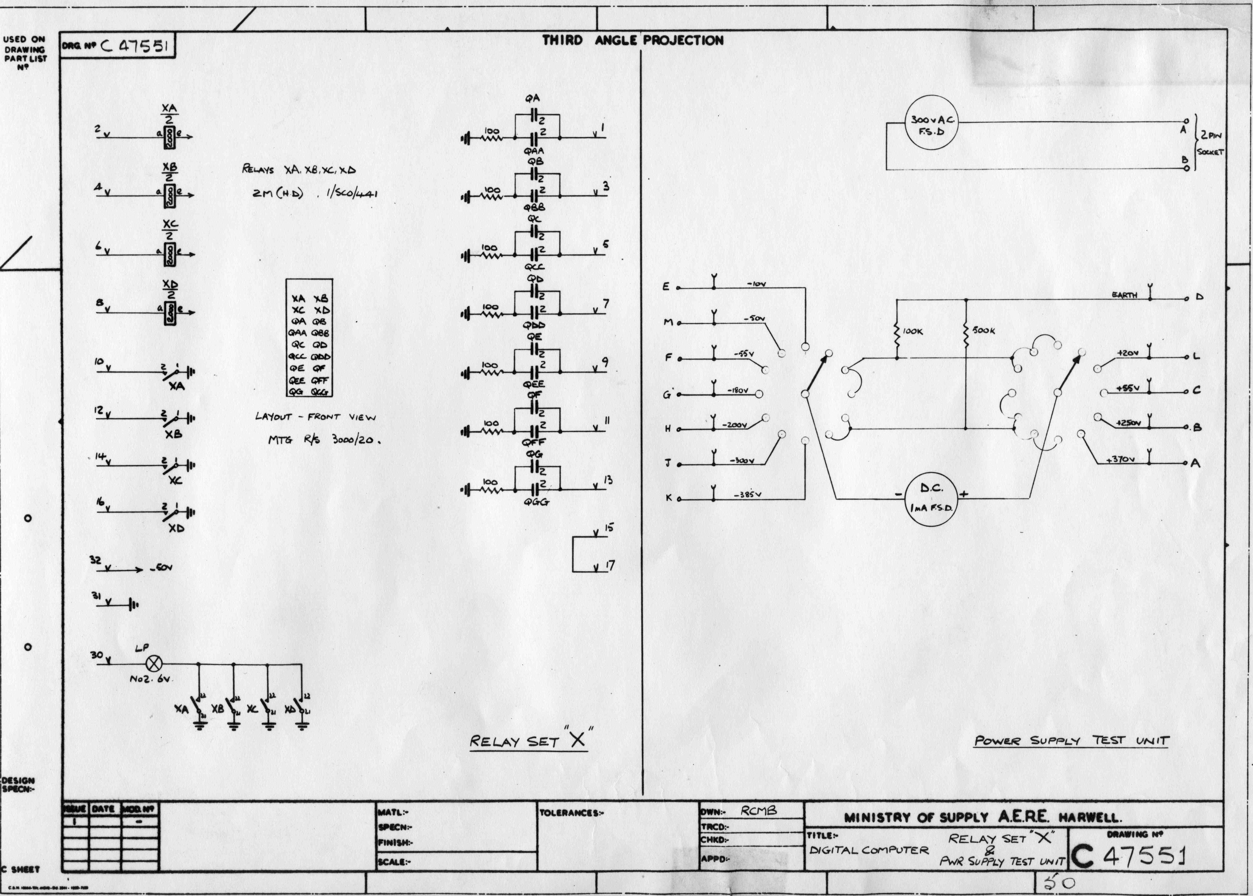
documentation/WITCH-schematics/jpgs/Relay Set X and PSU Test Unit - 47551.jpg
