prpplague/witch_dev/documentation/WITCH-schematics/notes/HDC testing  cables.jpg

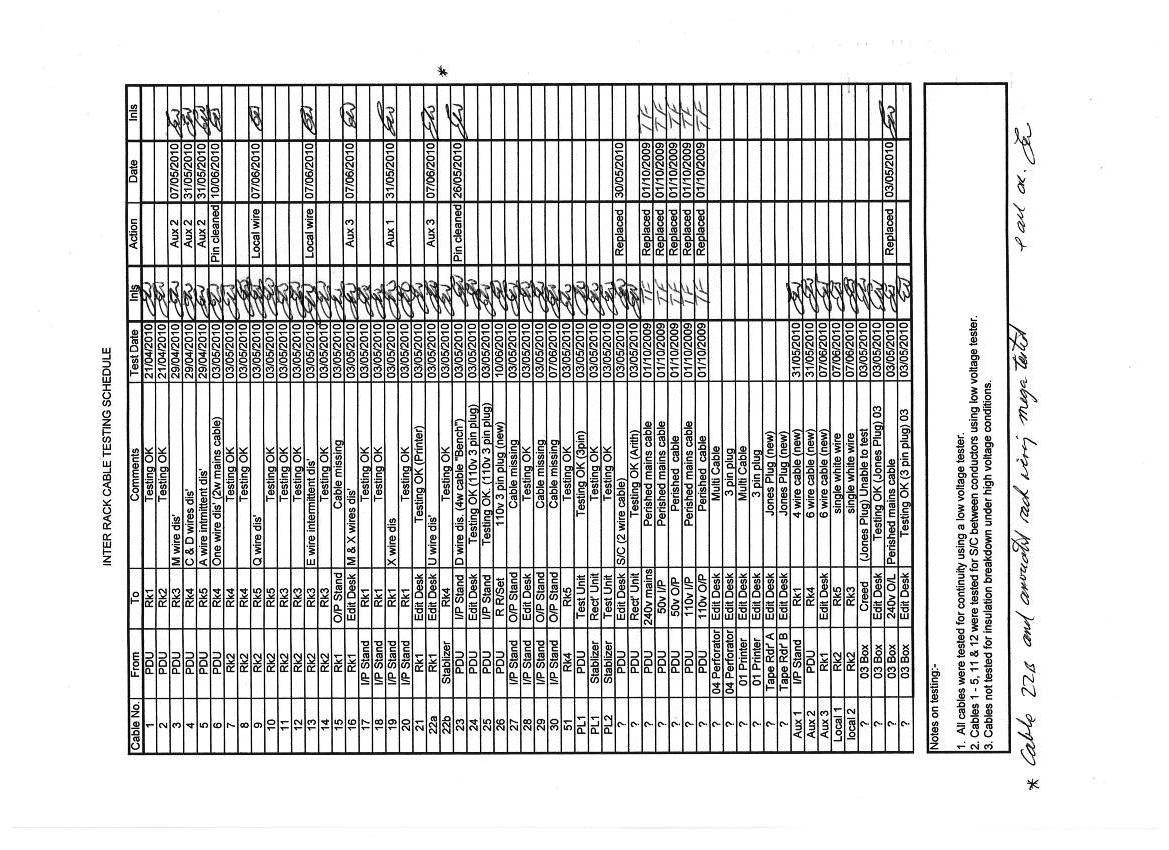
documentation/WITCH-schematics/notes/HDC testing cables.jpg
