prpplague/witch_dev/documentation/WITCH-schematics/misc/Computer Routine Maintenance - 1.jpg

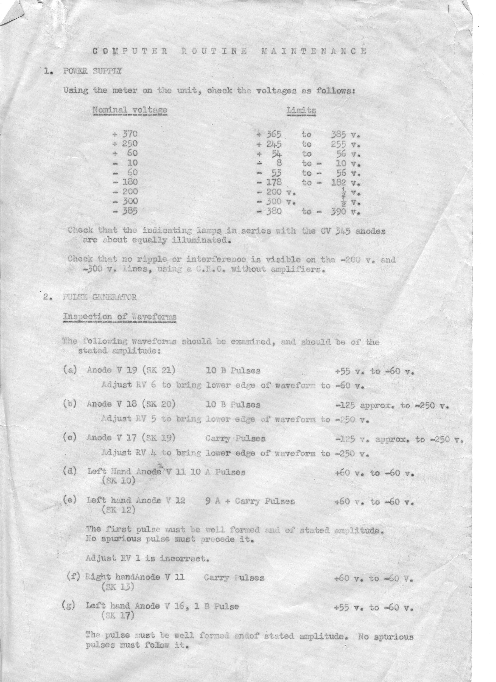
documentation/WITCH-schematics/misc/Computer Routine Maintenance - 1.jpg
