prpplague/witch_dev/documentation/WITCH-schematics/misc/Computer Routine Maintenance - 2.jpg

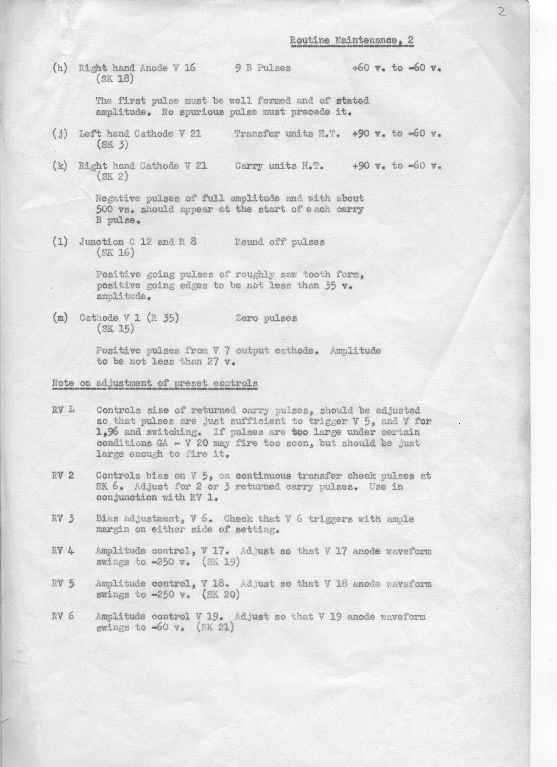
documentation/WITCH-schematics/misc/Computer Routine Maintenance - 2.jpg
