prpplague/witch_dev/documentation/WITCH-schematics/misc/Computer Routine Maintenance - 3.jpg

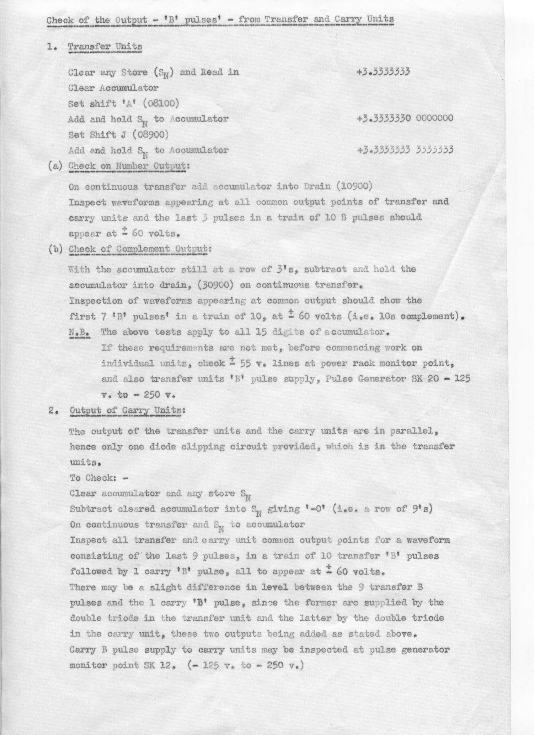
documentation/WITCH-schematics/misc/Computer Routine Maintenance - 3.jpg
