prpplague/witch_dev/documentation/WITCH-schematics/misc/Computer Routine Maintenance - 4.jpg

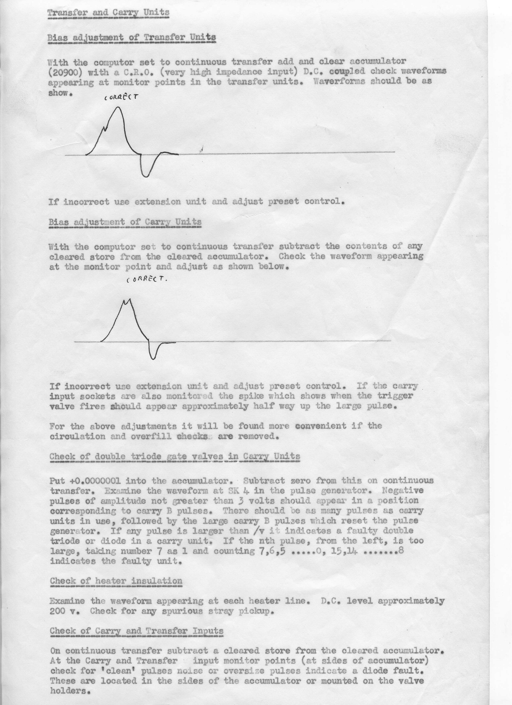
documentation/WITCH-schematics/misc/Computer Routine Maintenance - 4.jpg
