prpplague/witch_dev/documentation/WITCH-schematics/misc/Computer Routine Maintenance - 5.jpg

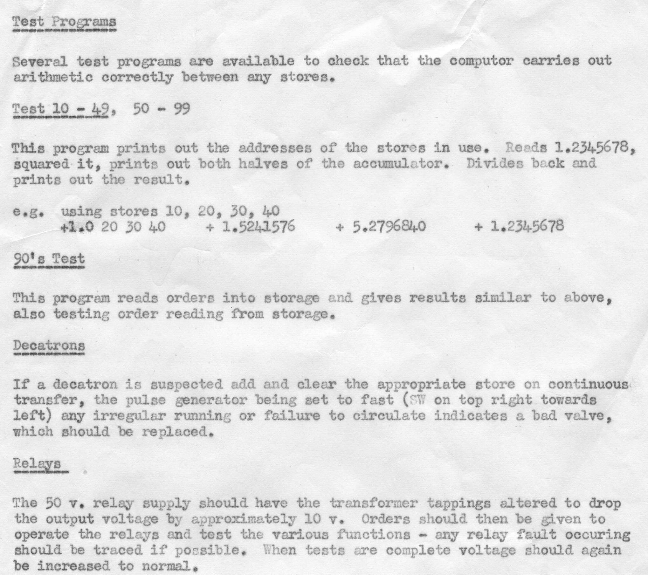
documentation/WITCH-schematics/misc/Computer Routine Maintenance - 5.jpg
