prpplague/witch_dev/block-designs/witch-phase1/dekatron/witch-dekatron1.pdf

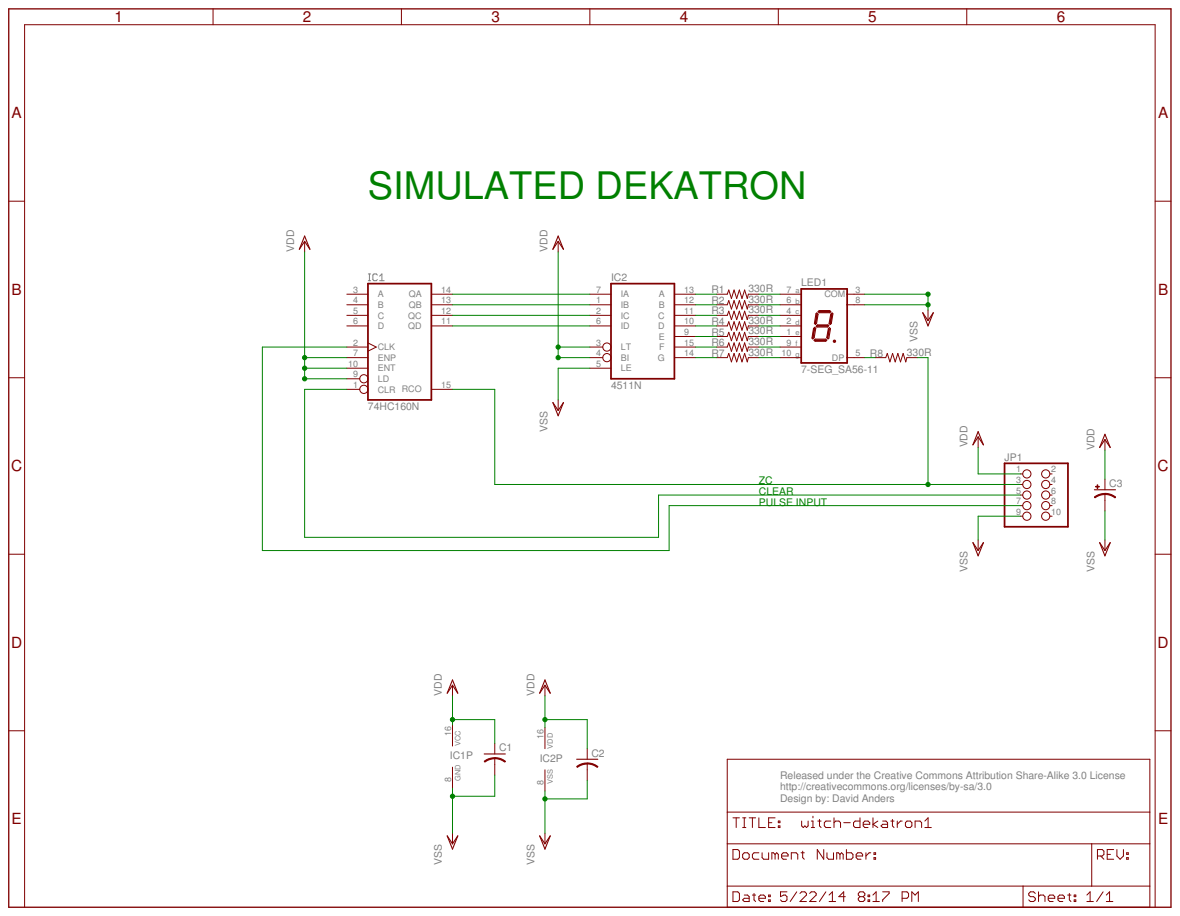
[picture p272: page 1]

Released under the Creative Commons Attribution Share-Alike 3.0 License
http://creativecommons.org/licenses/by-sa/3.0
Design by: David Anders
