prpplague/witch_dev/block-designs/witch-phase2/relay-set-d/relay-set-d-small-blocks/relay-set-d-decode-full/relay-set-d-decode.brd

## EAGLE design block-designs/witch-phase2/relay-set-d/relay-set-d-small-blocks/relay-set-d-decode-full/relay-set-d-decode.brd (2017-02-21, an earlier design)

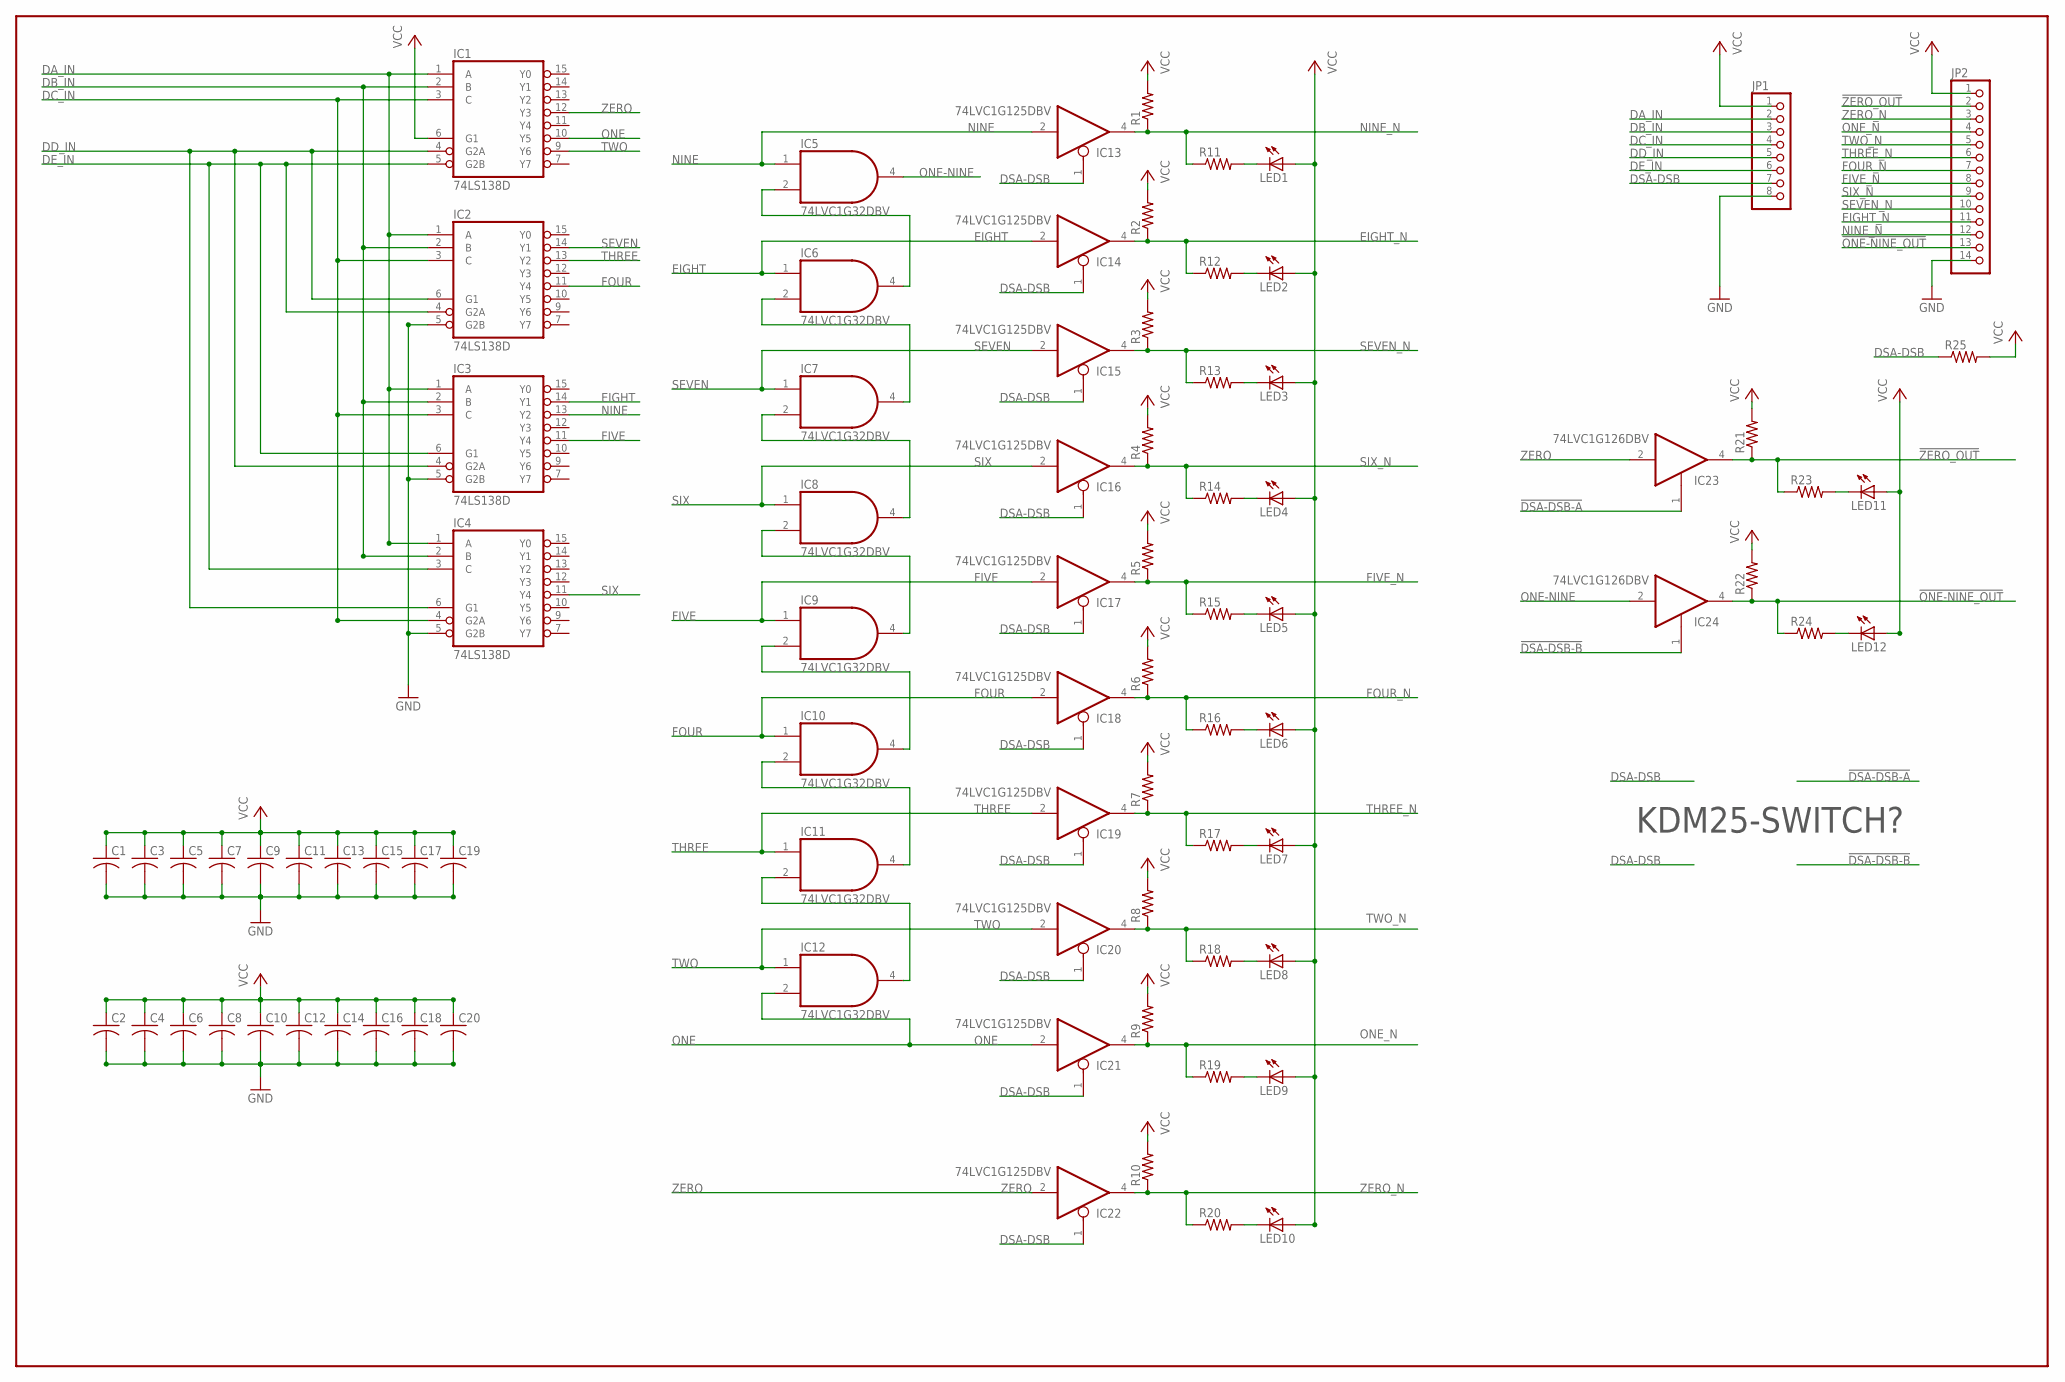
[picture p301: schematic relay-set-d-decode.sch]

Parts:
C1, C2, C3, C4, C5, C6, C7, C8, C9, C10, C11, C12, C13, C14, C15, C16, C17, C18, C19, C20: C-USC0805; C0805
IC1, IC2, IC3, IC4: 74LS138D; SO16
IC5, IC6, IC7, IC8, IC9, IC10, IC11, IC12: 74LVC1G32DBV; SOT23-5
IC13, IC14, IC15, IC16, IC17, IC18, IC19, IC20, IC21, IC22: 74LVC1G125DBV; SOT23-5
IC23, IC24: 74LVC1G126DBV; SOT23-5
JP1: PINHD-1X8; 1X08
JP2: PINHD-1X14; 1X14
LED1, LED2, LED3, LED4, LED5, LED6, LED7, LED8, LED9, LED10, LED11, LED12: LEDCHIP-LED0805; CHIP-LED0805
R1, R2, R3, R4, R5, R6, R7, R8, R9, R10, R11, R12, R13, R14, R15, R16, R17, R18, R19, R20, R21, R22, R23, R24, R25: R-US_R0805; R0805

Connections:
!DSA-DSB-A: IC23.1 (OE)
!DSA-DSB-B: IC24.1 (OE)
!ONE-NINE_OUT: IC24.4 (O), JP2.13, R22.1, R24.1
!ZERO_OUT: IC23.4 (O), JP2.2, R21.1, R23.1
DA_IN: IC1.1 (A), IC2.1 (A), IC3.1 (A), IC4.1 (A), JP1.2
DB_IN: IC1.2 (B), IC2.2 (B), IC3.2 (B), IC4.2 (B), JP1.3
DC_IN: IC1.3 (C), IC2.3 (C), IC3.3 (C), IC4.4 (G2A), JP1.4
DD_IN: IC1.4 (G2A), IC2.6 (G1), IC3.4 (G2A), IC4.6 (G1), JP1.5
DE_IN: IC1.5 (G2B), IC2.4 (G2A), IC3.6 (G1), IC4.3 (C), JP1.6
DSA-DSB: IC13.1 (OE), IC14.1 (OE), IC15.1 (OE), IC16.1 (OE), IC17.1 (OE), IC18.1 (OE), IC19.1 (OE), IC20.1 (OE), IC21.1 (OE), IC22.1 (OE), JP1.7, R25.1
EIGHT: IC3.14 (Y1), IC6.1 (I0), IC14.2 (I)
EIGHT_N: IC14.4 (O), JP2.11, R2.1, R12.1
FIVE: IC3.11 (Y4), IC9.1 (I0), IC17.2 (I)
FIVE_N: IC17.4 (O), JP2.8, R5.1, R15.1
FOUR: IC2.11 (Y4), IC10.1 (I0), IC18.2 (I)
FOUR_N: IC18.4 (O), JP2.7, R6.1, R16.1
GND: C1.2, C2.2, C3.2, C4.2, C5.2, C6.2, C7.2, C8.2, C9.2, C10.2, C11.2, C12.2, C13.2, C14.2, C15.2, C16.2, C17.2, C18.2, C19.2, C20.2, IC1.8 (GND), IC2.5 (G2B), IC2.8 (GND), IC3.5 (G2B), IC3.8 (GND), IC4.5 (G2B), IC4.8 (GND), IC5.3 (GND), IC6.3 (GND), IC7.3 (GND), IC8.3 (GND), IC9.3 (GND), IC10.3 (GND), IC11.3 (GND), IC12.3 (GND), IC13.3 (GND), IC14.3 (GND), IC15.3 (GND), IC16.3 (GND), IC17.3 (GND), IC18.3 (GND), IC19.3 (GND), IC20.3 (GND), IC21.3 (GND), IC22.3 (GND), IC23.3 (GND), IC24.3 (GND), JP1.8, JP2.14
unnamed: LED1.C, R11.2
unnamed: LED2.C, R12.2
unnamed: LED3.C, R13.2
unnamed: LED4.C, R14.2
unnamed: LED5.C, R15.2
unnamed: LED6.C, R16.2
unnamed: LED7.C, R17.2
unnamed: LED8.C, R18.2
unnamed: LED9.C, R19.2
unnamed: LED10.C, R20.2
unnamed: IC8.2 (I1), IC9.4 (O)
unnamed: IC9.2 (I1), IC10.4 (O)
unnamed: IC10.2 (I1), IC11.4 (O)
unnamed: IC11.2 (I1), IC12.4 (O)
unnamed: LED11.C, R23.2
unnamed: IC5.2 (I1), IC6.4 (O)
unnamed: IC6.2 (I1), IC7.4 (O)
unnamed: IC7.2 (I1), IC8.4 (O)
unnamed: LED12.C, R24.2
NINE: IC3.13 (Y2), IC5.1 (I0), IC13.2 (I)
NINE_N: IC13.4 (O), JP2.12, R1.1, R11.1
ONE: IC1.10 (Y5), IC12.2 (I1), IC21.2 (I)
ONE-NINE: IC5.4 (O), IC24.2 (I)
ONE_N: IC21.4 (O), JP2.4, R9.1, R19.1
SEVEN: IC2.14 (Y1), IC7.1 (I0), IC15.2 (I)
SEVEN_N: IC15.4 (O), JP2.10, R3.1, R13.1
SIX: IC4.11 (Y4), IC8.1 (I0), IC16.2 (I)
SIX_N: IC16.4 (O), JP2.9, R4.1, R14.1
THREE: IC2.13 (Y2), IC11.1 (I0), IC19.2 (I)
THREE_N: IC19.4 (O), JP2.6, R7.1, R17.1
TWO: IC1.9 (Y6), IC12.1 (I0), IC20.2 (I)
TWO_N: IC20.4 (O), JP2.5, R8.1, R18.1
VCC: C1.1, C2.1, C3.1, C4.1, C5.1, C6.1, C7.1, C8.1, C9.1, C10.1, C11.1, C12.1, C13.1, C14.1, C15.1, C16.1, C17.1, C18.1, C19.1, C20.1, IC1.6 (G1), IC1.16 (VCC), IC2.16 (VCC), IC3.16 (VCC), IC4.16 (VCC), IC5.5 (VCC), IC6.5 (VCC), IC7.5 (VCC), IC8.5 (VCC), IC9.5 (VCC), IC10.5 (VCC), IC11.5 (VCC), IC12.5 (VCC), IC13.5 (VCC), IC14.5 (VCC), IC15.5 (VCC), IC16.5 (VCC), IC17.5 (VCC), IC18.5 (VCC), IC19.5 (VCC), IC20.5 (VCC), IC21.5 (VCC), IC22.5 (VCC), IC23.5 (VCC), IC24.5 (VCC), JP1.1, JP2.1, LED1.A, LED2.A, LED3.A, LED4.A, LED5.A, LED6.A, LED7.A, LED8.A, LED9.A, LED10.A, LED11.A, LED12.A, R1.2, R2.2, R3.2, R4.2, R5.2, R6.2, R7.2, R8.2, R9.2, R10.2, R21.2, R22.2, R25.2
ZERO: IC1.12 (Y3), IC22.2 (I), IC23.2 (I)
ZERO_N: IC22.4 (O), JP2.3, R10.1, R20.1

Notes on the sheet:
KDM25-SWITCH?

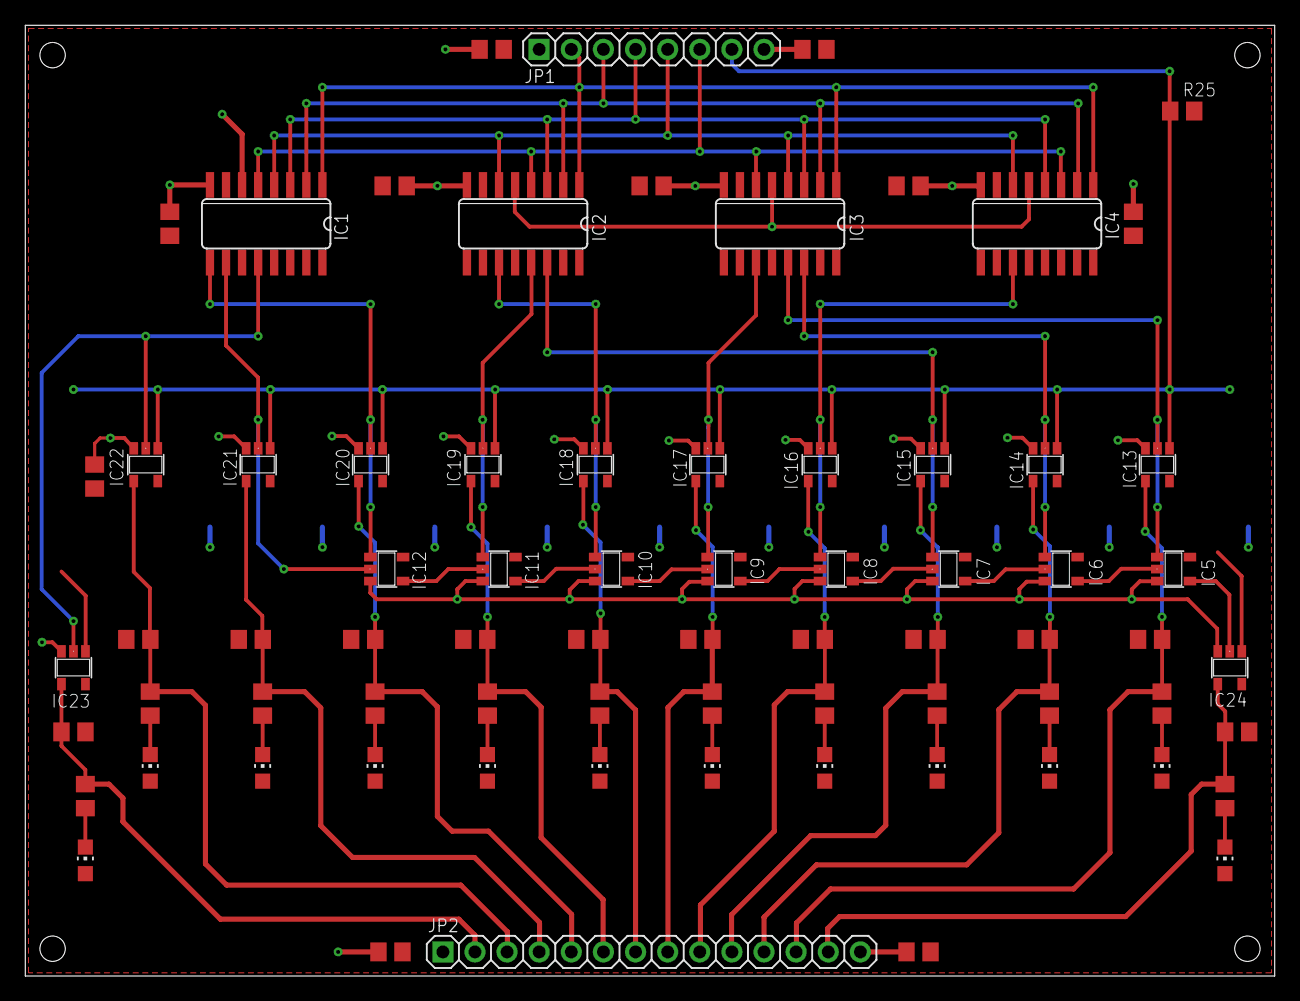
[picture p302: board block-designs/witch-phase2/relay-set-d/relay-set-d-small-blocks/relay… from above]

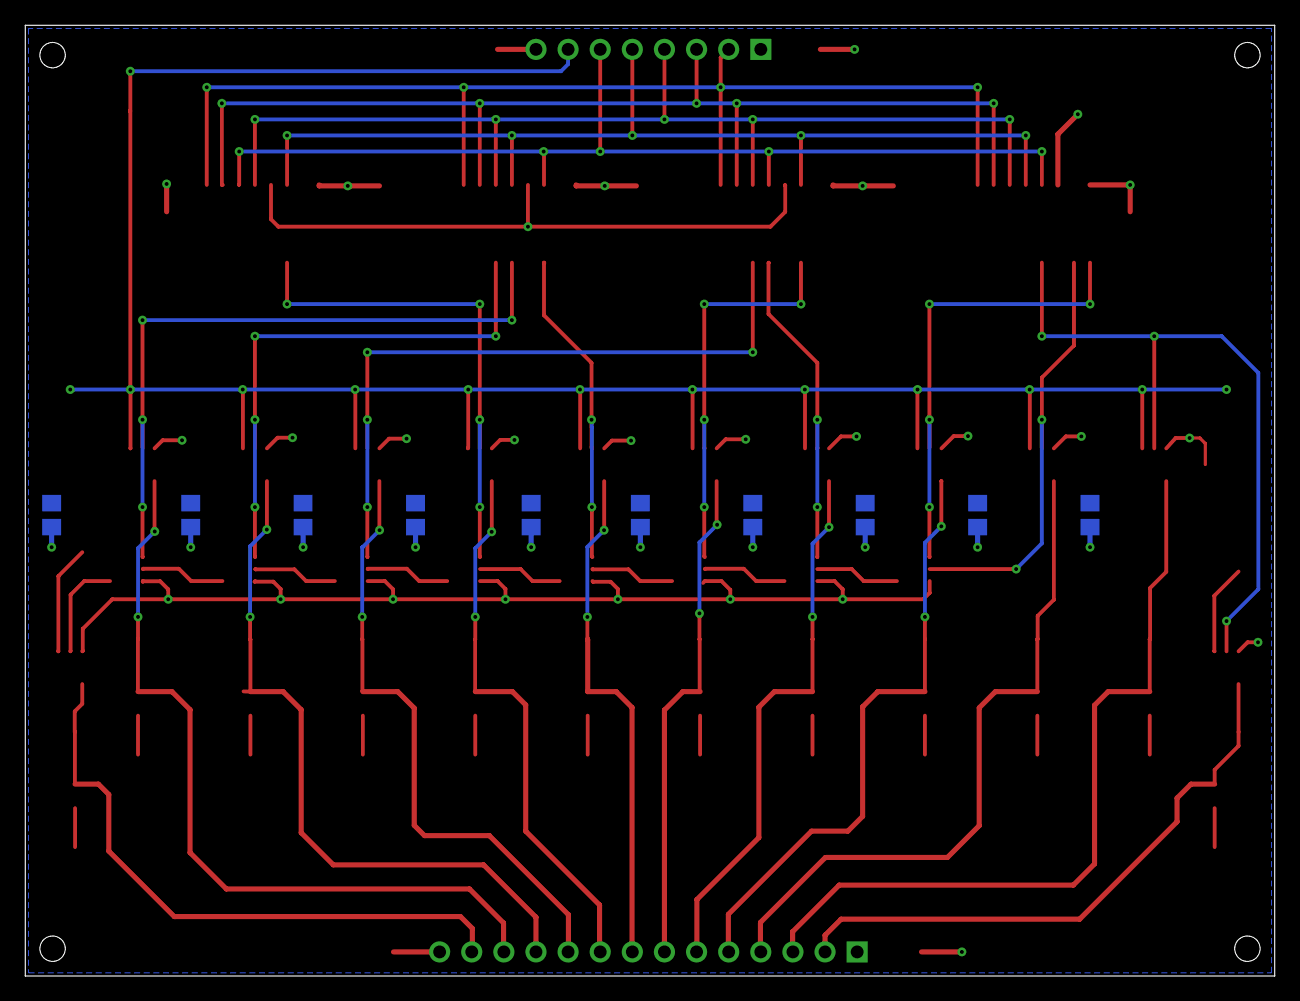
[picture p303: board block-designs/witch-phase2/relay-set-d/relay-set-d-small-blocks/relay… from below]

Board: 2 copper layers, 98.8 x 75.2 mm, 83 parts (10 on the bottom side), 50 nets.
