prpplague/witch_dev/block-designs/witch-phase2/interconnects/transfer-interconnect/transfer-interconnect.brd

## EAGLE design block-designs/witch-phase2/interconnects/transfer-interconnect/transfer-interconnect.brd (2017-02-14)

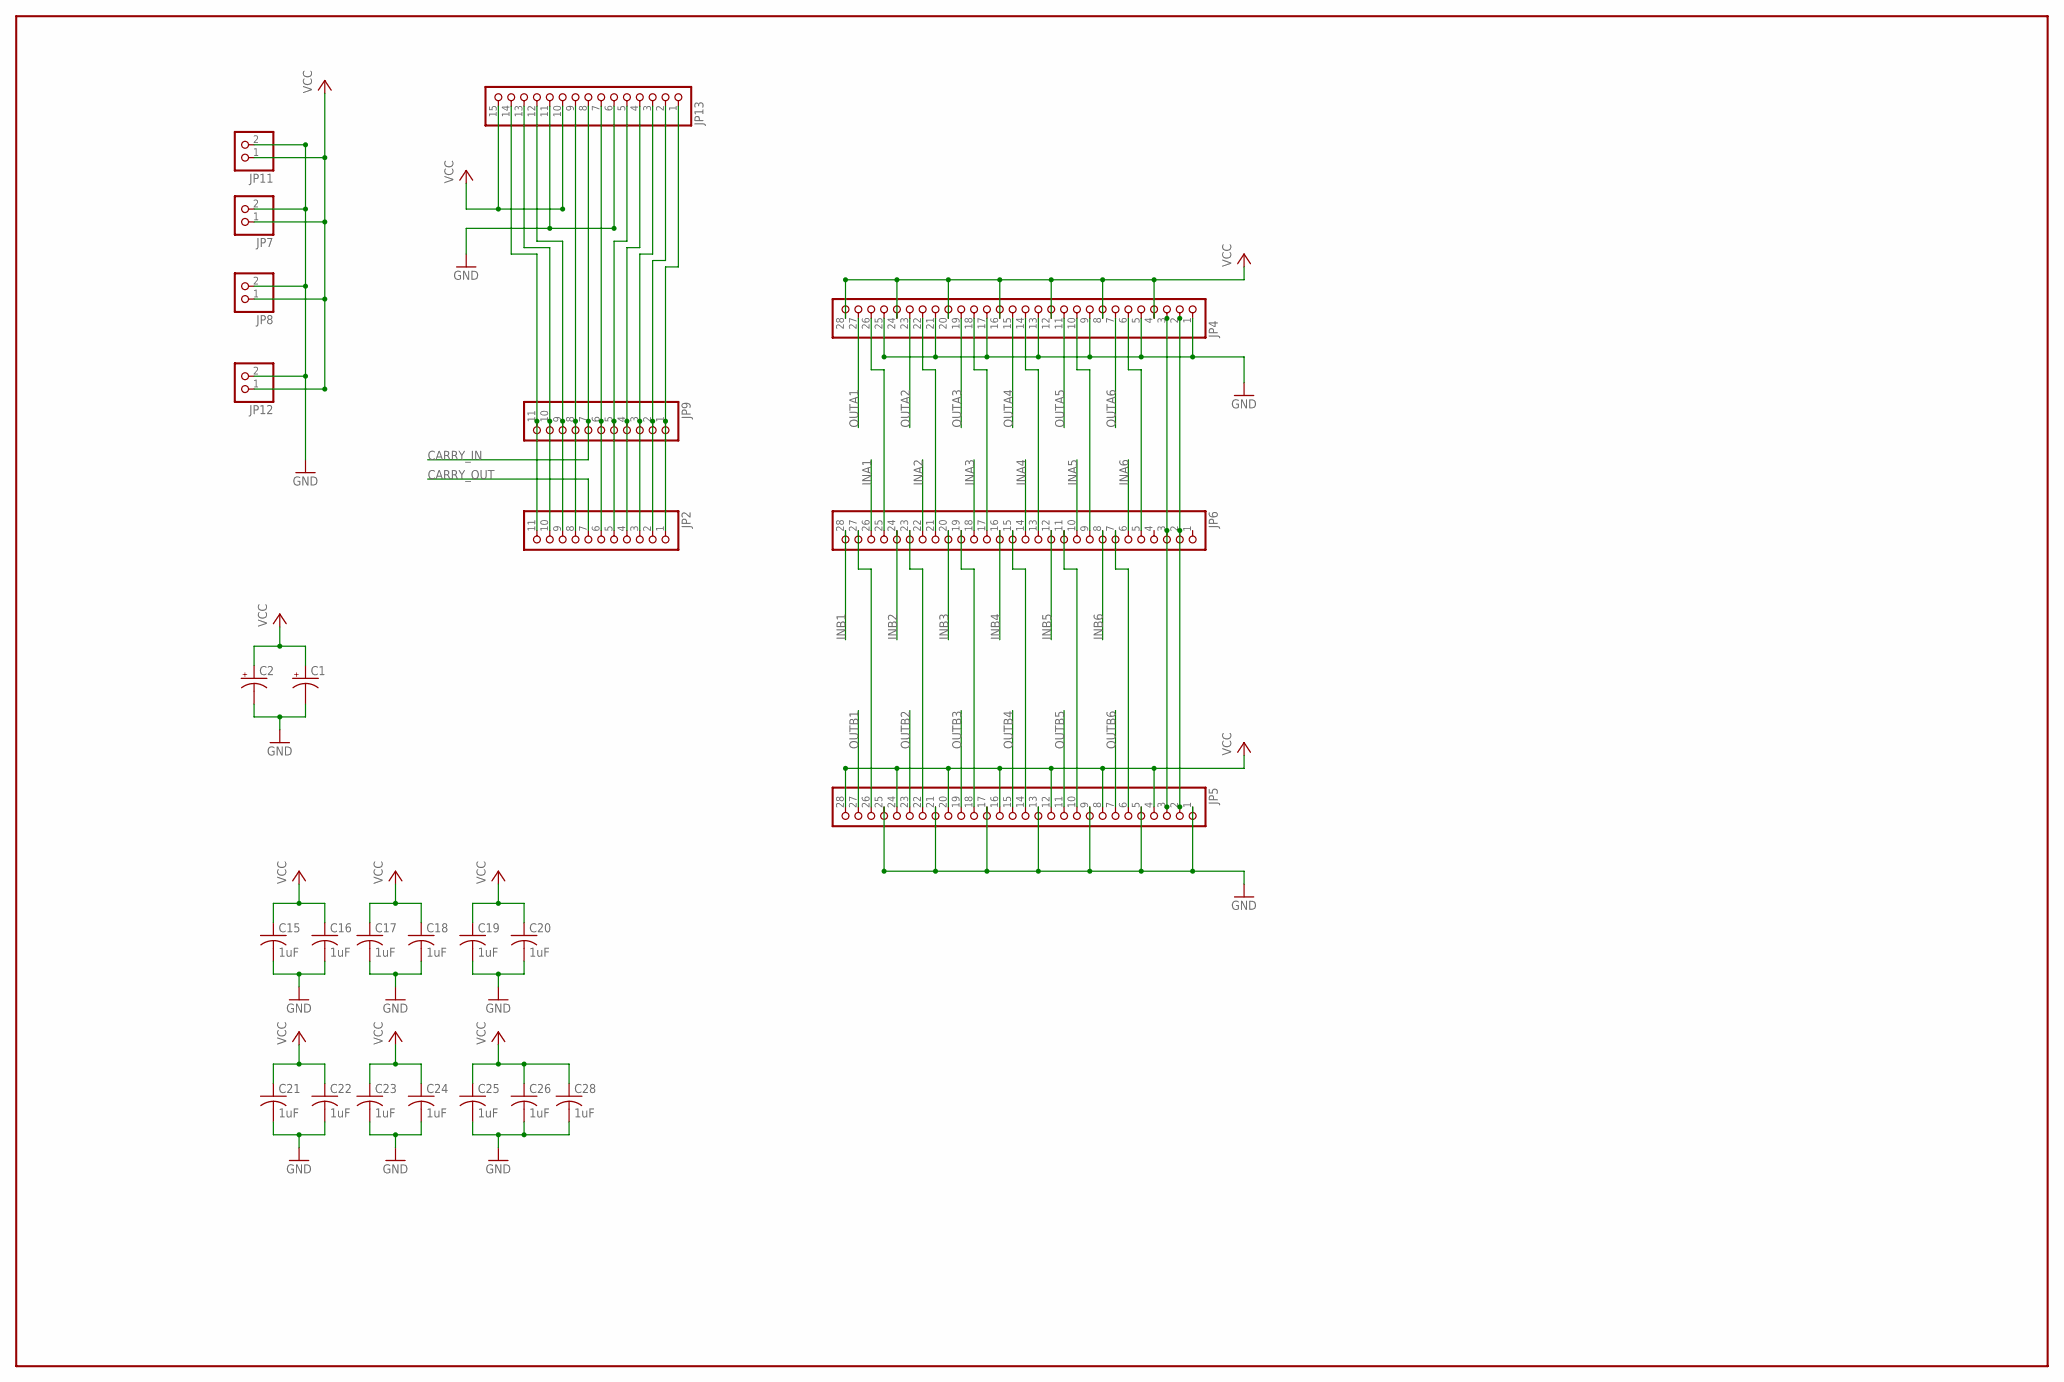
[picture p304: schematic transfer-interconnect.sch, sheet 1]

Parts:
C1, C2: CPOL-USE15-6AXIAL; E15-6
C15, C16, C17, C18, C19, C20, C21, C22, C23, C24, C25, C26, C28: 1uF; C0603K
JP2, JP9: PINHD-1X11; 1X11
JP4, JP5, JP6: PINHD-1X28; 1X28
JP7, JP8, JP11, JP12: PINHD-1X2; 1X02
JP13: PINHD-1X15; 1X15

Connections:
CARRY_IN: JP9.7, JP13.8; also elsewhere on the board
CARRY_OUT: JP2.7; also elsewhere on the board
GND: C1.-, C2.-, C15.2, C16.2, C17.2, C18.2, C19.2, C20.2, C21.2, C22.2, C23.2, C24.2, C25.2, C26.2, C28.2, JP4.1, JP4.5, JP4.9, JP4.13, JP4.17, JP4.21, JP4.25, JP5.1, JP5.5, JP5.9, JP5.13, JP5.17, JP5.21, JP5.25, JP7.2, JP8.2, JP11.2, JP12.2, JP13.6, JP13.11; also elsewhere on the board
INA1: JP6.26; also elsewhere on the board
INA2: JP6.22; also elsewhere on the board
INA3: JP6.18; also elsewhere on the board
INA4: JP6.14; also elsewhere on the board
INA5: JP6.10; also elsewhere on the board
INA6: JP6.6; also elsewhere on the board
INB1: JP6.28; also elsewhere on the board
INB2: JP6.24; also elsewhere on the board
INB3: JP6.20; also elsewhere on the board
INB4: JP6.16; also elsewhere on the board
INB5: JP6.12; also elsewhere on the board
INB6: JP6.8; also elsewhere on the board
unnamed: JP4.3, JP5.3, JP6.3
unnamed: JP4.2, JP5.2, JP6.2
unnamed: JP4.10, JP6.9
unnamed: JP2.8, JP9.8, JP13.9
unnamed: JP4.6, JP6.5
unnamed: JP4.14, JP6.13
unnamed: JP2.6, JP9.6, JP13.7
unnamed: JP4.18, JP6.17
unnamed: JP4.22, JP6.21
unnamed: JP4.26, JP6.25
unnamed: JP5.6, JP6.7
unnamed: JP5.10, JP6.11
unnamed: JP5.14, JP6.15
unnamed: JP5.18, JP6.19
unnamed: JP5.22, JP6.23
unnamed: JP5.26, JP6.27
unnamed: JP2.11, JP9.11, JP13.14
unnamed: JP2.10, JP9.10, JP13.13
unnamed: JP2.9, JP9.9, JP13.12
unnamed: JP2.5, JP9.5, JP13.5
unnamed: JP2.4, JP9.4, JP13.4
unnamed: JP2.3, JP9.3, JP13.3
unnamed: JP2.2, JP9.2, JP13.2
unnamed: JP2.1, JP9.1, JP13.1
OUTA1: JP4.27; also elsewhere on the board
OUTA2: JP4.23; also elsewhere on the board
OUTA3: JP4.19; also elsewhere on the board
OUTA4: JP4.15; also elsewhere on the board
OUTA5: JP4.11; also elsewhere on the board
OUTA6: JP4.7; also elsewhere on the board
OUTB1: JP5.27; also elsewhere on the board
OUTB2: JP5.23; also elsewhere on the board
OUTB3: JP5.19; also elsewhere on the board
OUTB4: JP5.15; also elsewhere on the board
OUTB5: JP5.11; also elsewhere on the board
OUTB6: JP5.7; also elsewhere on the board
VCC: C1.+, C2.+, C15.1, C16.1, C17.1, C18.1, C19.1, C20.1, C21.1, C22.1, C23.1, C24.1, C25.1, C26.1, C28.1, JP4.4, JP4.8, JP4.12, JP4.16, JP4.20, JP4.24, JP4.28, JP5.4, JP5.8, JP5.12, JP5.16, JP5.20, JP5.24, JP5.28, JP7.1, JP8.1, JP11.1, JP12.1, JP13.10, JP13.15; also elsewhere on the board
