prpplague/witch_dev/block-designs/witch-phase2/interconnects/transfer-interconnect/transfer-interconnect.brd

## EAGLE design block-designs/witch-phase2/interconnects/transfer-interconnect/transfer-interconnect.brd (continued)

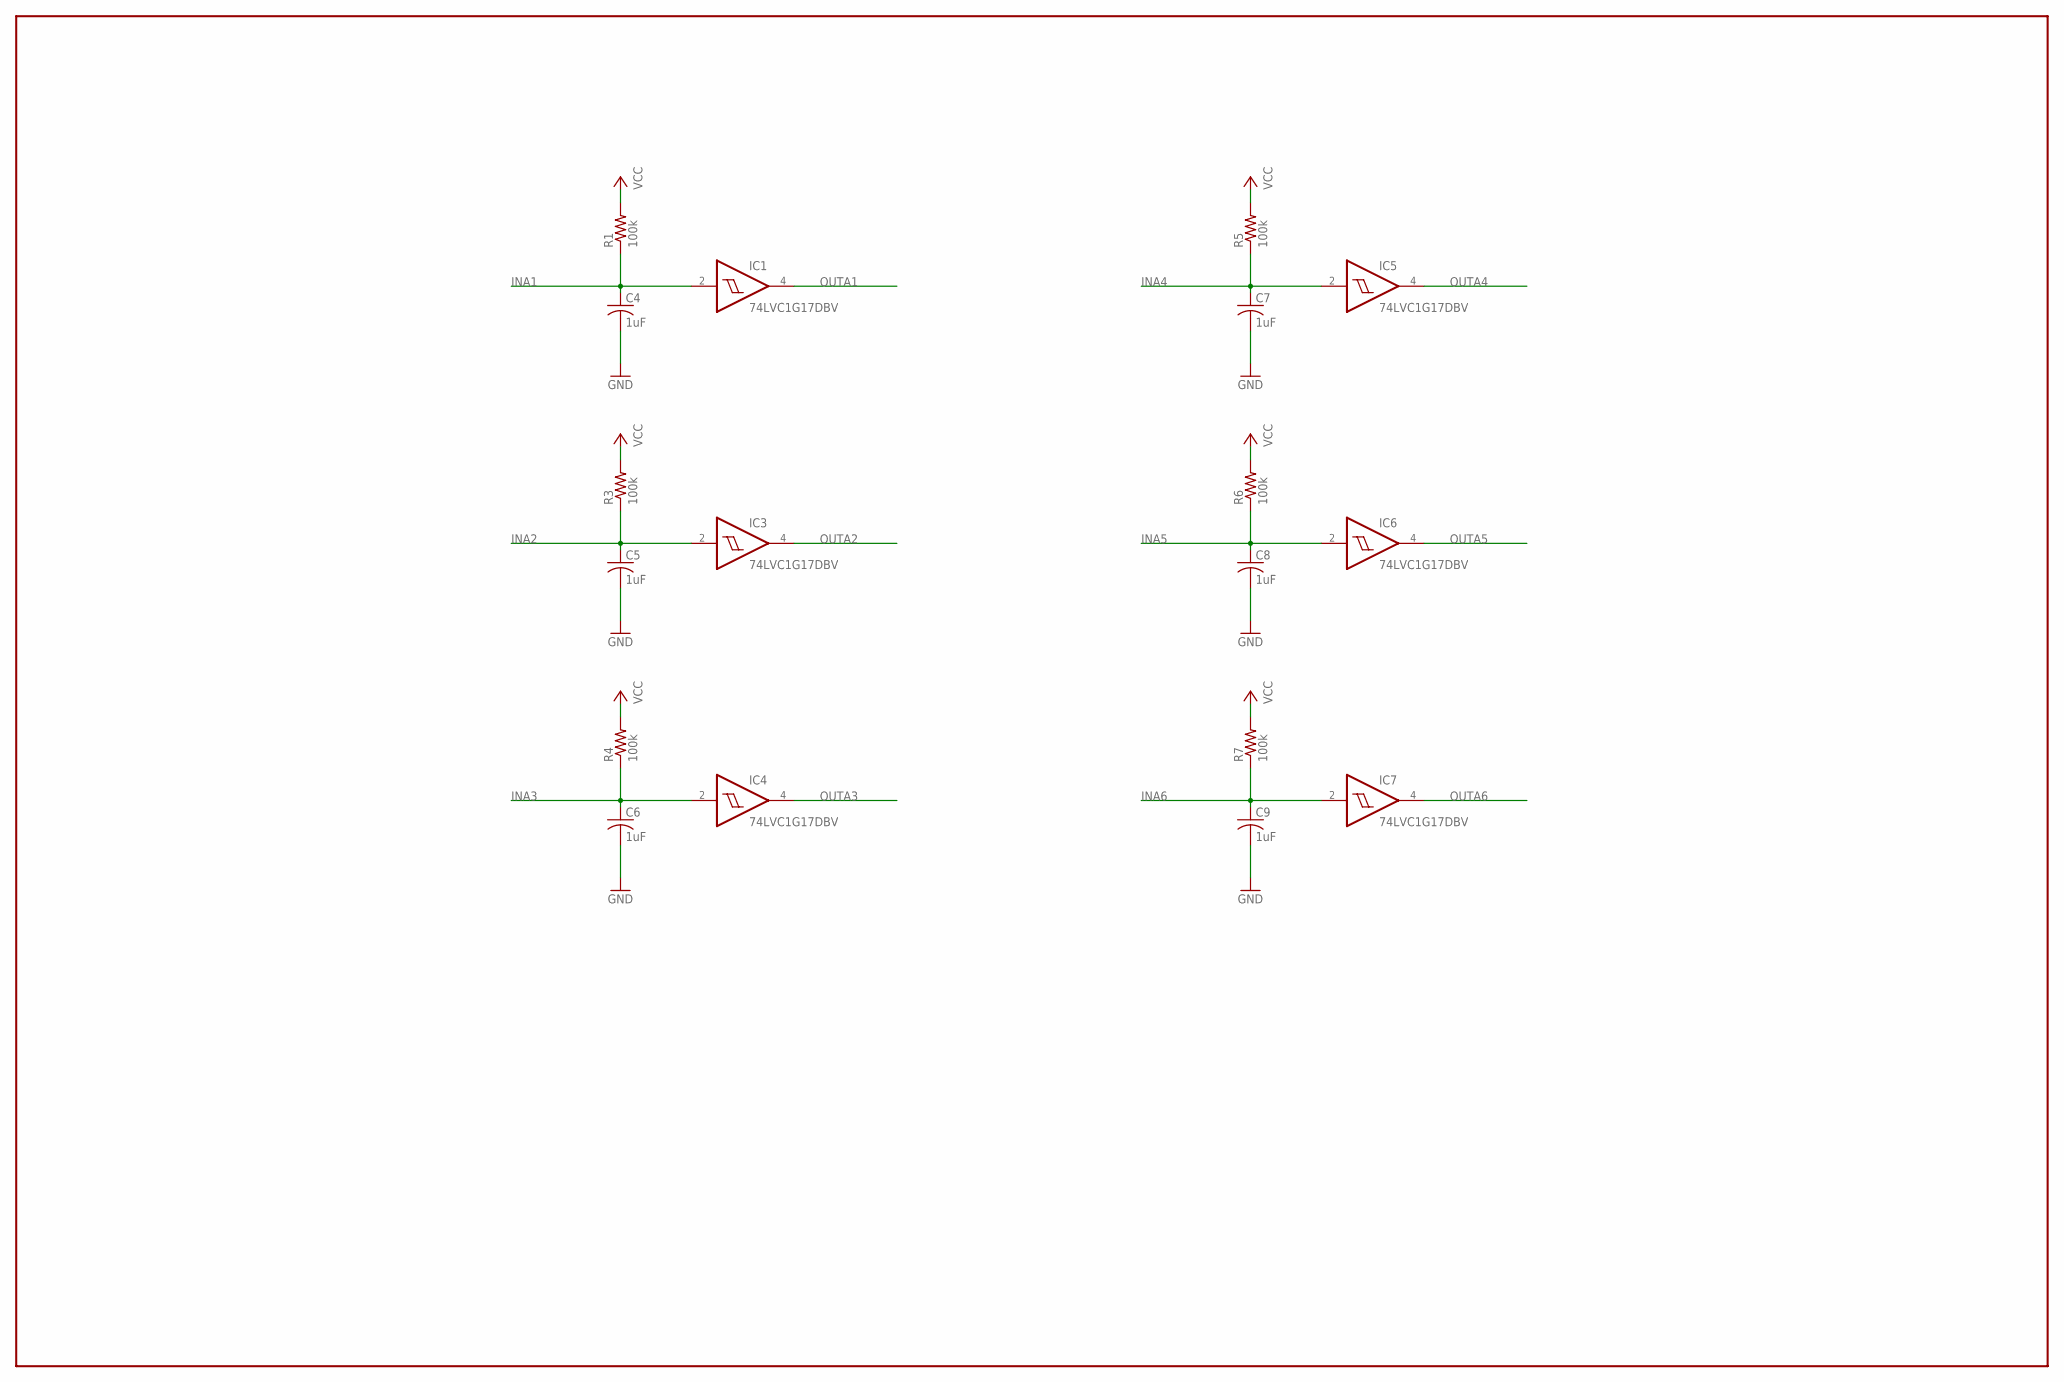
[picture p305: schematic transfer-interconnect.sch, sheet 2]

Parts:
C4, C5, C6, C7, C8, C9: 1uF; C0603K
IC1, IC3, IC4, IC5, IC6, IC7: 74LVC1G17DBV; SOT23-5
R1, R3, R4, R5, R6, R7: 100k; R0603

Connections:
GND: C4.2, C5.2, C6.2, C7.2, C8.2, C9.2, IC1.3 (GND), IC3.3 (GND), IC4.3 (GND), IC5.3 (GND), IC6.3 (GND), IC7.3 (GND); also elsewhere on the board
INA1: C4.1, IC1.2 (I), R1.1; also elsewhere on the board
INA2: C5.1, IC3.2 (I), R3.1; also elsewhere on the board
INA3: C6.1, IC4.2 (I), R4.1; also elsewhere on the board
INA4: C7.1, IC5.2 (I), R5.1; also elsewhere on the board
INA5: C8.1, IC6.2 (I), R6.1; also elsewhere on the board
INA6: C9.1, IC7.2 (I), R7.1; also elsewhere on the board
OUTA1: IC1.4 (O); also elsewhere on the board
OUTA2: IC3.4 (O); also elsewhere on the board
OUTA3: IC4.4 (O); also elsewhere on the board
OUTA4: IC5.4 (O); also elsewhere on the board
OUTA5: IC6.4 (O); also elsewhere on the board
OUTA6: IC7.4 (O); also elsewhere on the board
VCC: IC1.5 (VCC), IC3.5 (VCC), IC4.5 (VCC), IC5.5 (VCC), IC6.5 (VCC), IC7.5 (VCC), R1.2, R3.2, R4.2, R5.2, R6.2, R7.2; also elsewhere on the board

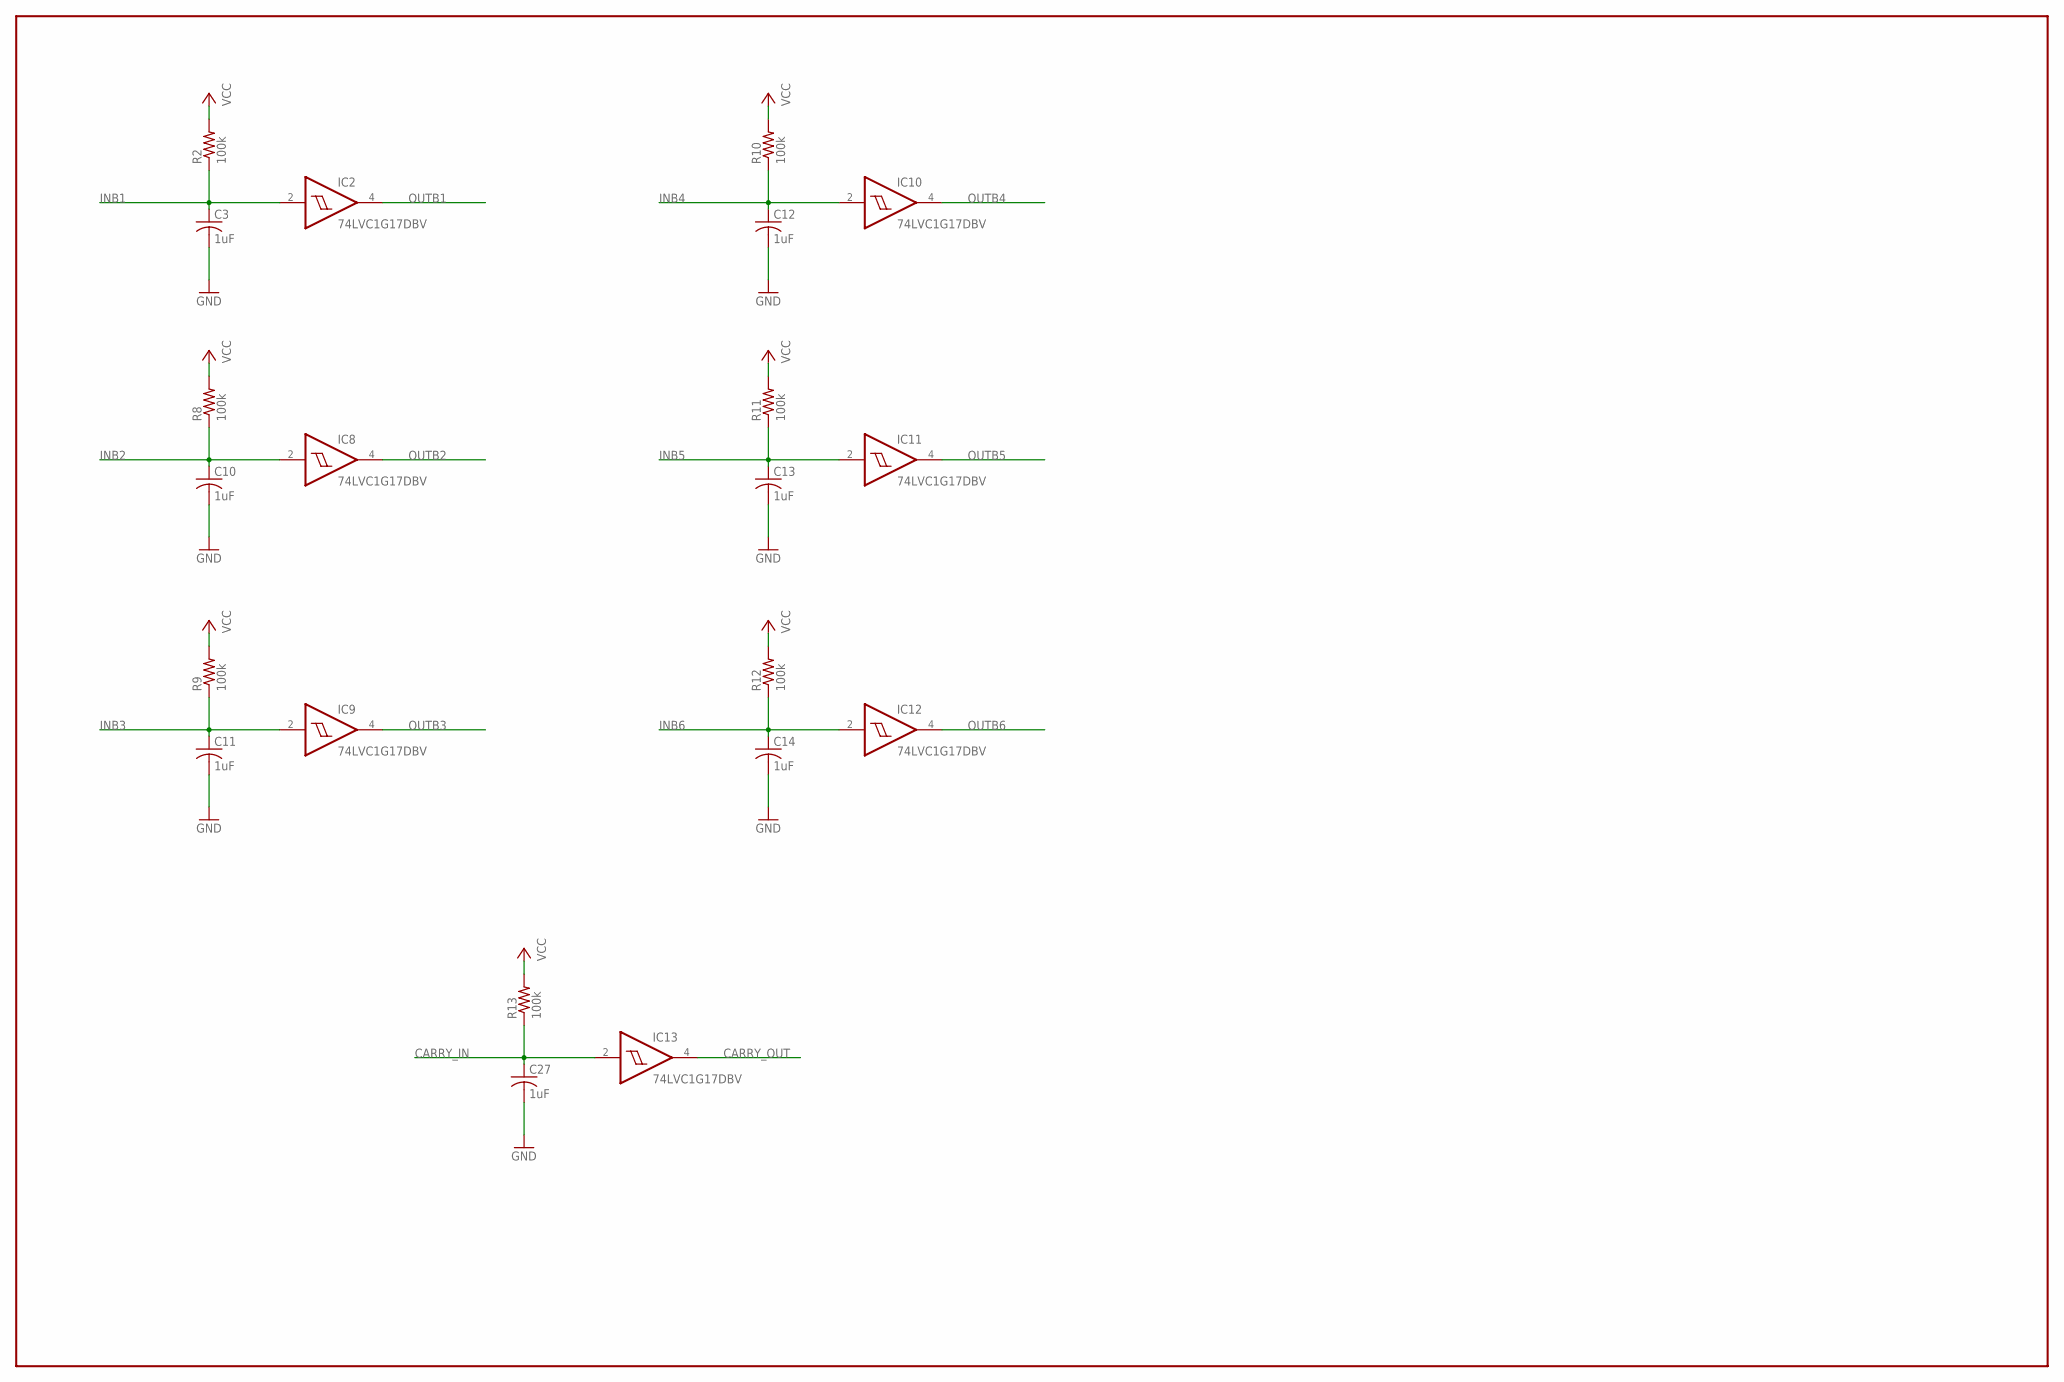
[picture p306: schematic transfer-interconnect.sch, sheet 3]

Parts:
C3, C10, C11, C12, C13, C14, C27: 1uF; C0603K
IC2, IC8, IC9, IC10, IC11, IC12, IC13: 74LVC1G17DBV; SOT23-5
R2, R8, R9, R10, R11, R12, R13: 100k; R0603

Connections:
CARRY_IN: C27.1, IC13.2 (I), R13.1; also elsewhere on the board
CARRY_OUT: IC13.4 (O); also elsewhere on the board
GND: C3.2, C10.2, C11.2, C12.2, C13.2, C14.2, C27.2, IC2.3 (GND), IC8.3 (GND), IC9.3 (GND), IC10.3 (GND), IC11.3 (GND), IC12.3 (GND), IC13.3 (GND); also elsewhere on the board
INB1: C3.1, IC2.2 (I), R2.1; also elsewhere on the board
INB2: C10.1, IC8.2 (I), R8.1; also elsewhere on the board
INB3: C11.1, IC9.2 (I), R9.1; also elsewhere on the board
INB4: C12.1, IC10.2 (I), R10.1; also elsewhere on the board
INB5: C13.1, IC11.2 (I), R11.1; also elsewhere on the board
INB6: C14.1, IC12.2 (I), R12.1; also elsewhere on the board
OUTB1: IC2.4 (O); also elsewhere on the board
OUTB2: IC8.4 (O); also elsewhere on the board
OUTB3: IC9.4 (O); also elsewhere on the board
OUTB4: IC10.4 (O); also elsewhere on the board
OUTB5: IC11.4 (O); also elsewhere on the board
OUTB6: IC12.4 (O); also elsewhere on the board
VCC: IC2.5 (VCC), IC8.5 (VCC), IC9.5 (VCC), IC10.5 (VCC), IC11.5 (VCC), IC12.5 (VCC), IC13.5 (VCC), R2.2, R8.2, R9.2, R10.2, R11.2, R12.2, R13.2; also elsewhere on the board

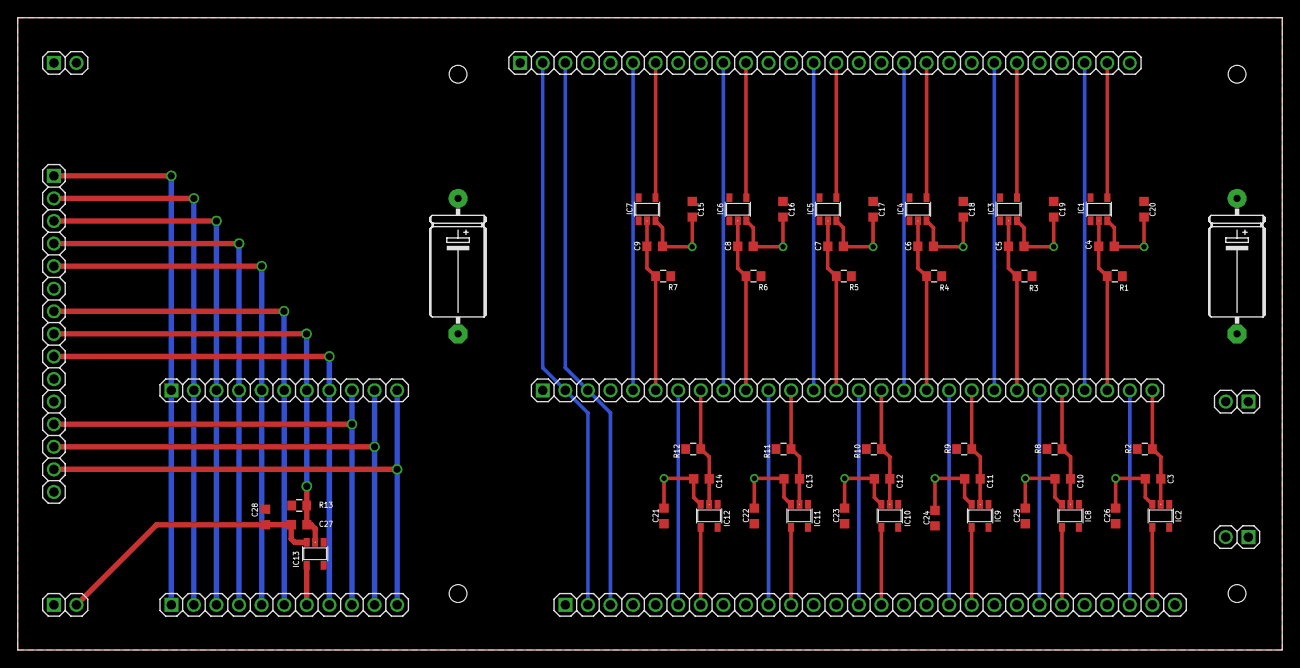
[picture p307: board transfer-interconnect.brd from above]

Board: 2 copper layers, 142.2 x 71.1 mm, 64 parts (0 on the bottom side), 52 nets.
