prpplague/witch_dev/block-designs/witch-phase2/tester-debug/schmitt-trigger/schmitt-trigger.brd

## EAGLE design block-designs/witch-phase2/tester-debug/schmitt-trigger/schmitt-trigger.brd (2017-02-12)

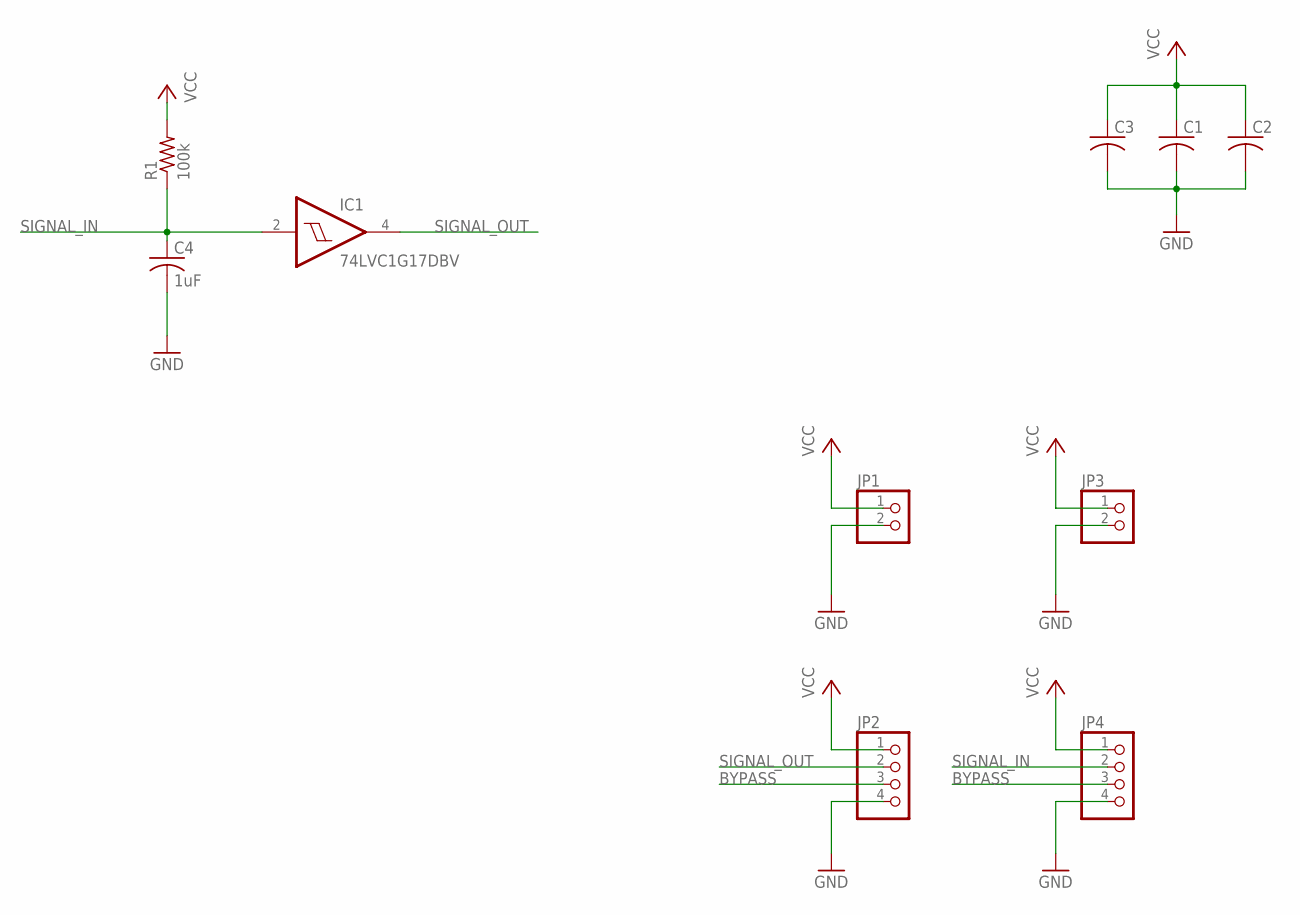
[picture p308: schematic schmitt-trigger.sch]

Parts:
C1, C2, C3: C-USC0603K; C0603K
C4: 1uF; C0603K
IC1: 74LVC1G17DBV; SOT23-5
JP1, JP3: PINHD-1X2; 1X02
JP2, JP4: PINHD-1X4; 1X04
R1: 100k; R0603

Connections:
BYPASS: JP2.3, JP4.3
GND: C1.2, C2.2, C3.2, C4.2, IC1.3 (GND), JP1.2, JP2.4, JP3.2, JP4.4
SIGNAL_IN: C4.1, IC1.2 (I), JP4.2, R1.1
SIGNAL_OUT: IC1.4 (O), JP2.2
VCC: C1.1, C2.1, C3.1, IC1.5 (VCC), JP1.1, JP2.1, JP3.1, JP4.1, R1.2

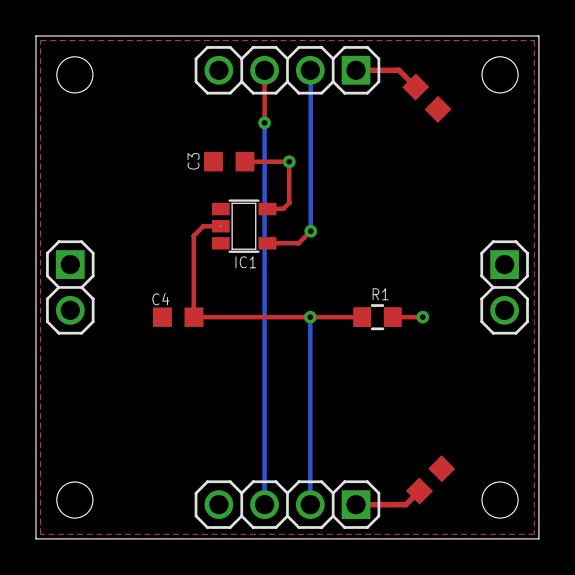
[picture p309: board schmitt-trigger.brd from above]

Board: 2 copper layers, 27.9 x 27.9 mm, 10 parts (0 on the bottom side), 5 nets.
