prpplague/witch_dev/block-designs/witch-phase2/tester-debug/clock-delay/clock-delay.brd

## EAGLE design block-designs/witch-phase2/tester-debug/clock-delay/clock-delay.brd (2017-01-22)

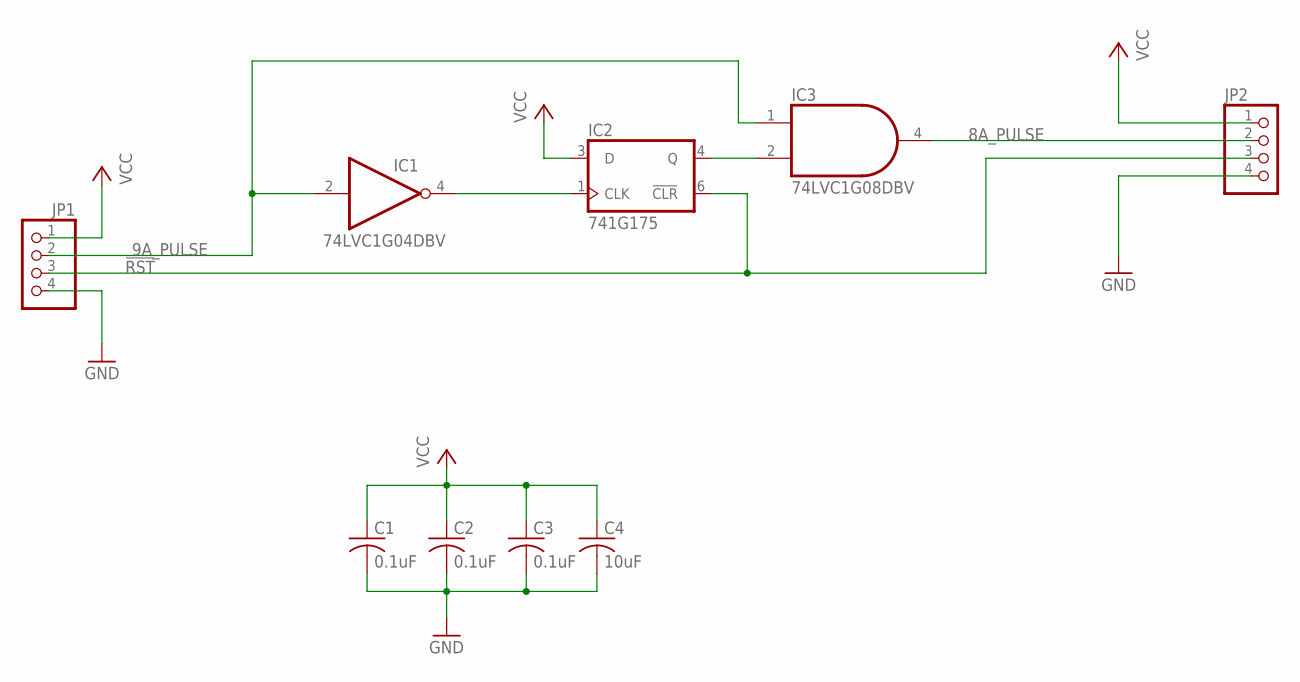
[picture p310: schematic clock-delay.sch]

Parts:
C1, C2, C3: 0.1uF; C0805
C4: 10uF; C0805
IC1: 74LVC1G04DBV; SOT23-5
IC2: 741G175; DBV_R-PDSO-G6
IC3: 74LVC1G08DBV; SOT23-5
JP1, JP2: PINHD-1X4; 1X04

Connections:
8A_PULSE: IC3.4 (O), JP2.2
9A_PULSE: IC1.2 (I), IC3.1 (I0), JP1.2
!RST: IC2.6 (!CLR), JP1.3, JP2.3
GND: C1.2, C2.2, C3.2, C4.2, IC1.3 (GND), IC2.2 (GND), IC3.3 (GND), JP1.4, JP2.4
unnamed: IC2.4 (Q), IC3.2 (I1)
unnamed: IC1.4 (O), IC2.1 (CLK)
VCC: C1.1, C2.1, C3.1, C4.1, IC1.5 (VCC), IC2.3 (D), IC2.5 (VCC), IC3.5 (VCC), JP1.1, JP2.1

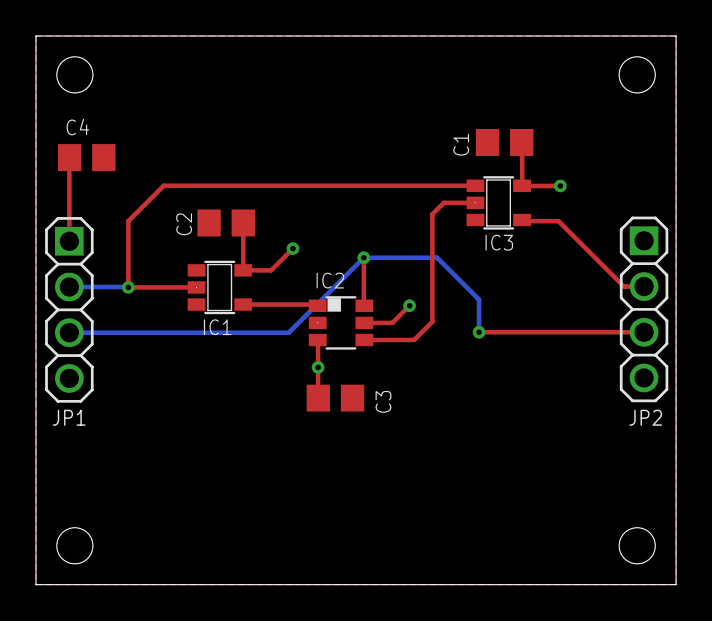
[picture p311: board clock-delay.brd from above]

Board: 2 copper layers, 35.6 x 30.5 mm, 9 parts (0 on the bottom side), 7 nets.
