prpplague/witch_dev/block-designs/witch-phase2/tester-debug/manual-input/manual-button/manual-button.brd

## EAGLE design block-designs/witch-phase2/tester-debug/manual-input/manual-button/manual-button.brd (2016-11-26)

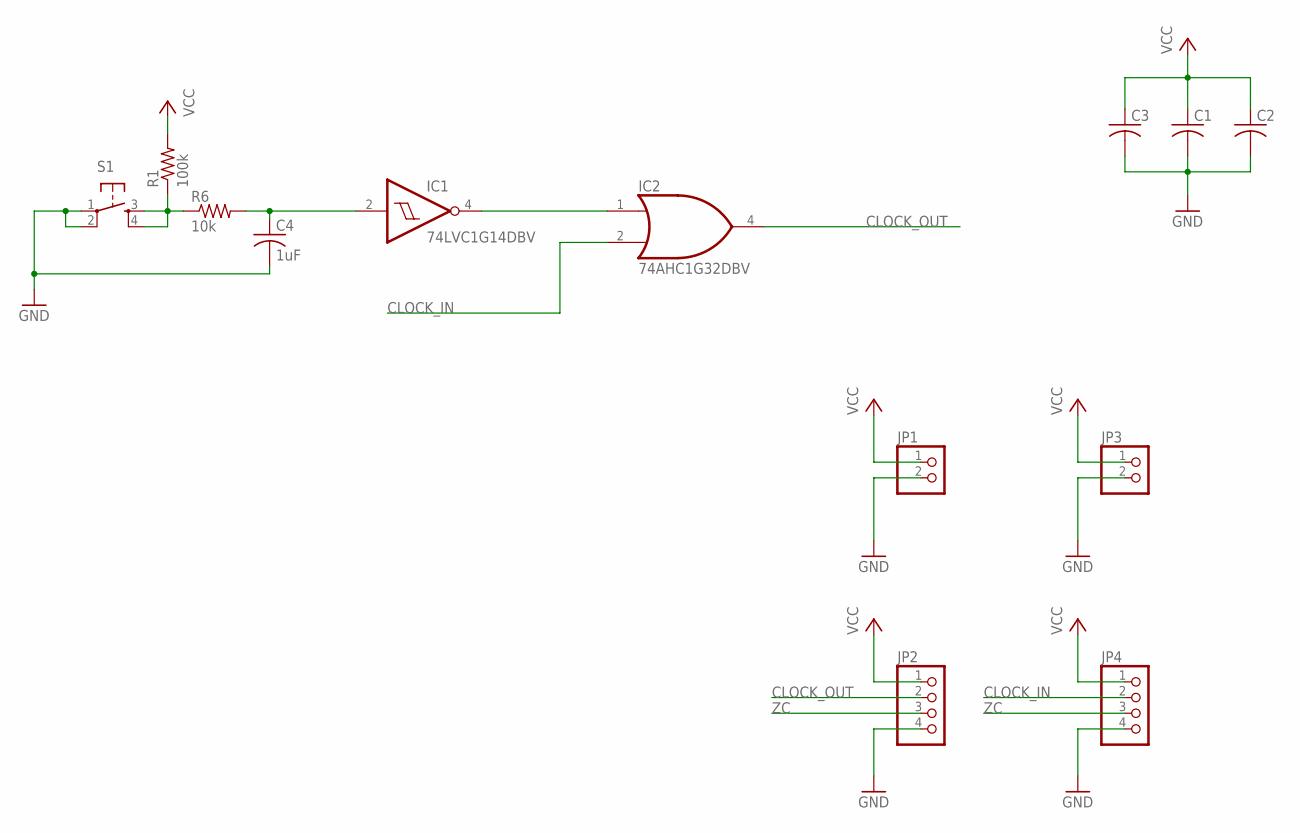
[picture p312: schematic manual-button.sch]

Parts:
C1, C2, C3: C-USC0603K; C0603K
C4: 1uF; C0603K
IC1: 74LVC1G14DBV; SOT23-5
IC2: 74AHC1G32DBV; SOT23-5
JP1, JP3: PINHD-1X2; 1X02
JP2, JP4: PINHD-1X4; 1X04
R1: 100k; R0603
R6: 10k; R0603
S1: TAC_SWITCHPTH; TACTILE-PTH

Connections:
CLOCK_IN: IC2.2 (I1), JP4.2
CLOCK_OUT: IC2.4 (O), JP2.2
DA_IN: IC1.4 (O), IC2.1 (I0)
GND: C1.2, C2.2, C3.2, C4.2, IC1.3 (GND), IC2.3 (GND), JP1.2, JP2.4, JP3.2, JP4.4, S1.1, S1.2
unnamed: R1.1, R6.1, S1.3, S1.4
unnamed: C4.1, IC1.2 (I), R6.2
VCC: C1.1, C2.1, C3.1, IC1.5 (VCC), IC2.5 (VCC), JP1.1, JP2.1, JP3.1, JP4.1, R1.2
ZC: JP2.3, JP4.3

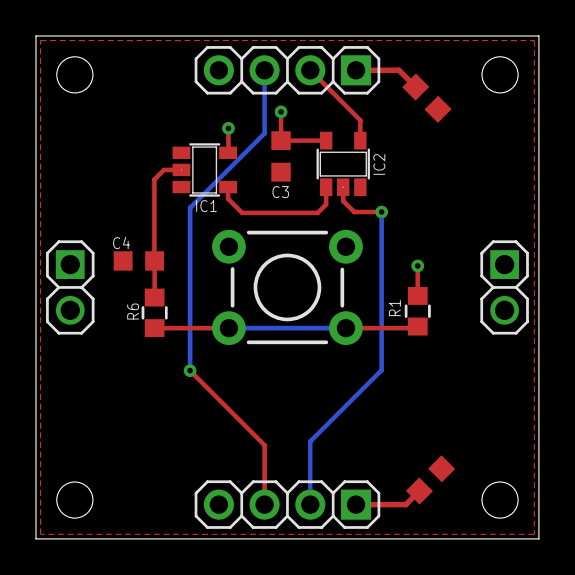
[picture p313: board manual-button.brd from above]

Board: 2 copper layers, 27.9 x 27.9 mm, 13 parts (0 on the bottom side), 8 nets.
