prpplague/witch_dev/block-designs/witch-phase2/store-column-block/store-column-block.brd

## EAGLE design block-designs/witch-phase2/store-column-block/store-column-block.brd (2016-11-19)

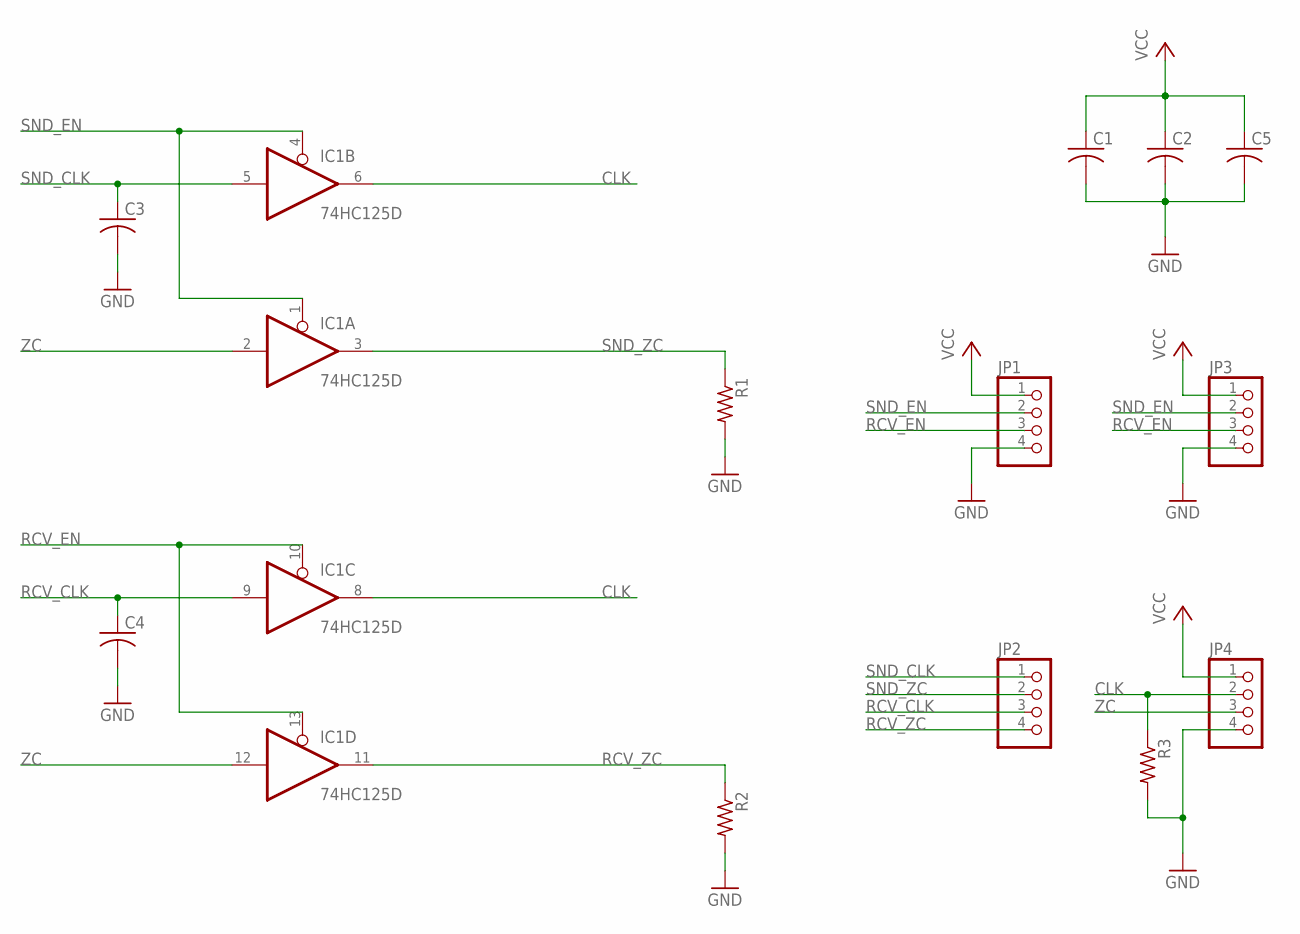
[picture p314: schematic store-column-block.sch]

Parts:
C1, C2, C3, C4, C5: C-USC0603K; C0603K
IC1: 74HC125D; SO14
JP1, JP2, JP3, JP4: PINHD-1X4; 1X04
R1, R2, R3: R-US_R0603; R0603

Connections:
CLK: IC1.6 (O), IC1.8 (O), JP4.2, R3.1
GND: C1.2, C2.2, C3.2, C4.2, C5.2, IC1.7 (GND), JP1.4, JP3.4, JP4.4, R1.2, R2.2, R3.2
RCV_CLK: C4.1, IC1.9 (I), JP2.3
RCV_EN: IC1.10 (OE), IC1.13 (OE), JP1.3, JP3.3
RCV_ZC: IC1.11 (O), JP2.4, R2.1
SND_CLK: C3.1, IC1.5 (I), JP2.1
SND_EN: IC1.1 (OE), IC1.4 (OE), JP1.2, JP3.2
SND_ZC: IC1.3 (O), JP2.2, R1.1
VCC: C1.1, C2.1, C5.1, IC1.14 (VCC), JP1.1, JP3.1, JP4.1
ZC: IC1.2 (I), IC1.12 (I), JP4.3

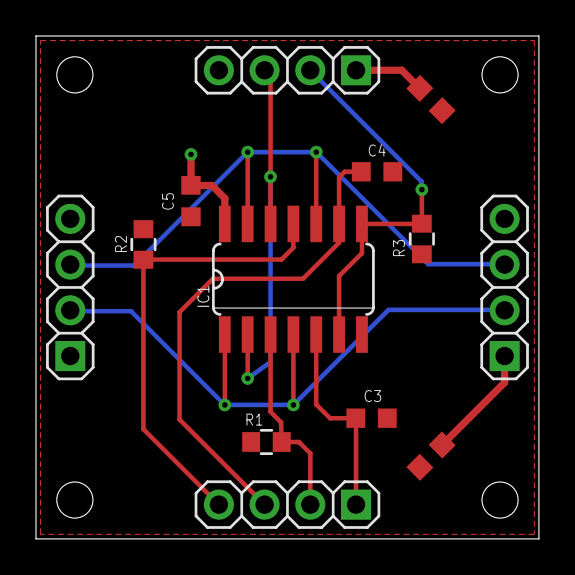
[picture p315: board store-column-block.brd from above]

Board: 2 copper layers, 27.9 x 27.9 mm, 13 parts (0 on the bottom side), 10 nets.
