prpplague/witch_dev/block-designs/witch-phase2/tester-debug/manual-input/manual-switch/manual-switch.brd

## EAGLE design block-designs/witch-phase2/tester-debug/manual-input/manual-switch/manual-switch.brd (2016-11-18)

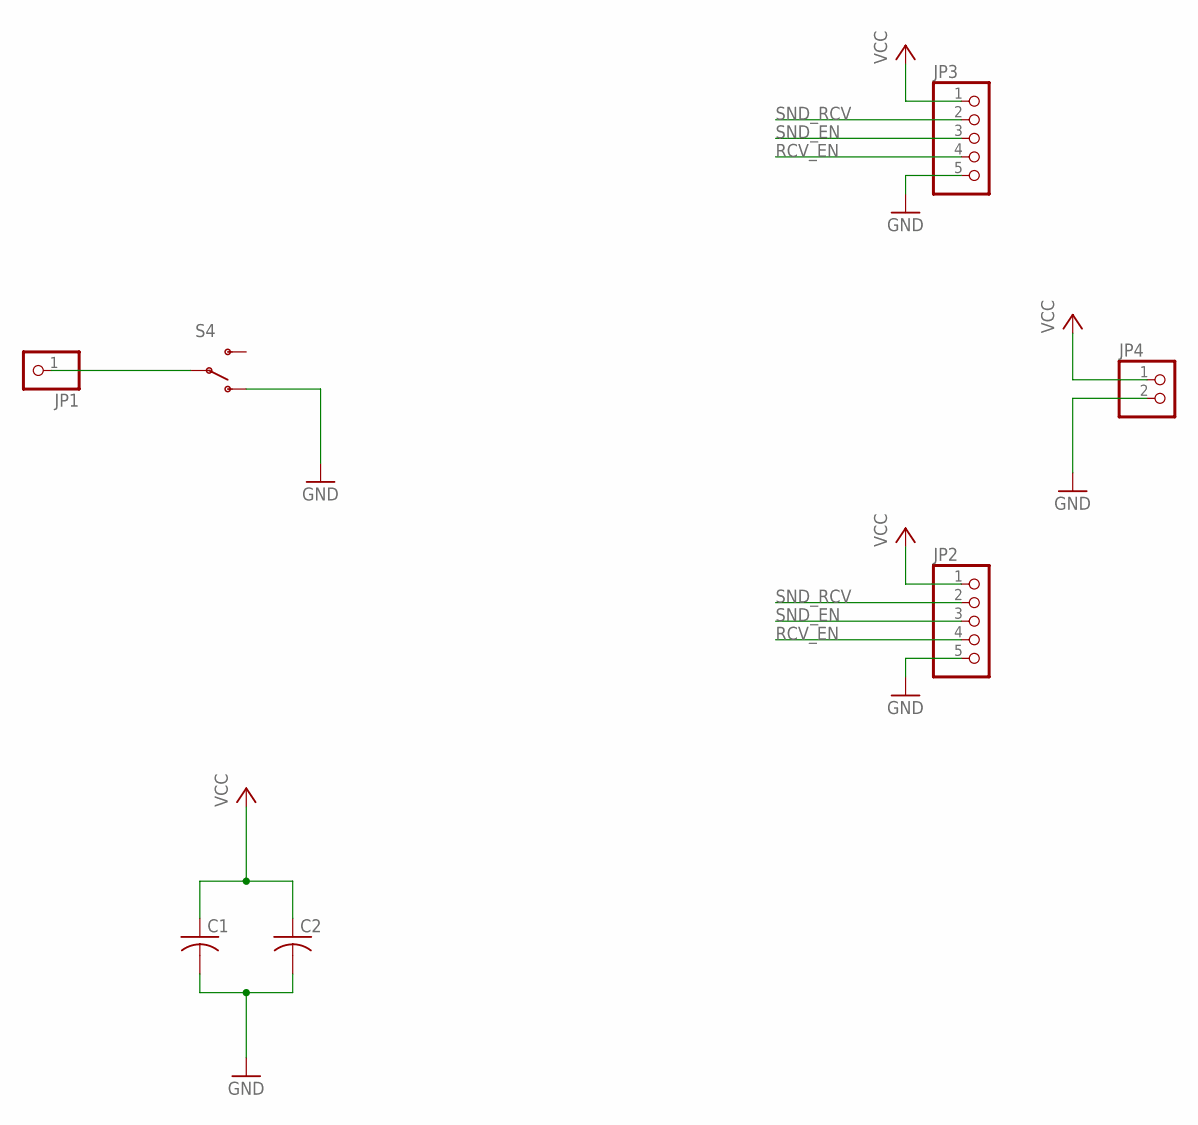
[picture p316: schematic manual-switch.sch]

Parts:
C1, C2: C-USC0805; C0805
JP1: PINHD-1X1; 1X01
JP2, JP3: PINHD-1X5; 1X05
JP4: PINHD-1X2; 1X02
S4: SWITCH-SPDTPTH; SWITCH-SPDT

Connections:
GND: C1.2, C2.2, JP2.5, JP3.5, JP4.2, S4.1 (O)
unnamed: JP1.1, S4.2
RCV_EN: JP2.4, JP3.4
SND_EN: JP2.3, JP3.3
SND_RCV: JP2.2, JP3.2
VCC: C1.1, C2.1, JP2.1, JP3.1, JP4.1

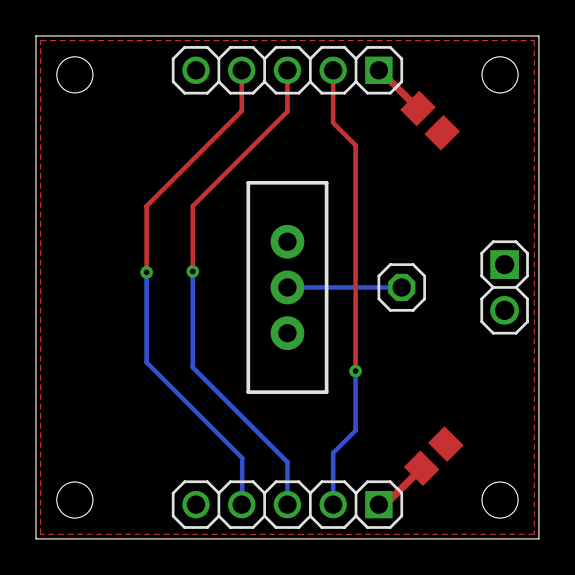
[picture p317: board manual-switch.brd from above]

Board: 2 copper layers, 27.9 x 27.9 mm, 7 parts (0 on the bottom side), 6 nets.
