prpplague/witch_dev/block-designs/witch-phase2/carry-block/carry-block.brd

## EAGLE design block-designs/witch-phase2/carry-block/carry-block.brd (2016-11-18)

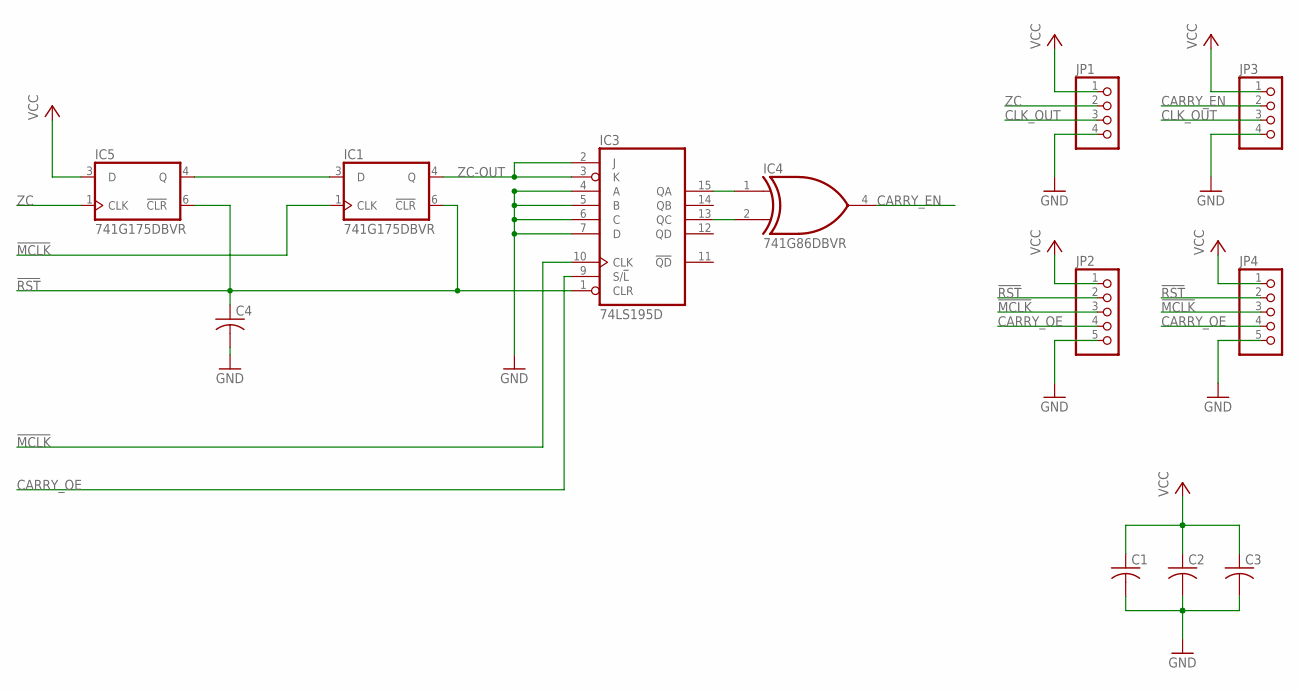
[picture p318: schematic carry-block.sch]

Parts:
C1, C2, C3, C4: C-USC0603K; C0603K
IC1, IC5: 741G175DBVR; DBV_R-PDSO-G6
IC3: 74LS195D; SO16
IC4: 741G86DBVR; SOT23-5
JP1, JP3: PINHD-1X4; 1X04
JP2, JP4: PINHD-1X5; 1X05

Connections:
!MCLK: IC1.1 (CLK), IC3.10 (CLK), JP2.3, JP4.3
!RST: C4.1, IC1.6 (!CLR), IC3.1 (CLR), IC5.6 (!CLR), JP2.2, JP4.2
CARRY_EN: IC4.4 (O), JP3.2
CARRY_OE: IC3.9 (S/!L), JP2.4, JP4.4
CLK_OUT: JP1.3, JP3.3
GND: C1.2, C2.2, C3.2, C4.2, IC1.2 (GND), IC3.4 (A), IC3.5 (B), IC3.6 (C), IC3.7 (D), IC3.8 (GND), IC4.3 (GND), IC5.2 (GND), JP1.4, JP2.5, JP3.4, JP4.5
unnamed: IC3.15 (QA), IC4.1 (I0)
unnamed: IC3.13 (QC), IC4.2 (I1)
unnamed: IC1.3 (D), IC5.4 (Q)
VCC: C1.1, C2.1, C3.1, IC1.5 (VCC), IC3.16 (VCC), IC4.5 (VCC), IC5.3 (D), IC5.5 (VCC), JP1.1, JP2.1, JP3.1, JP4.1
ZC: IC5.1 (CLK), JP1.2
ZC-OUT: IC1.4 (Q), IC3.2 (J), IC3.3 (K)

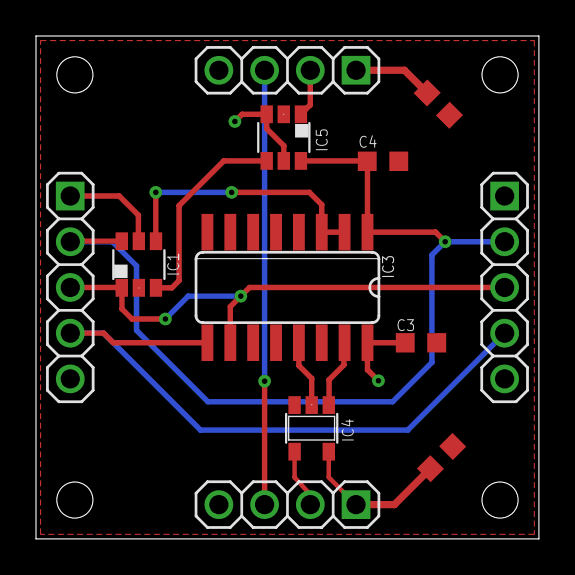
[picture p319: board carry-block.brd from above]

Board: 2 copper layers, 27.9 x 27.9 mm, 12 parts (0 on the bottom side), 12 nets.
