prpplague/witch_dev/block-designs/witch-phase2/tester-debug/mini-store-selector/mini-store-selector.brd

## EAGLE design block-designs/witch-phase2/tester-debug/mini-store-selector/mini-store-selector.brd (2016-08-27)

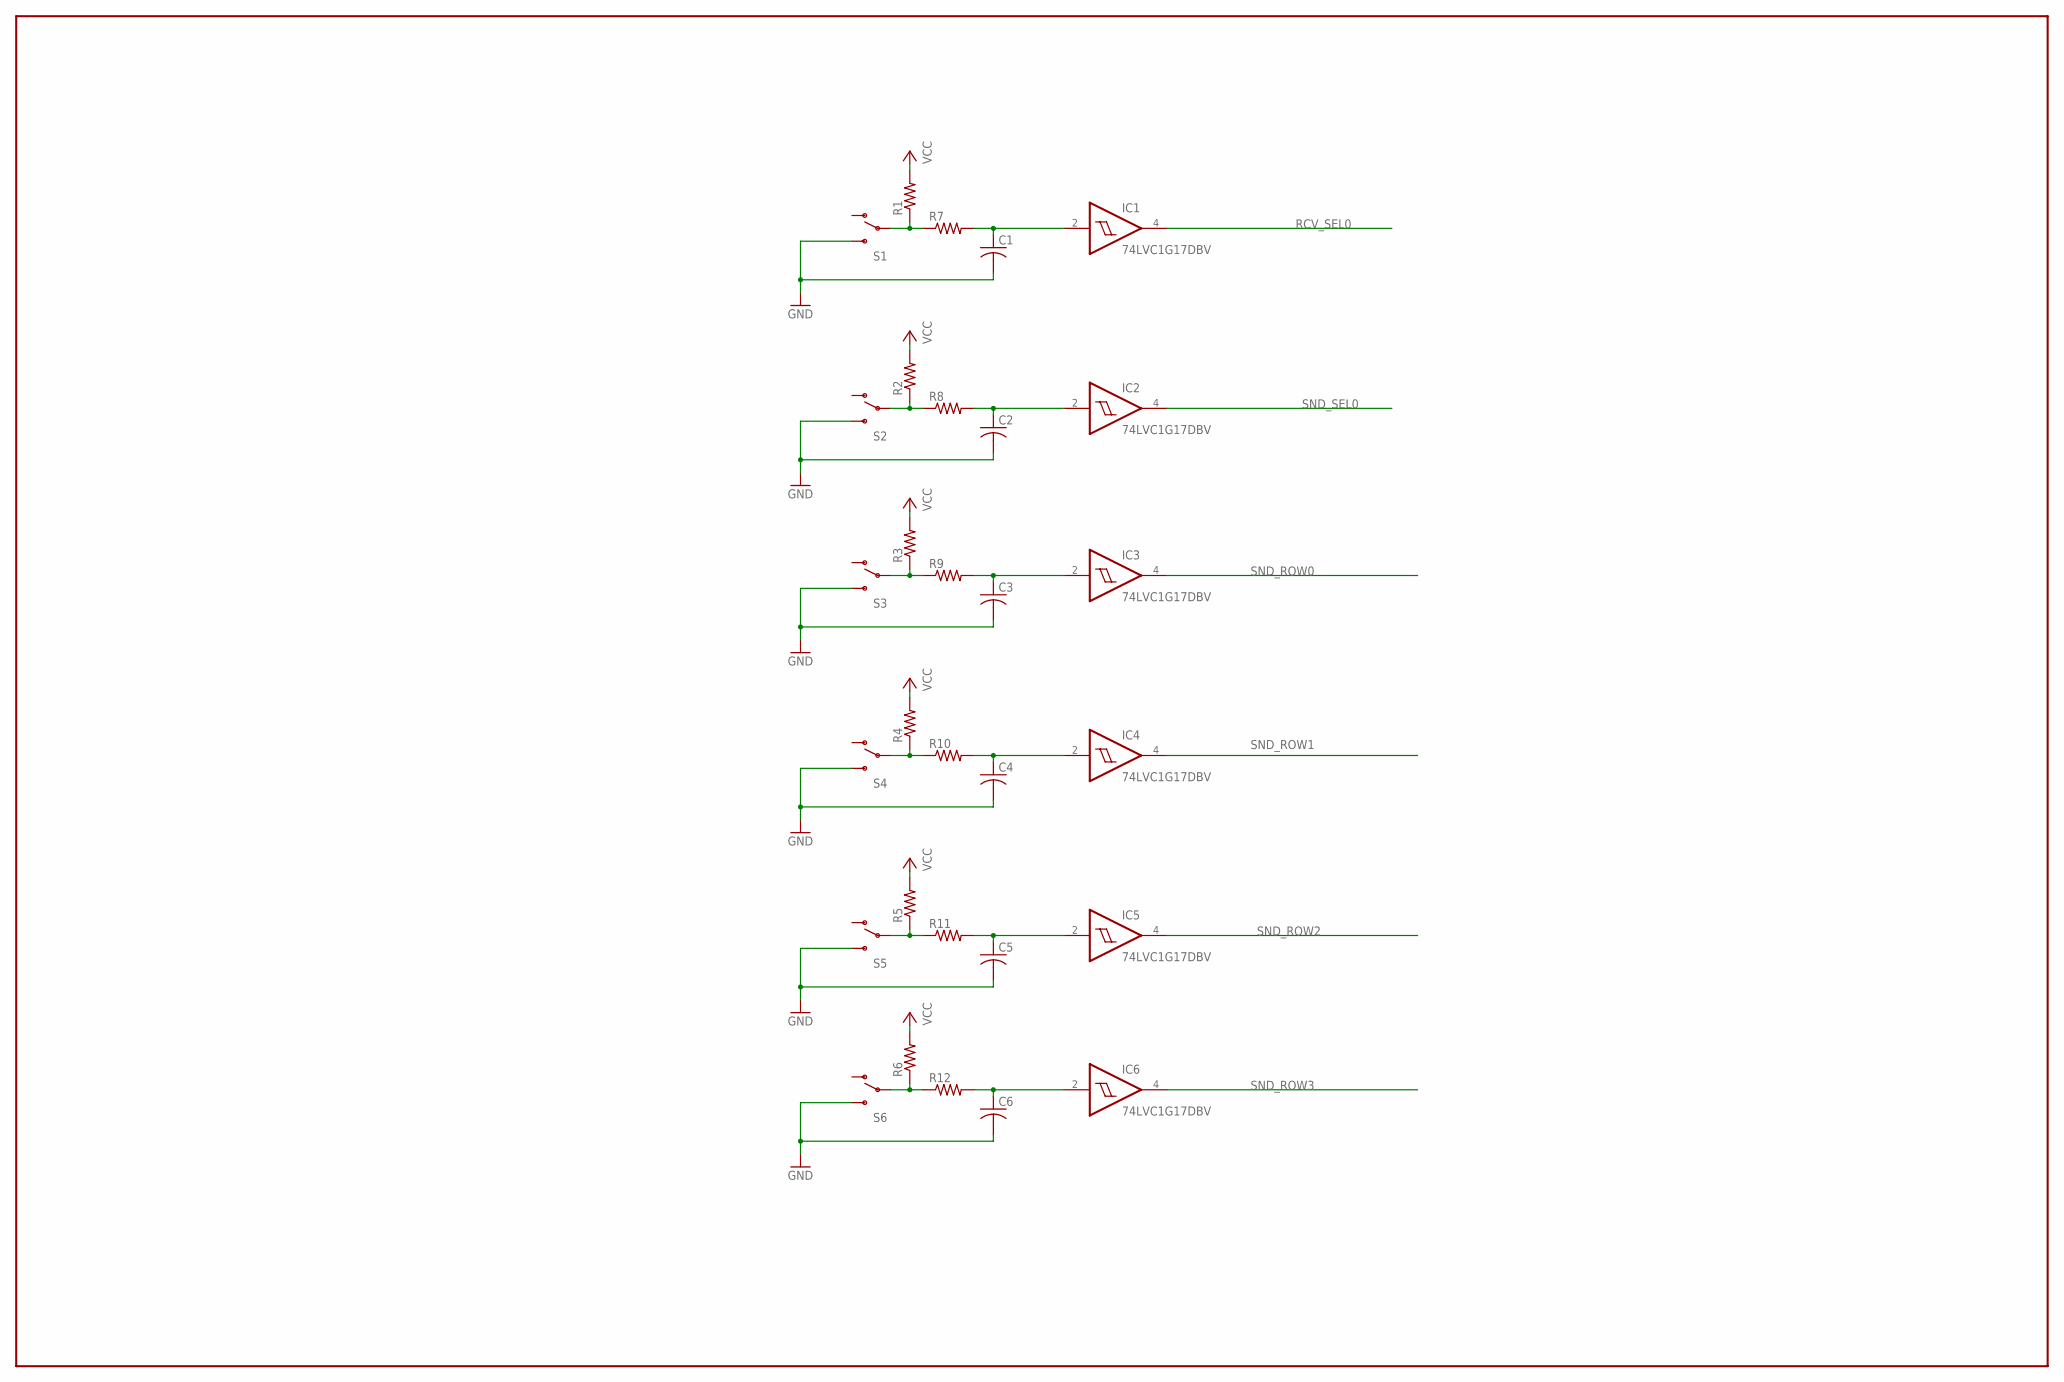
[picture p320: schematic mini-store-selector.sch, sheet 1]

Parts:
C1, C2, C3, C4, C5, C6: C-USC0805; C0805
IC1, IC2, IC3, IC4, IC5, IC6: 74LVC1G17DBV; SOT23-5
R1, R2, R3, R4, R5, R6, R7, R8, R9, R10, R11, R12: R-US_R0805; R0805
S1, S2, S3, S4, S5, S6: SWITCH-SPDTPTH; SWITCH-SPDT

Connections:
GND: C1.2, C2.2, C3.2, C4.2, C5.2, C6.2, IC1.3 (GND), IC2.3 (GND), IC3.3 (GND), IC4.3 (GND), IC5.3 (GND), IC6.3 (GND), S1.3 (S), S2.3 (S), S3.3 (S), S4.3 (S), S5.3 (S), S6.3 (S); also elsewhere on the board
unnamed: C6.1, IC6.2 (I), R12.2
unnamed: R6.1, R12.1, S6.2
unnamed: C2.1, IC2.2 (I), R8.2
unnamed: R2.1, R8.1, S2.2
unnamed: C1.1, IC1.2 (I), R7.2
unnamed: C4.1, IC4.2 (I), R10.2
unnamed: R4.1, R10.1, S4.2
unnamed: C3.1, IC3.2 (I), R9.2
unnamed: R3.1, R9.1, S3.2
unnamed: C5.1, IC5.2 (I), R11.2
unnamed: R5.1, R11.1, S5.2
unnamed: R1.1, R7.1, S1.2
RCV_SEL0: IC1.4 (O); also elsewhere on the board
SND_ROW0: IC3.4 (O); also elsewhere on the board
SND_ROW1: IC4.4 (O); also elsewhere on the board
SND_ROW2: IC5.4 (O); also elsewhere on the board
SND_ROW3: IC6.4 (O); also elsewhere on the board
SND_SEL0: IC2.4 (O); also elsewhere on the board
VCC: IC1.5 (VCC), IC2.5 (VCC), IC3.5 (VCC), IC4.5 (VCC), IC5.5 (VCC), IC6.5 (VCC), R1.2, R2.2, R3.2, R4.2, R5.2, R6.2; also elsewhere on the board

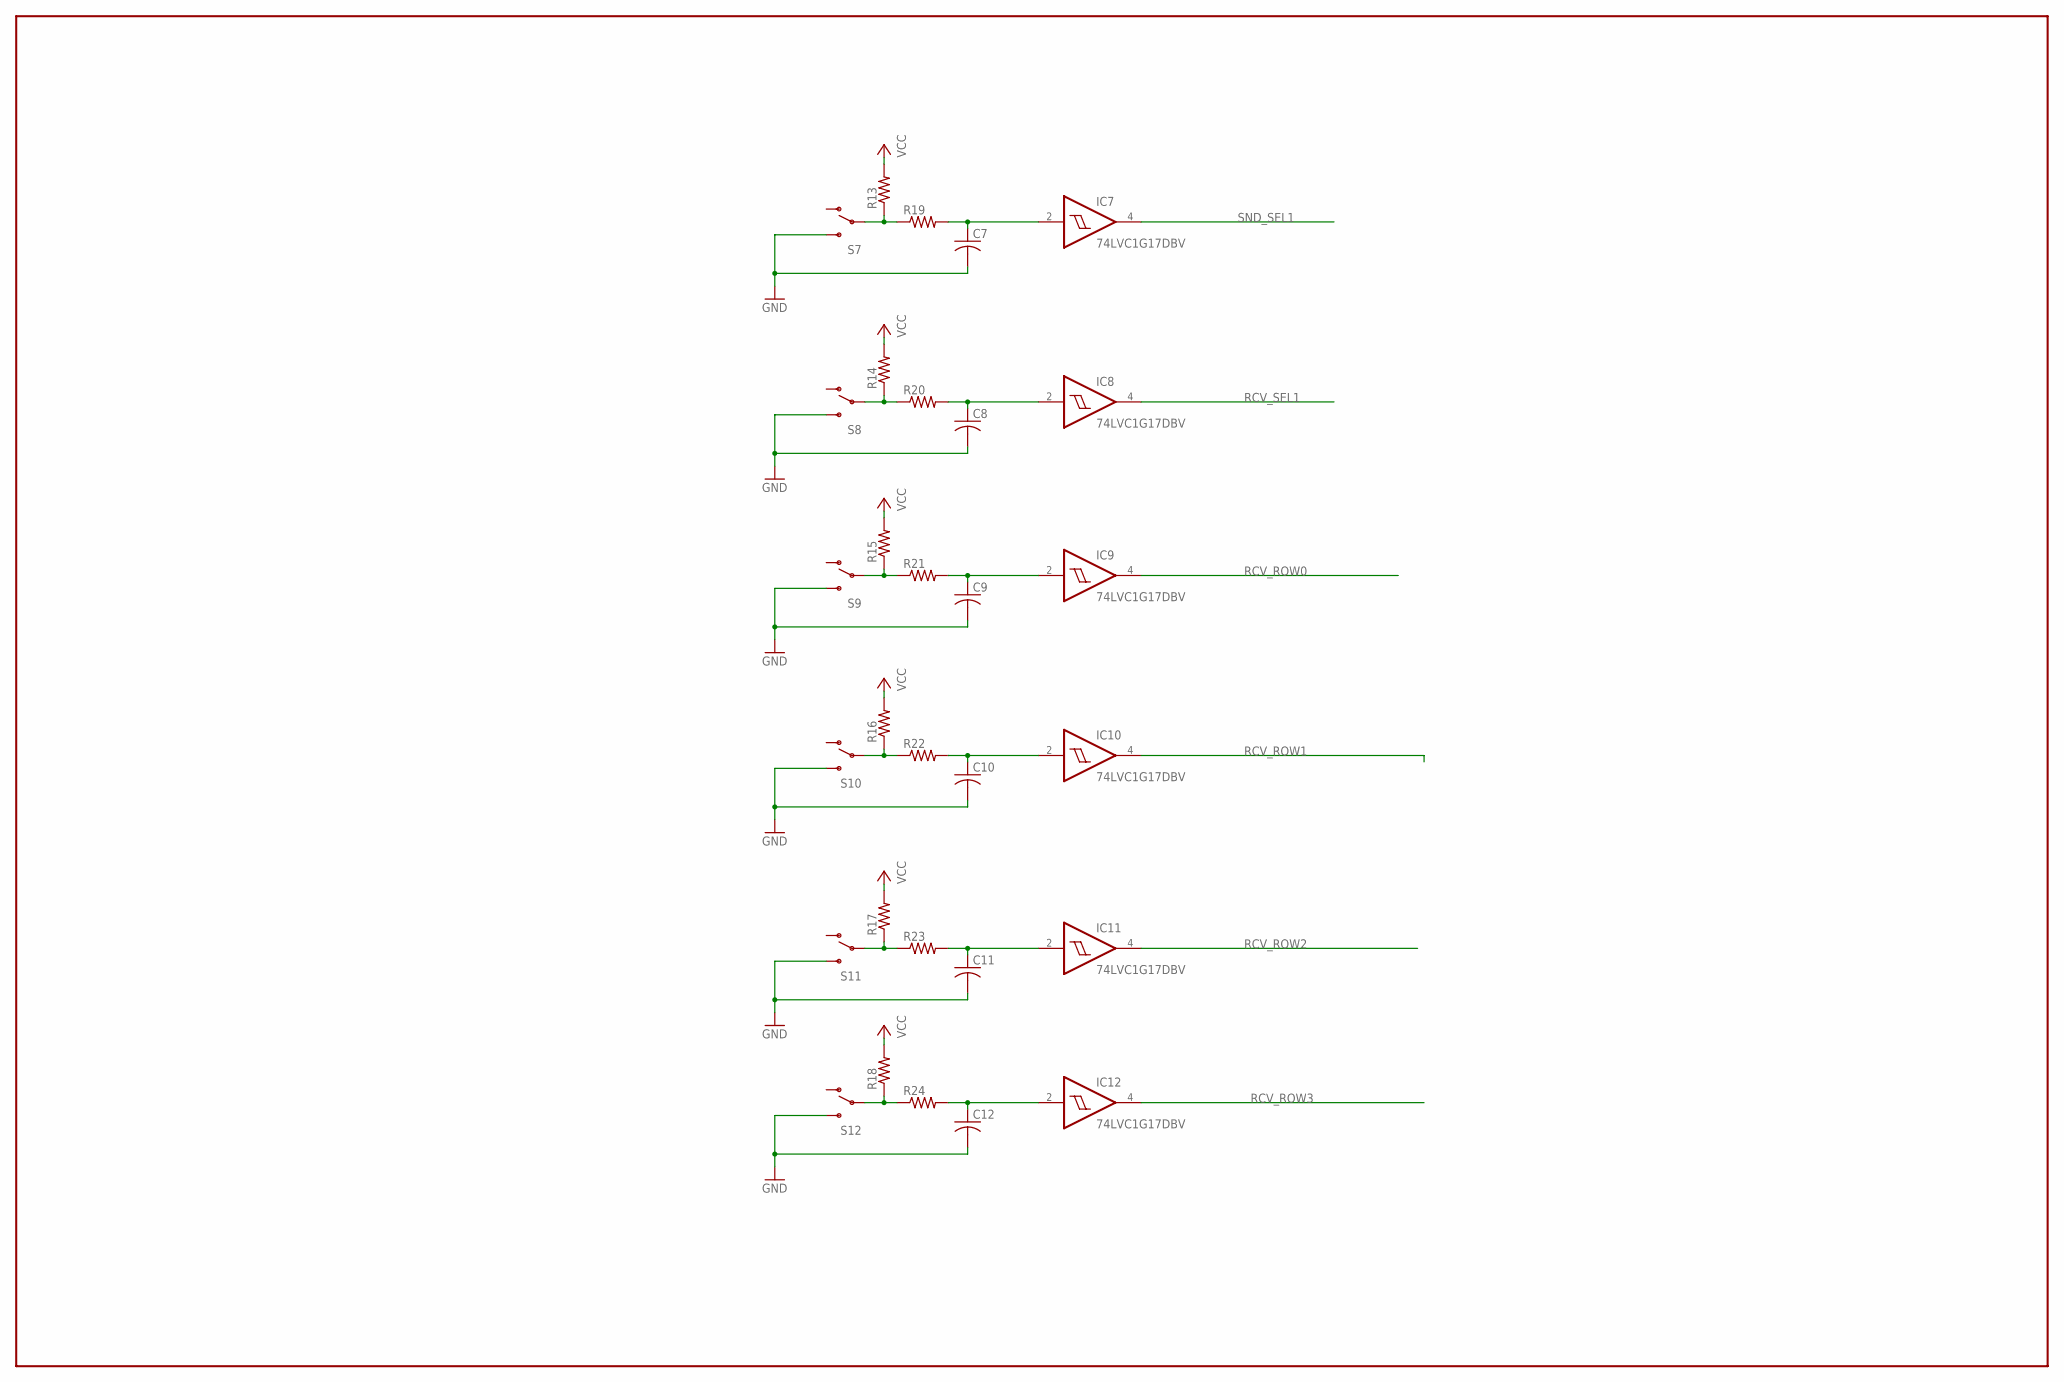
[picture p321: schematic mini-store-selector.sch, sheet 2]

Parts:
C7, C8, C9, C10, C11, C12: C-USC0805; C0805
IC7, IC8, IC9, IC10, IC11, IC12: 74LVC1G17DBV; SOT23-5
R13, R14, R15, R16, R17, R18, R19, R20, R21, R22, R23, R24: R-US_R0805; R0805
S7, S8, S9, S10, S11, S12: SWITCH-SPDTPTH; SWITCH-SPDT

Connections:
GND: C7.2, C8.2, C9.2, C10.2, C11.2, C12.2, IC7.3 (GND), IC8.3 (GND), IC9.3 (GND), IC10.3 (GND), IC11.3 (GND), IC12.3 (GND), S7.3 (S), S8.3 (S), S9.3 (S), S10.3 (S), S11.3 (S), S12.3 (S); also elsewhere on the board
unnamed: C10.1, IC10.2 (I), R22.2
unnamed: R16.1, R22.1, S10.2
unnamed: C9.1, IC9.2 (I), R21.2
unnamed: R15.1, R21.1, S9.2
unnamed: C11.1, IC11.2 (I), R23.2
unnamed: R17.1, R23.1, S11.2
unnamed: C12.1, IC12.2 (I), R24.2
unnamed: R18.1, R24.1, S12.2
unnamed: C8.1, IC8.2 (I), R20.2
unnamed: R14.1, R20.1, S8.2
unnamed: C7.1, IC7.2 (I), R19.2
unnamed: R13.1, R19.1, S7.2
RCV_ROW0: IC9.4 (O); also elsewhere on the board
RCV_ROW1: IC10.4 (O); also elsewhere on the board
RCV_ROW2: IC11.4 (O); also elsewhere on the board
RCV_ROW3: IC12.4 (O); also elsewhere on the board
RCV_SEL1: IC8.4 (O); also elsewhere on the board
SND_SEL1: IC7.4 (O); also elsewhere on the board
VCC: IC7.5 (VCC), IC8.5 (VCC), IC9.5 (VCC), IC10.5 (VCC), IC11.5 (VCC), IC12.5 (VCC), R13.2, R14.2, R15.2, R16.2, R17.2, R18.2; also elsewhere on the board

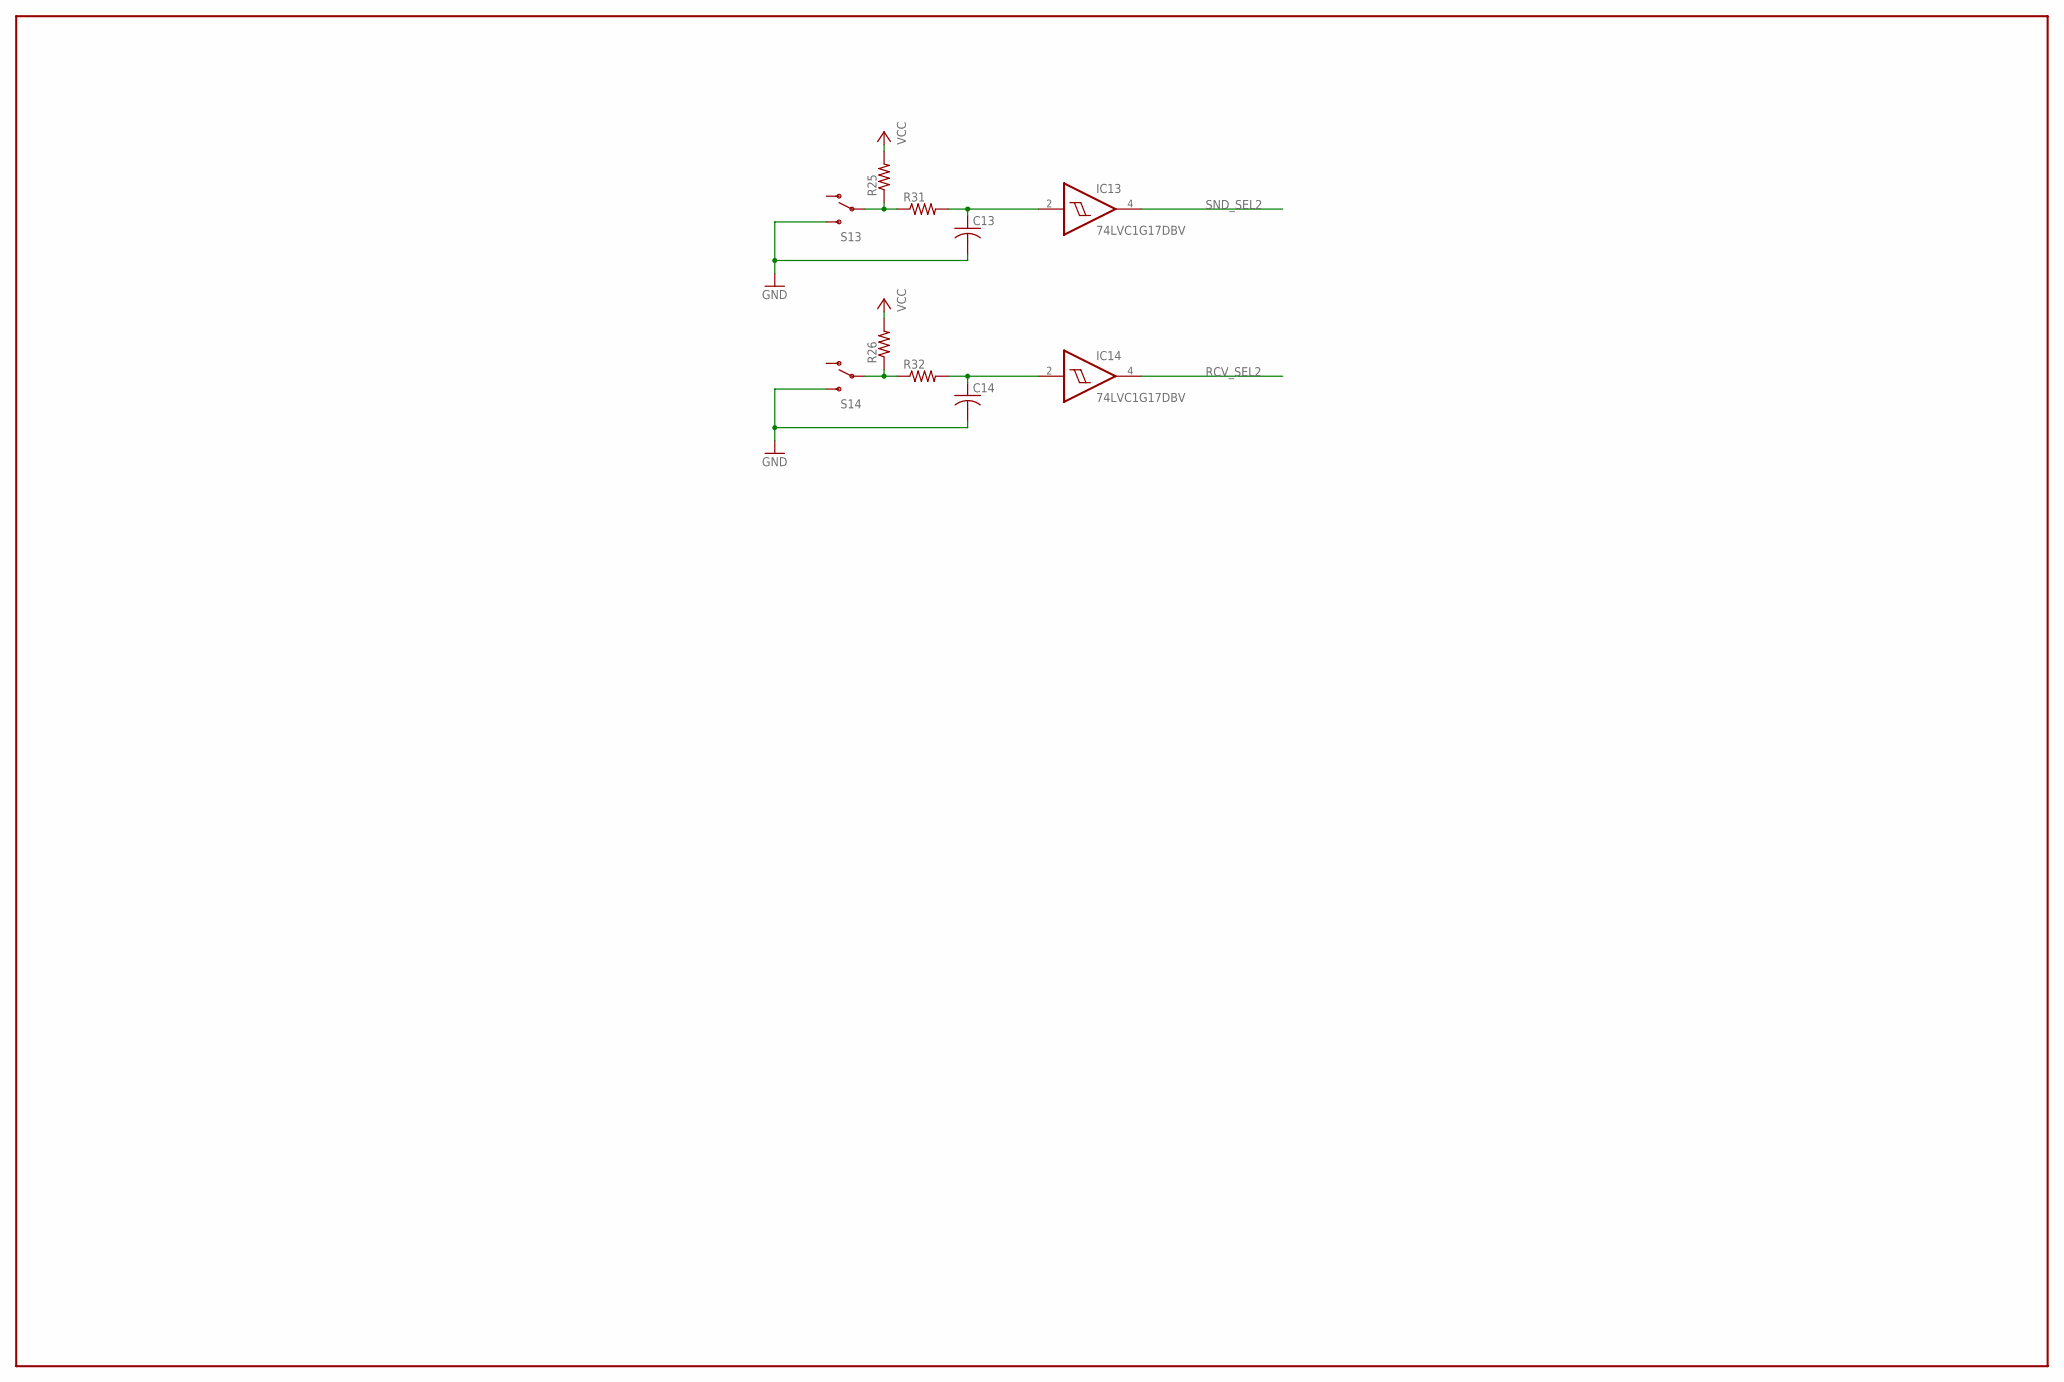
[picture p322: schematic mini-store-selector.sch, sheet 3]

Parts:
C13, C14: C-USC0805; C0805
IC13, IC14: 74LVC1G17DBV; SOT23-5
R25, R26, R31, R32: R-US_R0805; R0805
S13, S14: SWITCH-SPDTPTH; SWITCH-SPDT

Connections:
GND: C13.2, C14.2, IC13.3 (GND), IC14.3 (GND), S13.3 (S), S14.3 (S); also elsewhere on the board
unnamed: C14.1, IC14.2 (I), R32.2
unnamed: R26.1, R32.1, S14.2
unnamed: C13.1, IC13.2 (I), R31.2
unnamed: R25.1, R31.1, S13.2
RCV_SEL2: IC14.4 (O); also elsewhere on the board
SND_SEL2: IC13.4 (O); also elsewhere on the board
VCC: IC13.5 (VCC), IC14.5 (VCC), R25.2, R26.2; also elsewhere on the board

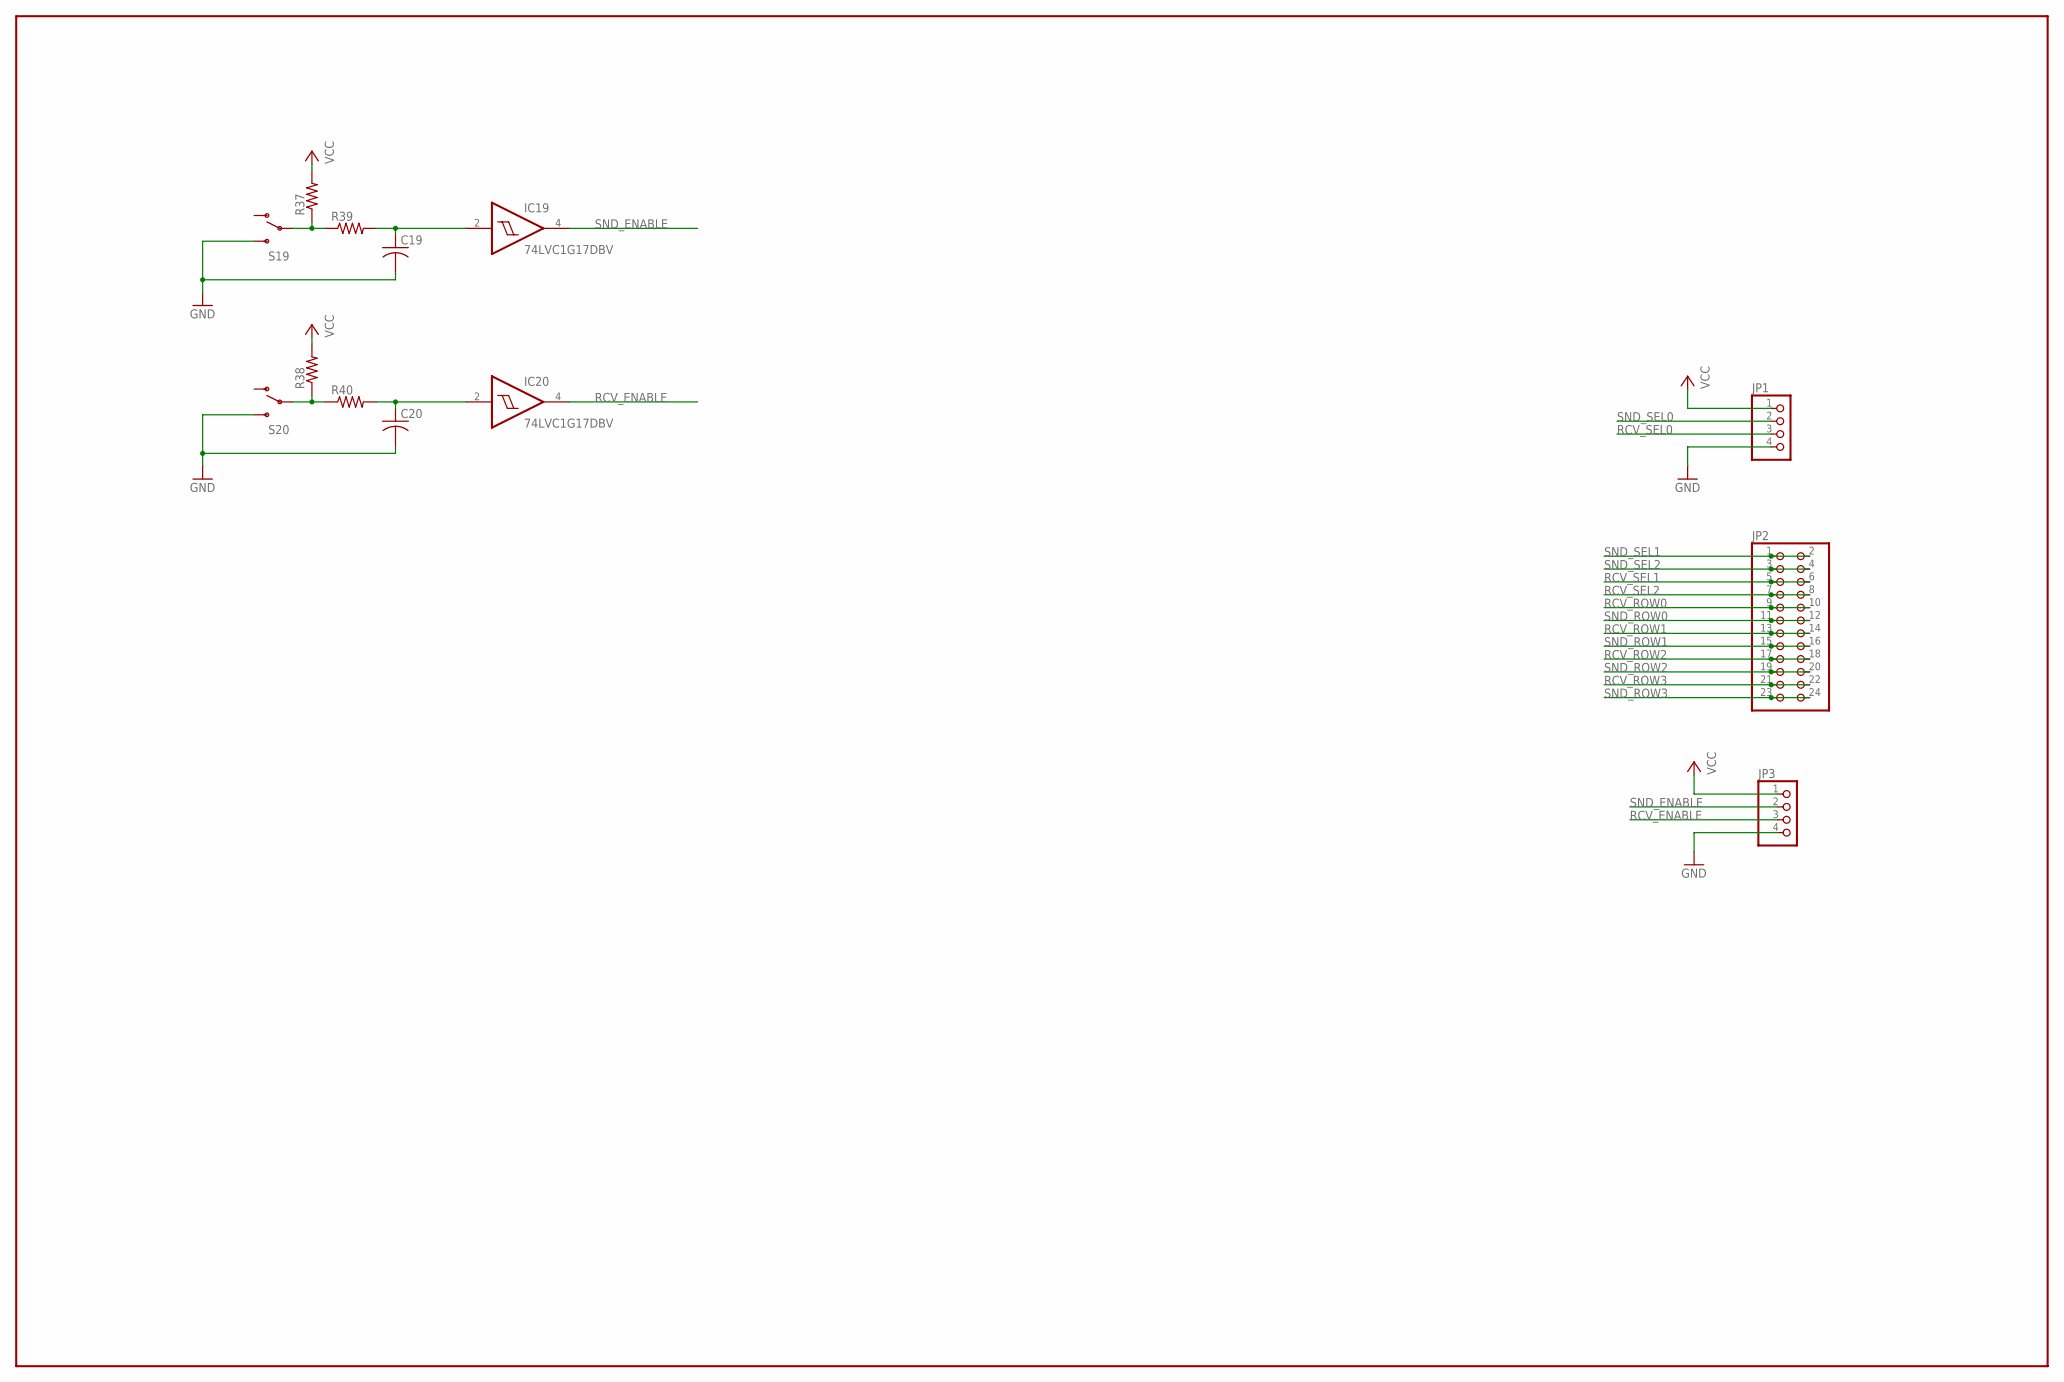
[picture p323: schematic mini-store-selector.sch, sheet 4]

Parts:
C19, C20: C-USC0805; C0805
IC19, IC20: 74LVC1G17DBV; SOT23-5
JP1, JP3: PINHD-1X4; 1X04
JP2: PINHD-2X12; 2X12
R37, R38, R39, R40: R-US_R0805; R0805
S19, S20: SWITCH-SPDTPTH; SWITCH-SPDT

Connections:
GND: C19.2, C20.2, IC19.3 (GND), IC20.3 (GND), JP1.4, JP3.4, S19.3 (S), S20.3 (S); also elsewhere on the board
unnamed: C20.1, IC20.2 (I), R40.2
unnamed: R38.1, R40.1, S20.2
unnamed: C19.1, IC19.2 (I), R39.2
unnamed: R37.1, R39.1, S19.2
RCV_ENABLE: IC20.4 (O), JP3.3
RCV_ROW0: JP2.9, JP2.10; also elsewhere on the board
RCV_ROW1: JP2.13, JP2.14; also elsewhere on the board
RCV_ROW2: JP2.17, JP2.18; also elsewhere on the board
RCV_ROW3: JP2.21, JP2.22; also elsewhere on the board
RCV_SEL0: JP1.3; also elsewhere on the board
RCV_SEL1: JP2.5, JP2.6; also elsewhere on the board
RCV_SEL2: JP2.7, JP2.8; also elsewhere on the board
SND_ENABLE: IC19.4 (O), JP3.2
SND_ROW0: JP2.11, JP2.12; also elsewhere on the board
SND_ROW1: JP2.15, JP2.16; also elsewhere on the board
SND_ROW2: JP2.19, JP2.20; also elsewhere on the board
SND_ROW3: JP2.23, JP2.24; also elsewhere on the board
SND_SEL0: JP1.2; also elsewhere on the board
SND_SEL1: JP2.1, JP2.2; also elsewhere on the board
SND_SEL2: JP2.3, JP2.4; also elsewhere on the board
VCC: IC19.5 (VCC), IC20.5 (VCC), JP1.1, JP3.1, R37.2, R38.2; also elsewhere on the board

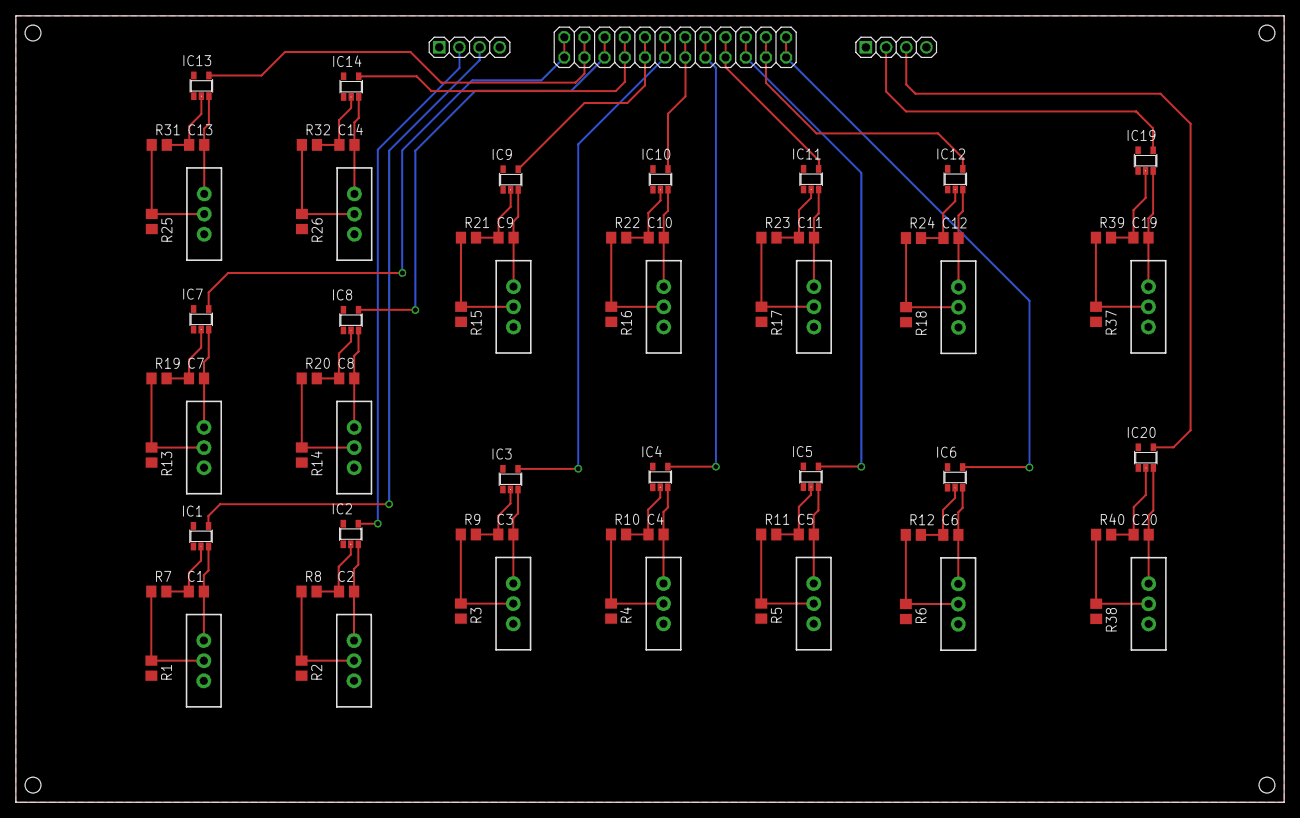
[picture p324: board mini-store-selector.brd from above]

Board: 2 copper layers, 159.8 x 99.1 mm, 83 parts (0 on the bottom side), 50 nets.
