prpplague/witch_dev/block-designs/witch-phase2/interconnects/ministore-interconnect/ministore-interconnect.brd

## EAGLE design block-designs/witch-phase2/interconnects/ministore-interconnect/ministore-interconnect.brd (2016-08-27)

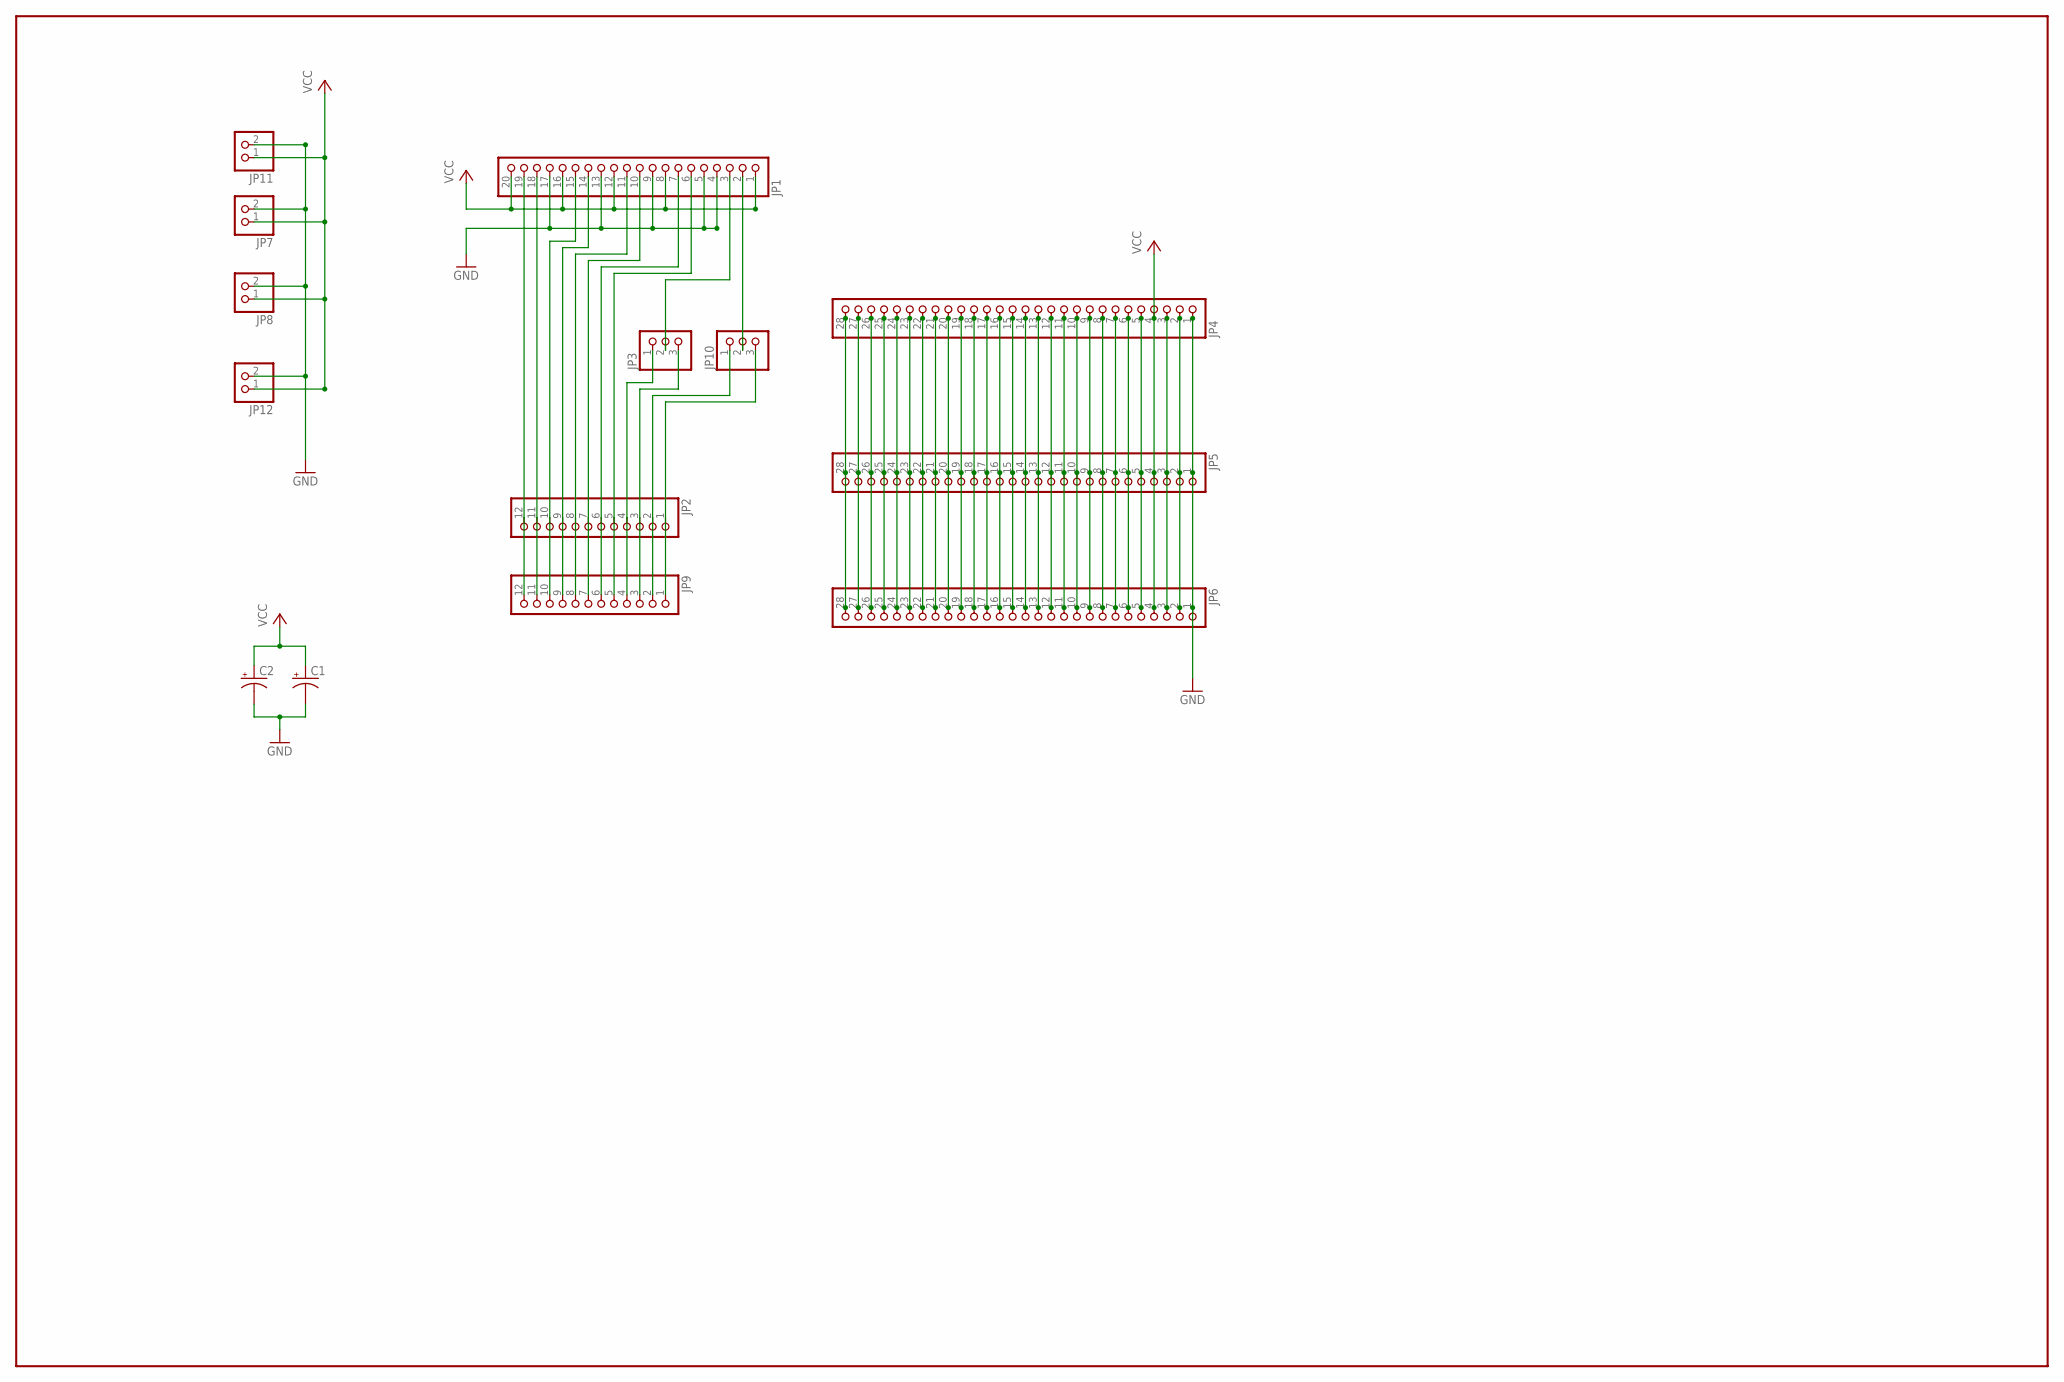
[picture p325: schematic ministore-interconnect.sch]

Parts:
C1, C2: CPOL-USE15-6AXIAL; E15-6
JP1: PINHD-1X20; 1X20
JP2, JP9: PINHD-1X12; 1X12
JP3, JP10: PINHD-1X3; 1X03
JP4, JP5, JP6: PINHD-1X28; 1X28
JP7, JP8, JP11, JP12: PINHD-1X2; 1X02

Connections:
GND: C1.-, C2.-, JP1.4, JP1.5, JP1.9, JP1.13, JP1.17, JP4.1, JP5.1, JP6.1, JP7.2, JP8.2, JP11.2, JP12.2
unnamed: JP4.28, JP5.28, JP6.28
unnamed: JP4.27, JP5.27, JP6.27
unnamed: JP4.26, JP5.26, JP6.26
unnamed: JP4.25, JP5.25, JP6.25
unnamed: JP4.24, JP5.24, JP6.24
unnamed: JP4.23, JP5.23, JP6.23
unnamed: JP4.22, JP5.22, JP6.22
unnamed: JP4.21, JP5.21, JP6.21
unnamed: JP4.20, JP5.20, JP6.20
unnamed: JP4.19, JP5.19, JP6.19
unnamed: JP4.18, JP5.18, JP6.18
unnamed: JP4.17, JP5.17, JP6.17
unnamed: JP4.16, JP5.16, JP6.16
unnamed: JP4.15, JP5.15, JP6.15
unnamed: JP4.14, JP5.14, JP6.14
unnamed: JP4.13, JP5.13, JP6.13
unnamed: JP4.12, JP5.12, JP6.12
unnamed: JP4.11, JP5.11, JP6.11
unnamed: JP4.10, JP5.10, JP6.10
unnamed: JP4.9, JP5.9, JP6.9
unnamed: JP4.8, JP5.8, JP6.8
unnamed: JP4.7, JP5.7, JP6.7
unnamed: JP4.6, JP5.6, JP6.6
unnamed: JP4.5, JP5.5, JP6.5
unnamed: JP4.3, JP5.3, JP6.3
unnamed: JP4.2, JP5.2, JP6.2
unnamed: JP1.19, JP2.12, JP9.12
unnamed: JP1.18, JP2.11, JP9.11
unnamed: JP1.15, JP2.10, JP9.10
unnamed: JP1.14, JP2.9, JP9.9
unnamed: JP1.11, JP2.8, JP9.8
unnamed: JP1.10, JP2.7, JP9.7
unnamed: JP1.7, JP2.6, JP9.6
unnamed: JP1.6, JP2.5, JP9.5
unnamed: JP2.4, JP3.1, JP9.4
unnamed: JP2.3, JP3.3, JP9.3
unnamed: JP2.2, JP9.2, JP10.1
unnamed: JP1.3, JP3.2
unnamed: JP1.2, JP10.2
unnamed: JP2.1, JP9.1, JP10.3
VCC: C1.+, C2.+, JP1.1, JP1.8, JP1.12, JP1.16, JP1.20, JP4.4, JP5.4, JP6.4, JP7.1, JP8.1, JP11.1, JP12.1

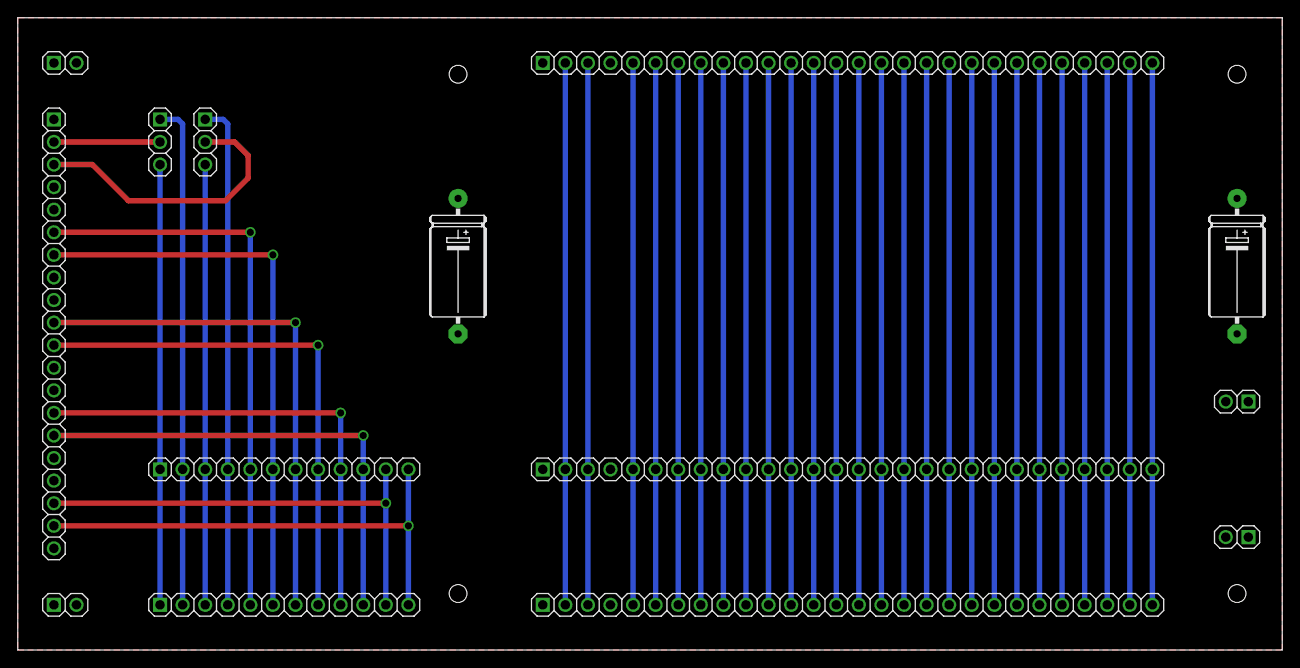
[picture p326: board ministore-interconnect.brd from above]

Board: 2 copper layers, 142.2 x 71.1 mm, 14 parts (0 on the bottom side), 42 nets.
