prpplague/witch_dev/block-designs/witch-phase2/dekatron-sim/dekatron-sim-4017-A4/dekatron-sim-4017-a4.brd

## EAGLE design block-designs/witch-phase2/dekatron-sim/dekatron-sim-4017-A4/dekatron-sim-4017-a4.brd (2016-08-27)

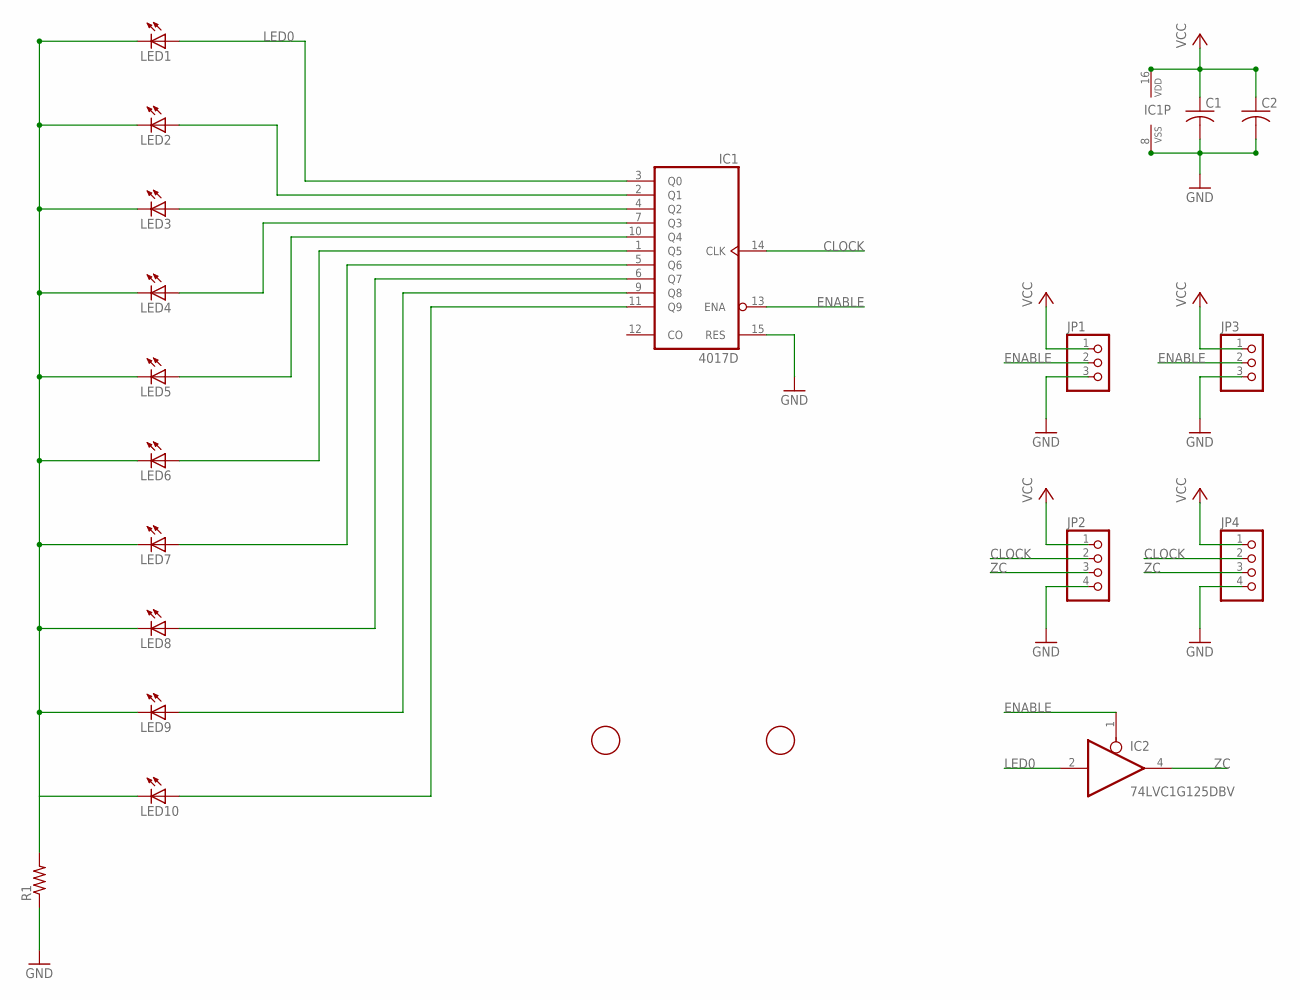
[picture p327: schematic dekatron-sim-4017-a4.sch]

Parts:
C1, C2: C-USC0805; C0805
FID1, FID2: FIDUCIAL; FIDUCIAL_1MM
IC1: 4017D; SO16
IC2: 74LVC1G125DBV; SOT23-5
JP1, JP3: PINHD-1X3; 1X03
JP2, JP4: PINHD-1X4; 1X04
LED1, LED2, LED3, LED4, LED5, LED6, LED7, LED8, LED9, LED10: RED; CHIP-LED0805
R1: R-US_R0805; R0805

Connections:
CLOCK: IC1.14 (CLK), JP2.2, JP4.2
ENABLE: IC1.13 (ENA), IC2.1 (OE), JP1.2, JP3.2
GND: C1.2, C2.2, IC1.8 (VSS), IC1.15 (RES), IC2.3 (GND), JP1.3, JP2.4, JP3.3, JP4.4, R1.1
LED0: IC1.3 (Q0), IC2.2 (I), LED1.A
LED1: IC1.2 (Q1), LED2.A
LED3: IC1.7 (Q3), LED4.A
LED4: IC1.10 (Q4), LED5.A
LED5: IC1.1 (Q5), LED6.A
LED6: IC1.5 (Q6), LED7.A
LED7: IC1.6 (Q7), LED8.A
LED8: IC1.9 (Q8), LED9.A
LED9: IC1.11 (Q9), LED10.A
LED_SINK: LED1.C, LED2.C, LED3.C, LED4.C, LED5.C, LED6.C, LED7.C, LED8.C, LED9.C, LED10.C, R1.2
unnamed: IC1.4 (Q2), LED3.A
VCC: C1.1, C2.1, IC1.16 (VDD), IC2.5 (VCC), JP1.1, JP2.1, JP3.1, JP4.1
ZC: IC2.4 (O), JP2.3, JP4.3

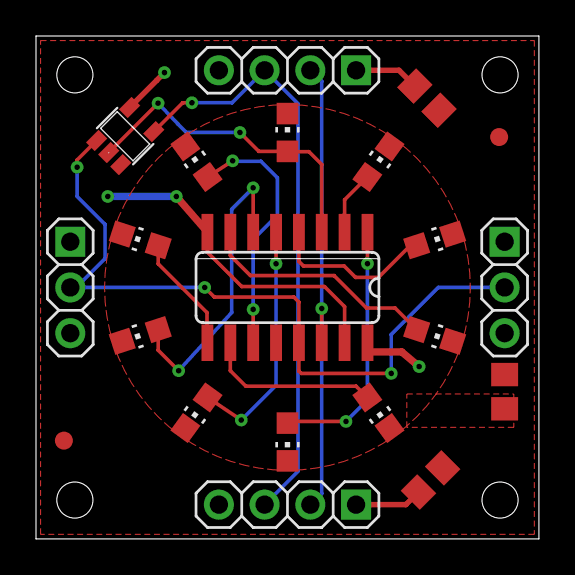
[picture p328: board dekatron-sim-4017-a4.brd from above]

Board: 2 copper layers, 27.9 x 27.9 mm, 21 parts (0 on the bottom side), 16 nets.
