prpplague/witch_dev/block-designs/witch-phase2/tester-debug/keyboard-tester/keyboard-tester.brd

## EAGLE design block-designs/witch-phase2/tester-debug/keyboard-tester/keyboard-tester.brd (2016-08-27)

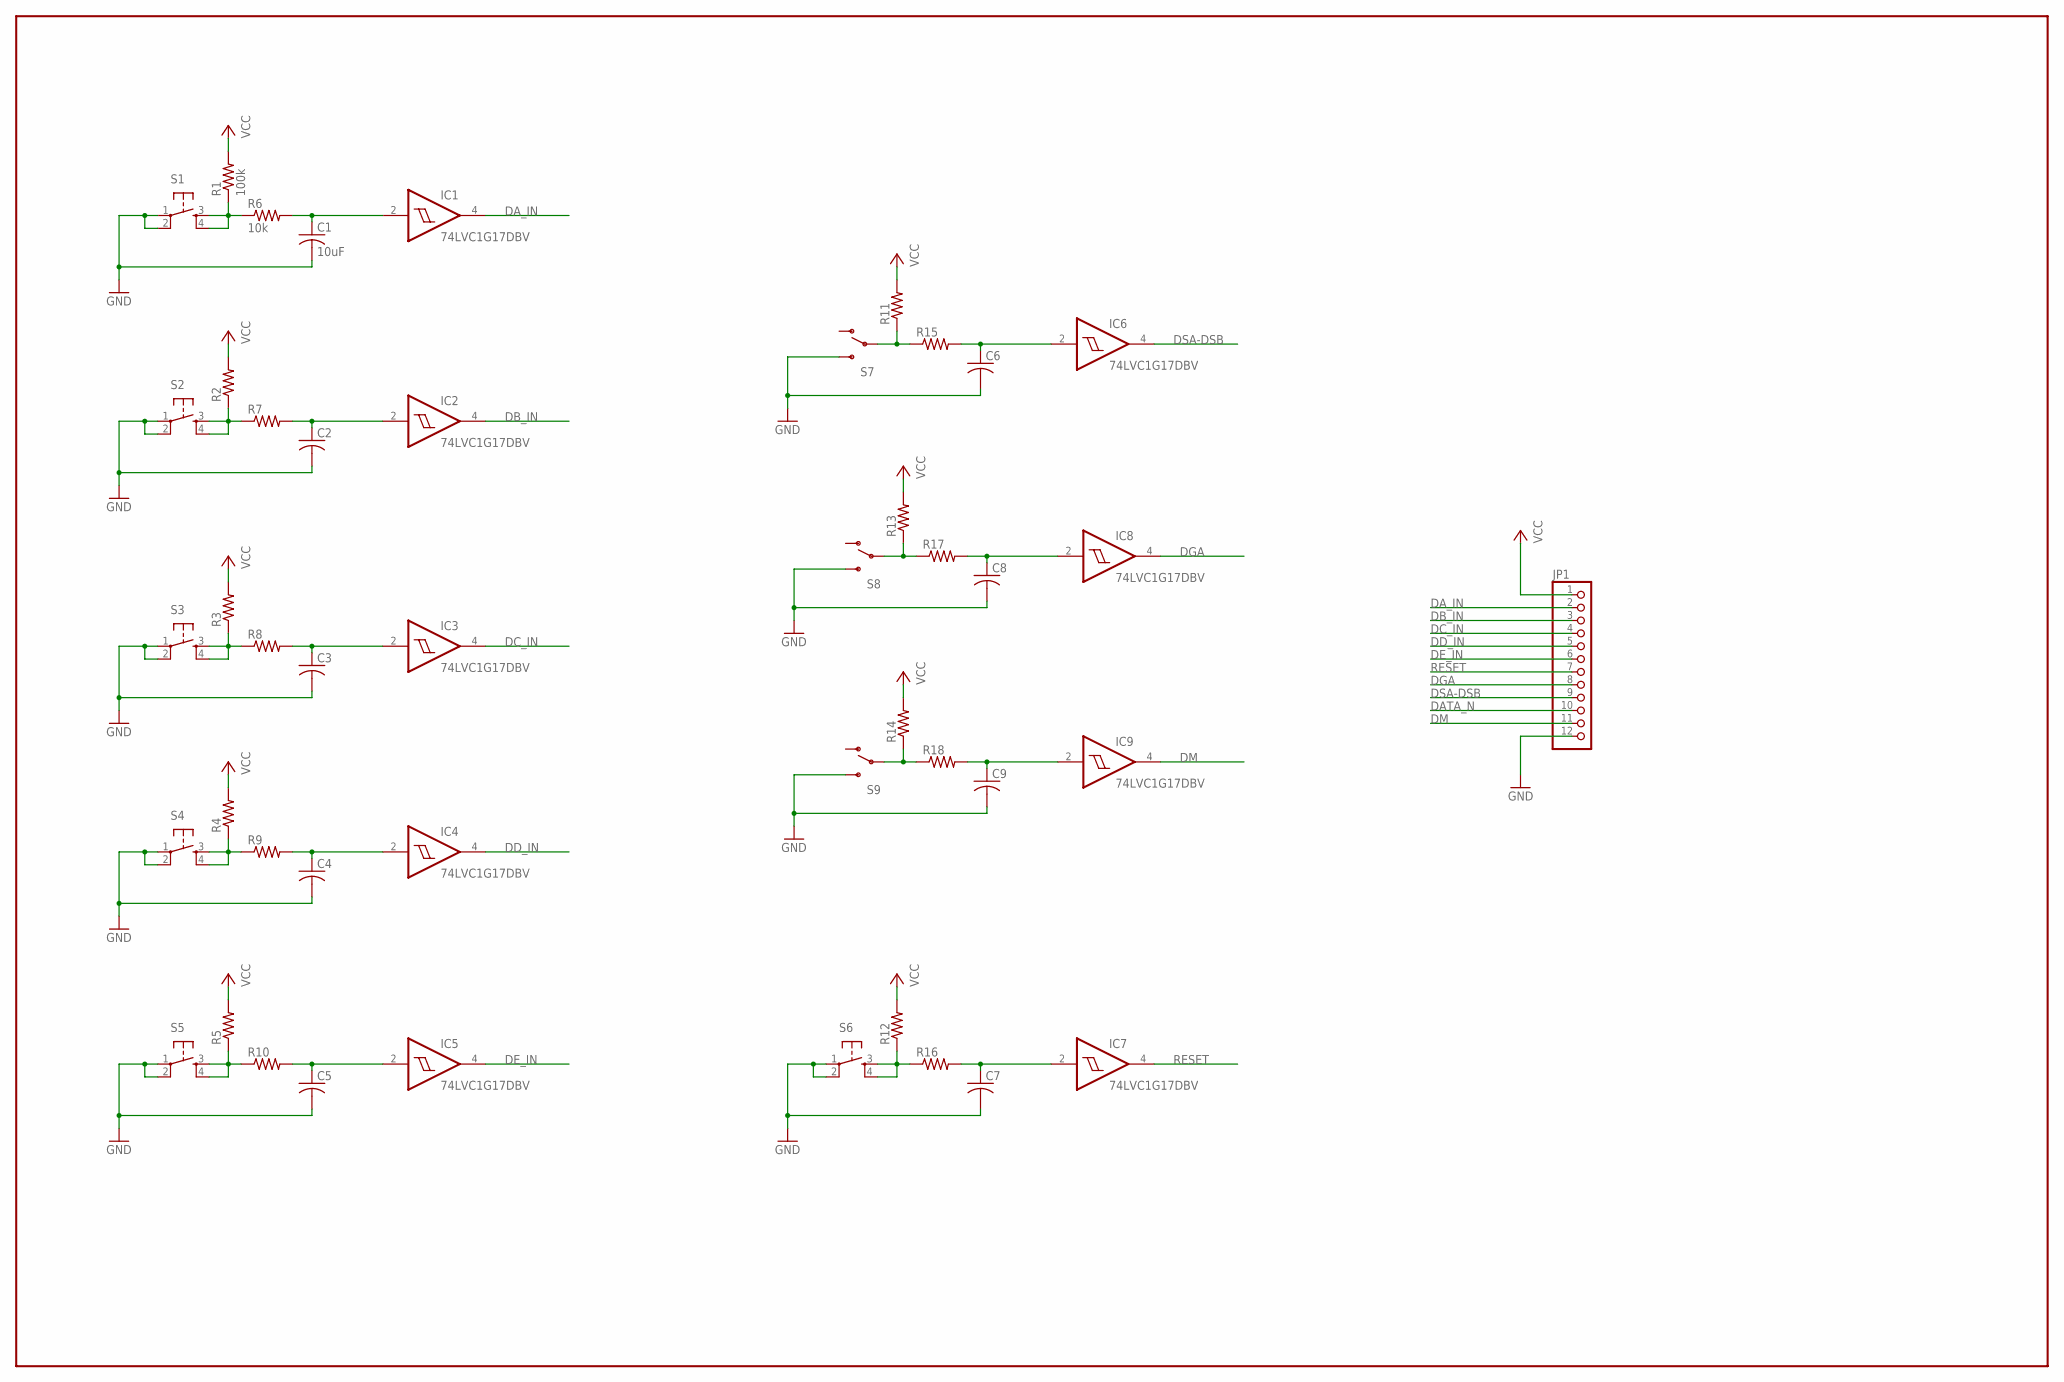
[picture p329: schematic keyboard-tester.sch]

Parts:
C1: 10uF; C0805
C2, C3, C4, C5, C6, C7, C8, C9: C-USC0805; C0805
IC1, IC2, IC3, IC4, IC5, IC6, IC7, IC8, IC9: 74LVC1G17DBV; SOT23-5
JP1: PINHD-1X12; 1X12
R1: 100k; R0805
R2, R3, R4, R5, R7, R8, R9, R10, R11, R12, R13, R14, R15, R16, R17, R18: R-US_R0805; R0805
R6: 10k; R0805
S1, S2, S3, S4, S5, S6: TAC_SWITCHPTH; TACTILE-PTH
S7, S8, S9: SWITCH-SPDTPTH; SWITCH-SPDT

Connections:
DATA_N: JP1.10
DA_IN: IC1.4 (O), JP1.2
DB_IN: IC2.4 (O), JP1.3
DC_IN: IC3.4 (O), JP1.4
DD_IN: IC4.4 (O), JP1.5
DE_IN: IC5.4 (O), JP1.6
DGA: IC8.4 (O), JP1.8
DM: IC9.4 (O), JP1.11
DSA-DSB: IC6.4 (O), JP1.9
GND: C1.2, C2.2, C3.2, C4.2, C5.2, C6.2, C7.2, C8.2, C9.2, IC1.3 (GND), IC2.3 (GND), IC3.3 (GND), IC4.3 (GND), IC5.3 (GND), IC6.3 (GND), IC7.3 (GND), IC8.3 (GND), IC9.3 (GND), JP1.12, S1.1, S1.2, S2.1, S2.2, S3.1, S3.2, S4.1, S4.2, S5.1, S5.2, S6.1, S6.2, S7.3 (S), S8.3 (S), S9.3 (S)
unnamed: R1.1, R6.1, S1.3, S1.4
unnamed: C1.1, IC1.2 (I), R6.2
unnamed: C2.1, IC2.2 (I), R7.2
unnamed: R2.1, R7.1, S2.3, S2.4
unnamed: C3.1, IC3.2 (I), R8.2
unnamed: R3.1, R8.1, S3.3, S3.4
unnamed: C4.1, IC4.2 (I), R9.2
unnamed: R4.1, R9.1, S4.3, S4.4
unnamed: C5.1, IC5.2 (I), R10.2
unnamed: R5.1, R10.1, S5.3, S5.4
unnamed: C7.1, IC7.2 (I), R16.2
unnamed: R12.1, R16.1, S6.3, S6.4
unnamed: C6.1, IC6.2 (I), R15.2
unnamed: R11.1, R15.1, S7.2
unnamed: C8.1, IC8.2 (I), R17.2
unnamed: R13.1, R17.1, S8.2
unnamed: C9.1, IC9.2 (I), R18.2
unnamed: R14.1, R18.1, S9.2
RESET: IC7.4 (O), JP1.7
VCC: IC1.5 (VCC), IC2.5 (VCC), IC3.5 (VCC), IC4.5 (VCC), IC5.5 (VCC), IC6.5 (VCC), IC7.5 (VCC), IC8.5 (VCC), IC9.5 (VCC), JP1.1, R1.2, R2.2, R3.2, R4.2, R5.2, R11.2, R12.2, R13.2, R14.2

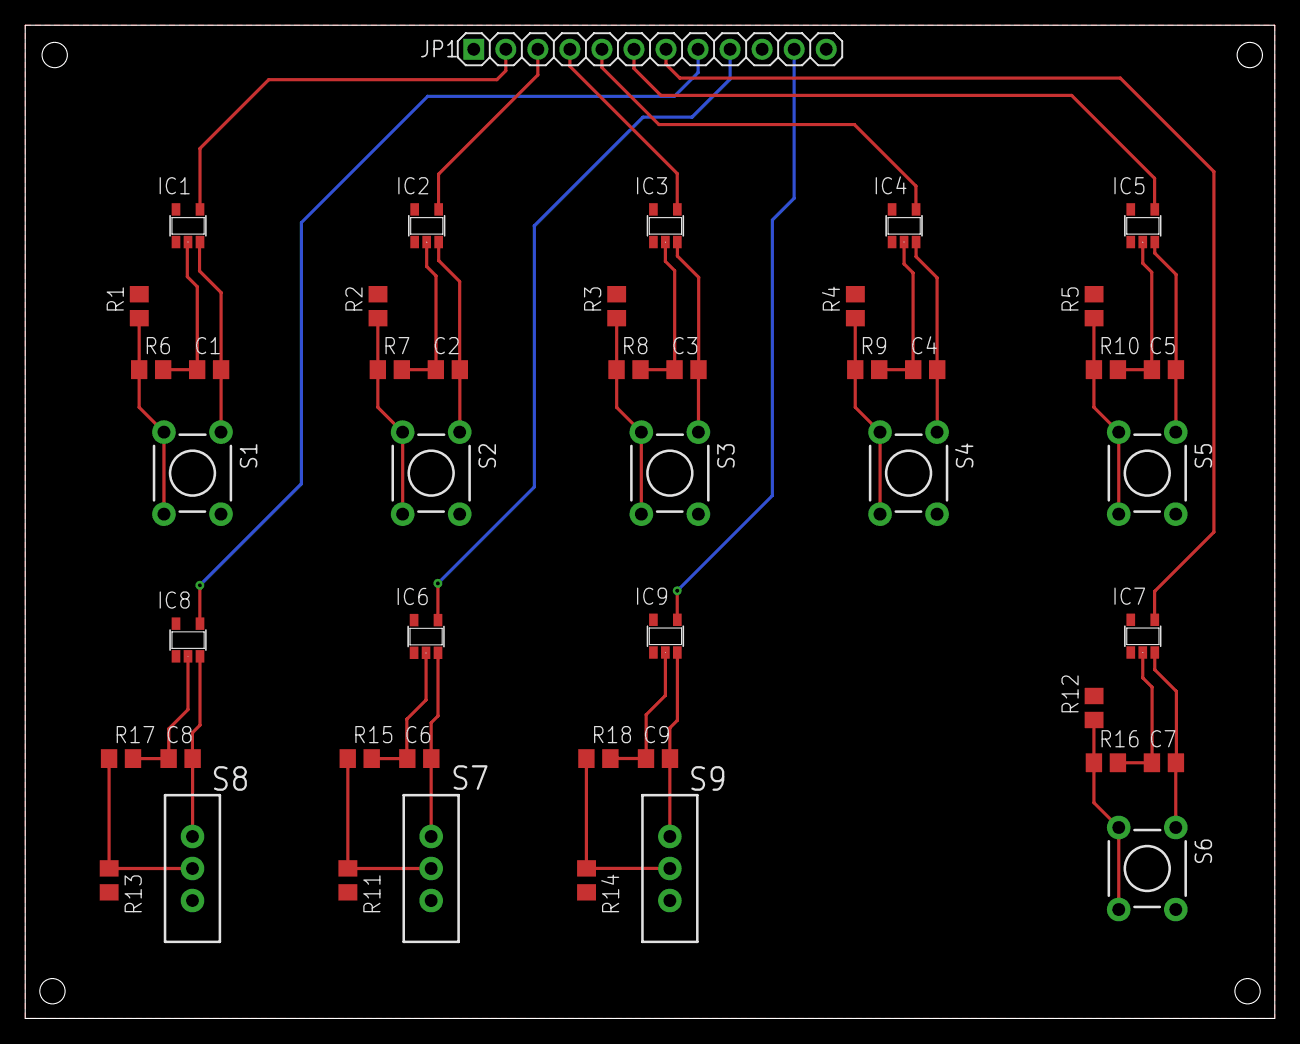
[picture p330: board keyboard-tester.brd from above]

Board: 2 copper layers, 99.1 x 78.7 mm, 46 parts (0 on the bottom side), 29 nets.
