prpplague/witch_dev/block-designs/witch-phase2/store-row-select/store-row-select.brd

## EAGLE design block-designs/witch-phase2/store-row-select/store-row-select.brd (2016-06-05)

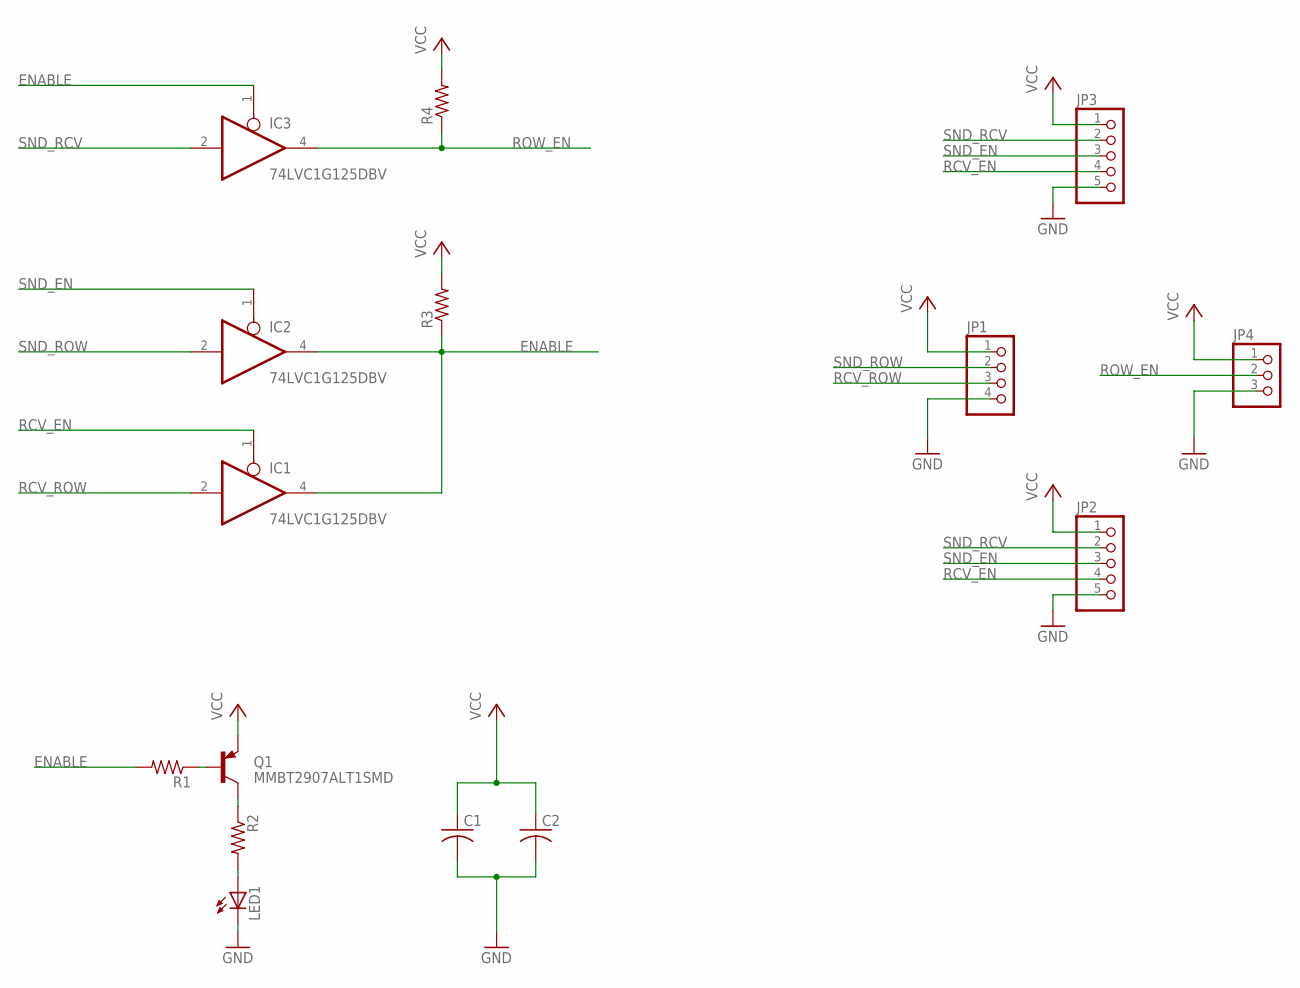
[picture p331: schematic store-row-select.sch]

Parts:
C1, C2: C-USC0805; C0805
IC1, IC2, IC3: 74LVC1G125DBV; SOT23-5
JP1: PINHD-1X4; 1X04
JP2, JP3: PINHD-1X5; 1X05
JP4: PINHD-1X3; 1X03
LED1: LEDCHIP-LED0805; CHIP-LED0805
Q1: MMBT2907ALT1SMD; SOT23-BEC
R1, R2, R3, R4: R-US_R0805; R0805

Connections:
ENABLE: IC1.4 (O), IC2.4 (O), IC3.1 (OE), R1.2, R3.1
GND: C1.2, C2.2, IC1.3 (GND), IC2.3 (GND), IC3.3 (GND), JP1.4, JP2.5, JP3.5, JP4.3, LED1.C
unnamed: Q1.B, R1.1
unnamed: Q1.C, R2.1
unnamed: LED1.A, R2.2
RCV_EN: IC1.1 (OE), JP2.4, JP3.4
RCV_ROW: IC1.2 (I), JP1.3
ROW_EN: IC3.4 (O), JP4.2, R4.1
SND_EN: IC2.1 (OE), JP2.3, JP3.3
SND_RCV: IC3.2 (I), JP2.2, JP3.2
SND_ROW: IC2.2 (I), JP1.2
VCC: C1.1, C2.1, IC1.5 (VCC), IC2.5 (VCC), IC3.5 (VCC), JP1.1, JP2.1, JP3.1, JP4.1, Q1.E, R3.2, R4.2

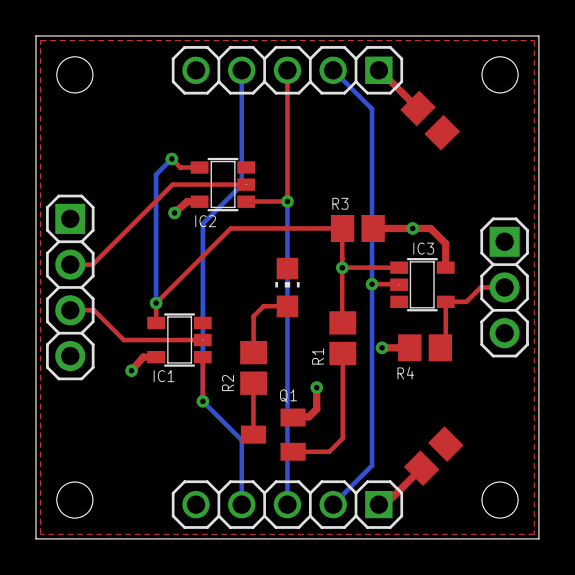
[picture p332: board store-row-select.brd from above]

Board: 2 copper layers, 27.9 x 27.9 mm, 15 parts (0 on the bottom side), 12 nets.
