prpplague/witch_dev/block-designs/witch-phase2/store-ctrl-block/store-ctrl-block.brd

## EAGLE design block-designs/witch-phase2/store-ctrl-block/store-ctrl-block.brd (2016-06-05)

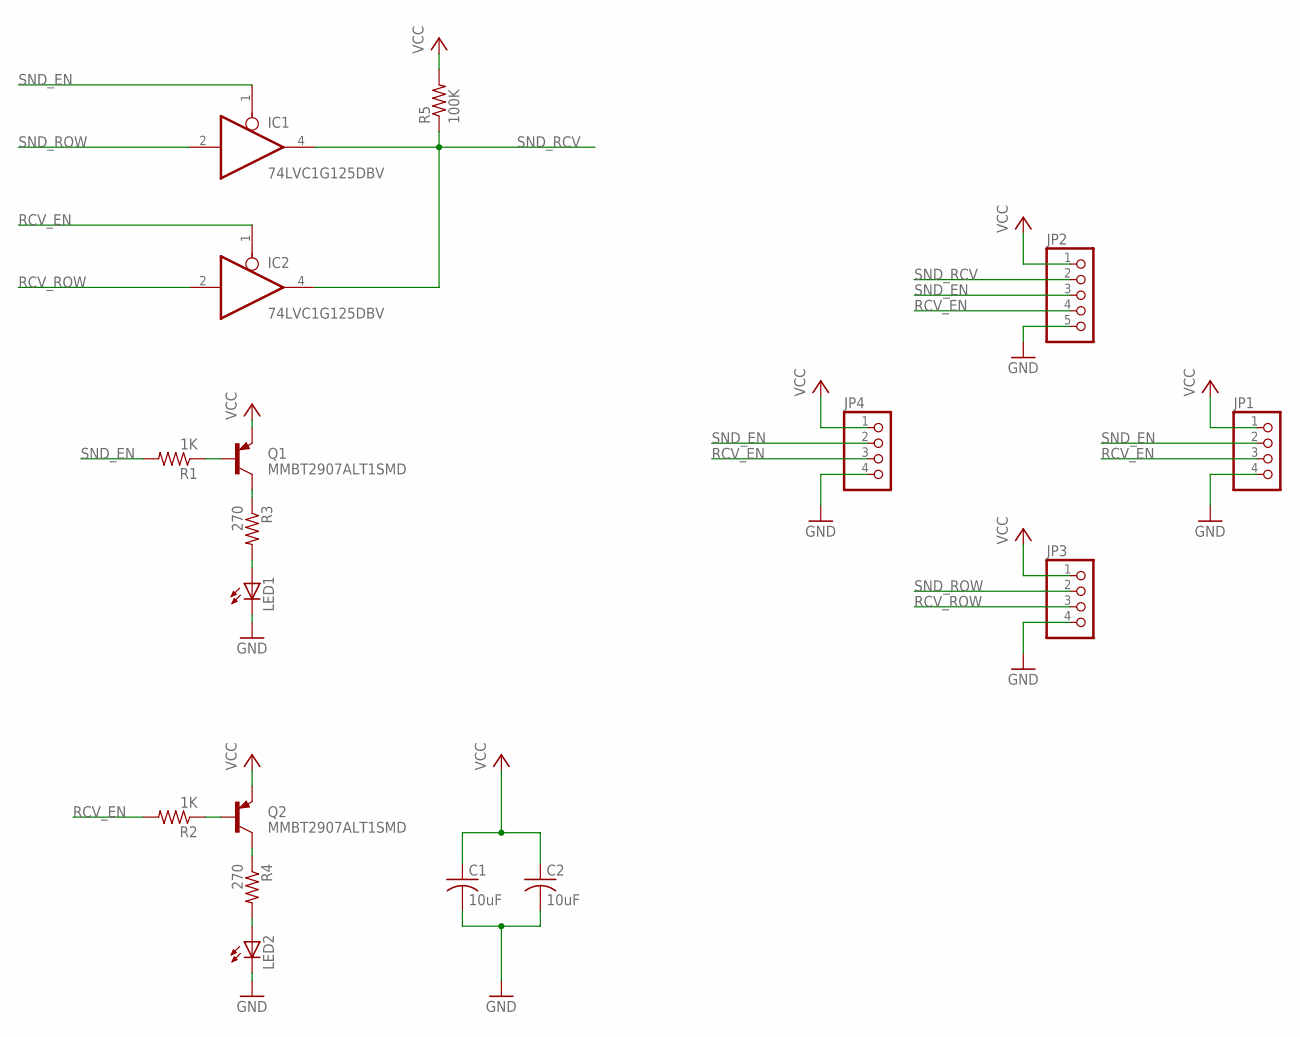
[picture p333: schematic store-ctrl-block.sch]

Parts:
C1, C2: 10uF; C0805
IC1, IC2: 74LVC1G125DBV; SOT23-5
JP1, JP3, JP4: PINHD-1X4; 1X04
JP2: PINHD-1X5; 1X05
LED1, LED2: LEDCHIP-LED0805; CHIP-LED0805
Q1, Q2: MMBT2907ALT1SMD; SOT23-BEC
R1, R2: 1K; R0805
R3, R4: 270; R0805
R5: 100K; R0805

Connections:
GND: C1.2, C2.2, IC1.3 (GND), IC2.3 (GND), JP1.4, JP2.5, JP3.4, JP4.4, LED1.C, LED2.C
unnamed: Q2.B, R2.1
unnamed: Q1.B, R1.1
unnamed: Q2.C, R4.1
unnamed: Q1.C, R3.1
unnamed: LED1.A, R3.2
unnamed: LED2.A, R4.2
RCV_EN: IC2.1 (OE), JP1.3, JP2.4, JP4.3, R2.2
RCV_ROW: IC2.2 (I), JP3.3
SND_EN: IC1.1 (OE), JP1.2, JP2.3, JP4.2, R1.2
SND_RCV: IC1.4 (O), IC2.4 (O), JP2.2, R5.1
SND_ROW: IC1.2 (I), JP3.2
VCC: C1.1, C2.1, IC1.5 (VCC), IC2.5 (VCC), JP1.1, JP2.1, JP3.1, JP4.1, Q1.E, Q2.E, R5.2

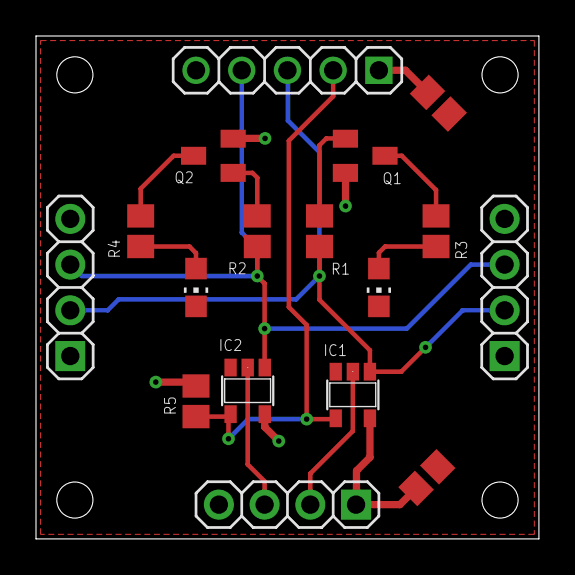
[picture p334: board store-ctrl-block.brd from above]

Board: 2 copper layers, 27.9 x 27.9 mm, 17 parts (0 on the bottom side), 13 nets.
