prpplague/witch_dev/block-designs/witch-phase2/store-row-block/store-row-block.brd

## EAGLE design block-designs/witch-phase2/store-row-block/store-row-block.brd (2016-06-05)

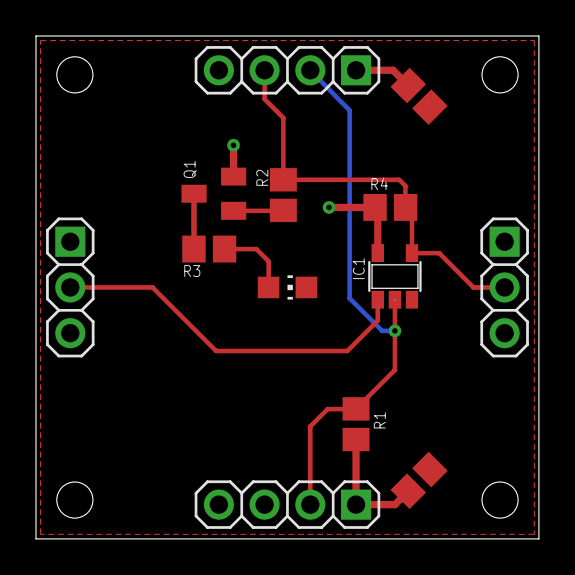
[picture p335: board store-row-block.brd from above]

Board: 2 copper layers, 27.9 x 27.9 mm, 13 parts (0 on the bottom side), 8 nets.

Parts:
C1, C4: C0805
IC1: 74LVC1G125DBV; SOT23-5
JP1, JP3: 1X03
JP2, JP4: 1X04
LED1: CHIP-LED0805
Q1: MMBT2907ALT1SMD; SOT23-BEC
R1, R2, R3, R4: R0805

Connections:
ENABLE: IC1.1, JP1.2
GND: C1.2, C4.2, IC1.3, JP1.3, JP2.4, JP3.3, JP4.4, LED1.C
unnamed: Q1.B, R2.1
unnamed: Q1.C, R3.1
unnamed: LED1.A, R3.2
ROW_EN: IC1.4, JP2.3, JP3.2, R2.2, R4.1
SND_RCV: IC1.2, JP2.2, JP4.2, R1.1
VCC: C1.1, C4.1, IC1.5, JP2.1, JP4.1, Q1.E, R1.2, R4.2
