prpplague/witch_dev/block-designs/witch-phase2/relay-set-d/relay-set-d-large-block/relay-set-d-large-block.brd

## EAGLE design block-designs/witch-phase2/relay-set-d/relay-set-d-large-block/relay-set-d-large-block.brd (2016-03-09)

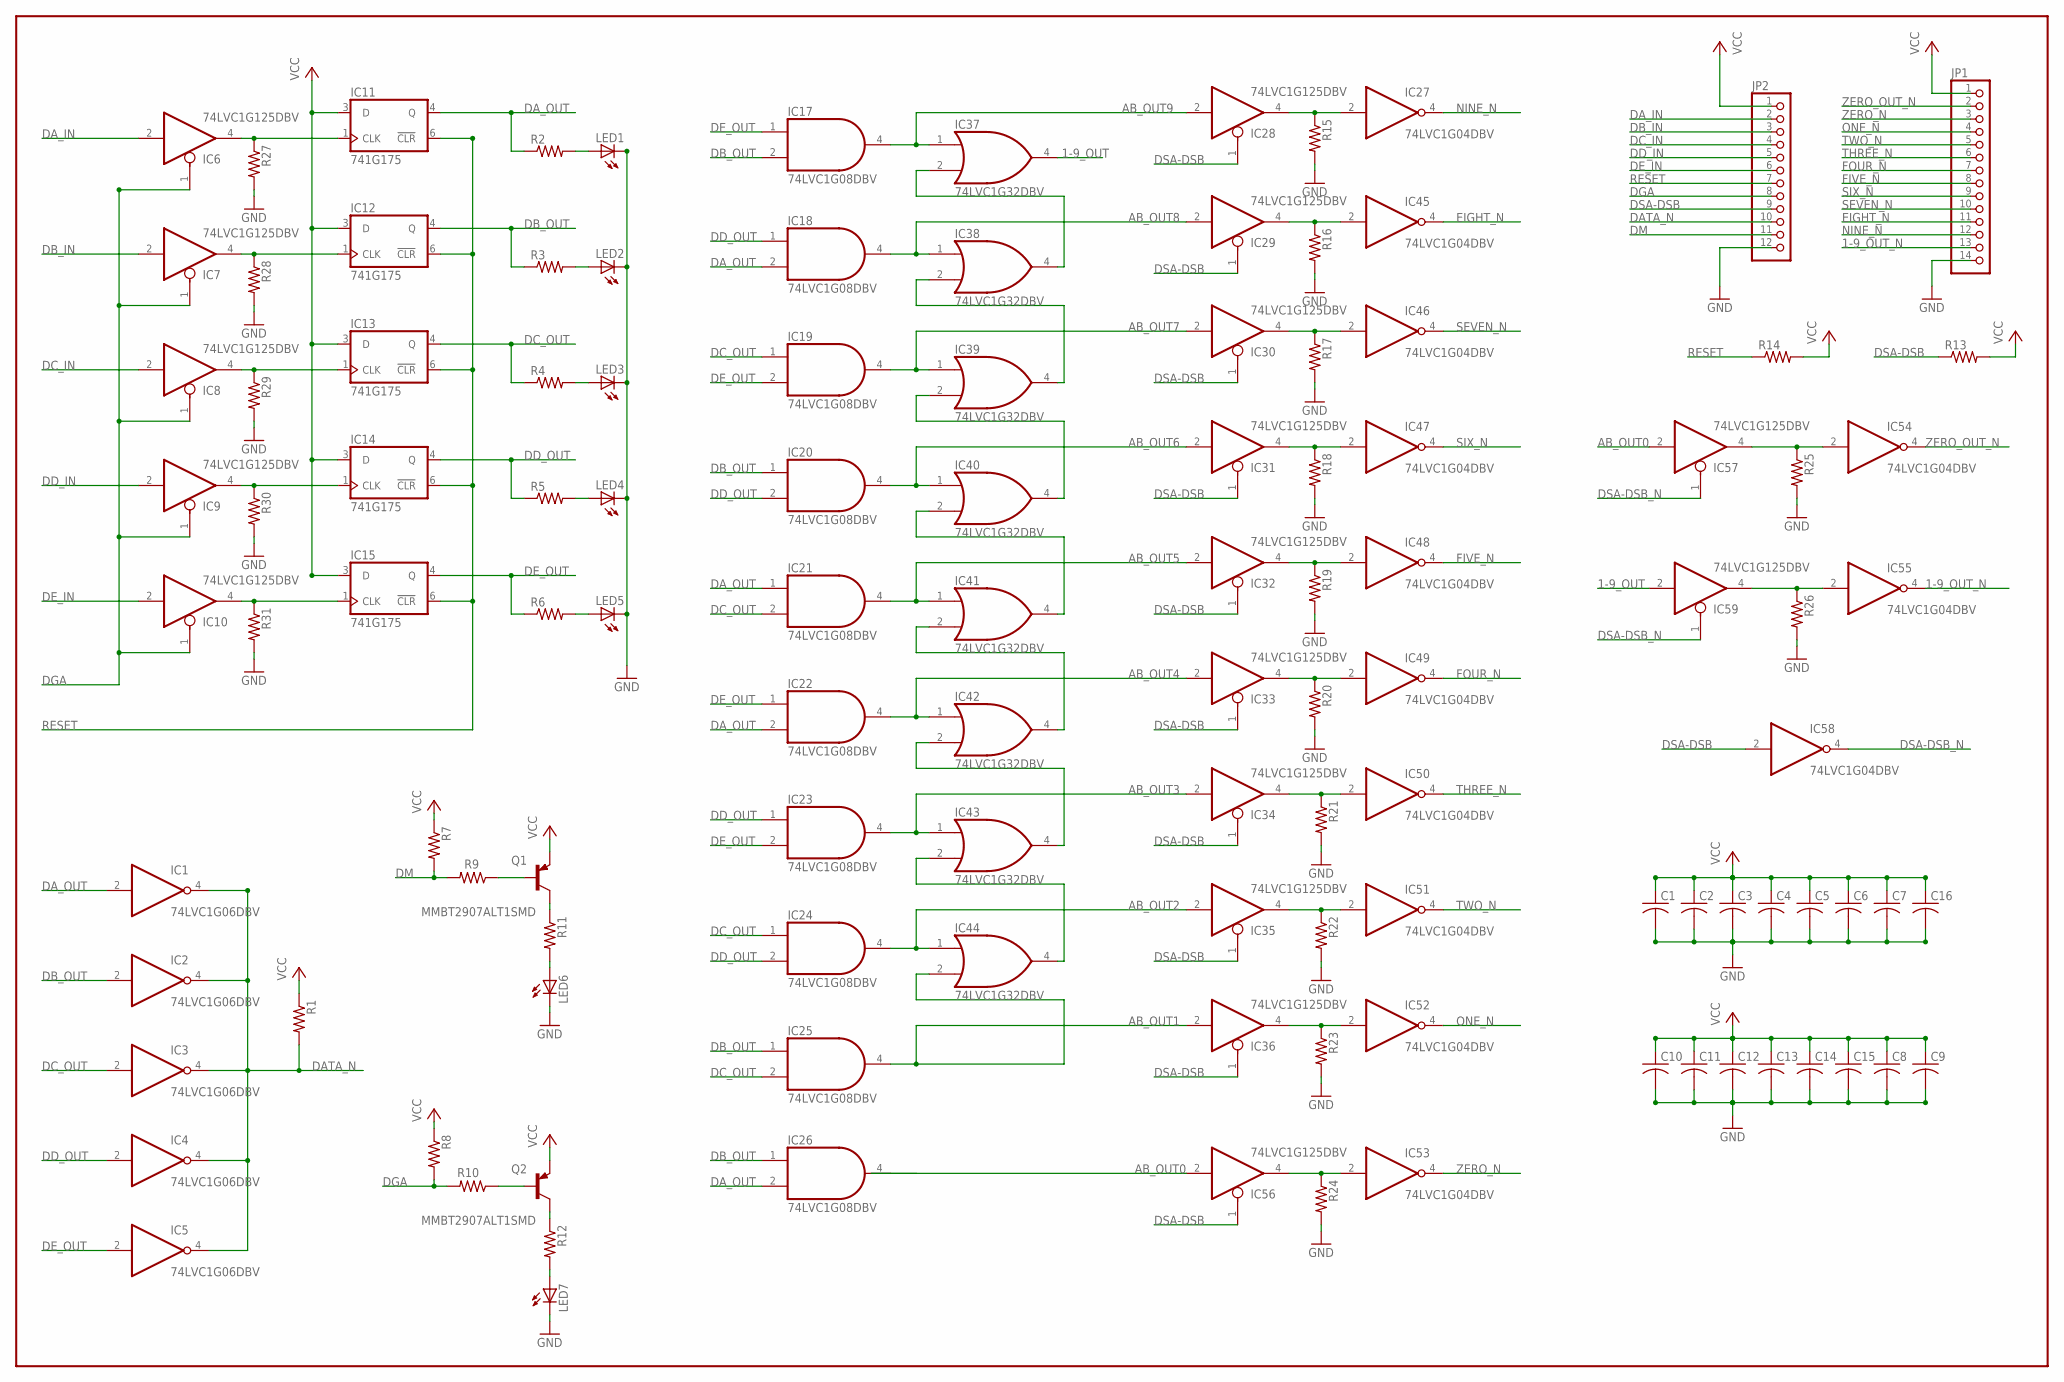
[picture p336: schematic relay-set-d-large-block.sch]

Parts:
C1, C2, C3, C4, C5, C6, C7, C8, C9, C10, C11, C12, C13, C14, C15, C16: C-USC0805; C0805
IC1, IC2, IC3, IC4, IC5: 74LVC1G06DBV; SOT23-5
IC6, IC7, IC8, IC9, IC10, IC28, IC29, IC30, IC31, IC32, IC33, IC34, IC35, IC36, IC56, IC57, IC59: 74LVC1G125DBV; SOT23-5
IC11, IC12, IC13, IC14, IC15: 741G175; DBV_R-PDSO-G6
IC17, IC18, IC19, IC20, IC21, IC22, IC23, IC24, IC25, IC26: 74LVC1G08DBV; SOT23-5
IC27, IC45, IC46, IC47, IC48, IC49, IC50, IC51, IC52, IC53, IC54, IC55, IC58: 74LVC1G04DBV; SOT23-5
IC37, IC38, IC39, IC40, IC41, IC42, IC43, IC44: 74LVC1G32DBV; SOT23-5
JP1: PINHD-1X14; 1X14
JP2: PINHD-1X12; 1X12
LED1, LED2, LED3, LED4, LED5, LED6, LED7: LEDCHIP-LED0805; CHIP-LED0805
Q1, Q2: MMBT2907ALT1SMD; SOT23-BEC
R1, R2, R3, R4, R5, R6, R7, R8, R9, R10, R11, R12, R13, R14, R15, R16, R17, R18, R19, R20, R21, R22, R23, R24, R25, R26, R27, R28, R29, R30, R31: R-US_R0805; R0805

Connections:
1-9_OUT: IC37.4 (O), IC59.2 (I)
1-9_OUT_N: IC55.4 (O), JP1.13
AB_OUT: IC26.4 (O)
AB_OUT0: IC56.2 (I), IC57.2 (I)
AB_OUT1: IC25.4 (O), IC36.2 (I), IC44.2 (I1)
AB_OUT2: IC24.4 (O), IC35.2 (I), IC44.1 (I0)
AB_OUT3: IC23.4 (O), IC34.2 (I), IC43.1 (I0)
AB_OUT4: IC22.4 (O), IC33.2 (I), IC42.1 (I0)
AB_OUT5: IC21.4 (O), IC32.2 (I), IC41.1 (I0)
AB_OUT6: IC20.4 (O), IC31.2 (I), IC40.1 (I0)
AB_OUT7: IC19.4 (O), IC30.2 (I), IC39.1 (I0)
AB_OUT8: IC18.4 (O), IC29.2 (I), IC38.1 (I0)
AB_OUT9: IC17.4 (O), IC28.2 (I), IC37.1 (I0)
DA: IC6.4 (O), IC11.1 (CLK), R27.1
DATA_N: IC1.4 (O), IC2.4 (O), IC3.4 (O), IC4.4 (O), IC5.4 (O), JP2.10, R1.2
DA_IN: IC6.2 (I), JP2.2
DA_OUT: IC1.2 (I), IC11.4 (Q), IC18.2 (I1), IC21.1 (I0), IC22.2 (I1), IC26.2 (I1), R2.1
DB: IC7.4 (O), IC12.1 (CLK), R28.1
DB_IN: IC7.2 (I), JP2.3
DB_OUT: IC2.2 (I), IC12.4 (Q), IC17.2 (I1), IC20.1 (I0), IC25.1 (I0), IC26.1 (I0), R3.1
DC: IC8.4 (O), IC13.1 (CLK), R29.1
DC_IN: IC8.2 (I), JP2.4
DC_OUT: IC3.2 (I), IC13.4 (Q), IC19.1 (I0), IC21.2 (I1), IC24.1 (I0), IC25.2 (I1), R4.1
DD: IC9.4 (O), IC14.1 (CLK), R30.1
DD_IN: IC9.2 (I), JP2.5
DD_OUT: IC4.2 (I), IC14.4 (Q), IC18.1 (I0), IC20.2 (I1), IC23.1 (I0), IC24.2 (I1), R5.1
DE: IC10.4 (O), IC15.1 (CLK), R31.1
DE_IN: IC10.2 (I), JP2.6
DE_OUT: IC5.2 (I), IC15.4 (Q), IC17.1 (I0), IC19.2 (I1), IC22.1 (I0), IC23.2 (I1), R6.1
DGA: IC6.1 (OE), IC7.1 (OE), IC8.1 (OE), IC9.1 (OE), IC10.1 (OE), JP2.8, R8.2, R10.2
DM: JP2.11, R7.2, R9.2
DSA-DSB: IC28.1 (OE), IC29.1 (OE), IC30.1 (OE), IC31.1 (OE), IC32.1 (OE), IC33.1 (OE), IC34.1 (OE), IC35.1 (OE), IC36.1 (OE), IC56.1 (OE), IC58.2 (I), JP2.9, R13.1
DSA-DSB_N: IC57.1 (OE), IC58.4 (O), IC59.1 (OE)
EIGHT: IC29.4 (O), IC45.2 (I), R16.1
EIGHT_N: IC45.4 (O), JP1.11
FIVE: IC32.4 (O), IC48.2 (I), R19.1
FIVE_N: IC48.4 (O), JP1.8
FOUR: IC33.4 (O), IC49.2 (I), R20.1
FOUR_N: IC49.4 (O), JP1.7
GND: C1.2, C2.2, C3.2, C4.2, C5.2, C6.2, C7.2, C8.2, C9.2, C10.2, C11.2, C12.2, C13.2, C14.2, C15.2, C16.2, IC1.3 (GND), IC2.3 (GND), IC3.3 (GND), IC4.3 (GND), IC5.3 (GND), IC6.3 (GND), IC7.3 (GND), IC8.3 (GND), IC9.3 (GND), IC10.3 (GND), IC11.2 (GND), IC12.2 (GND), IC13.2 (GND), IC14.2 (GND), IC15.2 (GND), IC17.3 (GND), IC18.3 (GND), IC19.3 (GND), IC20.3 (GND), IC21.3 (GND), IC22.3 (GND), IC23.3 (GND), IC24.3 (GND), IC25.3 (GND), IC26.3 (GND), IC27.3 (GND), IC28.3 (GND), IC29.3 (GND), IC30.3 (GND), IC31.3 (GND), IC32.3 (GND), IC33.3 (GND), IC34.3 (GND), IC35.3 (GND), IC36.3 (GND), IC37.3 (GND), IC38.3 (GND), IC39.3 (GND), IC40.3 (GND), IC41.3 (GND), IC42.3 (GND), IC43.3 (GND), IC44.3 (GND), IC45.3 (GND), IC46.3 (GND), IC47.3 (GND), IC48.3 (GND), IC49.3 (GND), IC50.3 (GND), IC51.3 (GND), IC52.3 (GND), IC53.3 (GND), IC54.3 (GND), IC55.3 (GND), IC56.3 (GND), IC57.3 (GND), IC58.3 (GND), IC59.3 (GND), JP1.14, JP2.12, LED1.C, LED2.C, LED3.C, LED4.C, LED5.C, LED6.C, LED7.C, R15.2, R16.2, R17.2, R18.2, R19.2, R20.2, R21.2, R22.2, R23.2, R24.2, R25.2, R26.2, R27.2, R28.2, R29.2, R30.2, R31.2
unnamed: IC40.2 (I1), IC41.4 (O)
unnamed: IC41.2 (I1), IC42.4 (O)
unnamed: IC42.2 (I1), IC43.4 (O)
unnamed: IC43.2 (I1), IC44.4 (O)
unnamed: Q2.B, R10.1
unnamed: IC37.2 (I1), IC38.4 (O)
unnamed: IC38.2 (I1), IC39.4 (O)
unnamed: IC39.2 (I1), IC40.4 (O)
unnamed: LED1.A, R2.2
unnamed: LED2.A, R3.2
unnamed: LED3.A, R4.2
unnamed: Q2.C, R12.1
unnamed: LED7.A, R12.2
unnamed: Q1.B, R9.1
unnamed: Q1.C, R11.1
unnamed: LED6.A, R11.2
unnamed: LED4.A, R5.2
unnamed: LED5.A, R6.2
NINE: IC27.2 (I), IC28.4 (O), R15.1
NINE_N: IC27.4 (O), JP1.12
ONE: IC36.4 (O), IC52.2 (I), R23.1
ONE_N: IC52.4 (O), JP1.4
OUT0: IC54.2 (I), IC57.4 (O), R25.1
OUT1-9: IC55.2 (I), IC59.4 (O), R26.1
RESET: IC11.6 (!CLR), IC12.6 (!CLR), IC13.6 (!CLR), IC14.6 (!CLR), IC15.6 (!CLR), JP2.7, R14.1
SEVEN: IC30.4 (O), IC46.2 (I), R17.1
SEVEN_N: IC46.4 (O), JP1.10
SIX: IC31.4 (O), IC47.2 (I), R18.1
SIX_N: IC47.4 (O), JP1.9
THREE: IC34.4 (O), IC50.2 (I), R21.1
THREE_N: IC50.4 (O), JP1.6
TWO: IC35.4 (O), IC51.2 (I), R22.1
TWO_N: IC51.4 (O), JP1.5
VCC: C1.1, C2.1, C3.1, C4.1, C5.1, C6.1, C7.1, C8.1, C9.1, C10.1, C11.1, C12.1, C13.1, C14.1, C15.1, C16.1, IC1.5 (VCC), IC2.5 (VCC), IC3.5 (VCC), IC4.5 (VCC), IC5.5 (VCC), IC6.5 (VCC), IC7.5 (VCC), IC8.5 (VCC), IC9.5 (VCC), IC10.5 (VCC), IC11.3 (D), IC11.5 (VCC), IC12.3 (D), IC12.5 (VCC), IC13.3 (D), IC13.5 (VCC), IC14.3 (D), IC14.5 (VCC), IC15.3 (D), IC15.5 (VCC), IC17.5 (VCC), IC18.5 (VCC), IC19.5 (VCC), IC20.5 (VCC), IC21.5 (VCC), IC22.5 (VCC), IC23.5 (VCC), IC24.5 (VCC), IC25.5 (VCC), IC26.5 (VCC), IC27.5 (VCC), IC28.5 (VCC), IC29.5 (VCC), IC30.5 (VCC), IC31.5 (VCC), IC32.5 (VCC), IC33.5 (VCC), IC34.5 (VCC), IC35.5 (VCC), IC36.5 (VCC), IC37.5 (VCC), IC38.5 (VCC), IC39.5 (VCC), IC40.5 (VCC), IC41.5 (VCC), IC42.5 (VCC), IC43.5 (VCC), IC44.5 (VCC), IC45.5 (VCC), IC46.5 (VCC), IC47.5 (VCC), IC48.5 (VCC), IC49.5 (VCC), IC50.5 (VCC), IC51.5 (VCC), IC52.5 (VCC), IC53.5 (VCC), IC54.5 (VCC), IC55.5 (VCC), IC56.5 (VCC), IC57.5 (VCC), IC58.5 (VCC), IC59.5 (VCC), JP1.1, JP2.1, Q1.E, Q2.E, R1.1, R7.1, R8.1, R13.2, R14.2
ZERO: IC53.2 (I), IC56.4 (O), R24.1
ZERO_N: IC53.4 (O), JP1.3
ZERO_OUT_N: IC54.4 (O), JP1.2

Board: 2 copper layers, 116 parts (8 on the bottom side), 76 nets, no tracks yet.
