prpplague/witch_dev/block-designs/witch-phase1/dekatron/witch-dekatron1.brd

## EAGLE design block-designs/witch-phase1/dekatron/witch-dekatron1.brd (2014-05-23)

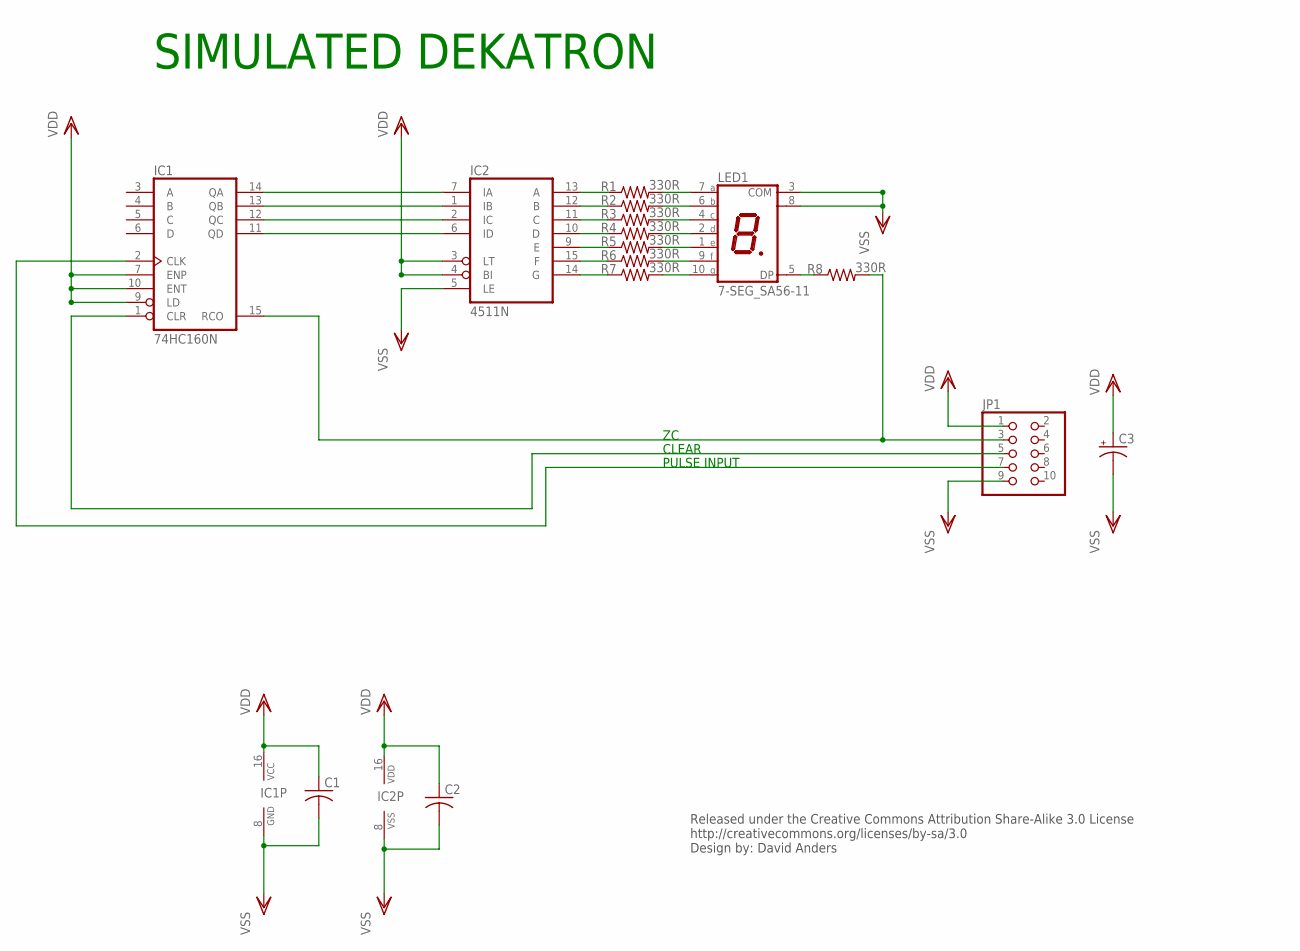
[picture p337: schematic witch-dekatron1.sch]

Parts:
C1, C2: C-US025-025X050; C025-025X050
C3: CPOL-USE2-5; E2-5
IC1: 74HC160N; DIL16
IC2: 4511N; DIL16
JP1: PINHD-2X5; 2X05
LED1: 7-SEG_SA56-11; SA56-11
R1, R2, R3, R4, R5, R6, R7, R8: 330R; 0204/5

Connections:
unnamed: IC1.15 (RCO), JP1.3, R8.2
unnamed: IC1.1 (CLR), JP1.5
unnamed: IC2.13 (A), R1.1
unnamed: IC2.12 (B), R2.1
unnamed: IC2.11 (C), R3.1
unnamed: IC2.10 (D), R4.1
unnamed: IC2.9 (E), R5.1
unnamed: IC2.15 (F), R6.1
unnamed: IC2.14 (G), R7.1
unnamed: IC1.14 (QA), IC2.7 (IA)
unnamed: IC1.13 (QB), IC2.1 (IB)
unnamed: IC1.12 (QC), IC2.2 (IC)
unnamed: IC1.11 (QD), IC2.6 (ID)
unnamed: LED1.7 (A), R1.2
unnamed: LED1.6 (B), R2.2
unnamed: LED1.4 (C), R3.2
unnamed: LED1.2 (D), R4.2
unnamed: LED1.1 (E), R5.2
unnamed: LED1.9 (F), R6.2
unnamed: LED1.10 (G), R7.2
unnamed: LED1.5 (DP), R8.1
unnamed: IC1.2 (CLK), JP1.7
VDD: C1.1, C2.1, C3.+, IC1.7 (ENP), IC1.9 (LD), IC1.10 (ENT), IC1.16 (VCC), IC2.3 (LT), IC2.4 (BI), IC2.16 (VDD), JP1.1
VSS: C1.2, C2.2, C3.-, IC1.8 (GND), IC2.5 (LE), IC2.8 (VSS), JP1.9, LED1.3 (COM), LED1.8 (COM)

Notes on the sheet:
SIMULATED DEKATRON
Released under the Creative Commons Attribution Share-Alike 3.0 License http://creativecommons.org/licenses/by-sa/3.0 Design by: David Anders
PULSE INPUT
CLEAR

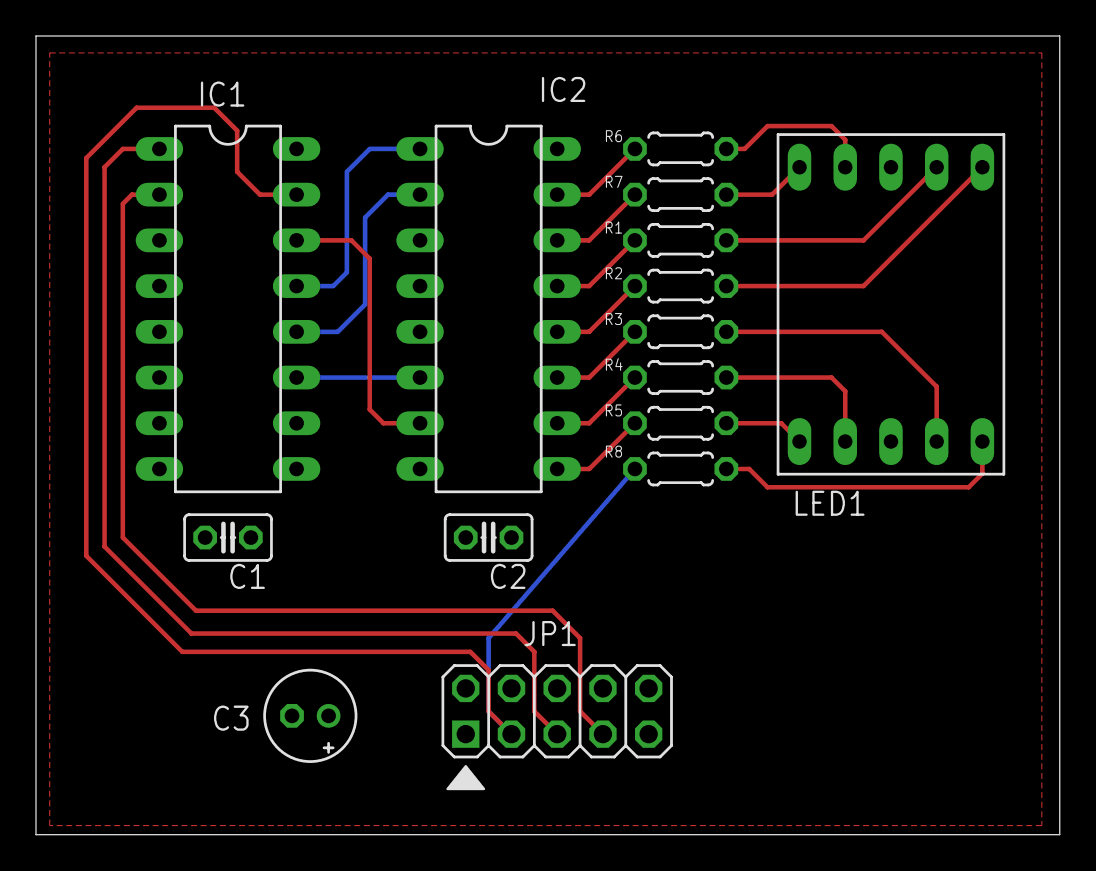
[picture p338: board witch-dekatron1.brd from above]

Board: 2 copper layers, 56.9 x 44.4 mm, 15 parts (0 on the bottom side), 24 nets.
