prpplague/witch_dev/block-designs/witch-phase1/pulse/witch-pulse1.brd

## EAGLE design block-designs/witch-phase1/pulse/witch-pulse1.brd (2014-10-02)

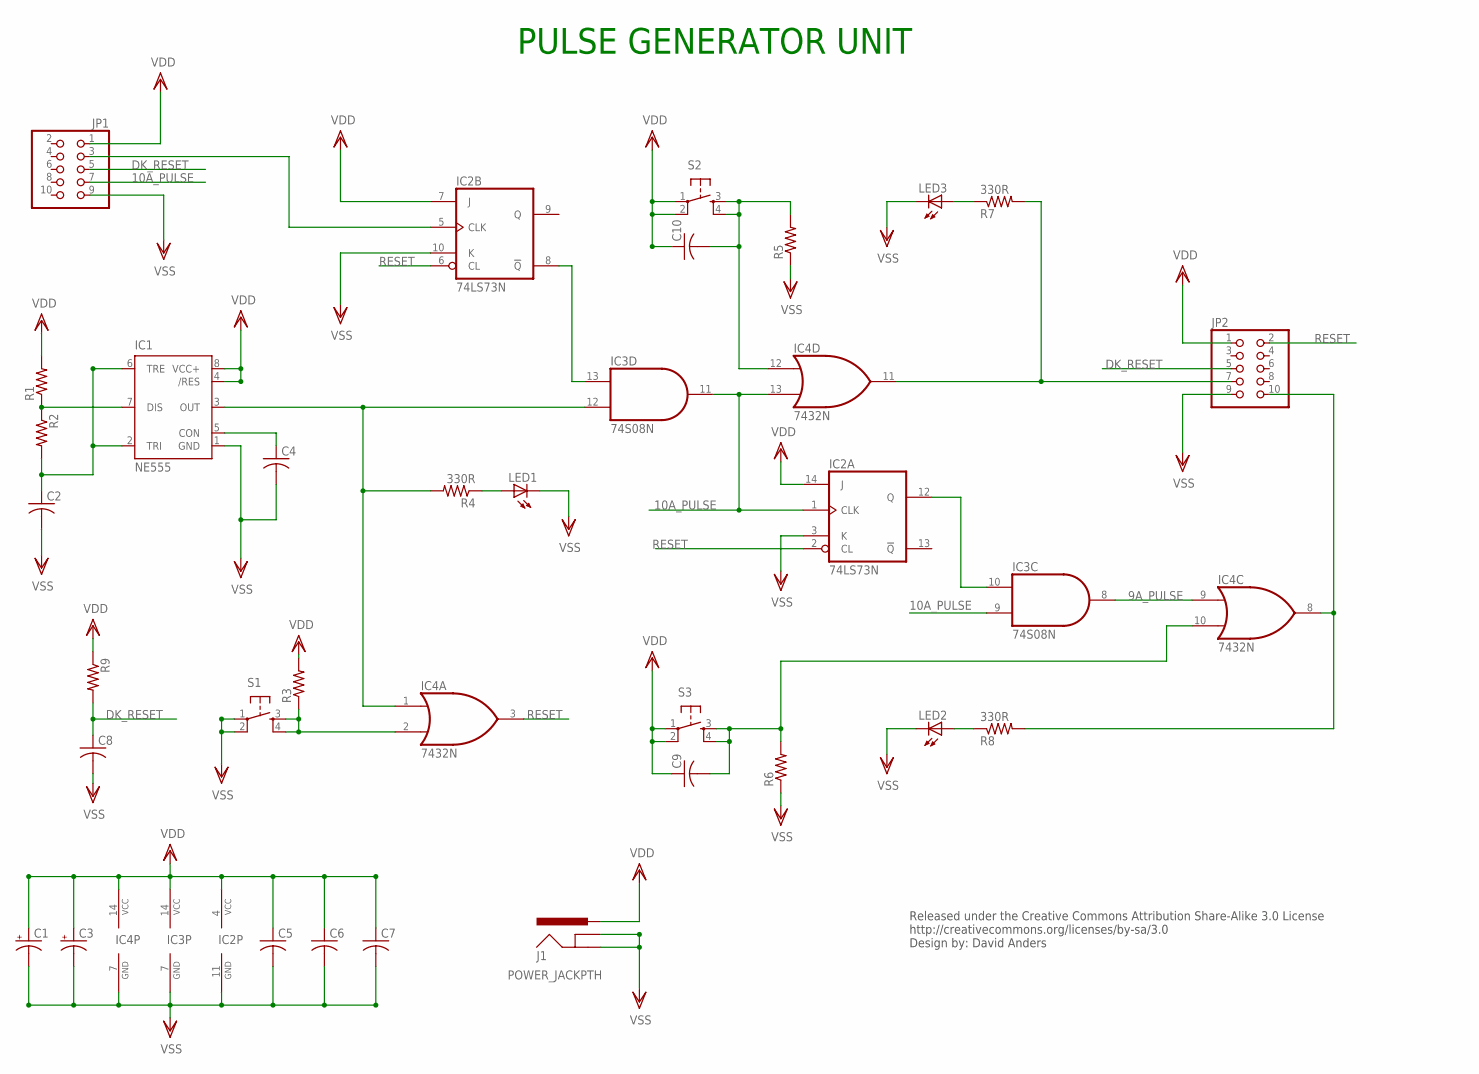
[picture p339: schematic witch-pulse1.sch]

Parts:
C1, C3: CPOL-USE2.5-5; E2,5-5
C2, C8: C-US025-040X050; C025-040X050
C4, C5, C6, C7, C9, C10: C-US025-025X050; C025-025X050
IC1: NE555; DIL-08
IC2: 74LS73N; DIL14
IC3: 74S08N; DIL14
IC4: 7432N; DIL14
J1: POWER_JACKPTH; POWER_JACK_PTH
JP1, JP2: PINHD-2X5; 2X05
LED1, LED2, LED3: LED5MM
R1, R2, R3, R5, R6, R9: R-US_0204/5; 0204/5
R4, R7, R8: 330R; 0204/5
S1, S2, S3: TAC_SWITCHPTH; TACTILE-PTH

Connections:
9A_PULSE: IC3.8 (O), IC4.9 (I0)
10A_PULSE: IC2.1 (CLK), IC3.9 (I0), IC3.11 (O), IC4.13 (I1), JP1.7
DK_RESET: C8.1, JP1.5, JP2.5, R9.2
unnamed: IC4.2 (I1), R3.1, S1.3, S1.4
unnamed: IC1.3 (OUT), IC3.12 (I0), IC4.1 (I0), R4.2
unnamed: IC4.8 (O), JP2.10, R8.2
unnamed: IC2.8 (!Q), IC3.13 (I1)
unnamed: C10.2, IC4.12 (I0), R5.2, S2.3, S2.4
unnamed: IC2.12 (Q), IC3.10 (I1)
unnamed: C9.2, IC4.10 (I1), R6.2, S3.3, S3.4
unnamed: IC1.7 (DIS), R1.1, R2.1
unnamed: IC2.5 (CLK), JP1.3
unnamed: C2.1, IC1.2 (TRI), IC1.6 (TRE), R2.2
unnamed: C4.1, IC1.5 (CON)
unnamed: LED1.A, R4.1
unnamed: LED3.A, R7.1
unnamed: LED2.A, R8.1
unnamed: IC4.11 (O), JP2.7, R7.2
RESET: IC2.2 (CL), IC2.6 (CL), IC4.3 (O), JP2.2
VDD: C1.+, C3.+, C5.1, C6.1, C7.1, C9.1, IC1.4 (/RES), IC1.8 (VCC+), IC2.4 (VCC), IC2.7 (J), IC2.14 (J), IC3.14 (VCC), IC4.14 (VCC), J1.PWR, JP1.1, JP2.1, R1.2, R3.2, R9.1, S2.1, S2.2, S3.1, S3.2
VDD1: C10.1
VSS: C1.-, C2.2, C3.-, C4.2, C5.2, C6.2, C7.2, C8.2, IC1.1 (GND), IC2.3 (K), IC2.10 (K), IC2.11 (GND), IC3.7 (GND), IC4.7 (GND), J1.GND, J1.GNDBREAK, JP1.9, JP2.9, LED1.K (C), LED2.K (C), LED3.K (C), R5.1, R6.1, S1.1, S1.2

Notes on the sheet:
Released under the Creative Commons Attribution Share-Alike 3.0 License http://creativecommons.org/licenses/by-sa/3.0 Design by: David Anders
PULSE GENERATOR UNIT
