prpplague/witch_dev/block-designs/witch-phase1/pulse/witch-pulse1.brd

## EAGLE design block-designs/witch-phase1/pulse/witch-pulse1.brd (continued)

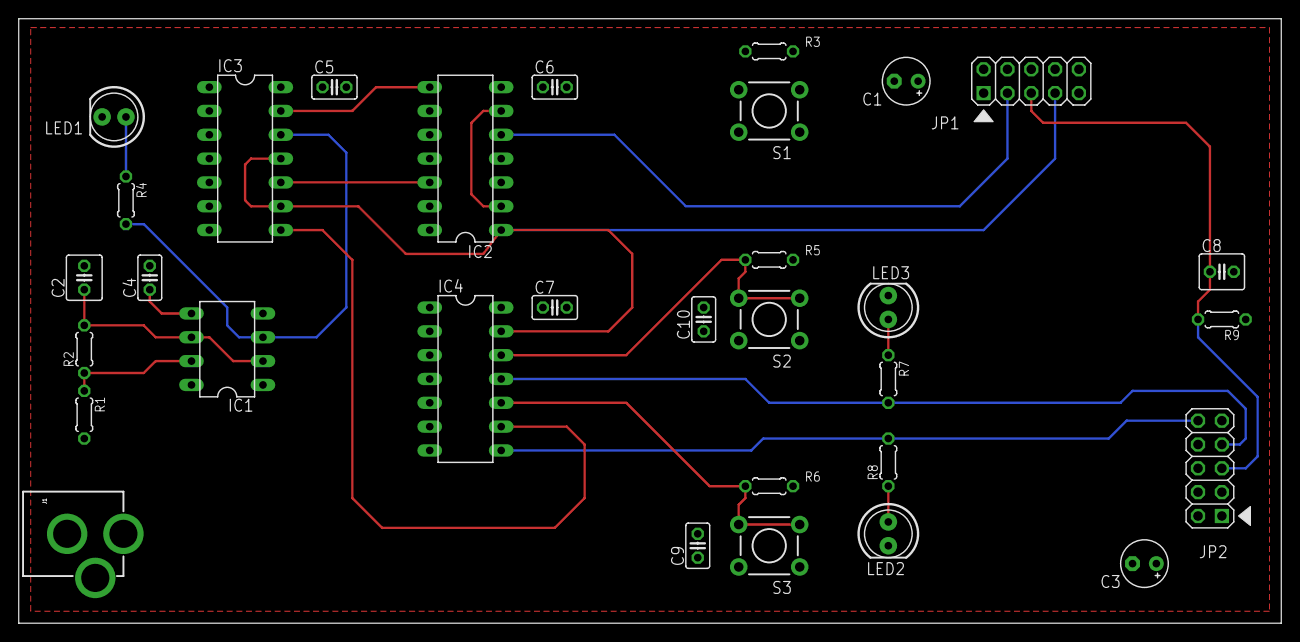
[picture p340: board witch-pulse1.brd from above]

Board: 2 copper layers, 134.6 x 64.4 mm, 32 parts (0 on the bottom side), 21 nets.
