prpplague/witch_dev/block-designs/witch-phase1/transfer/witch-transfer1.brd

## EAGLE design block-designs/witch-phase1/transfer/witch-transfer1.brd (2014-10-02)

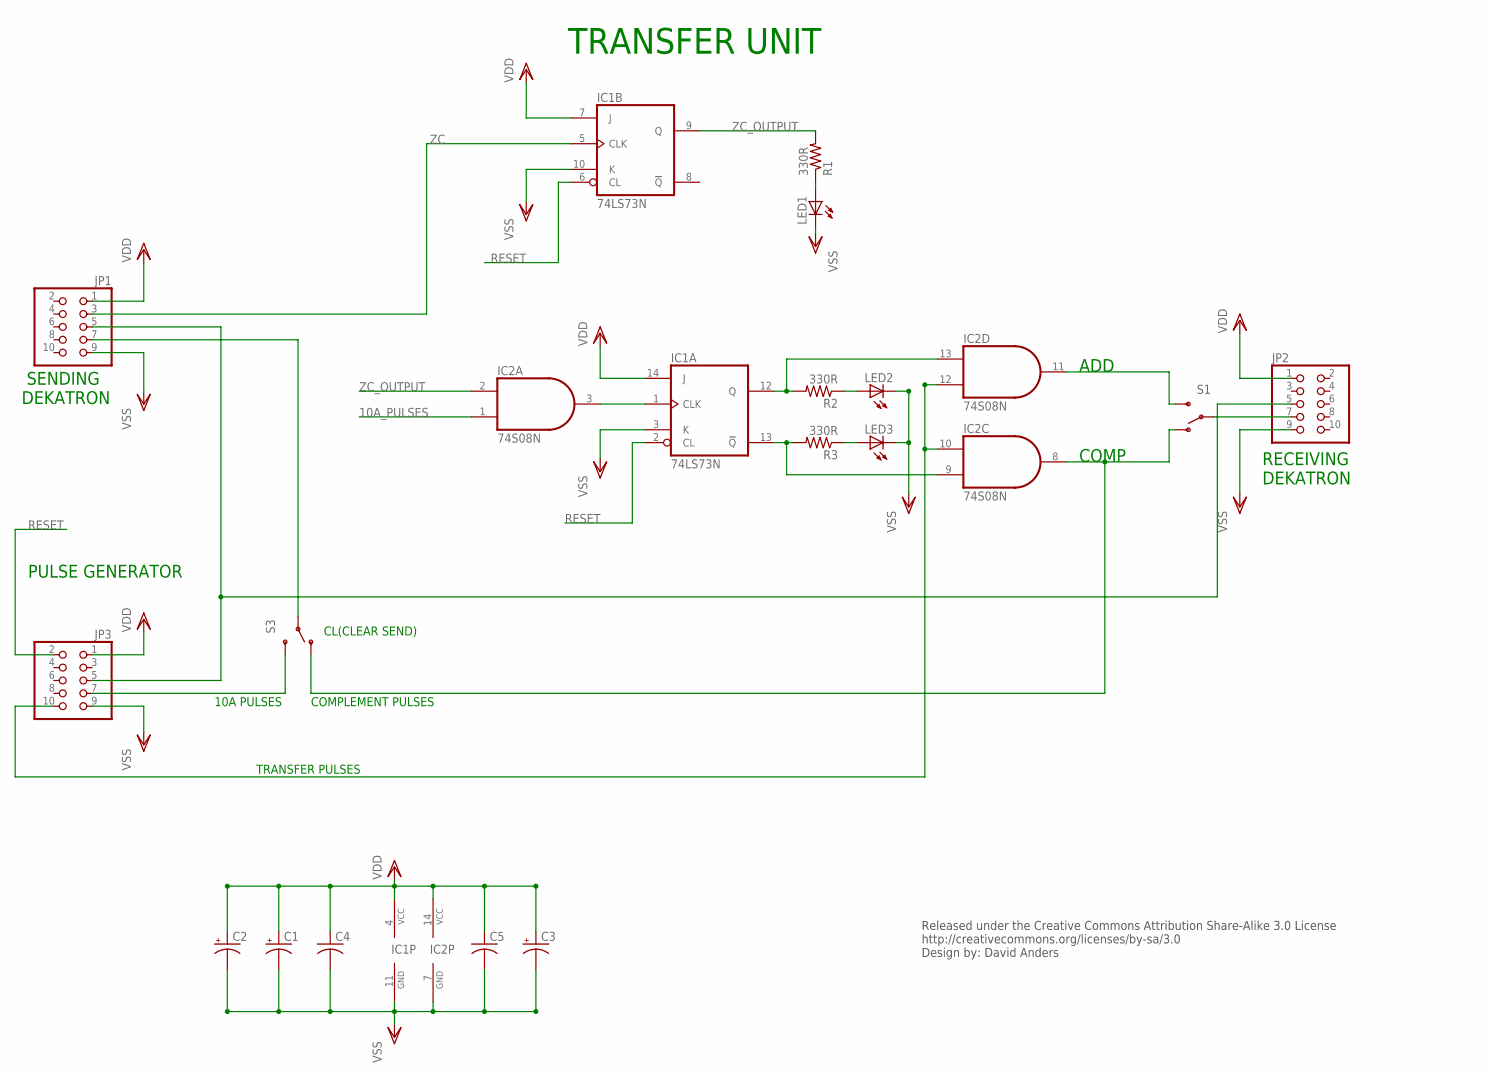
[picture p341: schematic witch-transfer1.sch]

Parts:
C1, C2, C3: CPOL-USE2-5; E2-5
C4, C5: C-US025-025X050; C025-025X050
IC1: 74LS73N; DIL14
IC2: 74S08N; DIL14
JP1, JP2, JP3: PINHD-2X5; 2X05
LED1, LED2, LED3: LED5MM
R1, R2, R3: 330R; 0204/5
S1, S3: SWITCH-SPDTPTH; SWITCH-SPDT

Connections:
10A_PULSES: IC2.1 (I0), JP3.7, S3.3 (S)
unnamed: JP2.7, S1.2
unnamed: IC2.10 (I1), IC2.12 (I0), JP3.10
unnamed: IC1.13 (!Q), IC2.9 (I0), R3.2
unnamed: IC1.12 (Q), IC2.13 (I1), R2.2
unnamed: IC2.11 (O), S1.3 (S)
unnamed: LED2.A, R2.1
unnamed: LED3.A, R3.1
unnamed: LED1.A, R1.1
unnamed: IC1.1 (CLK), IC2.3 (O)
unnamed: JP1.5, JP2.5, JP3.5
unnamed: IC2.8 (O), S1.1 (O), S3.1 (O)
RESET: IC1.2 (CL), IC1.6 (CL), JP3.2
TRANSFER_PULSE: JP1.7, S3.2
VDD: C1.+, C2.+, C3.+, C4.1, C5.1, IC1.4 (VCC), IC1.7 (J), IC1.14 (J), IC2.14 (VCC), JP1.1, JP2.1, JP3.1
VSS: C1.-, C2.-, C3.-, C4.2, C5.2, IC1.3 (K), IC1.10 (K), IC1.11 (GND), IC2.7 (GND), JP1.9, JP2.9, JP3.9, LED1.K (C), LED2.K (C), LED3.K (C)
ZC: IC1.5 (CLK), JP1.3
ZC_OUTPUT: IC1.9 (Q), IC2.2 (I1), R1.2

Notes on the sheet:
TRANSFER UNIT
ADD
COMP
Released under the Creative Commons Attribution Share-Alike 3.0 License http://creativecommons.org/licenses/by-sa/3.0 Design by: David Anders
SENDING DEKATRON
RECEIVING DEKATRON
CL(CLEAR SEND)
10A PULSES
TRANSFER PULSES
COMPLEMENT PULSES
PULSE GENERATOR

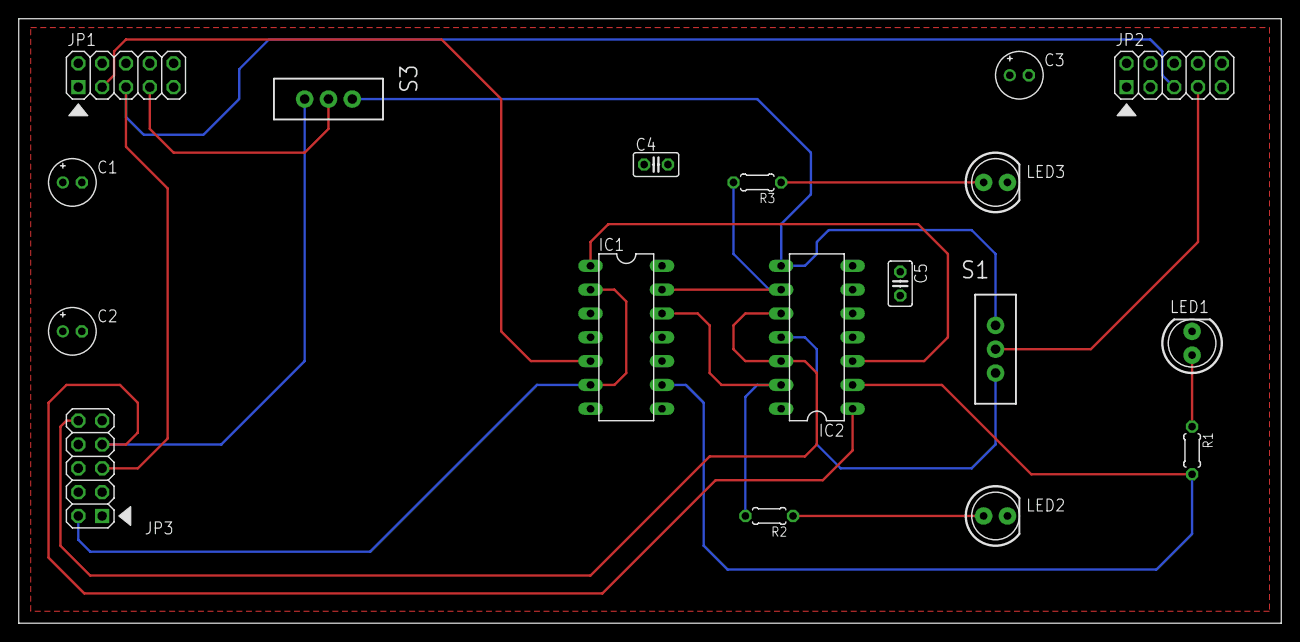
[picture p342: board witch-transfer1.brd from above]

Board: 2 copper layers, 134.6 x 64.4 mm, 18 parts (0 on the bottom side), 18 nets.
