prpplague/witch_dev/block-designs/witch-phase2/dekatron-sim/dekatron-sim-4017/dekatron-sim-4017.brd

## EAGLE design block-designs/witch-phase2/dekatron-sim/dekatron-sim-4017/dekatron-sim-4017.brd (2015-08-06)

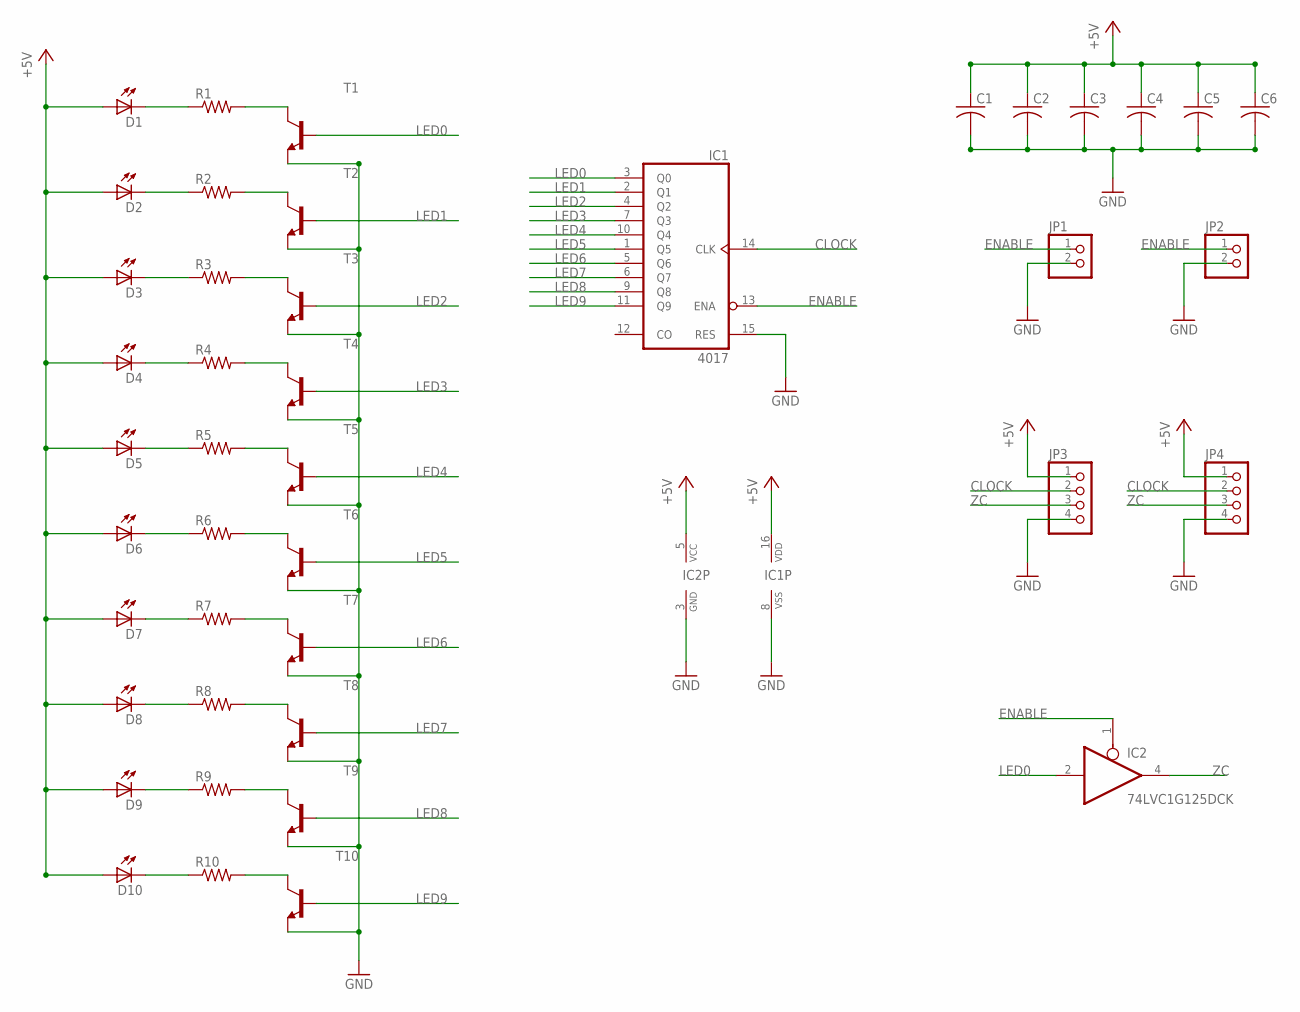
[picture p343: schematic dekatron-sim-4017.sch]

Parts:
C1, C2, C3, C4, C5, C6: C-USC0805; C0805
D1, D2, D3, D4, D5, D6, D7, D8, D9, D10: RED; CHIP-LED0603
IC1: 4017; TSSOP16
IC2: 74LVC1G125DCK; SC70-5
JP1, JP2: PINHD-1X2; 1X02
JP3, JP4: PINHD-1X4; 1X04
R1, R2, R3, R4, R5, R6, R7, R8, R9, R10: R-US_R0603; R0603
T1, T2, T3, T4, T5, T6, T7, T8, T9, T10: MMBT2222ALT1-NPN-SOT23-BEC; SOT23-BEC

Connections:
+5V: C1.1, C2.1, C3.1, C4.1, C5.1, C6.1, D1.A, D2.A, D3.A, D4.A, D5.A, D6.A, D7.A, D8.A, D9.A, D10.A, IC1.16 (VDD), IC2.5 (VCC), JP3.1, JP4.1
CLOCK: IC1.14 (CLK), JP3.2, JP4.2
ENABLE: IC1.13 (ENA), IC2.1 (OE), JP1.1, JP2.1
GND: C1.2, C2.2, C3.2, C4.2, C5.2, C6.2, IC1.8 (VSS), IC1.15 (RES), IC2.3 (GND), JP1.2, JP2.2, JP3.4, JP4.4, T1.E, T2.E, T3.E, T4.E, T5.E, T6.E, T7.E, T8.E, T9.E, T10.E
LED0: IC1.3 (Q0), IC2.2 (I), T1.B
LED1: IC1.2 (Q1), T2.B
LED2: IC1.4 (Q2), T3.B
LED3: IC1.7 (Q3), T4.B
LED4: IC1.10 (Q4), T5.B
LED5: IC1.1 (Q5), T6.B
LED6: IC1.5 (Q6), T7.B
LED7: IC1.6 (Q7), T8.B
LED8: IC1.9 (Q8), T9.B
LED9: IC1.11 (Q9), T10.B
unnamed: R10.2, T10.C
unnamed: R9.2, T9.C
unnamed: R8.2, T8.C
unnamed: D10.C, R10.1
unnamed: D9.C, R9.1
unnamed: D8.C, R8.1
unnamed: D7.C, R7.1
unnamed: R7.2, T7.C
unnamed: D6.C, R6.1
unnamed: R6.2, T6.C
unnamed: D5.C, R5.1
unnamed: R5.2, T5.C
unnamed: D4.C, R4.1
unnamed: R4.2, T4.C
unnamed: D3.C, R3.1
unnamed: R3.2, T3.C
unnamed: D2.C, R2.1
unnamed: R2.2, T2.C
unnamed: D1.C, R1.1
unnamed: R1.2, T1.C
ZC: IC2.4 (O), JP3.3, JP4.3

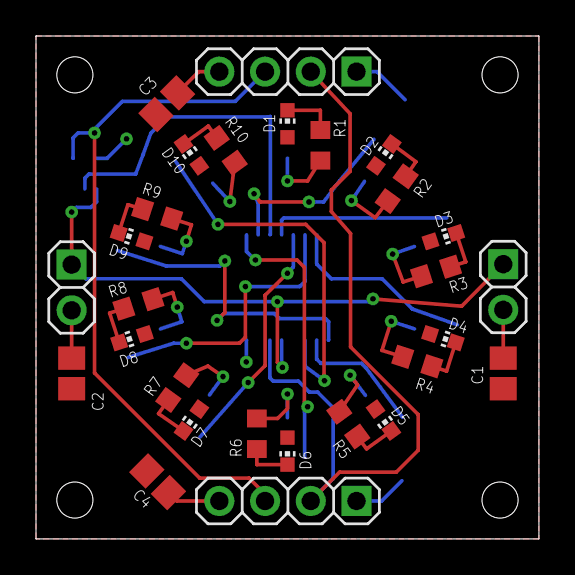
[picture p344: board dekatron-sim-4017.brd from above]

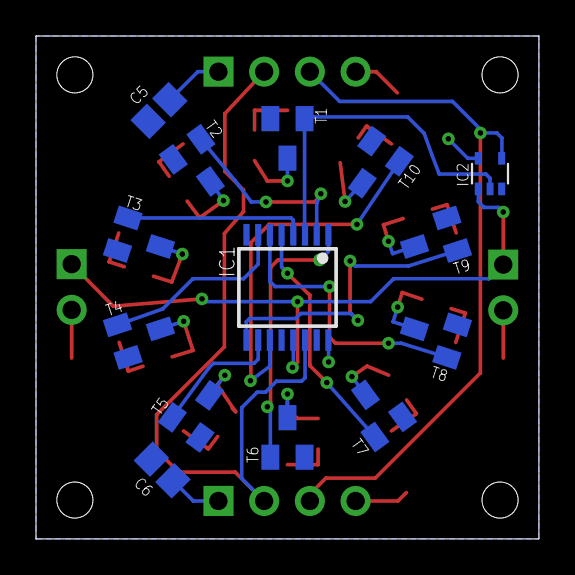
[picture p345: board dekatron-sim-4017.brd from below]

Board: 2 copper layers, 27.9 x 27.9 mm, 42 parts (14 on the bottom side), 35 nets.
