prpplague/witch_dev/block-designs/witch-phase2/dekatron-sim/dekatron-sim-4017-A2/dekatron-sim-4017-a2.brd

## EAGLE design block-designs/witch-phase2/dekatron-sim/dekatron-sim-4017-A2/dekatron-sim-4017-a2.brd (2015-08-06)

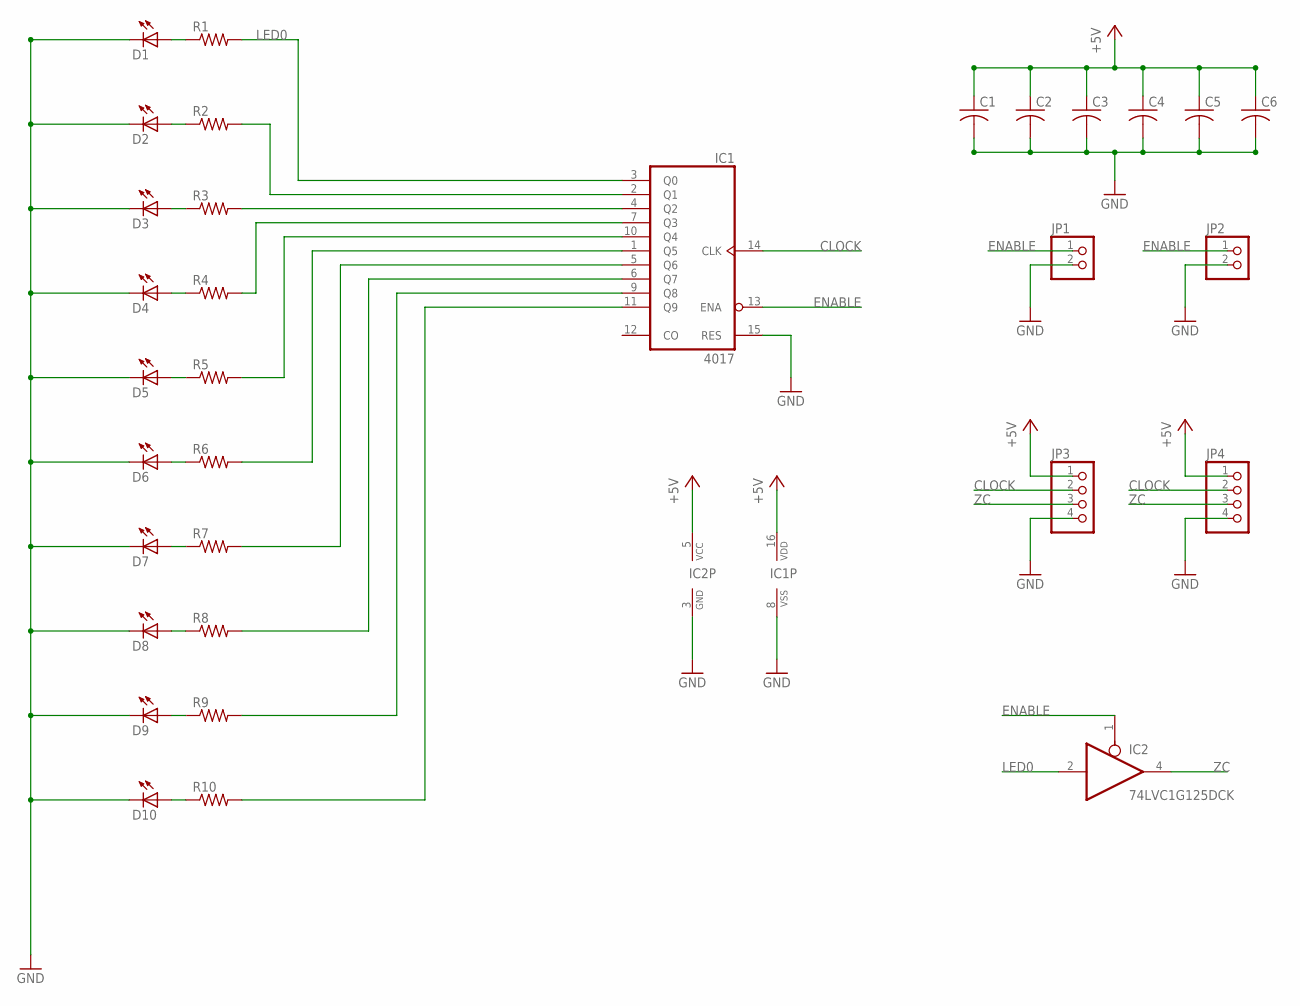
[picture p346: schematic dekatron-sim-4017-a2.sch]

Parts:
C1, C2, C3, C4, C5, C6: C-USC0805; C0805
D1, D2, D3, D4, D5, D6, D7, D8, D9, D10: RED; CHIP-LED0603
IC1: 4017; TSSOP16
IC2: 74LVC1G125DCK; SC70-5
JP1, JP2: PINHD-1X2; 1X02
JP3, JP4: PINHD-1X4; 1X04
R1, R2, R3, R4, R5, R6, R7, R8, R9, R10: R-US_R0603; R0603

Connections:
+5V: C1.1, C2.1, C3.1, C4.1, C5.1, C6.1, IC1.16 (VDD), IC2.5 (VCC), JP3.1, JP4.1
CLOCK: IC1.14 (CLK), JP3.2, JP4.2
ENABLE: IC1.13 (ENA), IC2.1 (OE), JP1.1, JP2.1
GND: C1.2, C2.2, C3.2, C4.2, C5.2, C6.2, D1.C, D2.C, D3.C, D4.C, D5.C, D6.C, D7.C, D8.C, D9.C, D10.C, IC1.8 (VSS), IC1.15 (RES), IC2.3 (GND), JP1.2, JP2.2, JP3.4, JP4.4
LED0: IC1.3 (Q0), IC2.2 (I), R1.2
LED1: IC1.2 (Q1), R2.2
LED3: IC1.7 (Q3), R4.2
LED4: IC1.10 (Q4), R5.2
LED5: IC1.1 (Q5), R6.2
LED6: IC1.5 (Q6), R7.2
LED7: IC1.6 (Q7), R8.2
LED8: IC1.9 (Q8), R9.2
LED9: IC1.11 (Q9), R10.2
unnamed: IC1.4 (Q2), R3.2
unnamed: D10.A, R10.1
unnamed: D9.A, R9.1
unnamed: D8.A, R8.1
unnamed: D7.A, R7.1
unnamed: D6.A, R6.1
unnamed: D5.A, R5.1
unnamed: D4.A, R4.1
unnamed: D3.A, R3.1
unnamed: D2.A, R2.1
unnamed: D1.A, R1.1
ZC: IC2.4 (O), JP3.3, JP4.3

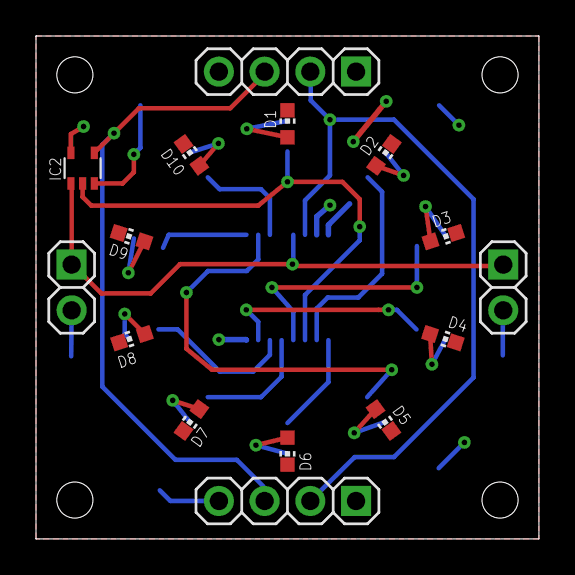
[picture p347: board dekatron-sim-4017-a2.brd from above]

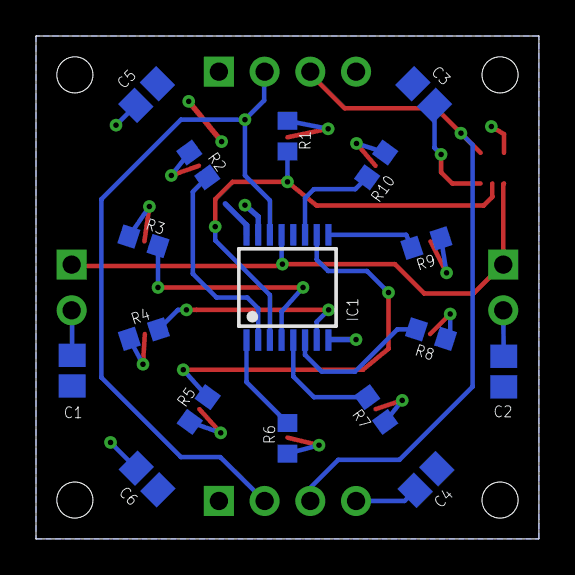
[picture p348: board dekatron-sim-4017-a2.brd from below]

Board: 2 copper layers, 27.9 x 27.9 mm, 32 parts (17 on the bottom side), 25 nets.
